xianzai588/Hanjie/simulation/cases/FE-004/README.md

# FE-004

本目录为二维热—结构代理模型交叉检查。

- 方案：baseline / compliant / 6P / S3。
- 节点来源：二维三角形 FE 网格；`bore-nodes.csv` 已送入 `position_tolerance.py`。
- 热源限制：峰值温度未达到钢/铸铁熔化温度，未模拟熔池、熔合和焊缝金属激活。
- 边界：不包含完整三维高度、温度相关塑性、相变、接触和真实材料温度曲线。
- 二维连接：翼端至壳体内壁的 1.2 mm 间隙以等效焊接桥接区表示。
- 结果性质：用于排序/趋势复核，不是实物 CMM 认证。
