xianzai588/Hanjie/DECISIONS.md

# V4.3 决策记录

更新时间：2026-10-02

1. 选题与自动 TIG + ERNiFe-CI 总体路线保留，不用未验证结果宣称已满足 Ø0.05 mm。
2. 非均匀异材公共面导热统一采用两侧串联热阻；旧 0.4R 结果仅作历史对照，当前证据指向 0.4R1。
3. 0.4R1 因空间网格门失败，保持 `solver_result_unvalidated`，不开放 THERMAL-1、正式结构耦合或熔合几何结论。
4. 3.5 mm 焊脚继续作为待验证设计目标；当前送丝 2.0 mm/s、行走 1.5 mm/s 不闭合成形体积，诊断反算值不写入 WPS。
5. 误差预算以 `project/tolerance.yaml` 为唯一权威；当前 Ø0.070 mm 最坏结果必须通过完整热—弹塑性、松夹后 CMM 与实物标定关闭。
6. 预偏置仅按逐件实测初始偏心求解，所有方法使用同一执行器约束；不可行件必须拒绝，不允许静默裁剪或回退。
7. 内腔防护必须经过装配、干涉、吹扫和非倒置退出验证；图纸表达不等于洁净度验证。
8. 定心配合以壳体内径 Ø150.00~150.02 mm、翼端外径 Ø149.94~149.98 mm 的极限尺寸直接定义，形成 0.01~0.04 mm 径向间隙；一般公差不适用于这些受控尺寸。
9. 局部截面 XSEC-M/F/VF 的焊材 P95 差未单调下降，按预登记规则停止 xfine 与新网格时间步复查；下一热实验只处理局部源密度、逐面界面通量、嵌套网格和阶梯拐角单元几何。
10. 接头尺寸继续使用 1.737/2.0/2.5/3.0/3.5 mm 条件曲线；3.5 mm 保持上界候选，不提前冻结四道。
11. 三维 J2 材料核已升级为 Mandel 一致切线与带回溯的全局 Newton，小网格基准通过；只有 Continuous 网格稀疏求解、接触、热映射和完整能量链关闭后才可通过 STRUCT-PREP。
12. Continuous 三材料预备网格不含倒置单元，但仍有 minSICN<0.1 的质量债；当前局部热场不能外推成整圈保守映射，因此不启动正式热—结构耦合。
13. THERMAL-0.6 的 NEST-M/F/VF 已严格整数嵌套；F→VF 焊材 P95 缩减比 0.406，但 P95 10.923 °C、MAE 8.066 °C 和固定点热循环仍超门，故停止 NEST-XF 与 dt/2。
14. 共同控制体源积分、源质心/二阶矩、累计界面热量及阈值翻转已通过，下一热诊断只处理边界源承载层、逐面峰值和仿射精确同材料点重构，不再归因于总能量或非嵌套比较。
15. STRUCT-0-PREP 的法向无摩擦接触、分离/撤夹、局部保守热映射和全局小模型高温无应力激活已通过；0.5 mm 局部细化及 Delaunay 重定位均未消除焊缝差单元，转向环向分段/扫掠拓扑，正式 STRUCT-0 继续冻结。
16. Plan 6 已把热源显式表示为边界面 `Q_face [W]` 并直接散射到相邻控制体 RHS；解析验证通过，且与旧 RHS 在机器精度内等价，证明旧峰值体积源密度翻倍是表示量随承载层厚度变化，不是功率单位误用。
17. 仿射精确同材料 WLS 使五个固定点 RMS 全部通过，但 F→VF NiFe P95/MAE 仍为 10.923/8.066 °C，QT 近界面峰值差 10.232 °C；不运行新 M、XF 或时间步复查，下一热路线改为成熟 FE/FVM 独立参考。
18. Continuous 采用二维共形截面环向扫掠及固定棱柱拆四面体拓扑；0.02 mm 未焊间隙在焊根共享节点闭合，最终整网格低于 minSICN 0.1 的单元为 0，几何体积误差小于 0.1%。
19. 合成温度下的完整截面周期扇区彩排已跑通稀疏全局 Newton、热致接触—分离、应力自由激活、撤夹、基准重建和孔轴拟合；STRUCT-0-PREP 升级为 `ready_pending_admitted_thermal_history`，但正式 STRUCT-0 仍由热 Gate 阻塞。
20. Plan 7 将 Elmer 40.1 s 能量跃迁定位到原生集中质量对变热容的空间混合；零传热出生能量门未通过，35–45 s 严格归因余量也略超限。成对 C 级预出生后焊缝/QT 近场仍差 68.53/108.76°C，不支持出生为主因。禁止调η或直接加密，REF-M须先通过出生与40 s审计，F/VF不运行；最多再做一次针对性诊断，仍冲突则以真实热电偶数据裁决。
21. 用户明确无实物条件，当前路线改为 Route B；第20条“实物裁决”的后续策略由本条替代。热电偶、CMM、金相和实焊均不作为当前计划依赖，不生成伪实验数据；保留物理验证边界和未来协议。
22. Plan 8完成分区焓/反力交换账、独立公共P0观测及成对预出生常物性控制。两边源积分一致，18–26 s焊缝→QT交换账约1046.46/1046.22 J，不支持巨大总量偏分配；常物性共同probe焊缝/QT近场仍差123.71/101.04°C。FE界面反力含共节点载荷/储能分摊，不能与纯梯度热流混称。诊断预算2/2已用尽，不调物理参数、不放宽门限、不运行REF-M/F/VF，剩余空间场差异作为模型形式不确定性保留。
23. 非正式STRUCT-UNCERTAINTY复用已有J2材料点、三候选3D座体和A/B基准孔轴拟合；两套QT局部热历史、3组物性、6组约束分布、2档面积基础刚度和C/M网格共432例。不是三材料整件瞬态热塑性：局部循环铺展、约束和理想壳体支承均为未验证假设。无可分辨稳健赢家，保留三候选；不得把0.00001–0.010 mm量级的敏感性当作最终焊接位置度，更不能据此认证Ø0.05。正式THERMAL-1/STRUCT-0和solver_verified升级规则不变。

19. 新增 THERMAL-REF-PLAN8 dt=0.05 s 时间步复核；Elmer 动态能量残差 0.84152 J，未改善原 dt=0.1 s 缺陷，排除时间离散为主因。热准入继续冻结，后续只处理出生焓/激活质量账的一致性。

24. R3 修复批次（2026-10-02）：评审导航、提交说明、核对清单、报名口径与冻结记录中“说明书 §9.2/§2.4”悬空引用全部改为真实章节（§0/§2.1/§7）；说明书 §0 恢复官方五评价维度→小节映射表；lint 新增章节引用门禁（§ 引用必须存在、章节标题必须渲染进 PDF），导航与说明书结构由机器对账。
25. FE 披露与载荷口径：§4.2 补胀套最大接触反力跨网格 614.2/2008.3 N（约 3.3×）披露，接触反力对网格敏感、只用于装夹容量核对、不进入位置度判定链；原“8p-fine”（3.0 mm，节点数少于主网格）更名“复核网格”（目录 8p-review、报告表头、图注、08 号附件名同步），不再使用粗/细误导命名；疲劳两组设计工况补一阶推导快照（08e load_derivation，移植 origin/main LOAD-ESTIMATE-4：Fi≈1579 N、Fg≈1885 N、M≈129.4 kN·mm），并披露假定谱倾覆矩为一阶推导的 0.19～0.58 倍——Miner 损伤仅为同谱相对排序，不是绝对寿命，载荷上移时损伤按应力范围三次方放大。
26. 封版与治理：新增 scripts/write_release_hashes.py 并生成 deliverables/COMPETITION-R3-SHA256.txt（ZIP＋27 个包内条目，verify_release_hashes.py 通配扩为 COMPETITION-R*，含回归测试）；origin/main 的 15 个分叉提交不做全量 merge——其提交门禁补强已在 R3 lint 等价实现，r1 文献基准文件整篇摘入 docs/sources/；图纸补 GB/T 324 角焊缝符号（z3.5，8×18(41)，段间净距≈41 按 Ø149.96 周长八等分）、GB/T 1182 位置度公差框（Ø0.05|A|B）与四栏标题栏（比例/材料/签审留空＝未完成制造签审）；报告 §7 与 17 号附件补 GB/T 1348-2019、GB/T 9441-2021。
