xianzai588/Hanjie/docs/P1A-0.5-complete.md

# P1A-0.5 完成报告 + Phase 1 启动状态（历史快照）

**日期**：2026-09-03  
**状态**：P1A-0.5 完成 ✅；本文记录 2026-09-03 的冻结快照。当前接口审查结论见 `simulation/structural-v4/P1A-1.1-interface-correction.md`。

---

## P1A-0.5 完成项

### 1. FAIR-A 定义修正 ✅

**修正前（错误）**：
> 固定总连接宽度 108 mm → 相同材料用量

**修正后（正确）**：
> **固定总外缘有效连接宽度 108 mm**
> 
> 回答：在相同总外缘连接尺度下，4/6/8 的拓扑分布差异如何影响结构性能。
> 
> 实际体积 V 和质量 m 将作为结果输出，不假设相等。

### 2. FAIR-C 登记 ✅

**定义**：等体积/等质量拓扑比较

**实施条件**：仅当 FAIR-A/B 排名冲突或质量差异显著时追加

**当前决策**：暂不建立（避免 7 个模型膨胀成 10+）

### 3. 统一参数化几何规则冻结 ✅

**核心文档**：`P1A-0.5-geometry-freeze.md`

**关键决策**：
- Wing width 定义：R74.98 mm 外缘处有效切向/圆弧连接宽度
- 槽根圆角：统一值（待 Phase 1 确定，优先 R2.0 mm）
- Ø40 H7：仅作为制造要求，FE 统一使用名义 Ø40.000 mm
- Continuous：传统连续环形轴承座几何基线（非简单实心圆盘）

### 4. 统一几何生成器完成 ✅

**文件**：`generate_seat_geometry.py`

**功能**：
- 生成 7 个模型的几何清单（manifest）
- 自动验证 FAIR-A/B 断言
- 输出统一格式 JSON 配置

**生成结果**：
```
[PASS] Continuous: All checks passed
[PASS] 4P-FAIR-A: All checks passed
[PASS] 6P-FAIR-A: All checks passed
[PASS] 8P-FAIR-A: All checks passed
[PASS] 4P-FAIR-B: All checks passed
[PASS] 6P-FAIR-B: All checks passed
[PASS] 8P-FAIR-B: All checks passed
```

**FAIR-A 验证**：
| 模型 | Width Each | Total Width | 断言 |
| --- | ---: | ---: | :---: |
| 4P-FAIR-A | 27.0 mm | 108.0 mm | ✅ |
| 6P-FAIR-A | 18.0 mm | 108.0 mm | ✅ |
| 8P-FAIR-A | 13.5 mm | 108.0 mm | ✅ |

**FAIR-B 验证**：
| 模型 | Width Each | Total Width | 断言 |
| --- | ---: | ---: | :---: |
| 4P-FAIR-B | 18.0 mm | 72.0 mm | ✅ |
| 6P-FAIR-B | 18.0 mm | 108.0 mm | ✅ |
| 8P-FAIR-B | 18.0 mm | 144.0 mm | ✅ |

---

## Phase 1 当前状态

### 已完成

- ✅ 7 个模型几何清单生成
- ✅ FAIR-A/B 断言验证通过
- ✅ 统一参数表冻结
- ✅ 生成规则可重复、可审查

### 待完成（Phase 1 核心任务）

**P1A Phase 1 的真正目标不是"画出来"，而是把参数化几何规则写死。**

#### 1. 确定槽根圆角统一值

**任务**：
- 检查 R2.0 mm 是否对所有拓扑（4P/6P/8P）均几何可行
- 若不可行，选择统一最大公共值（如 R1.5 mm）
- 记录最终选择理由

**约束**：
- 不与 Ø82 核心区穿透
- 不与 4 mm 槽几何冲突
- 不产生零厚度/极窄区域

**禁止**：为了降低某个方案应力而单独调整圆角

#### 2. 明确 Wing Width 几何定义

**必须回答**：
> Wing width = R74.98 mm 外缘处的哪个几何量？
> - 弦长？
> - 切向宽度？
> - 圆弧长度？
> - 恒定宽度？

**要求**：所有 FAIR-A/B 采用完全相同定义

#### 3. 建立 3D 实体几何

**使用统一生成规则**：
```
中心刚性区 Ø82
    ↓
按 N 等分中心角
    ↓
每个翼拥有参数化中心角
    ↓
从核心区向外缘延伸
    ↓
两翼之间切除径向槽
    ↓
槽根统一圆角 R_f
    ↓
外缘到 R74.98
```

**禁止**：人工独立绘制 7 份

#### 4. 自动几何检查

**必须通过**：
- Solid 有效（`is_valid = True`）
- Boolean 成功
- 无自交
- 无零/负体积
- 无重叠
- 无零厚度区域
- 坐标系一致

#### 5. 计算实际几何属性

**必须输出**：
- Planform area (mm²)
- Solid volume (mm³)
- Calculated mass (kg)
- Nominal total weld length (mm)

**用途**：后续评价比刚度 K/m

#### 6. 更新 Geometry Manifest

**将 null 字段填充为实际值**：
```json
"geometry": {
  "planform_area_mm2": 12345.67,
  "solid_volume_mm3": 123456.78,
  "calculated_mass_kg": 0.889
}
```

---

## Phase 1 验收标准（10 项）

当前完成度：4/10 (40%)

- [x] 1. 统一参数表冻结
- [x] 2. 统一生成器建立
- [x] 3. FAIR-A 断言通过
- [x] 4. FAIR-B 断言通过
- [ ] 5. 槽根圆角统一确定
- [ ] 6. Wing width 定义明确
- [ ] 7. 7 个三维实体生成
- [ ] 8. 自动几何检查通过
- [ ] 9. 实际几何属性计算
- [ ] 10. Manifest 完整更新

---

## 关键认知（重申）

### 这一步非常重要

> Phase 1 最重要的事情其实不是"画出来"，而是把**参数化几何规则写死**。

### 为什么需要统一生成器

> 评委问："4点和8点是不是人为画得不一样？"
> 
> 回答："除拓扑参数 N 和公平族定义外，几何由同一生成器产生。"
> 
> **这个证据很值钱。**

### Phase 1 的真正审查目标

> 我会先审的不是"模型漂不漂亮"，而是：
> 
> **4/6/8 的几何变化是否只有我们声称的变量在变化。**
> 
> 只要这件事守住，后面的静刚度排名才有资格称为**公平比较**。

---

## 下一步行动

### 立即任务

1. **确定槽根圆角统一值**
   - 几何可行性分析
   - 记录选择理由

2. **明确 Wing Width 定义**
   - 选择：弦长 / 切向宽度 / 圆弧长度
   - 文档化定义

3. **建立 3D 实体生成逻辑**
   - 实现统一生成规则
   - 避免人工修模

### 停止条件

**Phase 1 完成后停止，不要继续 Phase 2**

提交：
- 7 个模型/生成脚本
- geometry-manifest.csv/json（更新后）
- geometry-check-report.md
- 参数化生成规则说明
- 所有异常/妥协记录

**独立几何审查记录已迁移至 `simulation/structural-v4/geometry-audit.md`；本文仅保留历史快照。**

---

## Git 要求（已执行）

从本次开始禁止提交信息自动加入：
- ❌ Co-Authored-By: Claude
- ❌ Co-Authored-By: Codex
- ❌ Generated-by ...

---

**P1A-0.5 状态**：✅ 完成（历史快照）
**Phase 1 当前状态**：✅ P1A-1.1 接口修正和独立几何回读已通过
**下一步**：使用新 BREP 进入 Phase 2 网格与边界定义
