xianzai588/Hanjie/docs/P1A-phase0-complete.md

# P1A Phase 0 完成报告

**日期**：2026-09-03  
**任务**：Gate C-pre / P1A 三维结构静刚度公平筛选 - Phase 0 准备  
**状态**：✅ 完成

---

## 执行摘要

P1A Phase 0 准备工作已完成。设计输入已冻结，目录结构已建立，执行框架已就绪。

**核心目标重申**：
> 无预设结论地筛选进入后续三维焊接热—结构 FE 的结构候选。最终输出：Continuous + 最多两个离散候选。

**关键原则**：
- 如果六点结构被淘汰，接受结果并更新路线
- 这恰恰能证明"参数化协同优化"不是为了给既定方案找证据

---

## Phase 0 完成项（5/5）

| # | 任务 | 状态 | 交付物 |
| --- | --- | :---: | --- |
| 1 | G0 V4 unified 基线确认 | ✅ | commit 3987f11 → ed50e03 |
| 2 | 读取 V4 统一报告 | ✅ | technical-report-v4-unified.md |
| 3 | 读取几何参数 | ✅ | cad/parametric/geometry.json |
| 4 | P1A 设计输入冻结 | ✅ | P1A-design-inputs.md |
| 5 | 创建目录结构 | ✅ | simulation/structural-v4/ |

---

## 关键设计决策

### 1. 两套公平设计族（避免比较不公平）

**为什么需要两套**：
- 如果只做"4/6/8 全都每翼 18 mm"，八点实际上拥有更多材料
- 即使刚度最好也不能说是"点数优化"导致的

**FAIR-A：固定总连接宽度 108 mm**
- 回答："拓扑本身哪个好？"
- 4P: 27 mm/段，6P: 18 mm/段，8P: 13.5 mm/段

**FAIR-B：固定每段 18 mm**
- 回答："实际工程方案哪个好？"
- 4P: 72 mm 总长，6P: 108 mm，8P: 144 mm

### 2. 径向方向扫描（避免各向异性误判）

**扫描 7 个方向**：θ = 0°, 15°, 30°, 45°, 60°, 75°, 90°

**输出指标**：
- $C_{r,\max} = \max_\theta \frac{\delta_r(\theta)}{F}$（最差方向柔度）
- $A_r = \frac{C_{r,\max}}{C_{r,\min}}$（各向异性指标）

**原因**：4、6、8 点结构具有方向各向异性，只算 X/Y 很可能刚好踩在某个翼上

### 3. 双边界敏感性（避免边界假设掩盖问题）

**BC-1**：实际安装区域约束（主结果）  
**BC-2**：较刚边界（敏感性上界）

**若边界改变导致方案排序变化**：如实报告"结构优劣对安装刚度敏感"

### 4. 三级网格收敛验证（避免数值不可信）

**收敛判据**：
- 位移/柔度：Medium→Fine < 3%
- 热点应力：Medium→Fine < 10%

**若未收敛**：不得发布结构排名

### 5. 槽根圆角建模（避免数学奇异）

**禁止**：用数学尖角最大节点应力做疲劳判断  
**必须**：使用实际圆角几何，报告区域/路径应力

---

## 目录结构

```
simulation/structural-v4/
├── P1A-design-inputs.md           # ✅ 设计输入冻结
├── P1A-status.md                  # ✅ 执行状态追踪
├── README.md                      # ✅ 导航文档
├── configs/                       # ⏳ 模型配置（7 个 JSON）
├── models/                        # ⏳ 几何模型（7 个目录）
│   ├── continuous/
│   ├── 4p-fair-a/
│   ├── 4p-fair-b/
│   ├── 6p-fair-a/
│   ├── 6p-fair-b/
│   ├── 8p-fair-a/
│   └── 8p-fair-b/
├── meshes/                        # ⏳ 网格（coarse/medium/fine）
├── raw/                           # ⏳ 原始求解器输出
├── processed/                     # ⏳ 处理后结果
│   ├── results.csv
│   ├── convergence.csv
│   └── screening-summary.json
├── figures/                       # ⏳ 图表
│   ├── polar-radial-compliance.svg
│   └── pareto-stiffness-stress-mass.svg
└── stiffness-screening-v4.md      # ⏳ 筛选技术报告
```

---

## Gate C-pre 通过条件（10 项）

| # | 条件 | 状态 |
| --- | --- | :---: |
| 1 | 四种结构统一条件 3D 静力比较 | ⏳ |
| 2 | FAIR-A/B 明确分离 | ⏳ |
| 3 | 径向方向扫描完成 | ⏳ |
| 4 | 网格收敛通过 | ⏳ |
| 5 | 边界敏感性完成 | ⏳ |
| 6 | 输出机器可读结果 | ⏳ |
| 7 | 输出技术报告 | ⏳ |
| 8 | 生成极坐标图 | ⏳ |
| 9 | 生成 Pareto 图 | ⏳ |
| 10 | 无预设地选出候选 | ⏳ |

---

## 禁止项（重申）

本轮**严格禁止**：
- ❌ 预设"六点最优"结论
- ❌ 为了理想结果修改判据
- ❌ 做温度门控（那是 Gate D）
- ❌ 做预偏置补偿（那是 Gate E）
- ❌ 做三维焊接热—结构 FE（那是 Gate B/C）
- ❌ 只给漂亮云图不提供收敛表

---

## 最终输出（Phase 6 交付）

### 1. 结构筛选主表

| 方案 | 公平口径 | $C_{r,\max}$ | $A_r$ | $C_z$ | $C_\theta$ | $\sigma_{\text{slot}}/F$ | 质量 | Gate |
| --- | --- | ---: | ---: | ---: | ---: | ---: | ---: | --- |
| Continuous | baseline | … | … | … | … | … | … | ? |
| 4P | A/B | … | … | … | … | … | … | ? |
| 6P | A/B | … | … | … | … | … | … | ? |
| 8P | A/B | … | … | … | … | … | … | ? |

### 2. 网格收敛表

证明数值可信。

### 3. 径向柔度极坐标图

一张图看出 4/6/8 各向异性。

### 4. 刚度/应力/质量 Pareto 图

工程决策依据："为什么最后选 X 点"。

---

## 执行路线（Phase 1-7）

| Phase | 任务 | 预计时间 | 状态 |
| --- | --- | --- | :---: |
| Phase 1 | 几何建模（7 个模型） | 3-4 天 | ⏳ |
| Phase 2 | 网格划分（21 个网格） | 2-3 天 | ⏳ |
| Phase 3 | 边界与载荷 | 1-2 天 | ⏳ |
| Phase 4 | 求解（~378 个工况） | 2-3 天 | ⏳ |
| Phase 5 | 后处理 | 2-3 天 | ⏳ |
| Phase 6 | 分析与筛选 | 2-3 天 | ⏳ |
| Phase 7 | 独立审查 | 等待 | ⏳ |

**预计 Gate C-pre 通过**：2026-09-13

---

## Phase 7 独立审查：四个关键问题

完成 Phase 6 后，P1A 将停止并提交所有结果，等待独立审查攻击以下四个问题：

| # | 问题 | 攻击角度 |
| --- | --- | --- |
| 1 | **公平性** | FAIR-A/B 是否真的公平？有没有偷偷让某方案占便宜？ |
| 2 | **边界条件** | 边界是否合理？是否为了理想结果选择性使用边界？ |
| 3 | **网格收敛** | 收敛表是真的还是假的？变化率是否被人为压低？ |
| 4 | **结构排名** | 排名是数值结果还是人为设计出来的？ |

**只有这四项经得住攻击，才值得把筛出来的结构送入昂贵的 3D 焊接热—结构模拟。**

---

## 提交记录

```
commit ed50e03
[P1A-PREP] Phase 0 完成：三维结构静刚度公平筛选准备就绪
```

---

## 下一步

**Phase 1 几何建模**（预计 3-4 天）：
- 建立 7 个三维模型
- 统一几何参数（R74.98, Ø40 H7, t5, H200, Ø160）
- 槽根圆角建模
- 几何质量检查

**当前状态**：Phase 0 完成，进度 5/37 (14%)，准备进入 Phase 1。

---

**关键认知重申**：
> 现在不要再给项目"+1 分"。**下一次真正值得重评分的节点，就是 P1 出现第一批可信三维结构证据的时候。**

---

**P1A Phase 0 状态**：✅ 完成，设计输入冻结，目录结构就绪，等待 Phase 1 开始。
