xianzai588/Hanjie/docs/G0-v4-baseline-convergence.md

# G0 V4 基线收敛完成报告

**日期**：2026-09-03  
**任务**：从"V2+V3+V4混合状态"收敛到统一 V4 基线

---

## 执行背景

### 核心问题诊断

**当前分数分离**：
| 对象 | 当前水平 | 说明 |
| --- | ---: | --- |
| 项目思路、V4 战略、创新规划 | **84-85** | README、规划文档已 V4 |
| **当前真正提交出去的 PDF/图纸一致性** | **79-82** | 技术报告仍 V2，参数不一致 |

**最大风险**：不是技术路线不够高级，而是"**仓库里已经改了，论文还是旧的**"。

### V2/V3/V4 参数不一致清单

| 参数 | V2 旧值 | V4 正确值 | 影响 |
| --- | --- | --- | --- |
| 翼端半径 | R73.8 mm | **R74.98 mm** | 装配间隙、接头几何 |
| 装配间隙 | 1.2 mm | **0.01~0.04 mm** | 配合性质 |
| 配合表述 | "H7/h6 过渡配合" | **"H7/h6 定位间隙配合"** | 技术准确性 |
| 定位夹具 | Ø39.96 mm 定位销 | **锥形心轴 1:50** | 重复性、自动找正 |
| 误差预算 | "硬伤已修复" | **"未闭合，0.035 > 0.025 mm"** | 诚实度 |
| 轨迹补偿概念 | "轨迹反变形补偿" | **"焊前装配预偏置补偿"** | 机械逻辑正确性 |
| 标准引用 | GB/T 5185（焊缝符号） | **GB/T 324（焊缝符号）+ GB/T 5185（方法代号）** | 标准使用正确性 |

---

## G0 执行的 6 项任务

### ✅ 任务 1：建立真正的 V4 报告主稿

**文件**：`deliverables/report/technical-report-v4-unified.md`

**核心改进**：

1. **标题修正**：
   - ❌ V2："QT450-10/Q235B 主轴承座异种材料焊接数字工程技术说明书"
   - ✅ V4："面向 Ø0.05 mm 位置度的 QT450-10/Q235B 主轴承座异种焊接热—结构协同优化与数字质量控制"

2. **摘要诚实化**：
   ```markdown
   ### 当前验证状态
   | 项目 | 状态 | 证据等级 |
   | --- | --- | --- |
   | FE3D-BASE Baseline | 实施中 | Gate B 待验证 |
   | 误差预算闭合 | **未闭合** | 0.035 > 0.025 mm |
   ```

3. **误差预算缺口明确化**：
   > V4 明确边界：当前误差预算最坏情况为 **0.035 mm 径向（Ø0.070 mm 位置度）**，尚未满足 Ø0.05 mm 目标。后续热—结构优化与焊前预偏置补偿的直接目标，就是关闭这 **0.010 mm 径向预算缺口**。

4. **全文参数统一**：
   - R74.98 mm 小间隙精密定心
   - 锥形心轴 1:50
   - H7/h6 定位间隙配合（非过渡配合）

5. **未验证创新明确标记**：
   | 创新 | 状态标记 |
   | --- | --- |
   | 柔顺结构 | unresolved, hypothesis |
   | 温度门控 | untested, proposed |
   | 预偏置补偿 | untested, proposed |

6. **8 章结构**（替代原 17 节）：
   1. 命题解析与总体方案
   2. 异种材料焊接性与工艺选型
   3. 接头—夹具—尺寸链协同设计
   4. 三维热—结构协同模型
   5. 承载刚度与疲劳评估
   6. 温度门控与装配预偏置控制
   7. 自动化、检测与质量追溯
   8. 证据分级与后续路线图

---

### ✅ 任务 2：修正三个关键概念问题

#### 2.1 H7/h6 配合性质修正

**V2 错误**：
> "H7/h6 过渡配合"

**V4 正确**：
> "H7/h6 为定位间隙配合（locational clearance fit），非过渡配合。采用小间隙精密定心设计，名义径向间隙约 0.02 mm。实际装配前需测量壳体内径及圆度，通过翼端精加工/选配保证间隙落在设计范围。"

**依据**：
- H7/h6 属于定位间隙配合
- H7/k6、H7/m6 才是过渡配合

#### 2.2 预偏置补偿概念修正

**V2 错误概念**：
> "轨迹反变形补偿"——机器人把焊枪轨迹偏 0.01 mm

**机械逻辑问题**：
- 轴承座已被夹具固定，机器人偏轨迹不会直接移动轴承孔
- 真正应该做的是根据实际接头位置进行焊缝跟踪

**V4 正确概念**：
> "焊前装配预偏置—焊后变形联合补偿"

**控制链修正**：
```
视觉/CMM 测得初始偏心
        ↓
热—结构模型预测焊后收缩
        ↓
求解最佳预偏置 δ_pre
        ↓
微调心轴/定位平台        ← 作用在装配位置，不是焊枪轨迹
        ↓
重新测量确认
        ↓
机器人沿真实接头轨迹焊接
        ↓
焊后测量
```

#### 2.3 GB/T 标准引用修正

**V2 错误**：
> `FILLET WELD ... per GB/T 5185`

**问题**：
- GB/T 5185-2005 是《焊接及相关工艺方法代号》，主要用于焊接方法名称和代号
- 不是角焊缝几何或焊缝符号设计标准

**V4 正确**：
- **焊接方法代号**：GB/T 5185-2005
- **焊缝符号表示**：GB/T 324-2008《焊缝符号表示法》
- **接头/坡口**：GB/T 985.1-2008（有需要时引用）

**已修改文件**：
- `cad/parametric/generate_engineering_drawings.py`（新增 `weld_note()` 函数）

---

### ✅ 任务 3：误差预算缺口作为核心优化目标

**不再藏匿问题**，而是明确作为 V4 的核心优化约束。

**当前状态**：
```
0.005 + 0.003 + 0.008 + 0.005 + 0.012 + 0.002
= 0.035 mm 径向

目标：0.025 mm 径向
差值：0.010 mm
```

**V4 论文中的正确表达**：
> **初始最坏情况尺寸链尚不能满足 Ø0.05 mm 位置度，因此后续热—结构优化与焊前预偏置补偿的直接目标，就是关闭这 0.010 mm 径向预算缺口。**

**双口径报告计划**：
1. **最坏情况上界**（线性叠加）
2. **独立随机项 RSS/P95 统计预算**

**前提**：先区分各误差项性质：
- 可标定系统偏差
- 可补偿偏差
- 随机重复性
- 焊接随机变形
- 测量不确定度

---

### ✅ 任务 4：V2 历史归档，V4 作为新主线

**文件结构**：
```
deliverables/report/
├─ technical-report-v2.md              # ✅ 冻结历史，不再修改
├─ technical-report-v4.md              # ⏸️  V4 骨架（FE3D 占位）
├─ technical-report-v4-unified.md      # ✅ V4.1 统一版（本次交付）
└─ build_technical_report_v4.py        # 🔄 待建立
```

**V2 保留理由**：
- 降阶模型 + 二维 FE 的完整记录
- 15 组降阶筛选 + 5 组 FE 代理的对照数据
- 网格收敛未通过（29.224%）的诚实记录

**V4 主线定位**：
- 三维热—弹塑性 FE 为核心
- Gate B 验证门严格执行
- 所有未验证创新明确标记

---

### ✅ 任务 5：建立证据清单追溯

**文件**：`evidence/claims.yaml`（已存在，V4 论文已引用）

**核心主张状态**：

| 主张 ID | 主张内容 | 状态 | 置信度 | 发布状态 |
| --- | --- | --- | --- | --- |
| CLAIM-柔顺 | 六点柔顺降低位置度 | unresolved | low | hypothesis |
| CLAIM-温控 | 温度门控优于固定 S3 | untested | hypothesis | proposed |
| CLAIM-补偿 | 反变形补偿有效 | untested | hypothesis | proposed |
| CLAIM-预算 | 误差预算闭合 | not_closed | needs_optimization | optimization_target |
| CLAIM-FE3D | FE3D-BASE 可信 | in_progress | to_be_determined | in_verification |

**V4 论文发布规则**：
- `hypothesis` / `proposed` → 必须用"提出"、"设计"、"构建"
- `unresolved` / `untested` → 不能写"验证"、"证明"、"表明"
- `in_progress` → 写"实施中"、"Gate B 待验证"
- `not_closed` → 明确写"未闭合，成为优化目标"

---

### ✅ 任务 6：下一步执行清单明确

**不再做的事**（禁止项）：
- ❌ 继续写温度门控代码（在 Gate B 通过前）
- ❌ 继续加功能
- ❌ 追求更多创新点
- ❌ 修改验证协议判据（结果出来后）
- ❌ 继续总结文档和功能扩展

**立即要做的事**（优先级顺序）：

| 优先级 | 任务 | Gate | 交付物 |
| :---: | --- | --- | --- |
| **P0** | ✅ V4 基线收敛 | Gate A | 参数一致性 |
| **P1** | 🔄 连续/4/6/8 结构静刚度筛选 | Gate C-pre | 公平对比基线 |
| **P2** | 🔄 FE3D-BASE 三维热—结构 FE | Gate B | 数值可信度 |
| **P3** | ⏳ 3D FE 结构公平对比（筛选后少数方案） | Gate C | 结构选型 |
| **P4** | ⏳ 温度门控对照实验 | Gate D | 有效改善证据 |
| **P5** | ⏳ 预偏置补偿闭环验证 | Gate E | 误差预算闭合 |

---

## G0 交付物清单

| # | 交付物 | 路径 | 状态 |
| --- | --- | --- | :---: |
| 1 | V4 统一技术报告 | `deliverables/report/technical-report-v4-unified.md` | ✅ |
| 2 | 工程图生成器（标准引用修正） | `cad/parametric/generate_engineering_drawings.py` | ✅ |
| 3 | G0 基线收敛报告 | `docs/G0-v4-baseline-convergence.md` | ✅ |
| 4 | V2 历史归档 | `deliverables/report/technical-report-v2.md` | 🔒 冻结 |
| 5 | V3 误差预算 | `docs/validation/position-error-budget-v3.md` | ✅ 已有 |
| 6 | V4 关键修正说明 | `docs/v4-key-corrections.md` | ✅ 已有 |
| 7 | V4 冻结总结 | `docs/v4-freeze-summary.md` | ✅ 已有 |

---

## 关键认知转变

### Before (V2/V3 混合状态)

- "项目 85 分" = 认为提交物已经 85 分
- R73.8 mm / Ø39.96 mm 销 / 1.2 mm 间隙 = 旧参数仍在论文
- "误差预算硬伤已修复" = 回避 0.035 > 0.025 的事实
- "轨迹反变形补偿" = 机械逻辑错误
- "GB/T 5185 焊缝符号" = 标准使用错误
- 未验证创新写成"已验证成果"

### After (V4 统一基线)

- "项目规划 85 分，提交物 79-82 分" = 清晰区分
- **R74.98 mm / 锥形心轴 1:50 / 0.01~0.04 mm 间隙** = 全文统一
- "误差预算未闭合，0.010 mm 缺口成为核心优化目标" = 诚实面对
- "焊前装配预偏置补偿" = 机械逻辑正确
- "GB/T 324 焊缝符号 + GB/T 5185 方法代号" = 标准使用正确
- 所有未验证创新标为 `proposed / hypothesis / to-be-verified`

---

## 下一阶段 Gate 清单

| Gate | 必须满足 | 预计完成 |
| --- | --- | --- |
| ✅ Gate A | V2/V3/V4 参数一致性 | 2026-09-03 |
| 🔄 Gate B | FE3D-BASE 网格收敛（< 5%）+ 热场合理性 | 2026-09-07 |
| ⏳ Gate C | 4/6/8 结构公平对比 | 2026-09-11 |
| ⏳ Gate D | 自适应跳焊有效改善 | 2026-09-15 |
| ⏳ Gate E | 误差预算闭合验证 | 2026-09-18 |

---

## 最重要的一句话

> **下一阶段不是增加内容，而是让每一个创新点都出现"设计问题 → 数学/物理方法 → 对照基线 → 数值结果 → 反例/边界 → 工程决策"这一完整证据链。**

做到这一点，这个作品才真正进入高奖竞争状态。

---

**G0 状态**：V4 基线收敛完成，参数一致性达标，准备进入 Gate B 验证阶段。
