xianzai588/Hanjie/docs/00-project-definition.md

# 00 项目定义（WP0）

> 状态：v1.0 · 2026-09-02 执行版
> 比赛原始文件见 [competition/original-files/](../competition/)，本文与其逐条对照维护。

## 1. 比赛对象（固定题）

### 壳体

| 项目 | 参数 |
| --- | --- |
| 材料 | Q235B |
| 壁厚 | 5 mm |
| 外径 × 高 | Ø160 × 200 mm |

### 主轴承座

| 项目 | 参数 |
| --- | --- |
| 材料 | QT450-10 球墨铸铁 |
| 形状 | 环形盘状 |
| 轴承孔 | Ø40 mm |

## 2. 硬性要求

- 焊后轴承孔轴线位置度偏差 ≤ **Ø0.05 mm**
- 不得产生可能进入压缩机内部的焊渣、飞溅物
- 方案须覆盖五个维度：
  1. 工艺选择与优化
  2. 材料选配与连接
  3. 焊接结构设计
  4. 质量检测与评价
  5. 自动化焊接方案

## 3. 项目主线

**基于六点柔顺连接结构的 QT450-10/Q235B 主轴承座低变形自动 TIG 异种焊接及数字化质量控制方案**。

主候选：自动 TIG + 镍铁基填充材料；对比路线：CMT/低飞溅 GMAW、激光填丝。主候选仍需在设备与小试可用时完成工艺评定。

三个核心问题：

1. **焊得住** —— 异种材料焊接性：白口、脆硬组织、裂纹、焊材、热输入、预热/后热、接头可靠性
2. **焊不歪** —— P ≤ Ø0.05 mm：焊缝数量/位置/顺序、热输入、夹具、定位、热管理、反变形
3. **稳定焊** —— 视觉定位、路径生成、自动焊接、参数采集、异常检测、批量质量追溯

## 4. 工作包划分

| WP | 模块 | 最终回答 | 负责人 |
| --- | --- | --- | --- |
| WP0 | 项目定义与资料管理 | 我们到底要解决什么 | 待定 |
| WP1 | 材料与焊接性 | 为什么难焊 | 待定 |
| WP2 | 焊接工艺选型 | 到底用什么方法焊 | 待定 |
| WP3 | 接头结构与夹具 | 接头怎么设计 | 待定 |
| WP4 | 热-结构仿真 | 为什么这样设计 | 待定 |
| WP5 | 物理验证（可选） | 实际能不能焊好 | 待定 |
| WP6 | 自动化与智能监测 | 怎么稳定重复 | 待定 |
| WP7 | 检测评价与数值后处理 | 怎么证明真的好 | 待定 |
| WP8 | 作品集成与答辩 | 怎么形成完整参赛作品 | 待定 |

## 5. 证据边界

- 官方仅给出题面材料、壳体尺寸、轴承孔直径、位置度限值和洁净度要求；未给出的轴承座厚度、外廓细节、焊缝尺寸、装配间隙和基准细节统一见 [05-design-assumptions.md](05-design-assumptions.md)。
- 数值模型输出的 `P_sim` 是按内孔分层拟合轴线构造的比较指标，不是 CMM 认证结果。
- 没有设备时，实验、金相、硬度、NDT、CMM 和真实过程采集均标记为“可选/待实施”，不能用生成数据替代实测。

## 6. 待确认事项

- [ ] 固定题原文逐条核对（与 competition/original-files 对照，标注页码）
- [ ] 校内报名与作品节点最终确认（官方报名 10-20 前，作品提交 10-25 前）
- [ ] 位置度 Ø0.05 mm 的真实测量手段确认（CMM 可用性与精度）
- [ ] 洁净度判据的量化定义（内腔异物检查规程）
- [ ] QT450-10 与 Q235B 供应商质保书归档
- [ ] 自动 TIG 设备、ERNiFe-CI 丝/棒和保护气的可获得性确认
