xianzai588/Hanjie/deliverables/submission/10-复现与版本冻结记录.md

# COMPETITION-R3 复现与版本冻结记录

## 发布状态

- 版本：COMPETITION-R3；题型：固定题·焊接赛道。
- 冻结方案：8P-FAIR_B，八段两道脉冲 TIG；根道与盖面各一遍，总焊长144 mm，名义净线能量300 J/mm，净热86.40 kJ，弧燃174.5 s。
- 材料路线：QT450-10座体/Q235B壳体；Ni99预制隔离层，NiFe-55最终填充；不预热、层间≤100 ℃、400～500 ℃半热态轻击。
- 交付范围：纯数字设计作品。整件热-结构结果用于设计验证；实物资格试验仍按说明书 §7 设计放行顺序执行。
- 说明书与图集页数以构建后的 `manifest.json` 实际计数为准。

## 复现入口

在项目根目录执行：

```powershell
python deliverables/build_submission.py
```

入口会重建设计计算、Schaeffler映射、工程核算、WPS、图纸、说明书、manifest 和压缩包，并运行 `scripts/competition_submission_lint.py`。

## 权威输入

- `project/competition-design.yaml`：几何、8P焊序、控形、洁净与验证边界。
- `project/process-r3.yaml`：当前脉冲TIG名义参数。
- `studies/COMPETITION-DESIGN/results/assessment.json`：候选比较与守恒计算。
- `simulation/competition-r3/results/8p-coarse/`：整件主网格热-结构结果及历史。
- `studies/SCHAEFFLER-MAP/results/schaeffler-mapping.json`：相图当量及适用域声明。
- `deliverables/report/technical-report-v4-unified.md`：提交说明书源稿。

## 证据边界

位置度 0.001742 mm 为独立 A/B 基准拟合后的数值结果；主/复核独立网格绝对差 0.000784 mm，响应相对差45%，因此报告保留相对差并以设计限值的绝对裕量作为工程门。该结果是数值设计验证，不是实物放行；NiFe/QT界面、疲劳、洁净度和测量系统能力须通过首件试制确认。
