xianzai588/Hanjie/deliverables/submission/17-参数来源与证据等级.md

# COMPETITION-R3 参数来源与证据等级

| 参数/结论 | 当前值 | 来源等级 | 对核心结论影响 | 口径 |
| --- | ---: | :---: | :---: | :--- |
| 脉冲峰值/基值电流 | 100/50 A | B | 中 | 工艺设计窗口；试制阶段由WPS/PQR固化 |
| 电弧电压 | 12 V | B | 中 | 工艺设计窗口 |
| 焊速 | 1.65 mm/s（±2%） | B | 高 | 两道脉冲TIG冻结口径 |
| 送丝/焊丝直径 | 3.50±0.05 mm/s；Ø1.60±0.01 mm | B/C | 高 | 守恒边界输入 |
| 起焊温度/层间温度 | 20 ℃起焊（不预热）/≤100 ℃ | B/C | 高 | 位置度与铸铁冷焊窗口 |
| 锤击窗口 | 400～500 ℃；0.2～0.4 MPa | B | 高 | 仅焊道中心，避开QT/HAZ/焊趾 |
| 电弧效率/沉积效率 | 0.55；0.90～0.98 | C | 高 | 能量与熔敷守恒假设；首件截面复核 |
| 整件数值位置度 | 0.001742 mm（直径） | A | 高 | 独立A/B基准拟合；非实测放行值 |
| 网格绝对差 | 0.000784 mm | A | 高 | 与Ø0.05 mm设计限值比较的工程门 |
| 参考许用应力 | 60 MPa | C | 高 | 条件承载筛查值，不是NiFe/QT实测许用 |
| NiFe-55成分与熔敷性能 | 以供方质保书、AWS A5.15分类和PQR为准 | B | 高 | 报告仅作设计输入，不替代批次复核 |
| 母材标称成分 | Q235B按GB/T 700；QT450-10按GB/T 1348-2019 | B | 高 | 以实际批次质保书为准 |
| 金相组织检验 | GB/T 9441-2021 | B | 中 | 宏观截面/金相与硬度评定的标准框架；首件试制执行 |

等级定义：A=当前项目内可复核的独立计算或原始记录；B=公开标准/资料或工程工艺窗口；C=工程假设或设计分配。设计结果与实物工程放行严格分开。
