xianzai588/Hanjie/deliverables/process/joint-process-card.md

# 主轴承座—壳体连接 pWPS 工艺规程卡

赛道：中铁山桥杯焊接固定题。规程号HJ-W-01，修订3。适用Q235B壳体5 mm、QT450-10座体12 mm、Ø40孔、8×18 mm间断角焊缝。设计规程在A类工艺试验合格后转为生产WPS，内容按ISO 15609-1组织。

| 项目 | 规定 |
| --- | --- |
| 接头与位置 | 内周上表面角焊缝，八段等分45°；壳体轴线竖直，工件回转，焊枪保持平/横角焊位置；焊脚≥3.50，最大几何包络4.30 |
| QT预制过渡层 | 在八处18×6 mm连接面开深1.50±0.10、端部R1.5的浅槽，Ni99 TIG填满后加工至名义接头表面；最终组焊前纯镍层≥1.20 mm；组焊熔深≤0.40，剩余纯镍≥0.80；截面验证后冻结 |
| 前工序 | 镍层制作与最终Ø40孔加工分开：铸件→镍层→24 h表面裂纹检查→连接面及孔精加工→清洗干燥→组焊。隔离层不是假定“母材不再受热” |
| 表面准备 | 铸皮、油污、氧化层去除；镍层、钢侧连接面露出洁净金属；脱脂剂完全挥发，不在封闭内腔内打磨；焊前入腔物料清点 |
| 组装 | 孔40.010～40.018；座体底面z100；外缘149.94～149.98、壳体内径150.00～150.02；径向间隙0.01～0.04；胀套对独立壳体基准定心 |
| 方法/极性 | 自动脉冲GTAW（TIG），DCEN；不使用焊剂，禁止以低飞溅替代颗粒防护 |
| 焊材 | NiFe55 TIG实心棒Ø1.60±0.01；供方典型Ni55、C0.01、Si0.13、Mn0.70 wt%；按实际产品供货分类及证书订货，禁止把药皮焊条分类直接当作TIG牌号 |
| 电极/气体 | W-La20 Ø2.0，尖端角60°，平顶0.3；喷嘴Ø10，弧长2.5±0.5；99.999% Ar 10 L/min，许可8～12 |
| 脉冲 | 峰值100 A / 基值50 A；占空50%；20 Hz；平均75 A；名义12 V；须采样瞬时U(t)I(t)积分，禁止仅乘两个平均值作为在线能量 |
| 焊速/填充 | 焊速1.65 mm/s±2%；固定送丝3.50±0.05 mm/s，分辨率≤0.01；沉积效率设计0.90～0.98，由宏观截面及增重确认 |
| 成形 | 两道：根道目标焊脚2.8，盖面至名义4.0；总填充面积7.326～8.760 mm²、等效焊脚3.828～4.186；根道与盖面都需熔合，不以体积守恒替代熔合检查 |
| 线能量 | 名义毛弧能545.45 J/mm；η电弧0.55，名义净300 J/mm；净窗口250～350，η是热模型输入，不能直接由电源读数实测；全件名义净86.40 kJ |
| 焊序 | 根道1→5→3→7→2→6→4→8，盖面同序；各18 mm，段内不摆动；起停1 mm过渡，弧坑填充，不计入有效18 mm而削短焊段 |
| 温控 | 组焊不预热；起焊15～35℃；每段焊前测QT侧距焊趾10 mm及本段前道邻近测点，全部≤100℃；缺信号或超温禁起弧，等待至≤90℃再恢复 |
| 热态轻击 | 仅当表面实测400～500℃时，在熔敷焊道中部轻击；气动Ø8圆头、0.2～0.4 MPa、2000～3000次/min、搭接≥75%；不敲QT母材/熔合线/焊趾，各留0.5；压痕≤0.05，无撕裂或剥离；超窗跳过并记录，不为锤击二次加热 |
| 清理与防护 | 层间用专用刷与顶部局部抽吸清理，禁止腔内磨削；刚性盘＋分体铜环＋静态密封截留颗粒；气幕10～15、顶部抽吸22～28 L/min；水路独立检漏 |
| 装夹与卸夹 | 径向预载≤100 N；机械止挡承受热反力，额定5000 N；独立压环500 N。最后停弧≥120 s且热区<55℃，压环卸载→胀套正向回退1 mm→铜环/密封回缩0.5→朝上竖直下撤 |
| 精度检查 | 20±1℃，A为壳体下端面、B为壳体内壁两个独立测量带轴线；Ø40孔3截面各12点拟合孔轴，测得位置度直径＋同口径扩展不确定度≤0.05 |
| 尺寸精整 | 先检焊后位置度；孔径合格不精整；仅对孔径<40.020者定尺寸微珩，直径增量≤min(0.005,40.025−实测直径)，禁止用精整纠偏 |
| 异常处理 | 断丝、能量越窗、温度/气流/夹紧缺信号、漏水立即停弧；保留工装和防护，故障件隔离；返修须有独立评定，禁止自动补焊掩盖裂纹 |

名义弧燃174.5 s，耗丝610.9 mm；加夹持起停损耗按15%备料。生产节拍按焊接、锤击清理转位、冷却占用及检测资源逐项计算。
