xianzai588/Hanjie/docs/review/competition-r2-full-critique-2026-10-02.md

# COMPETITION-R2 全量锐评（2026-10-02）

## 审查范围

审查对象为当前提交包：说明书 PDF、设计图集 PDF、STEP、04～22 号证据附件、工艺卡、项目规则原件和仓库内当前正文。官方规则以 `competition/original-files/welding/第一届辽宁省大学生材料焊接与铸造工艺设计大赛实施方案.pdf` 为准。未把仓库旧版 R1/R2 研究状态当成提交结论。

## 结论先行

当前作品“能交”，但还不宜按“一等奖级完成闭环”自称。形式合规度高、工程图和工装设计是强项；技术上最危险的不是排版，而是三条证据链没有真正闭合：

1. **工艺版本冲突是硬伤。** 说明书和 06/07 号工艺卡写“不预热、层间≤100 ℃、起焊≥15 ℃”；图集第 2 页仍写“预热名义150 ℃、起弧前≥130 ℃、层间<200 ℃”。这会让评委无法判断到底评哪套 WPS。
2. **洁净防护仍残留红线方案。** 图集第 4 页仍画“连续薄裙 t0.15 mm”。它处在电弧/飞溅近区，且存在贴壁刮擦生屑风险；这与项目 AGENTS.md 明确禁止的物理方案冲突，也与正文已改用的 3 mm C11000 紫铜衬环不一致。
3. **“设计预算闭合”不等于“焊后达标”。** Ø0.05 mm 预算依赖热残余 0.008 mm、卸夹位移 0.002 mm、胀套重复性 0.003 mm 等分配值；这些不是当前实测或收敛的热—弹塑性结果。说明书应把“条件性设计判定”与“工程确认状态”分开。

因此，现状适合定位为：**完整的数字工艺设计方案，具备明确的试制验证入口；尚未完成 WPS/PQR、焊接性、位置度和洁净度的 A 类实物确认。**

## 一、基础合规检查

### 已经做得好的

- 官方固定题目五个维度均有对应章节：工艺选型、材料/界面、结构/变形、检测评价、自动化方案。
- 题面关键尺寸有覆盖：Q235B Ø160×200×5、QT450-10、Ø40 孔、焊后位置度 Ø0.05 mm、内腔洁净。
- 提交包包含说明书、图集、STEP、参数、计算、相图、边界图和工艺卡，证据可追溯性明显高于普通课程设计。
- 说明书 PDF 29 页、图集 6 页；PDF 元数据未出现学校、学生或指导教师姓名。图集视觉上有统一图号、基准 A/B、位置度框和尺寸说明。
- 官方允许固定题目提交研究报告、设计图或研究实物，未规定必须有实物；因此“纯数字设计”本身不违规。
- 说明书已经补回疲劳章节、界面预处理、应力释放槽、反变形/隔热、CMM 和洁净度检查，这些方向与题面逐项对齐。

### 必须马上修的形式/交付问题

| 严重度 | 位置 | 问题 | 为什么会被抓 |
|---|---|---|---|
| P0 | `project/report.yaml` 的 PDF 页脚 | “试制阶段完成A类实物工程确认” | 当前仓库证据明确写“实物性能未验证”。这会被理解为伪造/误报验证状态。应改成“设计计算与局部热诊断支撑｜试制阶段完成A类实物工程确认”或更准确的“设计阶段，实物工程确认待试制”。 |
| P0 | 图集第2页、`joint-detail.svg` | 150 ℃预热、起弧≥130 ℃、层间<200 ℃ | 与说明书、06号卡、07号参数“不预热、≤100 ℃”冲突；不能提交两套热制度。 |
| P0 | 图集第4页、`protected-process-assembly.svg` | 0.15 mm 连续薄裙 | 违反项目红线：电弧近区薄箔/薄裙存在烧穿和磨屑风险。必须删掉或明确它是历史禁用方案，并把图集统一改为 3 mm 紫铜衬环+隔离片+气幕。 |
| P1 | 图集页脚 | “状态 design-review（未完成制造签审）” | 可以作为数字设计状态，但应放在内部审查版；正式提交版应统一写“设计冻结/未作制造签审”，避免“图纸已可直接制造”和“未签审”两种信号同时出现。 |
| P1 | 提交包版本号 | 说明书/图集 R1，06/07/04 号为 R2 | 版本混用容易造成评委引用旧参数。建议整个包统一 COMPETITION-R2，或把 R1/R2 差异表放在导航第一页。 |
| P1 | 提交命名 | 官方要求“自编代码+小组负责人”；包内文件名是 01～22 号中文名 | 目录文件名可保留，但最终压缩包外层命名、封面自编代码和报名表必须由学校负责人按官方格式统一处理；当前仓库无法核验报名表是否一致。 |

## 二、按官方五个维度的锐评

### 1. 工艺选择与优化：有设计，缺工艺评定闭环

自动 TIG、NiFe-55、六段四道、对称跳焊、低热输入和层间温度门控的路线是有工程逻辑的；四个候选工艺的横向矩阵也覆盖了题面要求。

但当前参数仍是“设计卡”，不是合格 WPS。最关键的焊接变量没有实物证据：

- 铸铁侧实际熔深、稀释率和焊脚成形没有宏观截面；
- 75 A / 12 V / 1.5 mm/s 对 NiFe-55 Ø1.6 TIG 棒材的熔敷效率 0.85～1.00 是假设范围，不是试验标定；
- 低热输入 330 J/mm 与四道沉积之间的热循环、层间峰值和冷却时间没有实测；
- “400～500 ℃立即锤击”没有说明温度测量位置、测温误差、锤击能量校准和锤头寿命；
- 18 mm 短段 × 24 段的总节拍写得很具体，但还没有设备联调记录。

**判定：** 工艺路线可作为候选设计；不能把“焊缝不存在马氏体转变通道”“冷裂纹通道被关闭”写成已经验证的结果。应改为“设计上抑制/预期降低，需用宏观截面、硬度和裂纹 NDT 验证”。

### 2. 材料选配与连接：焊材选择成立，相图论证过度

NiFe-55 的供应商页面给出了 AWS A5.15 ENiFe-CI、EN ISO 1071 S C NiFe-2、Ni 55%、Rp0.2 300 MPa、Rm 450 MPa、A5 8%，且明确列出球铁、多道焊、钢—铸铁异种连接和机器人/自动化适用性。这一部分是可信的。

但正文的组织判定存在明显逻辑跳跃：

- Schaeffler/DeLong 类图本来是用来估算不锈钢焊缝中 Cr/Ni 当量对应的奥氏体/铁素体/马氏体比例。正文已承认 Ni_eq 46～57 超出常用图域，却又把 `Ni_eq ≥46` 直接拿去和“Fe–Ni 中 Ni≥30%”比较。
- 表 2.4-1 在 50% 稀释时实际 Ni 约 27.53%，低于正文所说的“Ni约≥30%稳定奥氏体”；这里把 Ni_eq 与实际 Ni 混用了。
- `Ms` 经验式在高镍、高碳、铸铁稀释体系中不是足够的相变证明。正文自己写了该式仅对低合金钢标定，却继续用负的 Ms 数值得出“无马氏体转变通道”。
- QT450-10 以“扣除球状石墨后的基体碳”代入当量，是可作模型假设，但不是焊缝熔合区真实化学成分；实际石墨溶解、碳扩散、Si/Mn 偏析和冷却速度仍需截面 EDS/金相/硬度确认。

**判定：** 相图附件有展示价值，但结论应收紧为“按成分混合模型，焊缝主体落在高镍奥氏体倾向区域；熔合线白口、碳化物和局部马氏体不能由该相图单独排除”。这是当前学术上最该改的一处。

### 3. 焊接结构设计：强项，但 6P 的承载/疲劳余量偏紧

六条柔顺槽、R2 槽根、六段 18 mm、内锥胀套和对称跳焊是作品最有辨识度的工程设计。图纸也把 A/B 基准、焊段识别和夹具回退写清楚了。

问题在于 6P 只保留 108 mm 总焊长，条件承载裕量 1.15、疲劳基线裕量 1.21。题面明确说主轴承座承受曲轴/转子全部重量和工作载荷，并长期承受高频振动。当前载荷是“参考包络”，不是实测载荷谱；疲劳又采用 FAT 63～80 的名义应力基线，却没有把以下因素量化进去：

- NiFe-55/球铁熔合线局部硬脆区；
- 角焊缝起止端和焊趾几何缺口；
- 未熔合/未焊透的实际等级；
- 焊接残余拉应力；
- 6 个短焊段的端部效应；
- 壳体薄壁局部屈曲/椭圆化。

**判定：** 6P 可以是低热输入首选，但应把 8P 的切换条件写成主设计的安全门，而不是附录备选。至少应明确：只要实际载荷谱、宏观熔深、疲劳试验或 CMM 任一门不通过，强制切换 8P；不能只写“条件筛查通过”。

反变形部分也偏弱：正文称有三级反变形策略，但主要仍是夹具约束、槽和顺序补偿；没有一个可执行的预偏置量/测量基准/施加方式。由于装配间隙只有 0.01～0.04 mm，应直接给出“允许预偏置范围”和超限处理，否则“反变形设计”更像概念说明。

### 4. 质量检测与评价：项目写了检测清单，但没有验收标准的工程化细节

已有 CMM、宏观截面、硬度、金相、PT/UT、内窥镜和颗粒检查的框架，覆盖面不错。缺口是“方法名有了，判定标准不够”：

- 铸铁/钢异种角焊缝的 PT/UT 适用性、探头频率、覆盖区域和验收等级未定；
- “白口带≤0.2 mm”没有说明沿多少截面、多少测线、采用何种腐蚀和图像标定；
- “显微硬度线扫无异常峰值”没有最大硬度上限、载荷、间距和判定规则；
- 疲劳试验写了 R=0.1、10^7 次、≥3 件，但没有试样几何、应力水平、失效判据、run-out 规则和统计处理；
- CMM 的不确定度 0.002 mm 是预算输入，缺少仪器 MPE、探针、温度补偿和重复测量方案；
- 洁净度只有“颗粒清点+内窥”，没有颗粒尺寸下限、计数面积/体积、可接受数量和抽样方案。

**判定：** 这一维度达到了“有方案”，还未达到“可据此放行”。建议先给出最小可执行验收表，而不是继续增加仿真图。

### 5. 自动化方案：控制逻辑有工程味，适用性尚未验证

胀套、压环、三支点、气幕、姿态互锁、温度门、回退确认和 SPC 叙述完整，属于答辩强项。

但“焊缝跟踪、自适应、在线异常监测、批量质控”大多是数字状态机/合成数据，没有真实焊机、热电偶、流量计、视觉系统或 PLC 联调记录。官方考核点要求“验证其适用性”，所以当前只能写“自动化方案设计与控制逻辑验证”，不能写“已验证自动化适用性”。

此外，紫铜衬环的“热态贴壁”是关键单点失效；名义实体干涉检查不能证明热膨胀、磨损隔离片、颗粒截留和气幕流场。必须做一个最小热态贴壁/颗粒收集试验，哪怕不是完整工件。

## 三、学术与文献核查

### 文献支持了什么

- AWS A5.15:1990(S2023) 的范围确实覆盖球墨铸铁焊接用焊条/焊丝分类，也说明材料应按化学成分分类，不能只凭商品名判定。
- Certilas 的 CEWELD NiFe 55 TIG 页面明确给出 `E NiFe-CI`、`S C NiFe-2`、Ni 55%、Rp0.2 300 MPa、Rm 450 MPa、A5 8%，并列出球铁和钢—铸铁异种接头、自动化应用。
- TWI 资料明确强调铸铁焊前清理、预热/冷却控制、镍/镍铁焊材、热态锤击和缓冷；其球铁典型预热表对铁素体球铁给出 RT～150 ℃、珠光体球铁给出 200～330 ℃。
- 2024 Scientific Reports 的球铁/304 异种焊研究仍观察到球铁/焊缝界面局部马氏体和铁碳化物，说明“焊缝主体奥氏体”不能推出“熔合线没有硬脆组织”。
- 2021 Revista de Metalurgia 的 TIG 球铁研究说明填充材料、热处理/冷却条件会改变组织和力学性能，支持做本件专属小试，而不能替代小试。
- Lincoln Electric TECHALLOY 55 资料给出更直接的反例：该 NiFe-55 类产品建议焊接时预热和层间至少 175 ℃，否则焊缝和 HAZ 可能开裂。它不是唯一工艺答案，但足以证明“不预热、≤100 ℃”必须被当作偏离供应商窗口的专项验证假设。

### 当前文献链的主要问题

1. **同一份证据被同时用于“支持路线”和“证明结果”。** 论文只能支持 NiFe/TIG/低热输入作为候选，不能证明本件熔合线硬度、裂纹、位置度或疲劳寿命。
2. **预热选择没有做真正的对立证据表。** 现在正文写“资料有分歧，所以选择不预热”，但没有按 QT450-10 基体组织、座体厚度、约束程度、热输入和裂纹风险把 0/100/150/200 ℃ 放在同一试验矩阵中。
3. **相图外推没有独立冶金证据。** 需要把“计算预测”与“金相/硬度/EDS 的可证伪判据”绑定，否则相图图很漂亮，结论仍是外推。
4. **疲劳标准引用不够具体。** 只写 IIW FAT 63～80，没有给具体焊缝细节类别、应力定义、厚度修正、应力集中处理和残余应力假设。
5. **供应商典型值被当作本件设计值。** Certilas 页面自己声明这些是典型数据，使用前需通过资格试验确认；报告应把 Rp0.2/Rm/A5 标成“供方典型值”，不能直接作为本件焊缝性能。

## 四、建议的整改顺序

### P0：提交前必须修

1. 统一热制度。决定采用“不预热、≤100 ℃”或“150 ℃、≤200 ℃”，然后同步修改说明书、06/07 号卡、图集 SVG/PDF、相图对比图、导航和所有 JSON。
2. 删除图集的 0.15 mm 薄裙。图集、STEP、工艺卡统一为“3 mm C11000 紫铜衬环 + 可更换隔离片 + 气幕 + 顶部排烟”；如果薄裙保留，只能放在“已否决方案”页并显式标红。
3. 删除“试制阶段完成A类实物工程确认”页脚，改成真实状态。
4. 修正相图结论：把“全域单相奥氏体、无马氏体通道”改成“焊缝主体高镍奥氏体倾向；熔合线局部硬脆组织需通过 V6/V7 验证”。明确区分 Ni、Ni_eq 和相图外推。
5. 在摘要和达标表中把 Ø0.05 写成“设计预算条件性闭合”，并列出热残余、卸夹位移、胀套重复性是待确认项。

### P1：最值得补的实物/验证

1. 做 3 组热制度对照：不预热/100 ℃/150～175 ℃；记录热循环、宏观截面、熔合线硬度和裂纹 PT。
2. 至少做一件代表性 6P 接头的宏观截面和显微硬度线扫；如果无法做完整件，做与实际厚度/拘束相当的平板或环段试样。
3. 做胀套重复装夹和松夹前后 CMM 比对，直接回答 0.002～0.003 mm 分配值是否真实。
4. 做紫铜衬环热态贴壁和颗粒收集对照；记录颗粒尺寸、数量、落点和清洁度判定。
5. 用 8P 做保守备选试样或至少补充疲劳/承载的几何计算，让“强制切换”有真实触发依据。

### P2：答辩必须改口径

- “Schaeffler 证明无马氏体”改为“成分混合模型预测焊缝主体为高镍奥氏体，熔合线组织由金相和硬度确认”。
- “位置度达标”改为“在热残余≤0.0102 mm、卸夹≤0.002 mm、胀套重复性满足分配的条件下，预算闭合；最终由 20±1 ℃ CMM 放行”。
- “洁净度满足”改为“源头低飞溅+铜衬环屏障+回收互锁构成设计控制链，颗粒计数和内窥检查完成后放行”。
- “自动化已验证”改为“自动化状态机和拒绝逻辑已完成数字验证，焊机/传感器/PLC 适用性待联调”。

## 参考链接

- [官方第一届辽宁省大学生材料焊接与铸造工艺设计大赛实施方案](../competition/original-files/welding/第一届辽宁省大学生材料焊接与铸造工艺设计大赛实施方案.pdf)
- [AWS A5.15:1990(S2023) 官方 PDF](https://pubs.aws.org/Download_PDFS/A5.15-90-S2023-Final-Web-PV.pdf)
- [Certilas CEWELD NiFe 55 TIG 产品页](https://certilas.com/en/product/nife-55-tig)
- [TWI Weldability of Materials—Cast Irons](https://www.twi-global.com/technical-knowledge/job-knowledge/weldability-of-materials-cast-irons-025)
- [TWI Can You Weld Cast Iron?](https://www.twi-global.com/technical-knowledge/faqs/can-you-weld-cast-iron)
- [Cárcel-Carrasco et al., Metals 2016](https://doi.org/10.3390/met6110283)
- [El-Shennawy et al., Scientific Reports 2024](https://doi.org/10.1038/s41598-024-70050-0)
- [Martínez Alcón et al., Revista de Metalurgia 2021](https://doi.org/10.3989/revmetalm.194)
