xianzai588/Hanjie/docs/process/heat-management.md

# 热管理（WP2）

> V1.0 · 热制度已冻结为**铸铁冷焊**：不预热、层间温度 ≤100 ℃、焊后半热态锤击。
> 定量依据见 [Schaeffler 相图组织映射与铸铁冷焊冶金设计](schaeffler-diagram-analysis.md) §5.2，
> 计算入口 `studies/SCHAEFFLER-MAP/run.py`，执行参数见 `project/competition-design.yaml`
> 的 `thermal_regime` 与 `peening` 段。

## 温度窗口（路线比较与选定）

| 路线 | 定位 | 预热 | 层间上限 | 冷却方式 | 本件适用性 |
| --- | --- | --- | --- | --- | --- |
| **P0 冷焊** | **选定路线** | **不预热，起焊温度 ≥15 ℃** | **100 ℃** | 保温毯缓冷至 55 ℃ 以下 | **采用**：自由径向收缩协调量 0.0630 mm，与 Ø0.05 mm 位置度相容 |
| P1 中等预热 | 对比路线 | 150 ℃ | 100 ℃ | 保温缓冷 | 数值互斥：预热使座体起焊前即高于层间门 |
| P2 较高预热 | 对比路线 | 250～350 ℃ | 自洽 | 保温缓冷 | 蓄热与收缩协调量超出位置度预算 |
| P3 热焊法 | 对比路线 | ≥400 ℃ | 自洽 | 保温缓冷 | 座体蓄热 151.15 kJ（四道净热输入的 106%），收缩协调量 0.3780 mm，不作优先选项 |

**选定理由（定量）**：

- 座体质量 0.6846 kg、比热 460 J/(kg·K)：起焊前蓄热 100 ℃ 时 25.19 kJ、150 ℃ 时 40.94 kJ、500 ℃ 时 151.15 kJ（四道名义净热输入 142.56 kJ）。
- 自由径向收缩协调量 r·α·ΔT（r = 74.98 mm、α = 10.5×10⁻⁶/K）：层间 100 ℃ 为 0.0630 mm、层间 200 ℃ 为 0.1418 mm、预热 150 ℃ 为 0.1024 mm、热焊 500 ℃ 为 0.3780 mm。
- 孔区与焊道间 31.7 K 温差即产生 0.025 mm 径向漂移，等于 Ø0.05 mm 位置度径向限值。降低整件温度水平就是降低温度梯度。
- 位置度预算不允许预热的热代价：预热 150 ℃ 预置 40.94 kJ 蓄热、抬高管座收缩协调量，并与层间 ≤ 100 ℃ 互斥；而 150 ℃ 级预热对半熔化区白口的抑制有限（显著抑制需 500～700 ℃ 热焊）。白口与 HAZ 的残余风险由低热输入限宽、镍基过渡带（NiFe-55 从外部引入镍）与锤击管理拉应力承担，并以金相门限（V6/V7）验证。

> 测温手段（测温枪/热电偶）见设备调查 §1、§3；监控点布置为距焊道边缘 10 mm 的座体表面。

## 后热与热处理

- 后热缓冷：四道完成后覆盖耐高温保温毯缓冷至 55 ℃ 以下，避免终冷阶段产生附加温度梯度。
- 焊后去应力退火（PWHT）对球铁焊缝的作用与变形风险并存，保留为对比试验项，不列入主流程。
- 与焊接顺序（S3：1→4→3→6→2→5）耦合：跳焊序列把单轮连续焊的热量分散到六个周向位置；层间可达成性按整件＋局部两尺度估算（说明书 §2.5(5)），常温车间估算值骑在门限附近，层间门保留为硬联锁，超温由状态机插入等待。

## 应力与散热路径

- **逐段锤击消应力（已列入主流程）**：每段收弧后在焊道 400～500 ℃ 窗口内以气动圆头锤轻击，搭接率 ≥75%，覆盖焊道全宽及熔合线两侧各 5 mm。冷却后锤击层稳定处于压应力状态。详见 [冷焊与半热态锤击专项工艺卡](../../deliverables/process/cold-weld-and-peening-card.md)。
- **紫铜衬环强制吸热**：C11000 衬环（壁厚 3 mm，导热率 ≥380 W/(m·K)）贴近焊缝下缘，把热量从孔周引开；外缘与壳体内壁限位贴合，接触面设可更换低摩擦隔离片，避免金属直接刮擦生屑。详见 [../../cad/fixture/](../../cad/fixture/)。
- 焊后冷却路径对残余应力的影响由 `project/competition-design.yaml` 的摩擦与释放逻辑、以及说明书 §6.3 的热—弹塑性求解方案共同处理。
