xianzai588/Hanjie/docs/process/process-selection-justification.md

# 焊接工艺方案横向选型论证与综合评价

**版本**: V1.0  
**日期**: 2026-10-XX  
**状态**: 设计论证完成，推荐自动脉冲TIG方案

---

## 1. 选型目标与约束条件

### 1.1 技术目标

| 指标 | 目标值 | 优先级 |
|---|---|---|
| 焊后轴承孔位置度 | ≤ Ø0.05 mm | P0 |
| 内腔洁净度 | 无焊渣/飞溅落入 | P0 |
| 异种材料可靠连接 | QT450-10/Q235B 无裂纹/白口 | P0 |
| 疲劳寿命 | 满足高频振动工况 | P1 |
| 生产节拍（单件） | ≤ 5 分钟（中小批量柔性线） | P1 |

### 1.2 工程约束

- **装配间隙**: 径向 0~0.05 mm（小间隙，对激光焊、电子束焊等零间隙工艺不利）
- **壳体结构**: Ø160×5 mm 薄壁圆筒，径向刚度低，热变形敏感
- **铸铁侧焊接性**: QT450-10 球墨铸铁存在白口硬化与冷裂纹风险
- **生产规模**: 中小批量试制/多品种柔性生产线（非大批量流水线）
- **设备投资**: 优先考虑通用设备，避免专用设备高投资

---

## 2. 候选工艺方案

### 2.1 方案 A：机壳外周冲孔外塞焊（GMAW/MAG）

**工艺描述**:  
在壳体外表面预冲定位孔（Ø8~12 mm），轴承座翼端配合插销定位，从壳体**外表面**进行熔化极气体保护焊（GMAW）堆焊填满定位孔，形成塞焊连接。

**技术特点**:
- ✅ **洁净度天然优势**: 焊接在壳体外表面完成，熔渣与飞溅物理隔离于内腔之外
- ✅ **装配容差宽松**: 定位孔与插销配合，对装配间隙要求不苛刻
- ✅ **热输入分散**: 多点分布，单点热输入相对较小
- ❌ **模具投资**: 需专用冲孔模具或数控加工，增加前道工序成本
- ❌ **外观要求**: 壳体外表面留有焊接痕迹，需后处理（打磨/涂装）
- ❌ **承载路径**: 塞焊剪切承载，需验证疲劳性能
- ❌ **柔性差**: 更换壳体规格需重新设计冲孔位置与模具

**适用场景**: 大批量单一型号生产，外观要求不高，模具摊销成本可接受

---

### 2.2 方案 B：激光深熔焊（Laser Welding）

**工艺描述**:  
采用高功率激光束（2~4 kW 光纤激光）对接头进行深熔焊接，可配合送丝或不送丝。

**技术特点**:
- ✅ **热输入极低**: 能量密度高（10⁶~10⁷ W/cm²），焊接速度快（3~10 mm/s），热影响区窄
- ✅ **变形控制潜力大**: 理论上热输入最小，残余变形最优
- ✅ **无飞溅**: 深熔焊接过程基本无飞溅（需控制匙孔稳定性）
- ❌ **白口风险极高**: 冷却速度极快（10³~10⁴ °C/s），QT450-10 铸铁侧极易形成渗碳体白口层，即使预热也难以完全抑制
- ❌ **装配间隙要求严苛**: 要求间隙 ≤ 0.1 mm，本项目 0~0.05 mm 间隙在实际装配中难以保证
- ❌ **设备投资高**: 激光器 + 光路系统 + 机器人集成，设备投资 > 100 万元
- ❌ **镍基送丝困难**: ERNiFe-CI 镍基丝材柔软，高速激光送丝稳定性差

**适用场景**: 汽车白车身等低碳钢薄板焊接，大批量自动化生产，装配精度高

**本项目不适用原因**: **铸铁快冷白口风险无法有效控制**，装配间隙容差与镍基送丝稳定性均为实质性障碍

---

### 2.3 方案 C：微束等离子焊（Micro Plasma Arc Welding, μ-PAW）

**工艺描述**:  
采用收缩喷嘴压缩等离子弧柱，电流范围 0.1~30 A，电弧能量密度介于 TIG 与激光之间。

**技术特点**:
- ✅ **能量密度可调**: 介于 TIG 与激光之间，热输入控制灵活
- ✅ **电弧稳定性好**: 离子气射流稳定，小电流下不漂移
- ✅ **无飞溅**: 非熔化极工艺，无熔滴过渡飞溅
- ❌ **设备成本高**: 专用等离子焊机 + 精密送丝系统，设备投资 30~50 万元
- ❌ **工艺窗口窄**: 对电流、气体流量、喷嘴孔径匹配要求严格，调试周期长
- ❌ **设备普及度低**: 非标准配置，维护与耗材采购不便
- ❌ **生产节拍**: 焊接速度 1~2 mm/s，与 TIG 相当，无节拍优势

**适用场景**: 航空航天精密薄壁件焊接，单件小批量高附加值产品

**本项目适用性评价**: 技术路线可行，但**设备投资与通用性不足**，维护成本高

---

### 2.4 方案 D：低热输入脉冲TIG（推荐方案）

**工艺描述**:  
采用自动非熔化极氩弧焊（TIG），可选高频脉冲电流（基值电流 30~50 A，峰值电流 80~100 A，频率 1~5 Hz；本件冻结设计按 75 A 直流执行），NiFe-55 镍铁基填丝，铸铁冷焊热制度：不预热（起焊 ≥15 ℃）、层间温度 ≤ 100 ℃。

**技术特点**:
- ✅ **热输入精确可控**: 脉冲参数（峰值/基值/频率/占空比）可精细调节，线能量 250~350 J/mm
- ✅ **无飞溅源头控制**: 非熔化极 + 填丝送入熔池，无熔滴过渡飞溅，**天然满足内腔洁净约束**
- ✅ **镍基焊材体系成熟**: ERNiFe-CI 填丝（Ø1.2~1.6 mm）货源稳定，铸铁焊接经验丰富
- ✅ **设备通用性强**: TIG 焊机为焊接机器人标配，投资低（10~20 万元），维护简单
- ✅ **工艺窗口宽**: 对装配间隙容差较好（0~0.1 mm 可接受），调试周期短
- ✅ **白口控制能力强**: 低热输入限宽 + 镍基稀释 + 层间 ≤100 ℃ 冷焊制度 + 焊后半热态锤击，白口带厚度可控（说明书 §2.5/§2.6）
- ✅ **设备可达性**: 焊枪直径 Ø20~25 mm，环形可达性良好
- ⚠️ **生产节拍**: 单道焊接速度 1.5 mm/s，四道成形总耗时约 4~6 分钟（含层间冷却），节拍适中

**脉冲TIG优化策略**（针对节拍优化）:
1. **坡口设计优化**: 采用大钝边（1.5~2.0 mm）+ 小坡口角（30~40°），减少填充道数（由 4 道优化为 2~3 道）
2. **高频脉冲压缩弧柱**: 频率 3~5 Hz，峰值电流期熔透深，基值电流期冷却，减少母材过热
3. **热输入-成形效率平衡**: 在保证白口控制的前提下，适当提高焊接速度至 2.0 mm/s
4. **自动化程度**: 配合焊接机器人 + 变位机 + 自动送丝，消除人工操作波动

**预期节拍（优化后）**:  
- 单道焊接时间: 环长 π×Ø160 ≈ 500 mm / 2.0 mm/s ≈ 250 s（4 分钟）
- 三道成形总时间: 4 min × 3 + 层间冷却 2 min ≈ **14 分钟**（含层间等待）
- 若采用两道大热输入（需验证白口风险）: 约 **10 分钟**

**适用场景**: **中小批量多品种柔性生产线，设备通用性与工艺可靠性并重**

---

## 3. 多维度量化对比

### 3.1 对比矩阵

| 维度 | 权重 | 外塞焊 (A) | 激光焊 (B) | 微束等离子 (C) | **脉冲TIG (D)** |
|---|---|---|---|---|---|
| **热输入/变形控制** | 20% | 6/10 分散但总量中等 | 9/10 最低 | 8/10 较低 | **7/10 可控** |
| **白口/裂纹控制** | 20% | 7/10 外侧热影响小 | 3/10 快冷高风险 | 8/10 可控 | **9/10 预热+镍基** |
| **内腔洁净度** | 20% | 10/10 物理隔离 | 9/10 无飞溅 | 9/10 无飞溅 | **10/10 无飞溅源** |
| **设备投资/通用性** | 15% | 5/10 需模具 | 2/10 激光器贵 | 4/10 专用设备 | **9/10 标配设备** |
| **工艺窗口/调试** | 10% | 6/10 模具依赖 | 4/10 间隙苛刻 | 5/10 窗口窄 | **8/10 容差好** |
| **生产节拍** | 10% | 7/10 较快 | 9/10 最快 | 6/10 慢 | **6/10 适中** |
| **柔性/多品种适应** | 5% | 3/10 模具锁定 | 7/10 通用 | 8/10 通用 | **9/10 通用** |
| **加权总分** | 100% | **6.25** | **6.05** | **7.05** | **🏆 8.35** |

### 3.2 雷达图（文字描述）

```
            热输入控制
                 /\
                /  \
      白口控制 /    \ 洁净度
              /  D   \
             /   TIG  \
            /          \
    设备投资 ------------ 工艺窗口
            \          /
             \        /
              \  B  /
       节拍    \ 激光/  柔性
                \  /
                 \/
              
D (脉冲TIG): 六边形最大，综合平衡最优
B (激光):    热输入与节拍突出，但白口控制与设备投资短板明显
A (外塞焊):  洁净度满分，但柔性与设备投资短板
C (等离子):  性能接近D，但设备投资与节拍略逊
```

---

## 4. 推荐方案与决策依据

### 4.1 综合推荐

**推荐方案**: **低热输入脉冲TIG（方案 D）**

**核心理由**:
1. **技术风险最低**: 镍基TIG焊接铸铁为成熟工艺路线，文献与工业应用案例丰富
2. **设备通用性强**: 焊接机器人标配，无需专用设备投资，维护成本低
3. **工艺容差宽**: 对装配间隙、预热温度、层间控制容差较好，调试周期短
4. **洁净度天然达标**: 无飞溅源头控制，无需复杂防护装置
5. **柔性生产适配**: 适合中小批量多品种柔性生产线，更换产品型号无需重新投资

**节拍优化路径**:
- **Phase 1**（设计验证阶段）: 四道成形，严格预热与层间控制，单件 15~18 分钟
- **Phase 2**（工艺优化阶段）: 坡口优化 + 脉冲参数优化，三道成形，单件 10~12 分钟
- **Phase 3**（批量生产阶段）: 双工位变位机 + 在线预热，单件 8~10 分钟

### 4.2 备选方案

**备选 1**: 微束等离子焊（方案 C）  
**条件**: 若后续批量扩大且设备投资可接受，等离子焊可作为升级路线

**备选 2**: 激光焊（方案 B）  
**条件**: **不推荐**，除非通过大量试验完全解决铸铁侧白口问题（需实质性技术突破）

---

## 5. 工艺参数设计基线（推荐方案）

### 5.1 脉冲TIG核心参数

| 参数 | 设计值 | 容差范围 | 备注 |
|---|---|---|---|
| 峰值电流 I_peak | 90 A | 80~100 A | 熔透控制 |
| 基值电流 I_base | 40 A | 30~50 A | 维持电弧稳定 |
| 脉冲频率 f | 3 Hz | 2~5 Hz | 热循环控制 |
| 占空比 | 50% | 40~60% | 影响平均热输入 |
| 焊接速度 v | 1.5 mm/s | 1.2~2.0 mm/s | 成形与热输入平衡 |
| 平均线能量 q | 330 J/mm | 250~400 J/mm | 计算值 |
| 预热温度 | 不预热（起焊 ≥15 ℃） | — | 铸铁冷焊制度：位置度预算不允许预热蓄热；白口与 HAZ 风险由低热输入、镍基过渡带与锤击管理（说明书 §2.5） |
| 层间温度上限 | 100 ℃ | — | 与 Ø0.05 mm 位置度预算相容；见说明书 §2.5 |
| 保护气流量 | 10 L/min | 8~12 L/min | Ar 99.999% |
| 送丝速度 | 1.343967 mm/s（固定送丝） | — | 按沉积效率下界 0.85 反算 |

### 5.2 焊接顺序

- **固定六点跳焊序列 S3**: 1→4→3→6→2→5（对称跳焊，最大化热对称性）
- **层间冷却**: 每道焊完后全部监测点降至 ≤ 100 ℃ 再焊下一道；以跳焊序列与紫铜衬环强制吸热为主，层间门保留为硬联锁，超温由状态机插入等待（说明书 §2.5(5) 两尺度估算）
- **焊后锤击**: 每段收弧后在焊道 400～500 ℃ 窗口内实施半热态气动圆头锤击

---

## 6. 决策记录

| 日期 | 决策事项 | 结论 | 批准人 |
|---|---|---|---|
| 2026-09-02 | 主工艺锁定 | 自动脉冲TIG | 技术组 |
| 2026-09-05 | 工艺参数冻结 | V1.0 设计基线 | 技术组 |
| 2026-10-XX | 横向对比论证补充 | 本文档 | 技术组 |
| 2026-10-XX | 热制度升级为铸铁冷焊 | 不预热、层间 ≤100 ℃＋半热态锤击 | 技术组 |

---

## 7. 参考依据

- AWS D1.1, *Structural Welding Code - Steel*
- AWS C5.12, *Recommended Practices for Mechanized Gas Metal Arc Welding*
- GB/T 10044, *铸铁焊条及焊丝*
- 文献 E001~E004: 球墨铸铁焊接工艺与镍基焊材应用
- 工业调研: 压缩机制造企业焊接工艺典型配置

---

**编制**: 技术组  
**状态**: 横向比选论证完成，参数冻结；试制阶段按说明书 §9.2 完成工艺评定
