xianzai588/Hanjie/docs/review/competition-r1-gap-analysis.md

# COMPETITION-R1 竞赛适配性诊断与整改方案

> 日期：2026-09-20　｜　距作品提交截止（10-25）约 5 周，距报名截止（10-20）约 4 周
> 依据：`competition/original-files/welding/...实施方案.pdf`（已提取原文逐条核对）、`deliverables/submission/`、`project/stage-status.yaml`、`docs/EXECUTIVE_SUMMARY.md`

---

## 0. 一句话结论

**不是"中看不中用"。是"中看"已经做到省一水平，"中用"的证据链只差最后一环没接上——而官方考核要点四问，四问都在问这一环。**

最尖锐的说法：

> 这份作品是为「不被打倒」写的，不是为「打动评委」写的。它是一份**审计报告**，不是一份**参赛作品**。

全部 9 月 6 日以后的工作（THERMAL-0.4R1 → 0.4R2 → XSEC → NEST → Neumann → Elmer REF → Plan7 → Plan8 → 432 例敏感性）在 `stage-status.yaml` 里的验收结论，几乎每一条都是 `not_passed` / `no_resolved_robust_winner` / `unvalidated`。**花了 60% 的力气，产出了一批"排除了一些可能性"的记录。**

对评委而言，"我们证明了这条路走不通"是减分项，不是加分项。

---

## 1. 合规性逐条对照

### 1.1 形式合规 —— ✅ 全部满足

| 官方条款（原文） | 项目 | 判定 |
| --- | --- | --- |
| "最终提交参赛作品可以包括项目研究报告、项目设计图或研究实物" | 22 页说明书 + 6 页设计图集 + 名义装配 STEP | ✅ 三选一中的两项 |
| "固定题目项目说明书格式及篇幅不受限制" | 14 页，自定版式 | ✅ |
| "参赛小组参赛学生 2-4 人、指导老师 1-2 名" | 由校方与报名表承担 | ✅ 不属交付物 |
| "10 月 20 日前报名；10 月 25 日（含）提交" | 已登记 | ✅ |
| 英文匿名为铸造赛道条款 | 已正确识别、未套用 | ✅ 判断正确 |

**形式层面没有硬伤。** 这一点先排除掉——你担心的"没有符合要求"，主要不在形式上。

### 1.2 内容合规 —— ⚠️ 三处实质缺口、一处硬指标未闭合

官方题面给出**五个维度**与**四条考核要点**。逐条比对：

| 官方维度原文列举项 | 项目现状 | 判定 |
| --- | --- | --- |
| ① 焊接与连接方法选型、热输入与热管理、预热与后热、连接顺序 | TIG + ENiFe-CI + 四道 + 6P 跳焊 + 150 ℃ 预热 | ✅ 覆盖充分 |
| ② 焊丝/焊条选型 | NiFe 55 / ERNiFe-CI，有供方页面 + 标准分类 | ⚠️ 只有文献与供方页面 |
| ② **异种材料界面设计与过渡层** | v4 说明书**无对应章节** | ❌ **缺失** |
| ② **待焊表面预处理** | 全文仅"清理"二字 | ❌ **严重不足** |
| ② 焊接材料的强度与韧性匹配 | 引用了 400～579 MPa，但明确声明"不作为许用值" | ⚠️ 有数据不敢用 |
| ③ 接头形式设计、焊缝布局优化 | 6P-FAIR_B、六段 18 mm、R2 槽根 | ✅ 最强项 |
| ③ **反变形设计** | 只有"逐件装配预偏置"（补偿的是装配姿态，不是焊后变形） | ❌ **实质缺失** |
| ③ **散热或隔热结构** | V3 的 4 mm 柔顺槽在 R1 已从配置中消失 | ❌ **缺失** |
| ④ NDT 方法选择 | 仅"适用表面 NDT"一句，未选 PT/UT 与标准 | ⚠️ 过薄 |
| ④ 焊接变形精密测量、同轴度检测 | A/B 基准、CMM、不确定度判定规则 | ✅ 覆盖好 |
| ④ 焊缝金相组织评价 | 出现在放行门清单，无方法细节 | ⚠️ 过薄 |
| ④ **力学性能与疲劳试验方案** | **v4 说明书全文无疲劳章节** | ❌ **缺失（且是回退）** |
| ④ 焊渣与洁净度检查方法 | 薄裙 + 朝上回收 + 内窥 + 颗粒清点 | ✅ 覆盖好 |
| ⑤ 装备选型、定位夹紧工装 | 胀套 + 独立压环 + 三支点 | ✅ 覆盖好 |
| ⑤ 焊接路径规划 | 有，但仅参数级 | ⚠️ 偏薄 |
| ⑤ 焊缝跟踪与自适应控制 | 状态机 + 温度门控 | ⚠️ 全为合成原型 |
| ⑤ 在线监测、批量质控、人机协作 | 视觉/异常检测为合成分支；人机协作未提 | ⚠️ 已被 `frozen_work` 冻结 |

### 1.3 最硬的一条：疲劳章节被删掉了（这是回退，不只是缺失）

`deliverables/report/technical-report-v2.md` §5 完整写过「焊缝疲劳与寿命评估」，包含 IIW 名义应力法 FAT 63–80 基线、疲劳热点与设计对策、三级验证试验计划。

**v4 说明书把这一整节删了。** 而官方题面原文：

> "焊缝在压缩机长期高频振动工况下承受交变载荷，**疲劳寿命要求高**。"

并且维度④原文明确要求「力学性能与疲劳试验方案」。

**这是目前最容易补、也最不该丢的一分。** v2 的稿子还在仓库里，捡回来更新成"6P 四道"口径即可，成本不到一天。

### 1.4 硬指标闭合状态

| 指标 | 官方要求 | 项目当前 | 判定 |
| --- | --- | --- | --- |
| 位置度 | ≤ Ø0.05 mm | 新预算 0.0456 mm（**其中 0.008 热残余 + 0.002 卸夹为假设**）；旧预算 Ø0.070 mm 明确超限 | ❌ **无达标证据** |
| 洁净度 | 不得产生可能落入内部的焊渣飞溅 | 设计闭环完整，无实测 | ⚠️ 设计成立、未验证 |
| 焊得住 | 异种材料可靠连接 | 文献 + 条件承载筛查 | ❌ 无任何试样 |

---

## 2. "中看不中用"的五个病灶（诊断）

### 病灶 1｜叙事自杀：作品在替评委否定自己

摘要第一段就写"本作品形成一套可直接进入工艺评审的数字设计方案"；第二段"仍须另行验证"；第三段"正式热—结构证据、最终位置度和洁净度仍按独立检测流程放行"。

§7.1 三项放行总表：**焊得住 / 位置度 / 洁净度，状态栏三行全是「待验证」。**

学术上这是诚信。竞赛上，评委翻到这一页会形成一个印象：**"这个队自己知道什么都没验证。"** 一旦这个印象形成，后面所有精妙的设计都变成"纸上功夫"的注脚。

> 诚实不必删，但**位置必须换**。正文讲"我们做了什么、结论是什么、为什么可信"；把所有"未验证"集中到最后一节《局限与验证路线》+ 证据等级附表（这张表你已经有了，就是 17 号文件）。

### 病灶 2｜研究跑偏：把火力全打在评委不看的靶子上

从 `DECISIONS.md` 第 13～22 条和 `stage-status.yaml` 看，9 月 6 日至今的主线是**自研热求解器的网格收敛与跨求解器对齐**：

- 0.4R1 空间网格未收敛 → 0.4R2-A 降到 16.682 ℃ 仍未过 10 ℃ 门
- XSEC 三级非单调 → NEST 严格嵌套仍有 10.923 ℃ → 边界 Neumann → Elmer 对照 → Plan7 出生焓账 → Plan8 交换账
- 最后结论：*"剩余空间场差异作为模型形式不确定性保留"*

**这一段在竞赛里的期望收益接近于零，期望损失却很大**——因为评委只会读到"你们的热模型没做出来"，而不会读到"你们严谨地排除了六种数值成因"。

自研 FVM 收敛性不是这道题要考的东西。题目要考的是：**这个接头该怎么焊、怎么保证不歪、怎么保证不脏。**

### 病灶 3｜闭环断在最后 0.010 mm

你已经做对的：
- 填丝守恒闭环：Ø1.2 单道 → Ø1.6 四道，1.737 mm 焊脚矛盾解决了 ✅
- 公差预算闭环：0.0218 径向 → Ø0.0436 + 0.002 不确定度 = 0.0456 < 0.05 ✅
- 工装几何闭环：裸锥穿透 → 内置锥驱动胀套，实体检查零干涉 ✅
- 拒绝逻辑闭环：缺信号/超温/未回退全部拒绝 ✅

**唯一没接上的一环**：预算表里最大的一项 `热残余 0.008 mm` 是设计目标；第二大的 `卸夹 0.002 mm` 也是。这两项加起来 0.010 mm，占整个 Ø0.05 预算的 2/3。

项目自己也写明了：

> "若热残余回到旧预算 0.012，则含不确定度后超限。"

也就是说——**Ø0.05 能不能达标，完全取决于一个没测过的数。** 评委问到这一层，现有的答案是"不知道"。

### 病灶 4｜核心创新与题面诉求正面冲突（最危险的一条）

这是我认为评委最可能致命一击的地方：

| | 焊缝总长 | 名义净热输入 | 条件所需许用 | 裕量 |
| --- | ---: | ---: | ---: | ---: |
| Continuous | 471.11 mm | 621.87 kJ | 11.96 MPa | 5.0× |
| **6P-FAIR_B（推荐）** | **108.00 mm** | 142.56 kJ | **52.17 MPa** | **1.15×** |
| 8P-FAIR_B | 144.00 mm | 190.08 kJ | 42.44 MPa | 1.41× |

推荐方案把焊缝长度压缩到整圈的 **23%**，代价是承载裕量从 5.0× 掉到 **1.15×**。

而官方题面把这个件的服役条件写得很重：

> "承载曲轴、转子等运动部件的**全部重量与工作载荷**""**长期高频振动**工况下承受**交变载荷**，疲劳寿命要求高"

评委必然会问：**"你为了控制变形，把焊缝砍掉 77%、安全裕量砍到 1.15，靠一个自己承认'不是真实载荷'的 60 MPa 包络来兜底，凭什么说这个座子不会在压缩机里振裂？"**

§3 里那句"模型不含焊趾缺口、未熔合、热残余、接触分担或**疲劳**"，等于自己把这个问题摆到了桌面上而没有回答。

**这条不解决，方案越"轻巧"，越像炫技。**

### 病灶 5｜把"设计"当成了"验证"，拿分点写成了减分点

§7 的《数字证据》表 7 行，其中：

- 热模型 → "空间准入未过，限制保留"
- 结构敏感性 → "432 例，**没有稳健优胜方案**"

这两行放在报告正文里，读者得到的信号是"研究失败"。而它们真实的价值（"我们证明了在当前不确定度下 6P/8P 不可分辨，因此选择依据应转向可制造性与热量，而不是继续挑数字"）**没有被写出来**。

**有结论的失败是成果；没有结论的失败只是失败。**

---

## 3. 客观评价：最强与最弱

### 真正的强项（不要改，要放大）

1. **几何是真的。** 6P-FAIR_B 是真实 BREP，不是示意图；装配 STEP 可查；工装干涉是实体布尔检查。本科生竞赛里能做到这一步的不多。
2. **图纸专业度极高。** 标题栏、基准 A/B/C、位置度框、公差限值、免责声明、图号 HJ-R1-001 …… 见 `cad/generated/engineering-drawings/bearing-seat.png`。这是"中看"的实体，而且是真的专业。
3. **误差预算链条完整，且保留了失败对照。** 旧 Ø0.070 超限的记录没有删——这在答辩时是加分项（说明你知道自己错在哪、怎么改的）。
4. **有拒绝条件。** 缺信号/超温/未回退/不确定度超限全部拒绝。工程味很足，比"什么都通过"的 demo 强得多。
5. **证据分级 A/B/C 体系。** 17 号文件那张表，答辩时是真加分项。
6. **全链路可复现。** `run.py` 一行跑通，构建脚本拒绝过期结果。评审专家想验证，随时能验。

### 真正的弱项

| 弱项 | 严重度 | 可补性 |
| --- | --- | --- |
| 零物理证据（无焊机、无金相、无硬度、无 CMM） | ★★★★★ | 中（取决于能否借到实验室） |
| Ø0.05 无任何达标证据 | ★★★★★ | 中 |
| 疲劳章节缺失（v2 有、v4 删了） | ★★★★ | **高（一天）** |
| 6P 承载裕量 1.15 与"高频振动"诉求冲突 | ★★★★ | 中 |
| 维度②界面/预处理、维度③反变形/隔热 缺失 | ★★★ | **高（1-2 天）** |
| 热模型挣扎史占据正文 | ★★★ | **高（半天）** |
| 自动化全为合成分支、已被冻结 | ★★ | 低 |

---

## 4. 整改方案

### 4.0 不依赖任何设备、必须做的（1 周内，收益最高）

| # | 动作 | 具体做法 | 产出 |
| --- | --- | --- | --- |
| A1 | **报告叙事重组** | 摘要第一段改为结论先行：推荐方案 + 关键数字 + 一条证据 + 一句"验证路径"。把散落各处的"未验证/不宣称"收拢到文末《局限与验证路线》。 | 说明书 v5 |
| A2 | **补回疲劳章节** | 从 `technical-report-v2.md` §5 捡回，更新为 6P 四道口径：IIW 名义应力 FAT 63–80；**正面回应 108 mm 焊缝的疲劳裕量**；三级验证试验计划（接头级 R=0.1 / 部件级振动台 / 整机级）。 | 新增 §5，约 1.5 页 |
| A3 | **补维度②缺口** | 新增"坡口与表面预处理"小节：待焊面机械清理/去油/去石墨层、镍基过渡层或预堆边、层间温度控制、后热与缓冷制度。哪怕按文献写，也要成节。 | 新增 0.5 页 |
| A4 | **补维度③缺口** | 反变形：给出**具体的反变形量与实施方式**（如装配预偏置 0.02 mm 反向 + 焊接顺序补偿），而不是只有公差分配；隔热：恢复"轴承座本体径向散热/隔热槽"设计并给出尺寸与依据。 | 新增 0.5 页 |
| A5 | **压缩热模型叙述** | §7 里热模型那两行删掉或改为一句结论："局部热模型用于确定热输入窗口与风险边界，空间准入未通过，故不将其作为位置度证据。"删掉全过程。 | 净减 1 页 |
| A6 | **把"失败"改写成"结论"** | 432 例的表述改为："在现有不确定度下 6P/8P 不可分辨，故选择依据转向热量、可制造性与对称性；这条结论本身即为设计依据。" | 改写 1 段 |
| A7 | **给 Ø0.05 一个答案** | 现在的问题是"没有答案"。改成句式：**"在 X 条件下预计可达 Ø0.0yy；敏感项为热残余，需通过 Y 验证；已有 Z 证据支持。"** 哪怕结论是"条件性可达"，也比"未证明"强一百倍。 | 改写摘要 + §6 |

### 4.1 路线 A：能借到焊机 + 硬度计（强烈建议，收益最大）

**三个小试，全部可在一次实验课时间内完成。**

| 小试 | 做法 | 直接回答的官方要求 | 预计耗时 |
| --- | --- | --- | --- |
| **T1 焊接性验证** | QT450-10 板 + Q235B 板，ENiFe-CI 棒，DCEN 75 A / 12 V / 1.5 mm·s⁻¹，预热 150 ℃，打一条 100 mm 角焊缝。 | 维度②「材料选配与连接」、考核要点"验证了其适用性" | 半天：焊 + 拍照 |
| **T2 组织与硬度** | T1 试样切割 → 磨抛 → 腐蚀 → 宏观截面照片（测熔深、熔合线、白口层厚度）→ 显微硬度线扫（母材/HAZ/熔合线/焊缝）。 | 维度④「焊缝金相组织评价」、②「强度与韧性匹配」 | 1 天（含制样） |
| **T3 洁净度对照** | 用开口容器模拟内腔，对比"无防护 / 有连续屏障"两种情况下焊接后的飞溅落物——**收集、称重、计数、拍照**。 | 维度④「焊渣与洁净度检查方法」、题面硬约束 | 半天 |

**三张小表的威力，大于你现在那 432 例敏感性 + 8 个热模型算例的总和。** 因为它们是"验证"，而后者不是。

**顺带解决病灶 4**：T1/T2 如果做出来，就能给出"108 mm 焊缝、FAT 基线、实测硬度与熔合线"，把裕量 1.15 的问题从"没回答"变成"有数据支撑的保守设计"。

### 4.2 路线 B：只能借到部分设备

优先级：**T1 > T3 > T2**。
- 只有焊机 → 做 T1 + T3（外观照 + 飞溅收集），已能把维度②和洁净度从"文献"提到"实测"。
- 只有金相/硬度没有焊机 → 难以独立完成，转路线 C。

### 4.3 路线 C：完全拿不到设备（务实的兜底）

| # | 动作 | 说明 |
| --- | --- | --- |
| C1 | **文献对标表** | 找 ≥5 篇同体系（球墨铸铁/低碳钢 + NiFe 焊材）的公开研究或 WPS，做参数对标表："本方案参数落在已发表成功窗口内"。**这是"适用性验证"的最低成本形态。** |
| C2 | **做一个真实动作模型** | 3D 打印 / 亚克力做 胀套 + 薄裙接料盘 的可动模型，拍一段"插入 → 胀紧 → 焊后回退 → 贴壁下撤"的视频。官方原文明确允许提交**研究实物**。成本：几十元 + 一天。 |
| C3 | **拒绝逻辑演示录屏** | 把已有的状态机 demo 录成 60 秒：模拟"防护未在位 → 拒绝起弧""超温 → 停弧""未回退 → 禁止下撤"。**"会说'不'的系统"在答辩里非常讨好。** |
| C4 | **数字化演示件** | 用 `03-名义装配包络.step` 做一段可交互三维剖切（HTML/视频），让评委能自己转着看 6P 布局、胀套接触带、薄裙路径。 |

路线 C 的产出性质是"实物模型 + 演示"，不是"实验数据"。**要在报告里把两者严格区分**——这正是你证据分级体系的长处。

### 4.4 4 周行动表

| 周次 | 日期 | 主线 | 交付 |
| --- | --- | --- | --- |
| W1 | 09-20 ~ 09-26 | ①找指导教师落实实验室（焊机/硬度/切割）②A1~A7 报告整改 | 说明书 v5 定稿（无新数据版） |
| W2 | 09-27 ~ 10-03 | 路线 A 的 T1 + T3（或路线 C 的 C1 + C2） | 焊接试样照片、飞溅对照数据/模型视频 |
| W3 | 10-04 ~ 10-10 | T2 制样与硬度线扫；重做图纸/说明书插图 | 金相照片、硬度曲线图、更新后的设计图集 |
| W4 | 10-11 ~ 10-17 | 数据入报告 → 重跑 `build_submission.py` → 答辩 PPT + 60 秒演示视频 → **内部攻击式预答辩**（用 `docs/review/competition-r1-attack-review.md` 那张表，但**加上病灶 4 的三个新问题**） | 封版 RC3、PPT、视频 |
| W5 | 10-18 ~ 10-25 | 10-20 前完成报名；终检、命名、盖章汇总表、提交 | 提交完成 |

---

## 5. 答辩必答（在现有 18 问之外新增）

现有 `docs/review/competition-r1-attack-review.md` 的 18 问质量很高，但**缺了最致命的三个**：

| 新增攻击问题 | 现在的答案 | 必须补成 |
| --- | --- | --- |
| **108 mm 焊缝只占整圈 23%，承载裕量 1.15，凭什么保证压缩机长期高频振动下不裂？** | "条件筛查通过" | 疲劳校核 + 实测/文献数据 + 明确的安全系数论证 |
| **焊后位置度到底达没达到 Ø0.05？** | "尚未证明" | "在 X 条件下预计可达 Ø0.0yy，敏感项是热残余，验证路径是 Y" |
| **你们做了那么多热仿真，结论是什么？** | "空间网格未收敛" | "确定了热输入窗口，并把位置度证据交给独立测量——这是我们主动的证据边界划分" |

---

## 6. 底线判断

| 场景 | 预计结果 |
| --- | --- |
| 现状直接提交 | 形式完整、内容惊艳、但"验证"一栏空白。**很可能三等，运气好二等。** 评委的评语大概是"设计详实，缺少验证"。 |
| 只做 4.0（不依赖设备） | 叙事与合规补齐。**稳二等。** 因为疲劳、界面、反变形的缺口是最容易被挑的。 |
| 做 4.0 + 路线 A（哪怕只有 T1+T3） | 从"纯数字"跨到"有实测"。**冲一等有实质把握。** |
| 做 4.0 + 路线 C | 有实物模型和演示视频，**二等偏上**，且答辩观赏性大幅提升。 |

**核心判断：这个项目最缺的不是钱、不是时间、不是算力，是"一次真实的焊接"。**

哪怕只有一条 100 mm 的焊道、一张宏观截面照片、一条硬度曲线——作品的性质就从"数字推演"变成了"有实验支撑的设计"。官方考核要点四条里的"验证"二字，这才算落了地。

---

## 附：本次诊断新增/引用的关键证据位置

- 官方原文：`competition/original-files/welding/第一届辽宁省大学生材料焊接与铸造工艺设计大赛实施方案.pdf`（PDF 第 2–4 页为固定题与五维度，第 5 页为考核要点）
- 疲劳章节可捡回的源稿：`deliverables/report/technical-report-v2.md` §5
- 承载与热量对比：`studies/COMPETITION-DESIGN/results/robust-selection.json`
- 现有答辩准备：`docs/review/competition-r1-attack-review.md`
- 阶段总账：`project/stage-status.yaml`
- 设备现状：`docs/03-equipment-inventory.md`（全部"待确认"）

---

## 整改执行结果（2026-09-20，RC3）

本诊断 §4.0 的七项「不依赖设备、必须做」的动作已全部落地，并额外修复一处既有缺陷。

| 诊断项 | 落地位置 | 状态 |
| --- | --- | --- |
| A1 叙事重组（结论先行 + 边界收拢） | 摘要重写并新增「条件性达标判断」表；全部未闭合项收拢到 §9.2（L1～L10） | ✅ |
| A2 补回疲劳与力学性能 | 新增 §6.2，含 FAT 63～80 基线、52.17 MPa 名义应力、裕量 1.21、三级试验计划 | ✅ |
| A3 补维度②缺口 | 新增 §2.1（界面策略、稀释率控制、表面预处理、层间与后热、强韧匹配）；工艺卡补七行 | ✅ |
| A4 补维度③缺口 | 新增 §3.2（径向柔顺释放槽的应力释放与热隔离双功能、反变形三级策略及间隙约束反算） | ✅ |
| A5 压缩热模型叙述 | §7 热模型登记为热输入窗口依据并声明不作为位置度证据，删除收敛挣扎过程 | ✅ |
| A6 把"失败"改写成"结论" | §7 与 §6.2：432 例不可分辨 → 结构选择转向热量、可制造性与失效退出路径 | ✅ |
| A7 给 Ø0.05 一个条件性答案 | 摘要「条件性达标判断」+ §6 预算反算热残余上限 0.0102 mm | ✅ |
| 额外：修复边界图缺中文字形 | `studies/ROBUST-BOUNDARY/run.py` 新增 `configure_cjk_font()` 与 `svg.fonttype=path` | ✅ |
| 额外：补维度④的变形精密测量 | 新增 §6.1 | ✅ |
| 额外：正面回应 6P 承载代价 | 新增 §3.1 与「强制切换」表 | ✅ |

**仍待外部条件（不在本次可修复范围）：** §4.1／§4.2／§4.3 三条实物路线（焊接性小试、洁净度对照、疲劳试件、3D 打印动作模型）。这三条决定的是"能否从二等冲到一等"，不是"能否交得出作品"。

**验证结果：** `python -m pytest -q` → 217 passed；`python deliverables/build_submission.py` → 提交门禁 PASS（19 个文件、说明书 22 页、图集 6 页、推荐候选 6P-FAIR_B/4pass）；构建告警由 60 余条降为 0。
