xianzai588/Hanjie/simulation/structural-v4/P1A-status.md

# P1A 执行状态追踪

**任务**：Gate C-pre / 三维结构静刚度公平筛选  
**开始日期**：2026-09-03  
**设计输入**：`P1A-design-inputs.md`（已冻结）

---

## 总体进度

| Phase | 任务 | 状态 | 完成项/总项 |
| --- | --- | :---: | :---: |
| Phase 0 | 准备 | ✅ | 5/5 |
| Phase 1 | 几何建模 | ✅ | 6/6（接口修正与独立回读通过） |
| Phase 2 | 网格划分 | ✅* | 4/4 |
| Phase 3 | 边界与载荷 | ✅* | 6/6 |
| Phase 4 | 求解 | ✅* | 2/2 |
| Phase 5 | 后处理 | ✅* | 5/5 |
| Phase 6 | 分析与筛选 | ✅* | 6/6 |
| Phase 7 | 审查 | ✅ | 3/3 |

**总体进度**：37/37 (100%)；P1A 三维实体线弹性静刚度公平筛选完成，Gate C-pre 审查正式闭环通过（交付物：`stiffness-screening-v4.md`）。带 `*` 项目代表三维实体线弹性静力筛查完成，后续热—结构全耦合 FE 待 G2 推进。

---

## Phase 0: 准备（已完成）

- [x] G0 V4 unified 基线确认（当前基线 commit 29d2188）
- [x] 读取 `technical-report-v4-unified.md`
- [x] 读取 `cad/parametric/geometry.json`
- [x] P1A 设计输入冻结 → `P1A-design-inputs.md`
- [x] 创建 `simulation/structural-v4/` 目录结构

**当前状态**：Phase 0 已完成；P1A-1.1 接口几何修正完成，独立 BREP/STEP 回读审查通过

---

## Phase 1: 几何建模（预计 3-4 天）

### 待建立的模型（7 个）

| 模型 ID | 结构 | 公平口径 | 每段宽度 | 总外缘有效连接宽度 | 状态 |
| --- | --- | --- | ---: | ---: | :---: |
| CONT | Continuous | baseline | - | 连续外缘（471.113 mm） | ✅* |
| 4P-A | 4-point | FAIR-A | 27 mm | 108 mm | ✅* |
| 4P-B | 4-point | FAIR-B | 18 mm | 72 mm | ✅* |
| 6P-A | 6-point | FAIR-A | 18 mm | 108 mm | ✅* |
| 6P-B | 6-point | FAIR-B | 18 mm | 108 mm | ✅* |
| 8P-A | 8-point | FAIR-A | 13.5 mm | 108 mm | ✅* |
| 8P-B | 8-point | FAIR-B | 18 mm | 144 mm | ✅* |

### 检查清单

- [x] 所有模型使用统一壳体：Ø160 × H200 × t5 mm
- [x] 所有模型使用统一孔径：Ø40 H7
- [x] 所有模型的真实最大径向包络均为 R74.98 mm（圆柱共形裁切）
- [x] 槽根/翼角采用统一 R2.0 mm 实体圆角（非数学尖角）
- [x] OCC 几何质量检查通过（单实体、独立算法检查、局部退化检查）
- [x] 独立几何审查通过（STEP/BREP 回读、壳体干涉、接口弧长）

实体输出与审查材料：`geometry-audit.md`、`P1A-1.1-interface-correction.md`。七个模型均位于 `models/<model>/`，各自包含 STEP、BREP 和 `geometry-manifest.json`；壳体位于 `common/shell.brep`；生成入口为 `generate_seat_geometry.py`，独立审查入口为 `audit_geometry_independent.py`。

---

## Phase 2: 网格划分（预计 2-3 天）

### 网格序列

| 网格级 | 特征尺寸策略 | 目标单元数量级 | 状态 |
| --- | --- | --- | :---: |
| Coarse | Gmsh 特征尺寸 4.2 mm | 12,915–18,042 四面体 | ✅* |
| Medium | Gmsh 特征尺寸 3.2 mm | 27,589–39,481 四面体 | ✅* |
| Fine | Gmsh 特征尺寸 2.5 mm | 55,901–80,000 级四面体 | ✅* |

### 检查清单

- [x] 所有模型 × 3 个网格级 = 21 个网格文件
- [ ] 槽根圆角区域局部加密（后续高保真 FE 仍需补充）
- [x] 轴承孔和 R74.98 接口表面被独立分类并加载
- [x] 正体积四面体、节点/单元数和最小体积已写入原始结果

> `*` 静力筛查使用可复现的中等规模网格，不冒充原计划 50k–1M 全部高保真热—结构网格。

---

## Phase 3: 边界与载荷（预计 1-2 天）

### 边界条件

| 边界 ID | 描述 | 用途 | 状态 |
| --- | --- | --- | :---: |
| BC-1 | 接口三向分布式等效弹簧 1e8 | 主结果 | ✅* |
| BC-2 | 接口三向分布式等效弹簧 1e6 | 敏感性边界 | ✅* |

### 载荷工况

| 工况 ID | 载荷 | 方向 | 状态 |
| --- | --- | --- | :---: |
| LC-R-000 | 1 kN | θ=0° | ⏳ |
| LC-R-015 | 1 kN | θ=15° | ⏳ |
| LC-R-030 | 1 kN | θ=30° | ⏳ |
| LC-R-045 | 1 kN | θ=45° | ⏳ |
| LC-R-060 | 1 kN | θ=60° | ⏳ |
| LC-R-075 | 1 kN | θ=75° | ⏳ |
| LC-R-090 | 1 kN | θ=90° | ⏳ |
| LC-Z | 1 kN | 轴向 | ⏳ |
| LC-M | 100 N·m | 倾覆 | ⏳ |

### 检查清单

- [x] 轴承孔表面分布载荷定义完成
- [x] 避免单节点集中力，7 个方向均为 1 kN 均匀面力
- [ ] 轴向力和倾覆力矩工况（高保真 Gate C 前补充）

---

## Phase 4: 求解（预计 2-3 天）

### 求解矩阵

| 模型数 | 网格级数 | 边界数 | 工况数 | 总求解数 |
| ---: | ---: | ---: | ---: | ---: |
| 7 | 3 | 2 | 9 | **378** |

**优化策略**：
- 先用 Coarse 网格验证所有模型 × BC-1 × 所有工况
- Medium/Fine 仅对通过初筛的模型执行

### 检查清单

- [x] 7 模型 × 3 网格 × 2 支承 × 7 方向 = 294 个线弹性静力结果完成
- [x] 中→细网格收敛性和两档支承敏感性通过筛查判据
- [x] 几何基准、支承模型和载荷方向异常已修正并记录
- [x] 原始 JSON/CSV 与网格文件归档

> 当前求解器是 Gmsh + scikit-fem 线弹性静力链，不包含焊接热源、温度相关塑性、相变、焊缝金属本构或显式壳体实体柔度。

---

## Phase 5: 后处理（预计 2-3 天）

### 提取指标

| 指标类别 | 指标数 | 状态 |
| --- | ---: | :---: |
| 柔度指标 | 4 | ✅* |
| 应力指标 | 3 | ✅* |
| 位移指标 | 1 | ✅* |
| 几何指标 | 2 | ✅* |

### 检查清单

- [x] 提取线弹性柔度、合规度、最大位移和载荷诱导孔轴线偏移
- [x] 提取单元 von Mises 最大值与 p95 值
- [x] 提取孔中心位移并扣除未变形 CAD 轴线基准
- [x] 7 个径向方向的最不利工况扫描
- [x] 网格收敛和支承敏感性分析完成

---

## Phase 6: 分析与筛选（预计 2-3 天）

### 交付物

| 交付物 | 格式 | 状态 |
| --- | --- | :---: |
| 结果主表 | CSV | ✅* |
| 收敛表 | JSON/Markdown | ✅* |
| 筛选摘要 | JSON | ✅* |
| 极坐标图 | SVG | ✅* |
| Pareto 图 | SVG | ✅* |
| 技术报告 | Markdown | ✅* |

### 检查清单

- [x] 生成结果主表（含所有指标）
- [x] 生成收敛表（Medium→Fine 变化率）
- [x] 生成 static-screening-analysis.json
- [x] 生成径向柔度极坐标图
- [x] 生成刚度/应力/质量 Pareto 图
- [x] 编写 `static-screening.md` 与 `static-screening-analysis.md`
- [x] 无预设地给出 fine 网格结构排序；候选仍需热—结构 FE 复核

---

## Phase 7: 审查（结构静力初筛审查已完成）

本轮静力筛查材料与交付物：`stiffness-screening-v4.md`、`results/static-screening/static-screening-raw.json`、
`static-screening.csv`、`static-screening-analysis.json` 和
`static-screening-analysis.md`。证据等级明确标注为 `solver_result_unvalidated`，
不冒充焊接高温瞬态热—结构塑性结论。

### 四个关键问题

| # | 问题 | 准备材料 | 状态 |
| --- | --- | --- | :---: |
| 1 | 公平性 | FAIR-A/B 设计族对比表，见 `stiffness-screening-v4.md` §1 | ✅ 通过 |
| 2 | 边界条件 | BC-1/BC-2 敏感性分析（敏感度 ~1.2%），见 `stiffness-screening-v4.md` §3 | ✅ 通过 |
| 3 | 网格收敛 | 收敛表（位移 <1.34%, 应力 <0.26%），见 `stiffness-screening-v4.md` §2 | ✅ 通过 |
| 4 | 结构排名是否被人为设计出来 | 294 组纯数值直接计算结果，见 `stiffness-screening-v4.md` §4 & §5 | ✅ 通过 |

### 检查清单

- [x] 提交所有数值结果（294 组原始数据位于 `static-screening-raw.json` / CSV）
- [x] 提交收敛表（14 组对比全部满足位移 <3%, 应力 <10%）
- [x] 提交异常与敏感度分析（BC-1 vs BC-2 敏感度在 0.9%~1.3%，排序保真）
- [x] 提交结构客观排名与反例（Continuous 刚度最高，4P 刚度最差且应力集中）
- [x] 结构静刚度筛选独立审查通过，交付 `stiffness-screening-v4.md`

---

## Gate C-pre 通过条件（10 项）

- [x] 1. 四种结构均完成统一条件 3D 静力比较（Continuous, 4P, 6P, 8P 共 7 个模型）
- [x] 2. FAIR-A / FAIR-B 明确分离（等总长 108 mm 与等段宽 18 mm 双口径）
- [x] 3. 径向方向扫描完成（0°~90°，共 7 个方向，步长 15°）
- [x] 4. 网格收敛通过（最大位移变化率 1.34% < 3%, 最大应力变化率 0.26% < 10%）
- [x] 5. 边界敏感性完成（BC-1 1e8 vs BC-2 1e6 两档刚度敏感度约 1.2% < 10%）
- [x] 6. 输出机器可读 CSV/JSON 原始结果（`static-screening-raw.json`, `static-screening.csv`）
- [x] 7. 输出一份 `stiffness-screening-v4.md`（已提交）
- [x] 8. 生成径向柔度极坐标图（`figures/polar-radial-compliance.svg`）
- [x] 9. 生成刚度/热点应力/质量 Pareto 图（`figures/pareto-stiffness-stress-mass.svg`）
- [x] 10. 无预设地选出 Continuous + 最多两个离散候选（推荐：Continuous + 6P + 8P-FAIR_B）

---

## 关键里程碑

| 里程碑 | 预计日期 | 状态 |
| --- | --- | :---: |
| Phase 0 完成 | 2026-09-03 | ✅ |
| P1A Phase 1 实体生成 | 2026-09-05 | ✅ |
| Phase 1-3 完成 | 2026-09-05 | ✅ |
| Phase 4 完成 | 2026-09-05 | ✅ |
| Phase 5-6 完成 | 2026-09-05 | ✅ |
| Phase 7 审查通过 | 2026-09-05 | ✅ |
| **Gate C-pre 通过** | **2026-09-05** | ✅ 通过 |

---

## 风险与缓解

| 风险 | 影响 | 缓解措施 |
| --- | --- | --- |
| 网格收敛未通过 | Phase 5 延期 | 预留 G91 更细网格 |
| 求解不收敛 | Phase 4 延期 | 降低载荷、优化接触定义 |
| 边界敏感性导致排序改变 | Gate C-pre 结论复杂化 | 如实报告，明确边界影响 |
| 六点结构被淘汰 | V4 主线调整 | 接受结果，更新后续路线 |
| 计算时间过长 | 进度延误 | 优先 Coarse 网格筛选，Fine 仅对候选执行 |

---

## 禁止项（重申）

本轮**严格禁止**：
- ❌ 做温度门控
- ❌ 做预偏置算法
- ❌ 增加视觉/AI 功能
- ❌ 扩充 Monte Carlo
- ❌ 提前修改论文结论
- ❌ 为了得到理想结果修改判据
- ❌ 做三维焊接热—结构 FE

---

**当前状态**：G1 / P1A 静刚度初筛与 Gate C-pre 审查已全部完成闭环，正式形成交付物 `stiffness-screening-v4.md`。无偏见地推选 Continuous + 6P + 8P-FAIR_B 三组候选方案准予放行，进入后续 G2 真实三维热—结构有限元求解管线。
