xianzai588/Hanjie/simulation/structural-v4/geometry-audit.md

# P1A Phase 1：实体几何审查材料

**状态**：P1A-1.1 接口几何修正完成；独立几何审查通过；允许进入 Phase 2 网格准备

**审查证据**：`geometry-independent-audit.json`

**独立复核命令**：

```powershell
python simulation/structural-v4/audit_geometry_independent.py
```

## 本轮修正的几何语义

- `R_seat,max = 74.98 mm` 是座体所有实体点的真实最大径向包络，不是平面翼端的 x 坐标。
- 离散翼由平面圆角母体与 `R=74.98 mm` 圆柱求交，最终外缘为圆柱共形接口。
- FAIR 宽度统一定义为 `R74.98` 圆柱焊接接口弧长；FAIR-A 固定总目标 108 mm，FAIR-B 固定每段目标 18 mm。
- `cad_measured_total_weld_length_mm` 和 `cad_measured_weld_interface_area_mm2` 均由导出实体的 OCC 面重新测量，不再把目标宽度复制为“实际焊缝”。
- 离散座体槽根最小径向韧带按 `R39-R20=19 mm` 计算；连续座体孔壁为 21 mm。
- `common/shell.brep` 是独立的 Q235B `Ø160 × H200 × t5 mm` 壳体审查实体。

## 七个实体与独立回读结果

| 模型 | CAD 实测焊接接口（mm） | 接口面积（mm²） | 壳体最小间隙（mm） | 最大穿透（mm） | 座体最小韧带（mm） | 结论 |
| --- | ---: | ---: | ---: | ---: | ---: | :---: |
| Continuous | 471.113 | 5653.359 | 0.020 | 0 | 21 | PASS |
| 4P-FAIR-A | 108.000 | 1295.760 | 0.020 | 0 | 19 | PASS |
| 4P-FAIR-B | 72.000 | 863.840 | 0.020 | 0 | 19 | PASS |
| 6P-FAIR-A | 108.000 | 1295.760 | 0.020 | 0 | 19 | PASS |
| 6P-FAIR-B | 108.000 | 1295.760 | 0.020 | 0 | 19 | PASS |
| 8P-FAIR-A | 108.000 | 1295.760 | 0.020 | 0 | 19 | PASS |
| 8P-FAIR-B | 144.000 | 1727.680 | 0.020 | 0 | 19 | PASS |

接口面积按 `弧长 × 座体厚度 12 mm` 从 OCC 圆柱面读取。审查脚本同时对每个模型重新读取 STEP 与 BREP，并检查两者体积一致。

## 独立审查项目

| 项目 | 独立判据 | 结果 |
| --- | --- | :---: |
| BREP 有效性 | `BRepCheck_Analyzer` 回读有效 | PASS |
| 单一实体 | 回读后 `solid_count = 1` | PASS |
| 自干涉/算法检查 | 独立 `BRepAlgoAPI_Check` | PASS |
| STEP/BREP 一致性 | 体积相对差 `<1e-8` | PASS |
| FAIR 目标一致性 | OCC 接口弧长与目标差 `≤1e-5 mm` | PASS |
| 壳体实体干涉 | `seat ∩ shell` 体积为 0 | PASS |
| 内腔穿透 | `seat \ shell_inner_void` 体积为 0 | PASS |
| 配合间隙 | `seat-shell` 最小距离约 0.020 mm | PASS |
| 局部退化 | 最小面面积、最小边长均为正 | PASS |
| 槽根韧带 | 独立重算最小值为 19 mm（离散） | PASS |

## 6P-A / 6P-B 几何 oracle

两者都满足每段接口弧长 18 mm、总接口弧长 108 mm；独立回读体积均为 `95079.427 mm³`，质量均为 `0.684572 kg`。这保留了公平规则的生成 oracle：两种写法对 6P 拓扑应产生同一实体，而不是把它们人为当成两个不同设计。

## 结论与边界

P1A-1.1 的五个退回项已闭合：真实径向包络、圆柱共形接口、CAD 实测焊接接口、独立几何质量检查、真实最小韧带/壳体干涉。当前可以进入 Phase 2 的网格和边界定义准备。

本审查不证明焊缝冶金质量、网格收敛、夹具刚度、热—结构响应或最终结构排名。由于座体实体已改变，任何依赖旧几何的结构结果都必须标记为历史结果，Phase 2 需要使用本轮新 BREP 重新计算。
