xianzai588/Hanjie/simulation/structural-v4/P1A-0.5-geometry-freeze.md

# P1A-0.5 几何定义冻结

**日期**：2026-09-03  
**状态**：冻结；接口实现已由 P1A-1.1 完成闭环

---

## 关键修正

### 1. FAIR-A 定义修正

**修正前（错误）**：
> 固定总连接宽度 108 mm → 相同材料用量

**问题**：
- 即使外缘总宽度 $\sum w_i = 108$ mm 保持一致
- 4P/6P/8P 的翼根宽度、翼侧边形状、槽总面积、实体体积、柔顺路径、焊接界面总长度仍可能不同
- **"固定总宽度"只能叫几何连接尺度公平，不能叫材料用量公平**

**修正后（正确）**：
> **FAIR-A：固定总外缘有效连接宽度 108 mm**
> 
> 回答：在相同总外缘连接尺度下，4/6/8 的拓扑分布差异如何影响结构性能。
> 
> **注**：实际体积 V 和质量 m 将作为结果输出，不假设它们相等。

### 2. FAIR-C 登记（暂不建立）

**定义**：
> **FAIR-C：等体积/等质量拓扑比较**
> 
> 调整 4P/6P/8P 使 $V_{4P} \approx V_{6P} \approx V_{8P}$
> 
> 回答：相同材料投入下，哪个拓扑效率更高？

**实施条件**：
- 仅当 FAIR-A/B 排名冲突时
- 或结构质量差异显著时（如 $m_{8P} > 1.5 m_{4P}$）
- 追加 FAIR-C 作为区分实验

**当前决策**：暂不建立，避免 7 个模型膨胀成 10+ 个

---

## 统一参数化几何规则

### 核心原则

**禁止**：手工独立绘制 7 个模型  
**必须**：所有模型由同一套代码和参数规则生成

**目标**：
> 评委问："4点和8点是不是人为画得不一样？"
> 
> 回答："除拓扑参数 N 和公平族定义外，几何由同一生成器产生。"

### 统一参数表

| 参数 | 值 | 来源 |
| --- | --- | --- |
| `shell_outer_diameter` | 160 mm | 题面固定 |
| `shell_height` | 200 mm | 题面固定 |
| `shell_thickness` | 5 mm | 题面固定 |
| `bearing_bore_diameter` | Ø40.000 mm | 名义尺寸（FE用） |
| `seat_thickness` | 12 mm | V4 设计 |
| `seat_outer_radius` | 74.98 mm | V4 设计 |
| `seat_core_diameter` | 82 mm | V4 设计 |
| `slot_width` | 4 mm | V4 设计 |
| `slot_root_radius` | **2.0 mm** | 统一公共值（所有离散拓扑） |

**关键说明**：
- **Ø40 H7** 仅作为制造设计要求
- P1A 有限元几何统一使用名义 **Ø40.000 mm**
- 不做公差极值模型（+0.025 / +0.000）

---

## Wing Width 几何定义

### 必须明确的问题

**Wing width / effective connection width 是哪个几何量？**

选项：
- 外圆处弦长
- 外圆处切向宽度
- 圆弧长度
- 整个翼恒定宽度

**必须选一个，所有 FAIR-A/B 采用完全相同定义。**

### 推荐定义

**定义**：
> Wing width = R74.98 mm 圆柱焊接接口上的弧长

**禁止**：
- 4P 用弦长
- 6P 用切向宽度
- 8P 用圆弧长度

**原因**：定义不一致会导致 FAIR-A/B 断言失效

---

## 槽根圆角冻结

### 统一要求

**所有 4P/6P/8P 使用完全相同槽根圆角半径**

### 确定流程

1. 先检查 **R2.0 mm** 是否对所有拓扑均几何可行
2. 若不可行，选择所有拓扑均可实现的统一最大公共值（如 R1.5 mm）
3. **不得为了降低某个方案应力而单独调整圆角**
4. 记录最终选择理由

### 几何约束

圆角必须满足：
- 不与 Ø82 核心区穿透
- 不与 4 mm 槽几何冲突
- 不产生零厚度/极窄区域

### 后续敏感性

**原则**：4/6/8 完全一致

**将来可单独做**：
$$
R_f = 1.0,\ 2.0,\ 3.0 \text{ mm}
$$
的局部敏感性研究

---

## Continuous 基线定义

### 正确定义

**Continuous ≠ 一整块 Ø149.96 × 12 mm 实心圆盘**

**Continuous = 传统连续环形轴承座几何基线**

### 必须记录

- $V_{\text{Continuous}}$（体积）
- $m_{\text{Continuous}}$（质量）

### 评价方式

**不应该说**：
> "柔顺方案刚度不如 Continuous，因此差。"

**应该分析**：
$$
\frac{K}{m} \quad \text{（比刚度）}
$$

以及焊接变形收益。

**原因**：
- Continuous 本来就是刚度上界候选
- 不应期待离散结构在纯静刚度上把它打败
- 真正研究的是：$\text{焊接变形} \leftrightarrow \text{服役刚度}$ 的权衡

---

## 几何生成器架构

### 推荐结构

```python
def generate_seat(N, family, parameters):
    """
    统一参数化座体生成器
    
    Parameters:
    -----------
    N : int
        连接点数量（4/6/8）或 0（Continuous）
    family : str
        公平族（'FAIR_A' / 'FAIR_B' / 'Continuous'）
    parameters : dict
        统一几何参数
    
    Returns:
    --------
    solid : CAD solid
    manifest : dict
        几何清单
    """
    pass
```

### 生成逻辑

```
中心刚性区 Ø82
    ↓
按 N 等分中心角
    ↓
每个翼拥有参数化中心角
    ↓
从核心区向外缘延伸
    ↓
两翼之间切除径向槽
    ↓
槽根统一圆角 R_f
    ↓
与 R74.98 圆柱求交，形成共形外缘接口
```

---

## Geometry Manifest 输出

### 每个模型自动输出

```json
{
  "model_id": "6P-FAIR-A",
  "family": "FAIR_A",
  "layout": "6P",
  "N": 6,
  "shell": {
    "outer_diameter_mm": 160,
    "height_mm": 200,
    "thickness_mm": 5
  },
  "seat": {
    "bore_nominal_diameter_mm": 40.000,
    "thickness_mm": 12,
    "outer_radius_mm": 74.98,
    "core_diameter_mm": 82,
    "slot_width_mm": 4,
    "slot_root_radius_mm": 2.0,
    "fair_target_width_each_mm": 18.0,
    "fair_target_total_width_mm": 108.0
  },
  "geometry": {
    "planform_area_mm2": null,
    "solid_volume_mm3": null,
    "calculated_mass_kg": null
  },
  "manufacturing": {
    "slot_count": 6,
    "weld_segment_count": 6,
    "nominal_total_weld_length_mm": null
  },
  "generation": {
    "generator_version": "1.0",
    "timestamp": "2026-09-03T19:00:00Z",
    "rule": "unified_parametric"
  }
}
```

### 用途

后续 Pareto 图可直接使用：
$$
C_r,\quad \sigma,\quad m,\quad N_{\text{weld}}
$$

---

## 自动几何检查

### 必须检查项

| 检查项 | 判据 |
| --- | --- |
| Solid 有效 | `is_valid = True` |
| Boolean 成功 | 无异常 |
| 无自交 | 拓扑检查 |
| 无零/负体积 | $V > 0$ |
| 无重叠 | 实体唯一 |
| 无零厚度区域 | 最小厚度 > 阈值 |
| 坐标系一致 | 原点/Z轴对齐 |

### FAIR-A 断言

```python
assert abs(sum(effective_widths) - 108.0) < 1e-6, \
    "FAIR-A total width must be 108 mm"
```

### FAIR-B 断言

```python
for w in effective_widths:
    assert abs(w - 18.0) < 1e-6, \
        "FAIR-B each width must be 18 mm"
```

**禁止仅靠人工查看图判断。**

---

## Phase 1 验收标准

### 必须满足（10 项）

- [x] 1. 7 个三维实体全部生成
- [x] 2. 所有几何自动检查通过
- [x] 3. FAIR-A 断言通过（总外缘有效连接宽度 = 108 mm）
- [x] 4. FAIR-B 断言通过（每段外缘有效连接宽度 = 18 mm）
- [x] 5. 参数 manifest 完整
- [x] 6. 质量/体积已计算
- [x] 7. 槽根圆角统一为 R2.0 mm
- [x] 8. 生成规则可重复
- [x] 9. 无人为独立修模
- [x] 10. Wing width 定义一致

此外，P1A-1.1 已补充并通过：导出 BREP/STEP 独立回读、座体—壳体零穿透、CAD 实测焊接接口弧长、真实槽根最小韧带和 6P-A/B 同构 oracle。Phase 2 可以使用新实体开始，但必须重新生成网格和结构结果。

**只有上述条件全部满足，才进入 Phase 2 网格。**

上述 10 项是生成器与实体交付验收，已全部满足；独立几何审查已作为 P1A-1.1 的单独暂停门完成并通过。

### 若几何冲突

**停止并报告**，不得私下修改该方案以使其通过。

---

## 质量和材料体积

### 不假设相等

**FAIR-A 不假设材料用量相同**

直接输出各结构真实：
- $V$ (mm³)
- $m$ (kg)

### 后续评价指标

将增加：
- 比刚度：$K / m$
- 刚度质量比：$C_r \cdot m$

---

## Git 提交要求

### 从本次开始禁止

```text
❌ Co-Authored-By: Claude Opus 4.8 <noreply@anthropic.com>
❌ Co-Authored-By: Codex
❌ Generated-by: ...
```

### 不需要

- 不需要改写过去 Git 历史
- 不需要 force-push
- 从下一次提交开始执行

---

**P1A-0.5 状态**：几何定义与七个实体生成完成；P1A-1.1 独立几何审查已通过，允许进入 Phase 2 网格/结构筛选。
