xianzai588/Hanjie/simulation/structural-v4/P1A-1.1-interface-correction.md

# P1A-1.1 接口几何修正完成记录

**日期**：2026-09-05

**状态**：完成；独立回读审查 PASS

## 修正内容

1. 将 `R74.98 mm` 从平面端点坐标改为真实圆柱径向包络，并在 OCC 中执行实体与圆柱的交集裁切。
2. 以圆柱接口弧长为公平宽度定义，通过统一反求过程得到圆角翼母体宽度，避免弦长、平面宽度和焊缝长度混用。
3. 从最终实体外圆柱面按 `OCC 面积 / 12 mm 厚度` 提取实际接口弧长、面积、段数和角度记录。
4. 将壳体实体独立导出到 `common/shell.brep`，对座体—壳体公共体积、内腔外穿体积和最小距离进行审查。
5. 将 `BRepCheck_Analyzer`、`BRepAlgoAPI_Check`、单实体计数、最小面/边尺度、局部韧带和壳体干涉拆成独立字段。
6. 补充 6P-A/B 同构 oracle，防止同一公平规则被误判为两个不同几何。

## 允许发布的几何主张

- 七个导出实体均可由同一参数化入口重建。
- 所有座体点的最大径向包络为 `R74.98 mm`；与壳体内壁 `R75.00 mm` 的名义间隙为 `0.020 mm`。
- FAIR-A 的 CAD 实测接口总弧长为 `108.000 mm`；FAIR-B 的每段 CAD 实测接口弧长为 `18.000 mm`。
- 座体—壳体公共体积和座体穿出壳体内腔的体积均为 0。
- 离散座体真实槽根方向最小径向韧带为 `19.000 mm`。

这些主张仅限几何接口和导出回读层面，不延伸为焊接质量或结构性能结论。
