xianzai588/Hanjie/docs/research/references.md

# 文献与标准清单

> 新增文献按格式追加；重点结论摘录到对应研究文档并标注编号。

| 编号 | 类型 | 标题/标准号 | 来源 | 关键结论 | 关联 |
| --- | --- | --- | --- | --- | --- |
| R001 | 标准 | GB/T 1348 球墨铸铁件 | | QT450-10 成分/性能依据 | WP1 |
| R002 | 标准 | GB/T 700 碳素结构钢 | | Q235B 成分/性能依据 | WP1 |
| R003 | 标准 | GB/T 10044 铸铁焊条及焊丝 | | 铸铁焊材选型依据 | WP2 |
| | 文献 | 球铁/钢异种材料焊接 | | | WP1 |
| | 文献 | 铸铁焊接白口控制 | | | WP1 |
| | 文献 | 薄壁圆筒焊接变形控制 | | | WP3/WP4 |
| R004 | 文献 | An Analysis of the Weldability of Ductile Cast Iron Using Inconel 625 for the Root Weld and Electrodes Coated in 97.6% Nickel for the Filler Welds | Cárcel-Carrasco et al., *Metals* 2016, 6, 283. [DOI](https://doi.org/10.3390/met6110283) | TIG 根部/镍基填充、预热与冷却会影响球铁界面组织；仍有硬脆区风险 | WP1/WP2 |
| R005 | 文献 | Effect of welding parameters on microstructure and mechanical properties of dissimilar AISI 304/ductile cast iron fusion welded joints | El-Shennawy et al., *Scientific Reports* 2024, 14, 19827. [DOI](https://doi.org/10.1038/s41598-024-70050-0) | ENiFe-CI 等填充与焊接条件影响界面组织；对象不是 Q235B/QT450-10 | WP1/WP2 |
| R006 | 文献 | Mechanical and microstructural analysis in the welding of ductile cast iron by TIG procedure, with different filler materials and air cooling | Martínez Alcón et al., *Revista de Metalurgia* 2021, 57(2). [DOI](https://doi.org/10.3989/revmetalm.194) | TIG、填充材料与热处理/冷却改变组织和力学性能；用于定义小试变量 | WP1/WP2 |
