xianzai588/Hanjie/docs/p0.5-cleaning-report.md

# P0.5 清洗完成报告

**日期**：2026-09-03 晚间  
**基于**：P0.5 细节审查反馈

---

## 修正的 5 个问题 ✅

### 1. Git 提交数量统计错误 ✅

**问题**：
- 最终总结说"8个commit"，实际列了9个
- 中间文档说"7个commit"，实际列了8个
- `eb7d144` 本身就是第9个提交

**修正**：统一为 **9个（含最终总结提交）**

**已修改文件**：
- 本次清洗报告中明确统计

---

### 2. CLAIM-001/002 的 verified 写高了 ✅

**问题**：只有文献支持，不能写 `publication_status: verified`

**修正**：
```yaml
status: literature_supported
confidence: high
publication_status: supported
allowed_wording: "文献与相近材料体系研究支持该工艺路线具有可行性"
notes: "仅文献支持，需本项目实物验证"
```

**允许写**："文献与相近材料体系研究支持该工艺路线具有可行性"  
**不能写**："已验证本项目 QT450-10/Q235B 接头可可靠焊接"

**已修改文件**：`evidence/claims.yaml`

---

### 3. 官方条件不该叫 design_assumption ✅

**问题**：`CLAIM-010/011` 来源是 `OFFICIAL-SPEC`，却写 `status: design_assumption`

**修正**：
```yaml
status: official_requirement
confidence: certain
publication_status: official
```

**已修改文件**：`evidence/claims.yaml`

---

### 4. CLAIM-017 偷偷提前了一步 ✅

**问题**：允许措辞"候选结构之一，经参数化优化得到"，但 Pareto 本身还是 `planned`，不能说"经优化得到"

**修正**：
```yaml
allowed_wording: "六点低拘束结构作为候选方案之一，待三维热—结构公平比较及参数化优化进一步裁决"
notes: "不能说'经参数化优化得到'，因为 Pareto 本身还是 planned"
```

**已修改文件**：`evidence/claims.yaml`

---

### 5. CLAIM-060 的"这不是硬伤"应该删掉 ✅

**问题**：0.035 > 0.025 仍然是预算缺口，"这不是硬伤"不够严谨

**修正**：
```yaml
allowed_wording: "误差预算口径已修正（装配链/自动化链分离），但当前仍存在 0.010 mm 径向预算缺口，是 V4 尚待解决的设计约束"
notes: "口径错误已修正，但预算缺口仍存在。四个创新点的顶层约束。"
```

**已修改文件**：`evidence/claims.yaml`

---

## publication_status 定义更新 ✅

新增分类：
- `official`: 官方要求
- `literature_supported`: 文献支持的可行性（无本项目实测）

更新定义：
- `verified`: 已验证，可直接作为结论（**需本项目实测数据**）
- `supported`: 有文献支持，可引用（**文献证据**）

---

## 关于 Co-Authored-By

**问题**：`eb7d144` 等提交包含 `Co-Authored-By: Claude Opus 4.8 <noreply@anthropic.com>`

**建议**：
- ✅ 不建议 force-push 改历史（协作风险）
- ✅ 立即固定开发指令：提交时不得添加任何 AI 工具署名

---

## Git 提交记录（今日完整统计）

```
eb7d144 [V4-FINAL] 今日工作最终总结
dc7dd61 [V4-P0] 添加关键修正说明文档
c8e3f2c [V4-P0] 关键修正：H7/h6表述+误差预算未闭合+证据清单
0260139 [V4-DOC] 今日工作总结
c871e16 [V4-DOC] 添加执行摘要
6689dde [V4-DOC] 对深度评审意见的完整回应
39edc0d [V4-MAINLINE] 重构项目核心叙事
d4b270b [V3-DOC] 添加进度报告与刚度分析框架
3754ded [V3-FIX-P0] 修复接头几何、夹具定位与误差预算三大硬伤
```

**今日 Git 提交总数：9 个（含最终总结提交）** ✅

---

## 评分不上调 ✅

**认同评审判断**：

| 维度 | 评分 | 说明 |
| --- | ---: | --- |
| 项目组织与研究成熟度 | **约 85** | 研究纪律、架构质量提升 |
| **当前实际提交竞争力** | **约 81-83** | 未产生新的物理/数值核心证据 |

**下一次值得重新评分的节点**：
> FE3D-BASE 通过网格收敛 + 热场合理性 + 边界检查之后

**不是**：
- ❌ `technical-report-v4.md` 建好
- ❌ 继续加功能
- ❌ 跑出"结果"但不可信

---

## 下一步执行顺序（确认）

### 阶段 1：technical-report-v4.md 骨架（本周）⏳

**不是写"最终稿"，而是"活的竞争稿"**

每个核心结果章节明确分三种状态：
```
[已有结果]  - ROM 初筛、2D FE、冲突
[当前边界]  - 六点只能作为候选、2D FE 未收敛
[V4待验证]  - 3D Base/4P/6P/8P、Pareto
```

**新论文结构（8 章）**：
1. 问题分析与设计目标
2. 异种材料焊接性与工艺选择
3. 参数化接头与夹具设计
4. 热—结构协同模型
5. 结构与工艺优化结果
6. 自适应跳焊与补偿
7. 自动化与质量闭环
8. 可靠性与证据边界

**关键原则**：
- ✅ 以后**替换证据，不用重新改逻辑**
- ✅ 今天就可以开始写
- ✅ 每章标明"已有/边界/待验证"

---

### 阶段 2：3D FE Baseline（9月5-10日）⏳

**只完成一个模型**：
- Continuous（连续座体）
- Rigid fixture（刚性夹具）
- S3 顺序
- Baseline 工艺参数

**必须交付**：
- ✅ 真正 3D 壳体 + 轴承座
- ✅ 温度相关材料参数
- ✅ 移动热源（Goldak/高斯）
- ✅ 热-弹塑性顺序耦合
- ✅ 完全冷却后松夹
- ✅ 拟合 Ø40 孔轴线 → 位置度
- ✅ **网格收敛性验证（变化 < 5%）**

**数值可信度 Gate**：
- ✅ 热场合理性（峰值温度、HAZ 尺度）
- ✅ 边界条件清晰
- ✅ 材料参数有依据

**Gate B**：模型自己先站得住

**关键原则**：
> **不要为了赶 9 月 10 日，就让 3D FE"跑出结果"而没有跑可信度。**
> 
> 如果 9 月 10 日得到的是一个不收敛、边界不清楚、材料参数随便填的 3D 模型，它不比现在二维模型高级。

---

### 阶段 3：公平结构比较（9月10-14日）⏳

统一边界，只改变结构变量：
- Continuous（Baseline）
- 4-point
- 6-point
- 8-point

**Gate C**：六点到底是不是值得继续

**关键**：如果六点输，换方案，不要保六点。

---

### 阶段 4：自适应跳焊（9月14-18日）⏳

对比方案：
- S1 顺序
- S2 对称
- S3 固定跳焊
- Thermal Gate（温度阈值门控）
- Dynamic（预测式动态顺序）

**Gate D**：必须比固定 baseline 有可解释改善

---

### 阶段 5：Pareto 优化（9月18-22日）⏳

设计变量：N, L_w, W_s, K_f, q  
目标：min(P, σ_hotspot, Q, t_cycle)

**这时才能说**："经参数化优化得到"

---

### 阶段 6：反变形补偿（9月22-26日）⏳

用已经可信的模型测试：
- 不补偿
- 静态补偿
- 根据初始装配偏差自适应补偿

---

### 阶段 7：最终论文（9月底）⏳

- 视觉和文字压缩
- 图表优化
- 摘要重写
- 从"V4 规划稿"变成"V4 结果稿"

---

## P0.5 清洗完成 ✅

**修正内容**：
- ✅ Git 提交数量统计：9 个
- ✅ CLAIM-001/002：literature_supported
- ✅ CLAIM-010/011：official_requirement
- ✅ CLAIM-017：不能说"经优化得到"
- ✅ CLAIM-060：删除"这不是硬伤"

**下一步**：
- ⏳ 提交 P0.5 清洗
- ⏳ 建立 technical-report-v4.md 骨架
- ⏳ 进入 3D FE Baseline 阶段

**核心原则（重申）**：
- ✅ 冻结 V4 主张
- ✅ 只有得到结果后，才允许更新论文中的创新结论
- ✅ 不要为了赶进度而牺牲可信度
- ✅ 如果六点输，换方案，不要保六点

---

**状态**：P0.5 清洗完成，准备进入 technical-report-v4.md 骨架建立阶段。
