xianzai588/Hanjie/deliverables/report/adversarial-review-v2.md

# Technical Report V2 - 恶意评委式技术审查

## 审查结论

本轮没有发现需要推翻主线的 P0 技术硬伤。报告最重要的防守点已经具备：基准不自引用、FE 不冒充高保真焊接仿真、蒙特卡洛不冒充独立证据、视觉返回率不冒充工程通过、参赛提交与制造放行分层。

## 逐条攻击记录

| 评委攻击 | 证据边界是否回答 | 风险 | 审查意见 |
| --- | --- | --- | --- |
| 为什么选 TIG？ | 是 | P1 | 说明了热输入、路径、分段和过程记录可控；同时承认设备与小试仍待评定。 |
| ERNiFe-CI 对本题有直接证据吗？ | 是 | P1 | 明确写成镍铁基候选，直接有效性由真实接头金相、硬度、裂纹/NDT 裁决；没有把相近对象文献当成本题验证。 |
| 为什么 6 点，不是 4 点/8 点？ | 是 | P1 | 解释为热输入、焊段数量和模型内裕度折中，不宣称唯一数学最优；后续答辩应展示 4/8 点对照输入。 |
| 为什么降阶和 FE 相反？ | 是 | P0 已关闭 | 明确归因于结构连接、夹具边界和材料表达不同，并把冲突保留为验证优先级，而非删除不利结果。 |
| FE 最高只有 462-562 °C，有什么意义？ | 是 | P0 已关闭 | 明确它没有熔池、熔合、焊缝激活、温度相关塑性、相变、三维接触等，只承担独立二维结构反例检查。 |
| 0.025 mm 预算为什么这样分？ | 是 | P0 已关闭 | 给出 6 项线性最坏情况分配，并明确它是设计分配，不是测量不确定度，也不是三维 GD&T 轴线误差的严格等价分解。 |
| 透视条件误差约 10 mm，怎么还能叫自动化？ | 是 | P0 已关闭 | 检测返回率和工程通过被分开；perspective 的 P95 超门限，系统应拒绝结果或转人工复核。 |
| 异常检测 100% 是不是自己出题自己答？ | 是 | P0 已关闭 | 明确是当前注入模式上的规则回归，不代表真实现场泛化；真实焊机数据需重新标定阈值、误报率和延迟。 |
| 没有实物，凭什么参赛？ | 基本是 | P1 | PDF 明确按数字工程设计方案提交，并把实物验证缺口列出；最终提交包应保留官方命题附件的准确文件名/编号。 |
| 洁净度怎么证明？ | 是 | P0 已关闭 | 明确数字图、仿真和无异常事件不能替代焊后内窥/目视与追溯放行记录。 |
| 最终到底推荐刚性还是柔顺？ | 已修正 | P1 | 当前证据只能支持 S3 作为继续验证的候选，同时保留刚性基准；PDF V2 已把“最终推荐”改成“当前候选路线”，避免过度定案。 |

## 只修关键缺陷后的答辩口径

一句话总答：

> 当前数字证据把自动 TIG + 镍基填充、六点短焊段和 S3 排为继续验证候选；降阶模型支持柔顺结构，但独立二维代理 FE 给出反例，所以最终结构不在没有三维/物理证据时提前定案。

## 不应在最终稿中新增的主张

- 不把 `P_FE` 写成真实焊后位置度或 CMM 结果。
- 不把 1000 次蒙特卡洛写成真实失效概率或第三种独立验证。
- 不把视觉检测返回率写成定位精度或工程通过率。
- 不把数字误差预算写成已测得的不确定度。
- 不把候选 WPS、候选填充牌号或数字图纸写成制造放行文件。
