xianzai588/Hanjie/deliverables/report/blind-review-v2.md

# Technical Report V2 - 脱离仓库上下文的三分钟盲审

## 审查边界

审查者只获得 `technical-report-v2.pdf`，不打开 GitHub、仓库源代码、结果 JSON 或工程图目录。目标不是复核每一个计算，而是判断首次阅读者能否在 3 分钟内回答：题目是什么、方案是什么、真正做了什么、哪些没有做。

## 结论

**盲审结论：通过，具备参赛 PDF 的基本自洽性；“最终推荐”歧义已收紧为“当前候选路线”。**

PDF 首屏给出目标、材料组合、位置度限值和证据链；第 1 章给出阅读路径；第 6-8 章明确了降阶模型、二维代理 FE、蒙特卡洛和视觉工程门的证据边界；第 14-15 章直接回答关键质疑并区分参赛提交与制造放行。因此读者不需要访问仓库才能理解作品主线。

## 三分钟阅读轨迹

| 时间 | 读者应当得到的答案 | PDF 位置 | 判定 |
| --- | --- | --- | --- |
| 0-30 s | 这是 QT450-10 / Q235B 异种材料焊接；目标是焊后 Ø40 孔轴线位置度不超过 Ø0.05 mm，同时保证内腔洁净。 | 封面、表 1 | PASS |
| 30-90 s | 当前路线是自动 TIG + 镍基填充、六点短焊段、S3 和可释放夹具，但仍属于候选路线。 | 封面、表 5、表 16 | PASS，措辞需继续避免唯一最优暗示 |
| 90-150 s | 项目实际完成了降阶筛选、二维热-结构代理交叉检查、共同输入扰动、视觉 P95 工程门和追溯/验证接口。 | 图 2-5、表 7-15 | PASS |
| 150-180 s | 降阶与 FE 排序相反；FE 未达到熔点，因此不是完整焊接预测；困难视觉有明确 FAIL；没有实物放行证据。 | 第 6-8、14-15 章 | PASS |

## 独立读者复述测试

- **题目是什么：** 两种材料连接，同时约束焊后位置度和内腔洁净度。
- **主张是什么：** 提出一条可继续验证的自动化 TIG 候选路线，并用数字模型组织证据。
- **真正做了什么：** 生成参数化结构/夹具、降阶结果、二维代理 FE 反例、蒙特卡洛传播、视觉工程门和追溯接口。
- **没有做什么：** 没有熔池级焊接 FE、WPS/PQR、真实焊接、焊后 CMM、金相/硬度/NDT 或实物洁净度放行。

## 盲审发现并已完成的唯一成稿级修订

封面和结尾如果使用“最终推荐”，容易被快速阅读者理解为“已完成最终选型”。PDF V2 已统一改为：

> 当前候选路线：自动 TIG + 镍基填充、六点短焊段和 S3；连续座体/刚性夹具继续作为 FE 反例基准，最终结构需由更高等级证据裁决。

该修订不改变任何数值结果，只消除决策状态歧义。
