xianzai588/Hanjie/simulation/structural-v4/results/joint-load-basis/joint-design-basis.md

# 条件性接头承载筛查

> 题面没有真实整机载荷或载荷谱；以下为参考包络影响系数，不是服役安全认证。

| 布局 | 有效焊长 (mm) | 焊脚 (mm) | 参考包络角点所需许用 (MPa) | 单道净热输入 (kJ) | 四道净热输入 (kJ) |
| --- | ---: | ---: | ---: | ---: | ---: |
| Continuous | 471.113 | 1.737 | 24.105 | 155.467 | 621.869 |
| Continuous | 471.113 | 2.000 | 20.931 | 155.467 | 621.869 |
| Continuous | 471.113 | 2.500 | 16.745 | 155.467 | 621.869 |
| Continuous | 471.113 | 3.000 | 13.954 | 155.467 | 621.869 |
| Continuous | 471.113 | 3.500 | 11.960 | 155.467 | 621.869 |
| 6P-FAIR_B | 108.000 | 1.737 | 105.149 | 35.640 | 142.560 |
| 6P-FAIR_B | 108.000 | 2.000 | 91.303 | 35.640 | 142.560 |
| 6P-FAIR_B | 108.000 | 2.500 | 73.042 | 35.640 | 142.560 |
| 6P-FAIR_B | 108.000 | 3.000 | 60.869 | 35.640 | 142.560 |
| 6P-FAIR_B | 108.000 | 3.500 | 52.173 | 35.640 | 142.560 |
| 8P-FAIR_B | 144.000 | 1.737 | 78.862 | 47.520 | 190.080 |
| 8P-FAIR_B | 144.000 | 2.000 | 68.477 | 47.520 | 190.080 |
| 8P-FAIR_B | 144.000 | 2.500 | 54.782 | 47.520 | 190.080 |
| 8P-FAIR_B | 144.000 | 3.000 | 45.652 | 47.520 | 190.080 |
| 8P-FAIR_B | 144.000 | 3.500 | 39.130 | 47.520 | 190.080 |

## 结论

参考包络下3.5 mm可降低条件应力并增加裕量，但题面载荷、真实焊缝许用和疲劳谱缺失，不能证明它是唯一必要尺寸。
容量与焊脚近似成正比；在同一焊长下，其力/力矩容量约为3.5 mm情景的49.6%。
保留为待真实载荷与成形验证的上界候选，不升级为推荐工艺。

既有 1000 N 径向静力筛查仅作为座体孔轴位移影响系数引用；它没有显式焊缝，不能给 3.5 mm 焊脚背书。
疲劳只登记焊趾、焊根、离散焊段端部和翼根圆角为风险位置；没有载荷谱时不计算或宣称寿命。

## 6P 焊脚—分量敏感曲线

| 焊脚 (mm) | 径向 (MPa) | 轴向 (MPa) | 合力 (MPa) | 倾覆 (MPa) | 包络角点 (MPa) |
| ---: | ---: | ---: | ---: | ---: | ---: |
| 1.737 | 65.300 | 65.300 | 92.348 | 50.281 | 105.149 |
| 2.000 | 56.701 | 56.701 | 80.188 | 43.660 | 91.303 |
| 2.500 | 45.361 | 45.361 | 64.150 | 34.928 | 73.042 |
| 3.000 | 37.801 | 37.801 | 53.458 | 29.107 | 60.869 |
| 3.500 | 32.401 | 32.401 | 45.821 | 24.949 | 52.173 |
