xianzai588/Hanjie/deliverables/registration-description.md

# 报名表"作品详细描述"填写口径（已核实）

> 对应附件 1《"中铁山桥杯"焊接工艺设计赛道报名表》。
> 2026-09-02 从报名表 .doc 原文提取核实。

## 报名表原文

```text
作品详细描述（200字以内）
固定命题，请填无
```

## 结论

本队为**固定命题**，该栏**填"无"**即可，无需填写 200 字描述。

## 备用：方案简介（如校内预选或老师另索材料时使用）

以下简介仅用于校内交流：

针对QT450-10主轴承座与Q235B壳体，提出八段两道脉冲TIG、NiFe-55镍铁基填充、圆柱胀套独立夹紧和紫铜衬环内腔防护方案，并采用铸铁冷焊热制度（不预热、层间≤100 ℃）与焊后半热态锤击控制熔合区冷裂纹。当量计算（适用域声明见说明书§2.1）表明焊缝全稀释域显示高镍奥氏体倾向；因点位超出Schaeffler常用域，熔合线组织由金相/硬度/NDT确认。通过真实CAD、沉积守恒、条件承载与疲劳基线比较、工装包络、公差分配和失败互锁，覆盖工艺、材料、结构、评价、自动化五维度。交付16页论文（正文8页＋文末横版设计图集8页）与可复算数据；试制阶段按说明书§7设计放行顺序完成A类实物工程确认（当前技术包不宣称已完成）。

## 报名表其余字段提示

- 作品类型：勾选 **固定命题**。
- 参赛作品名称：建议与报告封面标题一致——"面向精密定位与内腔洁净的异种材料焊接工艺设计"（或按校方命名规则）。
- 团队主要成员：不超过 4 人；获奖证书按此栏颁发，填写前与队友核对。
- 报名表无"自编代码"字段（自编代码为铸造赛道要求）。
