xianzai588/Hanjie/deliverables/submission-checklist.md

# 参赛提交核对清单（COMPETITION-R3）

技术文件页数以包内 manifest.json 的实际计数为准（当前构建为16页论文：正文8页＋文末横版设计图集8页），另含名义装配STEP、计算记录、工艺提案、冷焊与锤击专项工艺卡、Schaeffler相图映射、候选选择、确定性鲁棒边界、参数来源与证据等级总图、守恒修订与放行闭环图、复现与版本冻结记录。旧图纸与旧研究结果不混入当前技术包。

- 构建：python deliverables/build_submission.py；基于实际运行结果检查输入并重新导出当前图纸/报告与候选选择。包内整件热结构主网格结果与能量历史为当前冻结诊断附件，不由该入口重算。
- 已覆盖工艺、材料、结构、质量评价、自动化五维度；主设计为8P两道、NiFe-55填充、铸铁冷焊热制度（不预热、层间≤100 ℃）、焊后半热态锤击。
- 组织设计由 Schaeffler 当量计算进行高镍奥氏体倾向筛查；因点位超出常用图域，熔合线组织、硬度和裂纹状态必须由 V6/V7 实物确认（包内 19～21 号）。
- 位置度预算口径（R3）：预算目标上限 0.0456 mm（04号 precision：设计口径 0.0436＋测量扩展 0.002，design_budget_closes=true）；R3 保守合成估计 31.34 μm（线性、直径口径，FE 热残余取两网格较差值），构成与出处见说明书 §4.3 统一表。R1 时期“合计 0.0456、余 0.0044、热残余上限 0.0102”旧口径自 R3 起停用。试制阶段按说明书 §7 设计放行顺序完成 CMM 实测、金相与显微硬度、锤击层残余应力、衬环热接触与颗粒清点等工程确认。
- 热模型诊断在当前版本冻结，用于确定热输入窗口与风险边界；位置度证据由独立测量闭环判定。
- 焊接固定命题允许设计作品、篇幅不限；不套用铸造匿名与版式条款。
- 同校2～4名学生、1～2名教师。10月20日前报名；10月25日（含当日）提交作品和盖章汇总表，由校负责人核对最新通知。
- 固定命题报名表"作品详细描述"按原附件填"无"；真实学校、成员与指导教师由参赛方填写。
- 校方压缩包命名按官方"焊接工艺设计赛-参赛院校"。本地技术包按校方要求完成盖章、推荐与正式提交。
- 技术说明书与图纸已按当前生成入口核对；提交前由队伍确认报名信息、引用原件和附件清单。

原始依据：competition/original-files/welding/第一届辽宁省大学生材料焊接与铸造工艺设计大赛实施方案.pdf。
