xianzai588/Hanjie/docs/plan-2-physics-v5.3.md

# 计划二执行记录：焊接热模型物理完整性与工艺可行域

> 当前工作推进至本文末尾 **Plan 2C / THERMAL-0.4R**。下文0.3质量失配与243组预检保留为历史记录，不代表0.4仍使用旧焊缝带。

2026-09-06。**G-PHYSICS = REVIEW；THERMAL-1 和正式 STRUCT-0 均不放行。** 本轮完成25组实际计算，发现代理焊缝质量/几何不闭合。停止对该代理进行校准，先核实真实接头、填丝和宏观熔合。没有证明真实 TIG 路线不可行。

路线变更为 `G-THERMAL → G-PHYSICS → EXP-THERMAL → THERMAL-1`。无实验时只允许带明确不确定性的情景研究；不能宣称 calibrated、validated、最优或保证 Ø0.05。

## 已执行与保留的边界

| 交付物 | 本轮结果 | 尚未完成 |
| --- | --- | --- |
| THERMAL0.2 封存 | 原始结果及 manifest 全部核验未变；numerically verified, physically uncalibrated | 不升级物理证据 |
| THERMAL-0.3-PHYS | 三种材料独立固/液相线、潜热焓更新；温度相关 k/cp；两种激活模式 | ERNiFe-CI 高温数据仍为假设，未完成真实填丝几何 |
| G-PHYSICS | 独立机器审计，保留具体阻断项 | 质量闭合、高温数据、物理熔合与实验 |
| PROCESS-FEASIBILITY | 9个工艺/预热组合×2模式，另7组敏感性/复核 | 未穷尽连续工艺域，不构成全域不可行证明 |
| METALLURGY | 两侧母材 t8/5 有效数=0；风险改为 unresolved | 不能评价真实熔焊 HAZ 安全性 |
| EXP-THERMAL v2 | 执行协议、原始记录字段、质量账本、独立试件分流和目标函数规则 | 设备、试件、原始测量与实验执行 |
| STRUCT-0-PREP | 独立基准/孔轴拟合、体积加权P95、释放状态及SERVICE合力/力矩模块通过测试 | 统一网格、弹塑性、心轴接触、实物基准协议与正式耦合 |

## 计算结果

| 情景 | 全场峰温 °C | QT母材峰温 °C | Q235B母材峰温 °C |
| --- | ---: | ---: | ---: |
| 封存 THERMAL0.2 | 896.99 | 434.88 | 525.87 |
| 0.3 名义工况、预存在焊缝 | 797.15 | 426.29 | 507.56 |
| 0.3 名义工况、逐段激活 | 786.96 | 356.55 | 413.92 |

工艺采样的全场峰温上限为 **923.89°C**；单独改变 NiFe k/cp 的四组敏感性范围为 **683.78–1023.14°C**。全部25组计算中，QT/Q235B母材峰温上限分别为 **483.94/574.42°C**，母材有效 t8/5 均为0，没有两侧熔合。

名义工况关闭潜热后的峰温与开启潜热完全相同，因为未进入相变区。独立加热测试实际跨过固/液相线，以分段 cp 梯形积分加潜热复算能量，验证了潜热没有被漏掉。所有已算峰温也低于各材料假设固相线区间的下限；这仅说明这些情景下相变未激活，不能当作联合不确定性上界。

预存在/激活两模式 dt减半的峰温变化分别为 **0.01465% / 0.04022%**。旧网格收敛证据只封存为0.2的证据，不能自动覆盖新增空腔、出生边界和新物性。没有进行无意义的0.2网格加密。

## 物理阻断：填丝质量与热源沉积

由仓库名义焊丝 Ø1.2 mm、送丝2 mm/s、行走1.5 mm/s计算，100%沉积率对应每单位焊长的填丝体积为 **1.508 mm²**。名义3.5 mm等脚角焊缝截面积为 **6.125 mm²**；当前网格中的全高度焊缝带约 **132.462 mm²**，分别是上述填丝量和名义角焊缝面积的 **87.84倍 / 21.63倍**。

角焊缝截面包含母材熔化贡献，不能把6.125/1.508直接解释成送丝倍率。但整个132.462 mm²区域预先赋予焊丝物性、或将其作为新增焊丝激活，都无法代表登记的实际填丝量。当前双模型因此保留为**同一失配焊缝带的敏感性实验**。

逐段激活时，空单元不导热、不蓄热；按焊枪位置激活后以20°C出生焓入账，新增空腔面有对流/辐射损失。热源在完整计算域内按原0.2权重归一化，落在空域的部分单列为未吸收能量，禁止向剩余单元集中。

名义工况输入19800 J中，激活模式吸收约14653.63 J，空域未吸收约5146.37 J（约26.0%）。所以797.15→786.96°C不能证明“预存在焊缝抑制峰温10°C”：质量、散热路径和有效沉积热量同时变化。完整计算域捕获PASS与活动材料吸收FAIL分开登记，不能用能量守恒掩盖源沉积模型不适用。

账本为 `E_absorbed + E_birth = ΔU + E_convection + E_radiation + residual`，另有 `E_nominal = E_absorbed + E_void`。出生焓非零与跨相变的独立测试均通过。所有结果保持 `solver_result_unvalidated`。

## 参数与采样证据

输入覆盖层见 [thermal-physics-v5.3.yaml](../project/thermal-physics-v5.3.yaml)，没有修改0.2冻结材料文件。Q235相变中心值使用文献中的1748/1793 K和264000 J/kg，换算为1474.85/1519.85°C；这不是本批Q235B实测。见[Q235连铸研究表2](https://www.mdpi.com/1996-1944/16/9/3361)。

QT及NiFe的相变区间、NiFe高温曲线均明确标为工程敏感性假设；不伪装成“精确标准值”或“文献置信区间”。[ERNiFe-CI供应商资料](https://nickelalloys.es/fundicion/fund-nife-cl-ernife-cl/)没有给出本模型需要的高温k/cp和潜热，G-PHYSICS对此保持未通过。

工艺采样固定η=0.55及原热源尺寸。先从冻结I/U/v离散组合中按 `ηUI/v ∈ [240,420] J/mm`过滤，再预登记功率、速度、线能量边界及名义点，加入130/180°C预热。实际采样线能量覆盖 **241.3125–412.5 J/mm**；未覆盖精确240/420端点或全部连续组合。没有根据计算峰温选点、提高η或缩小热源以追求熔化。

[Goldak轮廓校准研究](https://doi.org/10.1016/j.addma.2024.104379)研究对象是LPBF；本项目只采用联合几何约束的思路，不迁移其激光参数到TIG。

## EXP 与 STRUCT 准备

[EXP-THERMAL v2](../experiments/protocols/EXP-THERMAL-v2.yaml)优先获取实测I/U/v、两侧宏观熔深/熔宽及送丝增重。CAL-01/CAL-02用于校准及重复，VAL-01完整留作独立验证。误差标准化方法、目标函数权重和参数边界在首次优化前冻结。

旧协议Q235测点n=+10 mm超出5 mm壳壁及当前模型域，已在v2废止；候选远点改为沿z方向10 mm、n=4 mm，实物安装性仍需检查，不能再称法向10 mm测点。

[STRUCT-0-PREP清单](../project/struct-0-prep.yaml)逐项登记真实状态。显式壳体和Continuous座体已有独立CAD；统一焊缝网格和弹塑性求解尚未实现。新评价模块使用独立A/B测点，再拟合实际孔轴，计入整个测量跨度上的偏移和倾斜；这仍是最小二乘测量情景，正式CMM基准协议待确认。旧静力排名和未加权P95没有改写成新结果。

本轮开始工作区干净，贴文所说的5个未提交结构改动在本地不存在。未凭描述补造这些改动，也没有正式耦合热场。

## 复现

Python 3.12环境；新增依赖Numba已写入项目依赖，运行输入快照保存在结果目录。

```powershell
python simulation/thermal-v5/run_physics03.py
python simulation/thermal-v5/audit_physics03.py
python simulation/metallurgy-v5/run_metallurgy0.py
python -m pytest tests/test_physics03.py tests/test_structural_prep.py tests/test_plan1_artifacts.py tests/test_evidence_graph.py -q
```

本轮 **26项测试通过**。新结果集中于 [G-PHYSICS](../simulation/thermal-v5/results/physics03/G-PHYSICS.json)、[PROCESS-FEASIBILITY](../simulation/thermal-v5/results/physics03/PROCESS-FEASIBILITY.json)及[冶金风险修正结果](../simulation/metallurgy-v5/results/physics03/metallurgy0-summary.json)。manifest登记运行产物，旧THERMAL0.2产物未覆盖。

下一项物理工作是核实接头截面、填丝量和实际焊接记录，并据此建立质量闭合的填丝几何及源沉积模型。该信息补齐前继续扫η或正式计算残余位置度没有合理证据基础。

## 后续审计意见落实：密度与 THERMAL-1 准入

最新贴文仍基于0.2状态，其中相变焓、NiFe高温情景、激活对照和实验协议已由上面的0.3工作覆盖；不能回退到单一1350°C阈值，也不能省去G-PHYSICS。结构候选保留Continuous、6P、8P-FAIR_B，后续正式结构求解仍先从Continuous开始。

新增 [准入输入](../project/thermal1-admission.yaml) 和 [预检结果](../simulation/thermal-v5/results/thermal1-preflight.json)，仅补充密度证据边界和正式Goldak矩阵，不重跑旧25组热场。

**密度处理。** 增加三种材料的固态膨胀情景 `J(T)=exp(3∫α_tangent dT)`、`rho(T)=rho_ref/J(T)`，检查 `rho(T)J(T)=rho_ref`。原材料表没有明确α是瞬时还是平均系数，所以这种解释本身仍是design_assumption；NiFe仅有常温α，常值延伸也明确标为假设。α倍率0.8–1.2只作工程敏感性，不是测量置信区间。

当前0.3求解器继续使用固定参考质量，不直接把rho(T)塞进固定体积的能量更新。否则会人为改变总质量。[COMSOL参考构形热物性说明](https://doc.comsol.com/6.3/doc/com.comsol.help.metproc/metproc_ug_theory.4.11.html)同样强调密度参考温度与质量守恒。空间密度变化必须同时处理体积变化或质量输运；本轮没有宣称实现移动网格或液相输运。

Q235/QT的情景范围受已有α表和保守固相线下限共同限制，NiFe受固相线下限限制。缺失温区返回null/missing_evidence，尤其三种材料1500°C密度均未补造。**完整20–1500°C实测rho(T)、液相密度和高温物性证据仍未取得。**

**Goldak矩阵。** η=[0.45,0.55,0.65]，a_f=[4.8,6,7.2] mm，a_r=[8,10,12] mm，b/c=[2,2.5,3] mm，共243组全因子解析预检。η和b/c范围继承旧数值审计；a_f/a_r±20%为新登记的工程敏感性假设。I/U/v、预热及前后权重固定，线能量为270/330/390 J/mm，没有追温度调参。

72组满足当前网格解析度、计算域捕获、边界余量和能量约束；171组因热源过小、当前网格不足以解析而拒绝。**243组均未执行热场求解**，且仍被焊缝质量、活动材料热源沉积、高温物性证据及合理熔合四项阻断。解析通过不等于准入或校准成功；后续真实几何改变后须重新预检，而非直接继承这72组。

```powershell
python simulation/thermal-v5/preflight_thermal1.py
python -m pytest tests/test_thermal1_preflight.py -q
```

新增5项关键测试通过，覆盖闭式密度/体积守恒、分段α积分、缺失温区拒绝、热源缩窄/效率强推拒绝及物理Gate缺项不放行。0.2、0.3冻结输入和已有计算结果均未覆盖。

后续修复：预检原先漏检预热窗口、可接受负密度，且四个物理检查为真时会忽略Gate的REVIEW状态。现已修正，并校验alpha表、速度、网格、路径、前后权重及必要数值检查；23项预检回归测试通过。重生成的243组预检仍有72组满足数值条件，阻断列表明确包含Gate状态和激活网格未收敛，已有热场未重算或覆盖。

## Plan 2B：THERMAL-0.4-MASS-CLOSED 实际物理纠偏

本次直接重构几何与热源，只运行75 A、12 V、1.5 mm/s、η=0.55、预热150°C这一工况。0.2/0.3输入和计算产物保持原样，没有扩跑243组矩阵。

### 母材保留，只有填丝出生

新局部坐标以壳体内壁为n=0、座体上表面为z=0。QT母材为n≤−0.02 mm、−12≤z≤0；Q235B壳体为0≤n≤5 mm。保留0.02 mm空隙，未计间隙气体导热/相互辐射；填丝与两侧接触后形成固体导热路径。

填丝位于母材之外的角部，采用面积精确的4层阶梯三角截面，面积由 `πd²/4 × v_wire/v_travel × eta_deposit` 给出。名义沉积效率1.0仍是design_assumption，0.85–1.0区间已登记；几何测试覆盖0.85情景，不声称已做该情景热场敏感性。

- 填丝截面积：**1.507964 mm²**；等效三角焊脚：**1.736643 mm**。
- 40 s送丝形成体积：**90.477868 mm³**；质量：**0.741919 g**。
- 每步最大填丝体积相对误差：**9.33×10⁻¹⁵**；母材质量变化：**0**。

沿s单元内连续增加占据长度，新增质量精确对应积分送丝量。母材不变为NiFe、不被删除或重新出生。3.5 mm焊脚仍是待满足的设计要求，不把1.737 mm填丝几何冒充设计已经实现；母材熔化体积另行统计。

### 表面热流直接作用于首个可见材料面

改用45°入射的前后双高斯**表面热流模型**，沿s的a_front=6 mm、a_rear=10 mm及投影横向宽度b=2.5 mm保持原值，前后权重保持0.6/1.4；体积Goldak的深度参数c不再用于表面模型。这是明确的新源模型假设，不是将旧26%空域功率集中补回，也不是实验校准。

在无限s/u投影平面解析归一化，再按射线选取首个已有母材或已出生填丝表面。填丝遮挡母材后只由首面接收；尚未出生区域仍由实际存在的母材表面接收。独立射线—矩形相交oracle复核表面权重；人为删除一侧接收面时，总接收功率随之减少，不会自动归一化恢复495 W。

[GTAW热流模型对比研究](https://journals.sagepub.com/doi/10.1243/09544054JEM1886)比较过表面高斯与体积Goldak模型；这里仅据此说明表面模型具有方法依据，不转用其材料/工艺标定。45°方向、阶梯自由表面和源尺度仍需真实接头/宏观截面约束。

实际源输入/表面接收均为 **19.800 kJ**，最小活动材料接收比例约 **100%**，超过运行前冻结的95%工程门槛；没有活动域重归一化。该值证明本源模型的功率没有落空，不证明真实电弧热流已经校准。

### 单一名义工况的实际结果

使用36260个参考单元、0.1 s隐式时间步，焊接40 s并继续冷却20 s。沿用0.3材料焓表和未验证高温物性情景；使用参考质量守恒，未模拟熔池流动、蒸发或成分混合。

| 材料 | 峰温 °C | 假设固相线 °C | 曾超过固相线体积 mm³ | 有效t8/5单元数 |
| --- | ---: | ---: | ---: | ---: |
| QT450-10母材 | 1087.262 | 1100 | 0 | 313 |
| Q235B母材 | 1018.340 | 1474.85 | 0 | 159 |
| ERNiFe-CI填丝 | 1517.269 | 1380 | 25.2584 | 420 |

NiFe曾超过液相线的体积约9.0478 mm³，说明出现**局部熔化**，不代表全部填丝已经充分熔化或接头实现两侧熔合。两侧母材现在确实超过800°C，所以0.4的非零t8/5与0.2/0.3中的母材零计数不矛盾；这些新热循环尚未用于评分真实冶金风险。

全局能量残差约 **−4.20×10⁻⁶ J（2.12×10⁻⁸%）**。隐式焓更新包含出生焓、导热和边界损失；本例20°C出生焓为零，独立热/冷质量混合测试验证了新增冷质量不会凭空获得热焓，相变跨越测试也通过。

**G-PHYSICS-R1：质量闭合、母材始终存在、源沉积、能量闭合及相变实现通过本轮检查；新模型网格/时间步及熔合几何收敛尚未验证，高温物性仍未获实验支持，两侧母材熔合未闭合。** 不把数值闭合升级为工艺合格，不修改η追求母材熔化。

新物理核心8项测试通过，加上沿用相变模块6项回归，共14项。测试覆盖逐时刻送丝体积、真实母材身份/间隙、独立射线积分、未出生材料无导热、删接收面不归一化、冷丝出生焓与潜热。

```powershell
python simulation/thermal-v5/run_mass_closed04.py
python -m pytest tests/test_mass_closed04.py tests/test_physics03.py -q
```

输入：[thermal-mass-closed-v5.4.yaml](../project/thermal-mass-closed-v5.4.yaml)。代码：[几何与表面源](../simulation/thermal-v5/mass_closed_geometry.py)、[隐式热求解器](../simulation/thermal-v5/run_mass_closed04.py)。结果：[summary](../simulation/thermal-v5/results/mass-closed04/summary.json)、[G-PHYSICS-R1](../simulation/thermal-v5/results/mass-closed04/G-PHYSICS-R1.json)、[质量/能量时间账本](../simulation/thermal-v5/results/mass-closed04/history.json)。

下一阶段针对**这个新模型**补材料证据、冻结情景并验证收敛，重点考察两侧熔合几何。THERMAL-1和正式STRUCT-0继续冻结；旧243组预检仍属于0.3，不直接迁移为0.4准入结果。

## Plan 2C / THERMAL-0.4R：物理可信度诊断

预登记配置为 `project/thermal-credibility-v5.4r.yaml`，运行入口为 `simulation/thermal-v5/run_credibility04r.py`。原0.4求解器、输入及结果保持封存；0.4R在独立模块实例中复用其焓求解，增加源接口和观测账本。每一步记录Q235、QT、NiFe直接源输入和净导热，二者不混同。正净导热表示从其余材料吸热；各材料净导热之和应为零。

名义账本：Q235直接4.184 kJ（21.13%）、QT 4.603 kJ（23.25%）、NiFe 11.012 kJ（55.62%）。随后NiFe向母材净导热10.626 kJ，分别进入Q235 4.928 kJ、QT 5.698 kJ。因此没有出现“NiFe独占80–90%直接输入”的证据，也不能把直接源占比当作材料最终储能占比。

### 热源与物性情景

固定η=0.55、I=75 A、U=12 V、v=1.5 mm/s、送丝2 mm/s、预热150°C。比较45°表面源、90%表面+10%浅层源、30°表面源。浅层部分沿射线在实际材料路径中以0.5 mm衰减长度指数吸收，间隙不吸收，剩余透射独立记账；它不是已标定的熔池对流模型。10%、0.5 mm、30°均为事先声明的设计情景，不能因为某情景更易熔化就选为真实模型。

[GTAW表面/体积热源比较研究](https://journals.sagepub.com/doi/10.1243/09544054JEM1886)支持开展热源结构比较；研究对象是AA1050，不能迁移其材料或工艺参数。本轮再次检查[NiFe焊丝生产商页面](https://nickelalloys.es/fundicion/fund-nife-cl-ernife-cl/)，仍只有成分、用途及机械性能，未获得高温k/cp或相变数据。Q235和球铁既有MDPI来源本轮直接访问返回429，保留原证据等级，没有声称完成新的逐值核验。

物性lower/nominal/upper采用0.3已登记的各参数工程区间；lower/upper是同时取参数端点的联合情景，**不是温度上下界、统计置信区间或实测曲线**。Q235相变常数为文献类比，其余高温曲线、QT/NiFe相变参数仍属设计假设。参考密度不随温度随意修改；alpha未进入固定参考域热方程，也没有据此虚构液态密度证据。完整字段分级、范围及结果见本轮assessment.json。

### 数值验证和判读规则

三档网格同时细化s方向、近远场及填丝阶梯，保持填丝积分体积；固定dt=0.1 s。另在中网格比较dt=0.1/0.05/0.025 s。它们是冻结名义代理物性及45°表面源后的**条件数值验证**，不能代替材料证据或实测标定。

除峰温外，对照母材/填丝越固相线与液相线体积、最大截面热暴露面积、母材热暴露宽度/深度、t8/5有效体积和体积加权均值、400°C以上暴露体积与能量残差。宽度/深度是逐截面单元外缘包络，不是实测金相熔合线；400°C以上暴露也不冒充组织HAZ边界。相邻变化门槛为5%；峰温还须不超过10°C，宽深还须不超过0.1 mm。两级熔化量均为零只说明状态一致，不能判定熔合几何收敛；出现阈值翻转则明确失败。t8/5均值基于各网格实际有效区域，需结合有效体积共同判断。

### 焊脚与后续工艺边界

3.5 mm位于 `project/baseline.yaml` 的设计geometry字段，不在其official字段中；`docs/plan-1-execution-v5.2.md`也将其列为设计假设。当前未找到独立承载/疲劳证明，不自行改变冻结设计。母材熔化区域并不等于外部新增截面积；没有母材迁移与自由表面模型，不能将母材熔化量直接加到1.508 mm²填丝截面上补足6.125 mm²。若保持理想等脚三角外形且完全由焊丝增加体积，3.5 mm对应的送丝量约为当前4.06倍；这只是体积核算，不是推荐工艺。

联合工艺扫描须先解决本轮暴露的收敛及材料证据问题，之后才围绕I/U/v/送丝/预热预登记9–15点；不恢复旧243组，不人为提高η追峰温。没有实测宏观截面、过程参数、耗丝/沉积质量与热电偶记录时，THERMAL-1和正式STRUCT-0继续不放行。

### 本轮实跑结果与判定

共10组，均完成40 s热源移动及20 s冷却。各组质量、有效源输入与全局能量检查通过，最大能量相对残差为1.73×10⁻⁷%。名义复算的各材料峰温与封存0.4一致。

| 工况 | Q235峰温°C | QT峰温°C | NiFe峰温°C | QT越固相线mm³ | NiFe越固相线mm³ |
| --- | ---: | ---: | ---: | ---: | ---: |
| baseline | 1018.34 | 1087.26 | 1517.27 | 0.000 | 25.258 |
| shallow45 | 1019.36 | 1087.56 | 1500.29 | 0.000 | 18.473 |
| surface30 | 1044.16 | 1087.91 | 1439.30 | 0.000 | 18.096 |
| properties-lower | 1186.24 | 1287.59 | 1943.33 | 95.192 | 81.889 |
| properties-upper | 876.73 | 929.37 | 1265.60 | 0.000 | 0.000 |
| coarse | 972.57 | 1051.07 | 1478.76 | 0.000 | 35.521 |
| medium | 1019.73 | 1088.15 | 1518.62 | 0.000 | 26.012 |
| fine | 1057.52 | 1124.21 | 1532.35 | 9.957 | 17.006 |
| dt-0.05 | 1021.81 | 1090.82 | 1520.97 | 0.000 | 26.578 |
| dt-0.025 | 1022.80 | 1092.02 | 1522.16 | 0.000 | 26.578 |

**时间步两次细化比较均通过预登记指标；空间网格两次细化比较均未通过。** 中→细网格，NiFe越固相线暴露体积变化34.62%，QT从零翻转到9.957 mm³，单元外缘热暴露深度为0.4 mm。后者只有一层细网格深度，不能作为已收敛熔深。Q235在全部10组中越固相线体积均为零；有限情景不能证明真实工艺不可行。

因此本轮完成的是可信度诊断，不是THERMAL-1认证。首要问题已定位为空间离散/阶梯表面表示与高温物性敏感性；不继续调整Gate或挑选能熔化的热源。联合工艺扫描未启动。

验证：新增7项独立测试通过，原0.4及焓实现14项回归通过，证据图8项测试通过，共29项。全结果审计核对逐步源/净导热、运行来源、材料分配与名义复现。初轮测试将有限厚度穿透误写为100%吸收，已按解析透射模型修正测试预期，未修改功率归一化。

运行期间发现继承的方向/网格状态元数据仍使用旧标签，已按实际计算角度纠正。实际执行驱动保存在结果根目录executed-runner.py及runtime-provenance.json；场数据和能量账本没有因元数据修正重算或改写。后续入口已同步修正标签。

复现命令（指定新的输出目录，入口拒绝覆盖已有证据）：

```powershell
python simulation/thermal-v5/run_credibility04r.py --output-dir output/credibility04r-repeat
python simulation/thermal-v5/audit_credibility04r.py --output-dir output/credibility04r-repeat
python -m pytest tests/test_credibility04r.py tests/test_mass_closed04.py tests/test_physics03.py tests/test_evidence_graph.py -q
```
