xianzai588/Hanjie/docs/01-roadmap.md

# 01 当前执行路线

2026-09-05 起以 [V4.2 比赛路线与修复计划](V4.2-competition-roadmap.md) 为唯一当前路线。旧版“P0–P5 已完成”仅说明部分数字脚本曾运行，不表示工程验证通过。

优先顺序：证据纠偏 → FAIR-A/B 真实几何与静刚度 → 真正 Continuous 热—结构求解及验证 → 条件落实后的物理校准 → 同模型焊序/预偏置对照 → 预算与报告冻结。

设备全部待确认；数字主线继续推进，实测证据积极争取。报名 10 月 20 日前，作品 10 月 25 日（含当日）提交，均由学校负责人办理。固定命题须覆盖工艺、材料、结构、质量评价、自动化五个维度，不强制提供实物。
