xianzai588/Hanjie/docs/v4-freeze-summary.md

# V4 技术路线冻结 - 工作总结

**日期**：2026-09-03  
**版本**：V4.0-FROZEN  
**状态**：设计输入冻结完成，FE3D-BASE 实施准备就绪

---

## 📌 核心决策

### 技术路线收敛原则

**停止功能扩展和文档总结，先建立 Baseline 数值可信度。**

V4 执行严格的技术纪律：
- ✅ **只实施** FE3D-BASE（连续环形座体 + 刚性夹具 + S3）
- ❌ **禁止** 4/6/8 点结构优化、Pareto、自适应跳焊、反变形补偿
- ⏸️ **暂停** 所有结构参数扫描和优化工作
- 🔒 **冻结** 设计输入、验证协议、判据

**理由**：Baseline 未通过 Gate B 前，任何结构优化结论都不可信。

---

## ✅ V4 交付物（已完成）

### 1. 设计输入冻结

**文件**：`simulation/fe3d/design-inputs-frozen-v4.md`

**内容**：
- 几何参数（壳体、轴承座、焊缝）
- 材料参数（温度相关：E, α, σ_y, k, c_p）
- 工艺参数（I=75A, U=12V, v=1.5mm/s, q=330J/mm）
- 边界条件（夹具约束、热边界、释放时机）
- 分析流程（热分析 → 结构分析 → 后处理）
- 网格策略（G51/G61/G71/G81）
- 输出指标（位置度 P、应力、温度、HAZ）

**状态**：✅ 已冻结，FE3D-BASE 及后续建模统一使用此输入

### 2. 验证协议（结果出来前编写）

**文件**：`simulation/fe3d/FE3D-BASE-verification-protocol.md`

**内容**：
- Gate B.1：网格收敛判据（P < 5%, T_peak < 10%, σ < 15%）
- Gate B.2：热场合理性判据（1300-1600°C, HAZ 3-10mm）
- Gate B.3：边界条件验证清单
- Gate B.4：材料参数验证清单
- 孔轴线位置度提取算法（最小二乘拟合）
- 异常检测与通过/不通过判定流程

**关键原则**：结果出来前编写判据，避免确认偏误

**状态**：✅ 已编写完成，严格按照协议验证

### 3. 技术报告 V4 骨架

**文件**：`deliverables/report/technical-report-v4.md`

**结构**：
- §0: V4 技术路线声明（实施范围、禁止项、Gate B）
- §1-3: 题面约束、材料边界、工艺路线
- §4-5: FE3D-BASE 几何与分析流程
- §6: 网格策略与收敛验证
- §7: Gate B 验证结果（PLACEHOLDER，待填充）
- §8-9: 疲劳评估、内腔防护
- §10-11: 证据分级、后续路线图
- §12: 附录（文件清单、术语表）

**状态**：✅ 骨架完成，§7 待 FE3D-BASE 结果填充

### 4. 实施状态追踪

**文件**：`simulation/fe3d/FE3D-BASE-status.md`

**内容**：40 项检查清单
- Phase 0: 准备（4/4 已完成）
- Phase 1: 几何建模（0/5）
- Phase 2: 网格划分（0/8）
- Phase 3: 材料定义（0/5）
- Phase 4: 边界条件与载荷（0/10）
- Phase 5: 求解设置（0/4）
- Phase 6: 求解运行（0/4）
- Phase 7: 后处理（0/8）
- Phase 8: Gate B 验证（0/12）
- Phase 9: 文档更新（0/4）

**当前进度**：4/40 (10%)

**状态**：✅ 检查清单建立，Phase 1 待开始

### 5. 目录结构与 README

**文件**：`simulation/fe3d/README.md`

**内容**：
- V4 技术路线说明
- 禁止项清单
- 文件结构
- Gate B 验证门详解
- 设计输入摘要
- 实施流程与路线图
- 验证协议原则
- 问题诊断流程

**状态**：✅ 导航文档完成

---

## 🚫 禁止项（重申）

Gate B 通过前，严格禁止：

1. ❌ 4-point 结构建模
2. ❌ 6-point 结构建模
3. ❌ 8-point 结构建模
4. ❌ 柔顺夹具对比
5. ❌ Pareto 多目标优化
6. ❌ 自适应跳焊策略
7. ❌ 反变形补偿设计
8. ❌ 任何结构参数扫描
9. ❌ 修改验证协议判据（结果出来后）
10. ❌ 继续总结文档和功能扩展

---

## 📊 Gate B 验证门（必须全部通过）

### Gate B.1: 网格收敛

**判据**：相邻网格级主要指标变化率

| 指标 | 阈值 | 说明 |
| --- | ---: | --- |
| 位置度 P | < 5% | 两级都必须 < 5% |
| 峰值温度 T_peak | < 10% | 两级都必须 < 10% |
| 最大应力 σ_eq_max | < 15% | 两级都必须 < 15% |

**网格序列**：G51 → G61 → G71 → G81

### Gate B.2: 热场合理性

**检查项**：
- 峰值温度 1300-1600°C（TIG 熔池范围）
- HAZ 宽度 3-10 mm（> 723°C 区域）
- 热源移动速度 = 1.5 mm/s
- 层间温度 ≤ 200°C

### Gate B.3: 边界条件

**检查项**：
- 夹具约束清单完整
- 释放时机明确（50±5°C）
- 热边界条件正确

### Gate B.4: 材料参数

**检查项**：
- 温度相关性合理（单调性）
- 来源标注清晰
- 不确定性评估

**只有 Gate B.1/B.2/B.3/B.4 全部通过，才允许开展 4/6/8 结构对比（V5）。**

---

## 📈 技术债务清理

### V2 → V3 问题修复（已完成）

- ✅ 接头几何修正（翼端半径、间隙）
- ✅ 基准定义修正（独立基准系统）
- ✅ 误差预算闭合（0.025 mm 径向预算）
- ✅ H7/h6 表述修正（Ø40 H7 孔）
- ✅ 证据清单细节清洗

### V3 → V4 核心转变

**V3 问题**：
- 降阶模型 + 二维 FE 代理，网格收敛未通过（29.224%）
- 柔顺结构优势证据不足
- 结构对比未统一边界条件

**V4 策略**：
- 停止降阶模型和二维 FE
- **只实施** FE3D-BASE（连续环形座体）
- 建立数值可信度基线（Gate B）
- 禁止未经验证的结构扩展

---

## 🔄 后续路线图

### V4 当前阶段（2-4 周）

**目标**：建立 FE3D-BASE 数值可信度

**任务**：
1. Phase 1-2: 几何建模 + 网格划分
2. Phase 3-5: 材料定义 + 边界条件 + 求解设置
3. Phase 6: 求解运行（G61/G71/G81）
4. Phase 7: 后处理（位置度、热场、应力场）
5. Phase 8: Gate B 验证
6. Phase 9: 文档更新

**交付物**：
- FE3D-BASE 验证报告
- Gate B 通过判定
- `technical-report-v4.md` §7 填充

### V5 阶段（Gate B 通过后）

**目标**：公平结构对比

**条件**：Gate B.1/B.2/B.3/B.4 全部通过

**任务**：
- 4-point 结构建模
- 6-point 结构建模
- 8-point 结构建模
- 统一网格、边界、参数
- 结构选型结论

### V6+ 阶段（V5 完成后）

**目标**：协同优化

**任务**：
- 柔顺夹具对比
- Pareto 多目标优化
- 自适应跳焊
- 反变形补偿

---

## 📝 V4 与 V2/V3 对比

| 项目 | V2 | V3 | V4 |
| --- | --- | --- | --- |
| **分析方法** | 降阶模型 + 二维 FE 代理 | 同 V2 | **三维 FE（仅 Baseline）** |
| **网格收敛** | 未通过（29.224%） | 同 V2 | **严格验证（< 5%）** |
| **结构对比** | 6 点柔顺 vs 刚性 | 同 V2 | **禁止（Gate B 通过前）** |
| **边界条件** | 混合（顺序/夹具不统一） | 同 V2 | **冻结（刚性/S3）** |
| **验证协议** | 无 | 无 | **有（结果前编写）** |
| **禁止项** | 无 | 无 | **严格执行** |
| **技术纪律** | 功能扩展优先 | 修正 P0 | **可信度优先** |

**核心转变**：从"快速探索多方案"转向"严格验证 Baseline"。

---

## 🎯 V4 成功标准

### 最小成功（必须）

- [ ] FE3D-BASE 建模完成
- [ ] Gate B.1 网格收敛通过
- [ ] Gate B.2 热场合理性通过
- [ ] Gate B.3 边界条件通过
- [ ] Gate B.4 材料参数通过
- [ ] 验证报告编写完成

### 完整成功（期望）

- [ ] 位置度预测值明确（P_FE3D_BASE）
- [ ] 热场云图、应力场云图完整
- [ ] 温度历程曲线完整
- [ ] 孔轴线偏移矢量可视化
- [ ] 不确定性敏感度分析
- [ ] 为 V5 结构对比建立可信基线

---

## ⚠️ 风险与缓解

### 风险 1：网格收敛未达标

**影响**：Gate B.1 不通过，无法进入 V5

**缓解**：
- 预留 G91 加密网格
- 优化网格过渡策略
- 检查单元类型选择

### 风险 2：峰值温度超范围

**影响**：Gate B.2 不通过，热源模型不合理

**缓解**：
- 调整 Goldak 热源参数（a_f, a_r, b, c）
- 与文献 HAZ 尺度交叉验证
- 必要时引入热源标定试验

### 风险 3：求解不收敛

**影响**：无法获得结果

**缓解**：
- 调整时间步长、增量步
- 优化非线性求解设置
- 检查接触定义、材料本构

### 风险 4：计算时间过长

**影响**：进度延误

**缓解**：
- 优化网格过渡
- 并行计算（多核）
- 简化远场网格

---

## 📂 文件清单

### 已交付文件

| 文件 | 路径 | 大小 | 状态 |
| --- | --- | ---: | --- |
| 设计输入冻结 | `simulation/fe3d/design-inputs-frozen-v4.md` | ~6 KB | ✅ 已冻结 |
| 验证协议 | `simulation/fe3d/FE3D-BASE-verification-protocol.md` | ~9 KB | ✅ 已编写 |
| 状态追踪 | `simulation/fe3d/FE3D-BASE-status.md` | ~6 KB | ✅ 检查清单 |
| README | `simulation/fe3d/README.md` | ~8 KB | ✅ 导航文档 |
| 技术报告 V4 | `deliverables/report/technical-report-v4.md` | ~17 KB | ✅ 骨架完成 |
| 工作总结 | `docs/v4-freeze-summary.md` | 本文件 | ✅ 总结完成 |

### 待建立文件（Phase 1+）

- `simulation/fe3d/models/FE3D-BASE/geometry/` 几何文件
- `simulation/fe3d/models/FE3D-BASE/mesh/` 网格文件
- `simulation/fe3d/models/FE3D-BASE/materials/` 材料定义
- `simulation/fe3d/models/FE3D-BASE/bc/` 边界条件
- `simulation/fe3d/models/FE3D-BASE/analysis/` 求解设置
- `simulation/fe3d/models/FE3D-BASE/results/` 结果文件
- `simulation/fe3d/FE3D-BASE-verification-report.md` 验证报告

---

## 🔖 关键提交信息

**提交标题**：`[V4-FREEZE] 技术路线冻结：停止功能扩展，只实施 FE3D-BASE`

**提交说明**：

V4 技术路线收敛，执行严格技术纪律：

**已完成**：
- ✅ 设计输入冻结（几何、材料、工艺、边界）
- ✅ 验证协议编写（结果前，避免确认偏误）
- ✅ 技术报告 V4 骨架
- ✅ 实施状态追踪（40 项检查清单）
- ✅ FE3D-BASE 目录结构

**唯一实施任务**：FE3D-BASE（连续环形座体 + 刚性夹具 + S3）

**Gate B 验证门**（必须全部通过）：
- B.1 网格收敛（P < 5%, T < 10%, σ < 15%）
- B.2 热场合理性（1300-1600°C, HAZ 3-10mm）
- B.3 边界条件验证
- B.4 材料参数验证

**严格禁止**（Gate B 通过前）：
- 🚫 4/6/8 点结构优化
- 🚫 Pareto、自适应跳焊、反变形补偿
- 🚫 任何结构参数扫描
- 🚫 修改验证协议判据

**理由**：Baseline 数值可信度未建立前，任何结构优化结论都不可信。

**下一步**：开始 Phase 1 几何建模。

---

**V4 冻结状态**：设计输入已锁定，FE3D-BASE 实施准备就绪，技术纪律严格执行。
