xianzai588/Hanjie/docs/daily-summary-final-2026-09-03.md

# 今日工作最终总结（2026-09-03）

**工作时长**：约 4 小时  
**Git 提交**：7 个 commit  
**状态**：P0 关键修正完成

---

## 核心认识修正 ⚠️

### 评分校准

**修正前的误解**：
- ❌ "今日完成后项目评分 85 分"
- ❌ "现在直接提交就有 85 分竞争力"

**修正后的正确理解**：
- ✅ **85 分是项目开发状态评分**
- ✅ **当前真正 PDF 提交态：81-83 分**
- ✅ README = V4，但技术报告 = V2（最大不一致）

**关键认识**：
> 比赛是盲审无答辩，评委只看最终 PDF。必须把"V4 规划"变成"V4 可提交证据"。

---

## 今日完成的工作

### 一、V3 P0 硬伤修复 ✅

1. **R73.8/1.2mm 接头几何矛盾**
   - R73.8 → R74.98 mm
   - 小间隙精密定心设计
   - 删除所有 "2D FE equivalent" 标注

2. **Ø39.96 定位销与误差预算矛盾**
   - 定位销 → 锥形心轴 1:50
   - 定位重复性 0.008 mm（设计假设）

3. **误差预算混淆装配链与自动化链**
   - 拆分为两条独立链路
   - 生成 V3 误差预算文档

**Git 提交**：`3754ded [V3-FIX-P0]`

---

### 二、V4 主线重构 ✅

1. **主标题修改**
   - 从"基于六点柔顺结构"
   - 改为"面向 Ø0.05 mm 位置度的热—结构协同优化"

2. **四个创新点凝聚**
   - 参数化低拘束接头+协同优化
   - 温度门控自适应跳焊（主创新）
   - 焊前反变形补偿
   - 一件一码数字质量闭环

3. **核心一句话确立**

**Git 提交**：
- `d4b270b [V3-DOC]`
- `39edc0d [V4-MAINLINE]`
- `6689dde [V4-DOC]`
- `c871e16 [V4-DOC]`
- `0260139 [V4-DOC]`

---

### 三、P0 关键修正 ✅

1. **H7/h6 表述纠正**
   - 从"过渡配合" → "定位间隙配合"
   - 明确为小间隙精密定心设计

2. **误差预算状态修正**
   - 从"已修复" → "未闭合但方向正确"
   - 当前 0.035 mm > 0.025 mm 目标
   - 增加 V4 目标分配（设计指标）
   - 误差预算成为四个创新点的顶层约束

3. **证据清单系统建立**
   - `evidence/claims.yaml`（17 个主张）
   - 明确每个主张的证据来源、置信度和发布状态
   - 六点柔顺 = `unresolved`（ROM 支持，FE2D 反例）
   - 温度门控/反变形/Pareto = `proposed`
   - 二维 FE = `preliminary_model`（网格未收敛）
   - 误差预算 = `not_closed`（优化目标）
   - 所有实物验证 = `pending`

**Git 提交**：
- `c8e3f2c [V4-P0]`
- `dc7dd61 [V4-P0]`

---

## Git 提交记录（今日全部）

```
dc7dd61 [V4-P0] 添加关键修正说明文档
c8e3f2c [V4-P0] 关键修正：H7/h6表述+误差预算未闭合+证据清单
0260139 [V4-DOC] 今日工作总结
c871e16 [V4-DOC] 添加执行摘要
6689dde [V4-DOC] 对深度评审意见的完整回应
39edc0d [V4-MAINLINE] 重构项目核心叙事
d4b270b [V3-DOC] 添加进度报告与刚度分析框架
3754ded [V3-FIX-P0] 修复接头几何、夹具定位与误差预算三大硬伤
```

**已推送到**：`github.com:xianzai588/Hanjie.git`

---

## 文件变更统计

| 类型 | 文件数 | 说明 |
| --- | ---: | --- |
| 核心配置 | 2 | geometry.json, design-assumptions.md |
| 证据系统 | 1 | evidence/claims.yaml（新建） |
| CAD 生成器 | 2 | 生成器脚本 |
| 工程图 | 7 | 全部 SVG 重新生成 |
| 仿真脚本 | 1 | error_budget_v3.py |
| 文档 | 10 | V3/V4 计划、进度、修正、摘要 |
| **合计** | **23** | |

---

## 评分真实状态

| 状态 | 评分 | 说明 |
| --- | ---: | --- |
| 项目架构/规划成熟度 | **85** | README、计划已 V4 |
| **当前真正 PDF 提交态** | **81-83** | 技术报告仍 V2 |
| 修正一致性后 | 84-85 | ⏳ 下一步 |
| 完成可信 3D FE | 86-88 | ⏳ 9月5-10日 |
| 温度门控对照 | 87-89 | ⏳ 9月14-18日 |
| V4 全部完成 | 88-90 | 🎯 目标 |
| V4 + 实物证据 | 90-92 | 🎯 最佳 |

---

## 下一步最关键的工作

### 不是 ❌
- ❌ 继续写温度门控代码
- ❌ 继续加功能
- ❌ 追求更多创新点

### 而是 ✅

**1. 建立 technical-report-v4.md（本周）⏳**

把"V4 规划"变成"V4 可提交证据"

必须同步：
- R74.98 小间隙精密定心
- 锥形心轴 1:50
- V3 误差预算（未闭合但方向正确）
- V4 主叙事和四个创新点
- 所有"尚未实现的创新"标为 `proposed / to-be-verified`

新论文结构（8 章）：
1. 问题分析与设计目标
2. 异种材料焊接性与工艺选择
3. 参数化接头与夹具设计
4. 热—结构协同模型
5. 结构与工艺优化结果
6. 自适应跳焊与补偿
7. 自动化与质量闭环
8. 可靠性与证据边界

**2. 建立 3D FE Baseline（9月5-10日）⏳**

只完成一个模型：
- Continuous + rigid fixture + baseline process
- 真正 3D 壳体 + 轴承座
- 移动热源（Goldak/高斯）
- 热-弹塑性顺序耦合
- **网格收敛性验证（变化 < 5%）**

**Gate B**：模型自己先站得住

**3. 公平结构比较（9月10-14日）⏳**

统一边界，只改变结构变量：
- Continuous / 4-point / 6-point / 8-point

**Gate C**：六点到底是不是值得继续

**关键**：如果六点输，换方案，不要保六点。

---

## 执行时间表（修正后）

| 日期 | 里程碑 | Gate |
| --- | --- | --- |
| 09-03~05 | 提交基线清洗 | Gate A：参数一致性 |
| 09-05~10 | 3D FE Baseline | Gate B：模型可信 |
| 09-10~14 | 公平结构比较 | Gate C：六点验证 |
| 09-14~18 | 自适应跳焊 | Gate D：有效改善 |
| 09-18~22 | 多目标优化 | Pareto 前沿 |
| 09-22~26 | 反变形补偿 | 闭环验证 |
| 09-底 | V4 技术报告第一完整稿 | - |

---

## 最终提交前的 5 个"高奖门"

| Gate | 必须满足 |
| --- | --- |
| G1 题目响应 | 五个比赛维度都明确回答 |
| G2 主创新 | 至少 2 个创新有定量 baseline 对照 |
| G3 数值可信 | 核心 FE 收敛、BC、材料、热源清晰 |
| G4 证据完整 | 每个强结论都有 evidence ID |
| G5 盲审表现 | 3 分钟能看懂"问题—创新—结果—可信度" |

**五个都过，再谈 88-90。**

---

## 核心原则（重新确立）

1. ✅ 冻结 V4 主张
2. ✅ 先修提交物一致性
3. ✅ 再建立可信 3D baseline
4. ✅ 模型通过检查后，统一边界比较
5. ✅ **只有得到结果后，才允许更新论文中的创新结论**

**不要让论文提前写"已经验证的成果"，而实际上还是"计划中的创新"。**

---

## 关键文档索引

| 文档 | 路径 | 作用 |
| --- | --- | --- |
| **关键修正说明** | `docs/v4-key-corrections.md` | P0 修正详细说明 |
| **修正执行清单** | `docs/v4-correction-checklist.md` | 修正任务清单 |
| 执行摘要 | `docs/EXECUTIVE_SUMMARY.md` | 快速查阅 |
| V4 主线重构 | `docs/v4-mainline-refactor.md` | V4 详细计划 |
| 评审回应 | `docs/response-to-deep-review.md` | 完整回应 |
| **证据清单** | `evidence/claims.yaml` | 17 个主张状态 |
| V3 误差预算 | `docs/validation/position-error-budget-v3.md` | 双链预算 |

---

## 今日核心成就

### 1. 完成了 V3 P0 硬伤修复 ✅
- 消除了 3 个最易被评委抓到的硬伤

### 2. 完成了 V4 主线重构 ✅
- 从"六点柔顺已成立"转向"面向 Ø0.05 mm 的参数化协同优化"
- 四个创新点凝聚

### 3. 完成了 P0 关键修正 ✅
- H7/h6 表述纠正
- 误差预算状态修正
- 证据清单系统建立

### 4. 建立了清晰的执行路径 ✅
- Gate A/B/C/D 明确
- 时间节点清晰
- 文档追溯完整

---

## 最重要的认识

### 修正前
> "今天完成后项目 85 分，可以冲高奖了"

### 修正后
> "85 分是项目架构成熟度，当前真正 PDF 提交态 81-83 分。下一步不是继续加功能，而是先把 README 的 V4 叙事同步到技术报告，再建立可信的 3D FE baseline，只有得到结果后才允许更新论文中的创新结论。"

---

## 感谢

非常感谢二次深度评审的专业指导！

每一条建议都直击要害：
- ✅ 评分校准（85 分是开发成熟度，不是提交竞争力）
- ✅ H7/h6 表述纠正（定位间隙配合，非过渡配合）
- ✅ 误差预算状态修正（未闭合但方向正确）
- ✅ 证据清单系统（防止把计划当成果）
- ✅ 执行顺序修正（先修一致性，再建模型，再写结论）

**今日工作严格按照修正后的理解执行，取得实质性进展。**

---

**当前状态**：P0 关键修正完成，准备进入 technical-report-v4.md 建立阶段。  
**下一步**：建立 V4 技术报告，全面同步 V4 参数和主叙事。
