xianzai588/Hanjie/docs/v4-key-corrections.md

# V4 关键修正说明

**日期**：2026-09-03 下午  
**基于**：二次深度评审反馈

---

## 评分重新校准 ⚠️

### 修正前的误解
- ❌ "今日完成后项目评分 85 分"
- ❌ "现在直接提交就有 85 分竞争力"

### 修正后的正确理解
| 状态 | 评分 | 说明 |
| --- | ---: | --- |
| 项目架构/规划成熟度 | **85** | README、计划文档已 V4 |
| **当前真正 PDF 提交态** | **81-83** | ⚠️ 技术报告仍 V2 |

**核心认识**：
- **85 分是项目开发状态评分，不是当前 PDF 提交竞争力**
- 比赛是盲审无答辩，评委只看最终 PDF
- README = V4，但技术报告 = V2（最大不一致）

---

## P0 关键修正（已完成）

### 1. H7/h6 表述纠正 ✅

**错误表述**：
> "H7/h6 过渡配合"

**正确表述**：
> "H7/h6 为定位间隙配合（locational clearance fit），非过渡配合。采用小间隙精密定心设计，名义径向间隙约 0.02 mm。"

**修正依据**：
- H7/h6 属于定位间隙配合
- H7/k6、H7/m6 才是过渡配合
- 当前设计本质是小间隙精密定心

**已修改文件**：
- `docs/05-design-assumptions.md`
- `evidence/claims.yaml`

---

### 2. 误差预算"未闭合"事实修正 ✅

**错误表述**：
> "误差预算硬伤已修复"

**正确表述**：
> "误差预算口径已修正（装配链/自动化链分离），但当前最坏情况预算尚未闭合（0.035 > 0.025），成为 V4 重点优化约束。"

**当前状态**：
- V3 装配链合计：**0.035 mm**
- 目标：**0.025 mm**
- 差值：**0.010 mm**
- 状态：**未闭合**

**V4 目标分配**（设计指标，待验证）：

| 项目 | V4 目标 (mm) | 依据 |
| --- | ---: | --- |
| A/B 基准建立 | ≤0.004 | 精密装夹基准 |
| 定位夹具 | ≤0.004 | 锥形心轴自动找正 |
| 初始装配 | ≤0.003 | 小间隙精密定心 |
| 焊接变形 | ≤0.011 | 柔顺结构+自适应跳焊 |
| 松夹回弹 | ≤0.003 | 可释放夹具 |
| **合计** | **≤0.025** | 闭合目标 |

**关键认识**：
- 这不是硬伤，是优化方向
- 误差预算反而成为四个创新点的顶层约束
- 必须回答"为什么能做到这些目标"

**已修改文件**：
- `docs/validation/position-error-budget-v3.md`
- `evidence/claims.yaml` (CLAIM-060/061)

---

### 3. 证据清单系统建立 ✅

**目的**：
- 防止把"计划中的创新"误写成"已经验证的成果"
- 明确每个主张的证据来源、置信度和发布状态

**已建立文件**：
- `evidence/claims.yaml`（17 个核心主张）

**关键主张状态**：

| 主张 | 状态 | 置信度 | 发布状态 |
| --- | --- | --- | --- |
| 六点柔顺降低位置度 | unresolved | low | hypothesis |
| 温度门控优于固定S3 | untested | hypothesis | proposed |
| 反变形补偿有效 | untested | hypothesis | proposed |
| Pareto前沿 | planned | to_be_determined | proposed |
| 二维FE | qualified | low | preliminary_model |
| 误差预算闭合 | not_closed | needs_optimization | optimization_target |

**发布规则**：
- `hypothesis` / `proposed` 必须用"提出"、"设计"、"构建"
- `unresolved` / `untested` 不能写"验证"、"证明"、"表明"
- `digital_prototype` 必须注明"数字样本"
- `preliminary_model` 必须注明局限性
- `pending` 必须写"待验证"或完全不提

---

## 下一步最关键的工作

**不是**：
- ❌ 继续写温度门控代码
- ❌ 继续加功能
- ❌ 追求更多创新点

**而是**：

### 1. 建立 technical-report-v4.md（本周）⏳

**目的**：把"V4 规划"变成"V4 可提交证据"

**结构**：
```
deliverables/report/
├─ technical-report-v2.md       # 冻结历史
├─ technical-report-v4.md       # 新主稿
├─ build_technical_report_v4.py # 新生成器
└─ figures-v4/                  # 新图集
```

**必须同步**：
- R74.98 小间隙精密定心（非 R73.8）
- 锥形心轴 1:50（非 Ø39.96 销）
- V3 误差预算（未闭合但方向正确）
- V4 主叙事和四个创新点
- 所有"尚未实现的创新"标为 `proposed / to-be-verified`

**新论文结构**（8 章）：
1. 问题分析与设计目标
2. 异种材料焊接性与工艺选择
3. 参数化接头与夹具设计
4. 热—结构协同模型
5. 结构与工艺优化结果
6. 自适应跳焊与补偿
7. 自动化与质量闭环
8. 可靠性与证据边界

---

### 2. 建立 3D FE Baseline（9月5-10日）⏳

**只完成一个模型**：
- Continuous（连续座体）
- Rigid fixture（刚性夹具）
- S3 顺序
- Baseline 工艺参数

**必须交付**：
- 真正 3D 壳体 + 轴承座
- 温度相关材料参数
- 移动热源（Goldak/高斯）
- 热-弹塑性顺序耦合
- 完全冷却后松夹
- 拟合 Ø40 孔轴线 → 位置度
- **网格收敛性验证（变化 < 5%）**

**Gate B**：模型自己先站得住

---

### 3. 公平结构比较（9月10-14日）⏳

统一边界，只改变结构变量：
- Continuous（Baseline）
- 4-point
- 6-point
- 8-point

**Gate C**：六点到底是不是值得继续

**关键**：如果六点输，换方案，不要保六点。

---

## 执行时间表（修正后）

| 日期 | 里程碑 | Gate |
| --- | --- | --- |
| 09-03~05 | 提交基线清洗 | Gate A：参数一致性 |
| 09-05~10 | 3D FE Baseline | Gate B：模型可信 |
| 09-10~14 | 公平结构比较 | Gate C：六点验证 |
| 09-14~18 | 自适应跳焊 | Gate D：有效改善 |
| 09-18~22 | 多目标优化 | Pareto 前沿 |
| 09-22~26 | 反变形补偿 | 闭环验证 |
| 09-底 | V4 技术报告第一完整稿 | - |

---

## 最终提交前的 5 个"高奖门"

| Gate | 必须满足 |
| --- | --- |
| G1 题目响应 | 五个比赛维度都明确回答 |
| G2 主创新 | 至少 2 个创新有定量 baseline 对照 |
| G3 数值可信 | 核心 FE 收敛、BC、材料、热源清晰 |
| G4 证据完整 | 每个强结论都有 evidence ID |
| G5 盲审表现 | 3 分钟能看懂"问题—创新—结果—可信度" |

**五个都过，再谈 88-90。**

---

## 核心原则（重新确立）

1. ✅ 冻结 V4 主张
2. ✅ 先修提交物一致性
3. ✅ 再建立可信 3D baseline
4. ✅ 模型通过检查后，统一边界比较
5. ✅ **只有得到结果后，才允许更新论文中的创新结论**

**不要让论文提前写"已经验证的成果"，而实际上还是"计划中的创新"。**

---

## Git 提交记录（今日下午）

```
c8e3f2c [V4-P0] 关键修正：H7/h6表述+误差预算未闭合+证据清单
```

---

**状态**：P0 关键修正完成，准备进入 technical-report-v4.md 建立阶段。
