xianzai588/Hanjie/docs/EXECUTIVE_SUMMARY.md

# V4 升级执行摘要

**日期**：2026-09-03  
**当前状态**：V4 主线重构完成，评分从 78 → 85 分  
**目标**：V4 全部完成达到 88-90 分高奖竞争力

---

## 今天完成的工作 ✅

### 1. V3 P0 三项硬伤修复 ✅
- R73.8 → 74.98 mm（H7/h6 配合）
- Ø39.96 销 → 锥形心轴（定位重复性 0.008 mm）
- 误差预算拆分（装配链 / 自动化链）

### 2. V4 主线重构 ✅
- 主标题从"基于六点柔顺结构"改为"面向 Ø0.05 mm 位置度的热—结构协同优化"
- 六点柔顺降为"候选方案之一"
- 四个创新点重构：参数化优化、温度门控跳焊、反变形补偿、数字质量闭环

### 3. Git 提交记录 ✅
```
3754ded [V3-FIX-P0] 修复接头几何、夹具定位与误差预算三大硬伤
d4b270b [V3-DOC] 添加进度报告与刚度分析框架
39edc0d [V4-MAINLINE] 重构项目核心叙事
6689dde [V4-DOC] 对深度评审意见的完整回应
```

---

## 核心叙事（已确立）

> 以 Ø0.05 mm 位置度为直接设计目标，通过**参数化低拘束接头、热—结构鲁棒优化、焊前位姿补偿、焊中温度门控自适应跳焊和全过程质量追溯**，构建 QT450-10/Q235B 异种焊接的**三闭环数字工艺体系**。

---

## 四个创新点（已确立）

### 创新 1：参数化低拘束接头与热—结构协同优化 ⭐⭐⭐
- 多目标优化 → Pareto 前沿
- 六点处于"折中区域"，不说"最优"

### 创新 2：基于热状态反馈的自适应对称跳焊策略 ⭐⭐⭐
- 不是固定 S3，而是动态选择
- `next_segment = f(T₁..T₆, ΔT, P_predicted)`

### 创新 3：焊前位姿—焊后变形联合预测的轨迹/反变形补偿 ⭐⭐
- 视觉 + 预测 + 轨迹闭环
- `x_cmd = x_nominal - predict_shrinkage`

### 创新 4：基于过程数据和证据分级的一件一码数字质量闭环 ⭐
- I/U/v/T + anomaly + traceability
- 证据分级清晰

---

## 下一步行动（优先级）

### P0 级（本周必须）
1. ⏳ **3D FE 模型** — 最大技术短板
2. ⏳ **4/6/8/连续结构公平比较** — 支撑主创新
3. ⏳ **网格收敛性验证** — 可信度基础

### P1 级（2 周内）
4. ⏳ **温度门控自适应跳焊** — 主创新
5. ⏳ **焊前反变形补偿** — 闭环创新
6. ⏳ **参数化多目标优化** — Pareto 前沿

### P2 级（争取）
7. ⏳ **最小物理证据链** — 3 小试 + 1 硬度 + 1 温度
8. ⏳ **Evidence Manifest** — claims.yaml

---

## 关键文档索引

| 文档 | 作用 |
| --- | --- |
| `README.md` | 项目主页，已更新主线 |
| `docs/v3-fix-plan.md` | V3 总计划 |
| `docs/v3-progress-report.md` | V3 进度报告 |
| `docs/v4-mainline-refactor.md` | V4 主线重构详细计划 |
| `docs/response-to-deep-review.md` | 对评审意见的完整回应 |
| `docs/validation/position-error-budget-v3.md` | V3 误差预算（装配链/自动化链） |
| `simulation/results/stiffness-comparison-framework.md` | 刚度对比框架 |

---

## 评分进展

| 阶段 | 分数 | 状态 |
| --- | ---: | --- |
| V2 起点 | 78 | ✅ |
| V3 P0 修复 | 83 | ✅ |
| **V4 主线重构** | **85** | **✅ 当前** |
| V4 + 3D FE | 86-87 | ⏳ |
| V4 + 温度门控 | 87-88 | ⏳ |
| V4 全部完成 | 88-90 | 🎯 目标 |
| V4 + 实物 | 90-92 | 🎯 最佳 |

---

## 时间节点

| 日期 | 里程碑 | 状态 |
| --- | --- | --- |
| 09-03 | V3 P0 + V4 主线 | ✅ |
| 09-10 | 3D FE + 公平比较 | ⏳ |
| 09-17 | 温度门控跳焊 | ⏳ |
| 09-24 | 反变形 + Pareto | ⏳ |
| 10-01 | 实物小试（如果可能） | ⏳ |
| 10-08 | 证据清单 + 内部评审 | ⏳ |
| 10-20 | 学校报名截止 | 🎯 |
| 10-25 | 作品提交截止 | 🎯 |

---

## 核心原则

1. ✅ 不推翻重做，在当前基础上升级
2. ✅ 做强证据，凝聚创新
3. ✅ 保持技术诚信和证据分级
4. ✅ 从"数字内容多" → "机理驱动、可验证"
5. ✅ 不追求"看起来厉害"，追求"站得住"

---

## 关键引用

> "六点柔顺现在没资格承担整个项目成败。" — 评审核心判断

> "一个收敛的三维热—弹塑性模型，比现在继续增加 50 个二维算例更值钱。" — 评审关键建议

> "3 个小试 + 1 条硬度 + 1 条温度，对比赛可信度的提升，可能比增加十个 AI 功能都大。" — 评审优先级指导

---

**状态**：V4 主线重构完成，正在向 88-90 分高奖竞争力推进。
