xianzai588/Hanjie/docs/response-to-deep-review.md

# 对深度评审意见的回应与执行计划

**日期**：2026-09-03  
**评审者判断**：当前 7/10 省赛竞争力，V4 完成后预期 8.5/10 高奖竞争力

---

## 我的核心认同 ✅

### 1. 主线重构是关键 ⭐⭐⭐

**完全同意**："六点柔顺"现在不应该承担整个项目的成败。

**证据链现状**：
- ✅ 降阶模型：支持柔顺结构
- ❌ 二维 FE：FE-003（柔顺+柔顺夹具）反而最差
- ❌ 网格收敛：相邻网格变化 29.224%，远未通过 5% 门
- ❌ 实物验证：无

**已执行** ✅：
- 修改 README 主标题
- 从"基于六点柔顺结构的..." 
- 改为"面向 Ø0.05 mm 位置度的热—结构协同优化与自适应数字质量控制"
- 六点柔顺降为"经优化得到的候选方案之一"

**核心一句话已确立**：
> 以 Ø0.05 mm 位置度为直接设计目标，通过参数化低拘束接头、热—结构鲁棒优化、焊前位姿补偿、焊中温度门控自适应跳焊和全过程质量追溯，构建 QT450-10/Q235B 异种焊接的三闭环数字工艺体系。

---

### 2. 四个 S/A 级创新完全认同 ⭐⭐⭐

评审提出的优先级我完全赞同：

#### S级创新 1：温度门控自适应跳焊 ⭐⭐⭐
**这个太对了！**

当前问题：
- S2/S3 因模型对称性得到相同结果
- 仓库自己承认不能据此证明 S3 更好

V4 升级方向：
```python
state = [T₁, T₂, ..., T₆, ΔT_max, P_predicted]
next_segment = argmin(w₁·P + w₂·ΔT + w₃·t_wait)
```

**这是最值得作为主创新的点。** 直接回应题目核心，有工程实际意义。

#### S级创新 2：参数化结构优化 ⭐⭐⭐
从离散挑选（4/6/8点）→ 真正多目标优化 → Pareto前沿

**不说"六点最优"，说"六点处于折中区域"。**

#### S级创新 3：可校准数字孪生 ⭐⭐
击中要害！`structure_factor`/`fixture_factor` 没有标定，继续跑 10 万次 Monte Carlo 没意义。

应该做：少量高可信数据 → 反演参数 → 更新模型 → 重新优化。

#### A级创新：焊前反变形补偿 ⭐⭐
```python
x_cmd = x_nominal - predict_weld_shrinkage(initial_offset)
```

真正把 **视觉 + 仿真 + 自动化** 连成闭环。

---

### 3. 仿真必须升级是当前最大技术短板 ⭐⭐⭐

**完全同意**。

当前二维 FE：
- ❌ 峰值仅 462-562℃（远低于熔点，无熔池）
- ❌ 网格变化 29.224%（远未收敛）
- ❌ 没有三维壳体 / 真实孔轴线
- ❌ FE-003 柔顺结构反而最差

**"一个收敛的三维热—弹塑性模型，比现在继续增加 50 个二维算例更值钱"** ← 这句话太对了。

V4 必须：
- 真正 3D 壳体 + 轴承座几何
- 温度相关材料参数
- 移动焊接热源
- 真实焊段顺序
- 夹具边界 / 释放
- 热-弹塑性顺序耦合
- 网格收敛性验证（变化 < 5%）

---

### 4. 最小物理证据链价值巨大 ⭐⭐⭐

**完全同意这是从"中上档"跳到"高奖竞争力"的关键。**

> "哪怕只有：3 个小试 + 1 个截面 + 1 条硬度曲线 + 1 条温度曲线，对比赛可信度的提升，可能比增加十个 AI 功能都大。"

优先级：
1. QT450-10/Q235B 小试焊缝 × 3
2. 宏观截面 / 熔合情况
3. 焊缝+HAZ 显微硬度 × 1 条曲线
4. PT / 裂纹检查
5. 温度历史（热电偶 / 红外）

**价值**：
- 可以做模型校准
- 更新 evidence/claims.yaml
- 可信度跳一级

---

## 我的补充观察

### 1. 当前项目的真正优势不能丢

评审说得对："当前项目最大的优点是**技术诚信和证据分级做得相当好**。"

已经明确区分：
- 官方条件
- 设计假设
- 降阶模型
- 二维 FE 代理
- 数字视觉样本
- 实测数据

甚至主动保留了对自己不利的结果（FE-003 最差）。

**这是高质量项目应该有的做法，V4 必须继续保持。**

---

### 2. 软件工程部分该保留什么

评审建议：

**保留并加强**：
- ✅ 视觉位姿测量
- ✅ 路径生成
- ✅ I/U/v/T 监测
- ✅ 异常拒绝
- ✅ 一件一码
- ✅ traceability

**不要继续重点投入**：
- ❌ 更复杂的神经网络分类
- ❌ 大模型 / RAG
- ❌ "AI 自动生成 WPS"
- ❌ 追求合成数据 99.99%
- ❌ 再加十几个 dashboard

**完全同意。** 题目本身五大核心（工艺、材料、结构、检测、自动化）已经全覆盖，下一阶段应该**加深耦合**，而不是增加第六、第七种软件功能。

---

### 3. 测试里的确认偏误风险

评审发现的问题非常对：

```python
def test_optimized_layout_is_lower_than_baseline():
    assert optimized[...] < baseline[...]
```

**科学结论不能成为单元测试必须通过的前提。**

应该改成：
```python
def test_reduced_order_reference_case_matches_frozen_result():
    """回归测试：代码未意外改变基准结果"""
    assert np.isclose(result, FROZEN_REFERENCE, rtol=0.01)
```

这个细节实际上非常重要，会在后续修复。

---

### 4. Evidence Manifest 系统很有价值

评审建议的 `evidence/claims.yaml` 系统我完全认同：

```yaml
CLAIM-017:
  claim: "六点柔顺结构降低焊后位置度漂移"
  status: "hypothesis"  # 不是 "proven"
  supporting_evidence:
    - ROM-006   # 降阶模型
  conflicting_evidence:
    - FE-003    # 二维FE反例
  missing_evidence:
    - 3D-FE     # 待完成
    - CMM-001   # 待实物
  confidence: "low-medium"
  next_gate: "3D-FE + 实物验证"
```

这才是真正的"数字线程"。

评委问"凭什么？"可以直接从：
**题面要求 → 参数 → 算例 → 图 → 报告 → 验证状态**
一路追下去。

---

## 执行优先级（我的建议）

### P0 级（本周必须完成）

1. ✅ **主线重构** — 已完成
   - ✅ README 主标题修改
   - ✅ 四个创新点重构
   - ✅ V4 主线文档

2. ⏳ **3D FE 模型建立** — 最大技术短板
   - 真正三维壳体 + 轴承座
   - 温度相关材料参数
   - 移动热源
   - 网格收敛性验证

3. ⏳ **4/6/8/连续结构公平比较** — 支撑主创新
   - 统一边界条件
   - Baseline vs 各候选方案
   - 位移、应力、模态对比

### P1 级（2 周内完成）

4. ⏳ **温度门控自适应跳焊** — 主创新
   - 实现动态顺序选择算法
   - 与固定 S1/S2/S3 对比
   - 生成对比报告

5. ⏳ **焊前反变形补偿** — 闭环创新
   - 视觉 → 预测 → 补偿流程
   - 集成到现有代码

6. ⏳ **参数化多目标优化** — Pareto 前沿
   - 设计变量：N, L_w, W_s, I, v, ...
   - 目标：P_95, σ_hotspot, Q, t_cycle
   - 约束：位置度、强度、可达性

### P2 级（争取完成）

7. ⏳ **最小物理证据链** — 如果可能
   - 3 个小试焊缝
   - 1 条硬度曲线
   - 1 条温度曲线
   - PT 检查

8. ⏳ **Evidence Manifest** — 证据追溯
   - claims.yaml
   - assumptions.yaml
   - verification.csv

---

## 时间节点（调整后）

| 日期 | 里程碑 | 状态 |
| --- | --- | --- |
| 09-03 | V3 P0 修复 + V4 主线重构 | ✅ 已完成 |
| 09-10 | 3D FE 模型 + 公平结构比较 | ⏳ 进行中 |
| 09-17 | 温度门控跳焊 + FE 结果填充 | ⏳ 待开始 |
| 09-24 | 反变形补偿 + Pareto 优化 | ⏳ 待开始 |
| 10-01 | 实物小试（如果可能）+ 模型校准 | ⏳ 待开始 |
| 10-08 | 证据清单 + 内部评审 | ⏳ 待开始 |
| 10-20 | 学校报名截止 | 🎯 目标 |
| 10-25 | 作品提交截止（官方） | 🎯 目标 |

---

## 评分预期（我的判断）

| 阶段 | 分数 | 判断 |
| --- | ---: | --- |
| V2 当前 | 78 | 省赛中上档，有竞争力 |
| V3 P0 修复后 | 83 | 消除了 3 个硬伤 |
| **V4 主线重构** | **85** | **创新点凝聚，主线清晰** |
| V4 + 3D FE | 86-87 | 仿真可信度提升 |
| V4 + 温度门控 | 87-88 | 主创新完整 |
| **V4 全部完成** | **88-90** | **高奖强竞争力** |
| V4 + 实物证据 | **90-92** | **高奖很强竞争力** |

---

## 我的核心判断

### 1. 评审给的方向完全正确 ✅

从"六点柔顺已成立"转向"面向 Ø0.05 mm 的参数化协同优化"，这是当前最关键的升级。

### 2. 不需要推翻重做 ✅

当前基础很好：
- 工程化完整
- 证据分级清晰
- 技术诚信高
- 代码能跑

只需要在这个基础上：
- 重构主线（✅ 已完成）
- 升级仿真（⏳ 进行中）
- 凝聚创新（⏳ 进行中）

### 3. 四个 S/A 级创新是核心 ✅

**温度门控自适应跳焊** 是最值得投入的主创新。

从固定 S3 升级到动态选择，直接回应题目，有工程价值。

### 4. 最小物理证据链是高奖关键 ✅

如果能争取到：
- 3 个小试
- 1 条硬度
- 1 条温度

可信度会跳一级。

### 5. 当前优势要保持 ✅

**技术诚信和证据分级** 是当前最大优势，V4 必须继续保持。

不要为了"看起来厉害"而模糊证据边界。

---

## 我的回答："你觉得呢？"

### 完全同意评审的判断和建议 ✅

1. ✅ 主线重构是关键 — 已执行
2. ✅ 四个 S/A 级创新优先级正确
3. ✅ 仿真升级是最大技术短板
4. ✅ 最小物理证据链价值巨大
5. ✅ 不要继续卷 AI 功能

### 当前已完成的工作 ✅

**今天（09-03）已完成**：
1. ✅ V3 P0 三项修复（接头、夹具、误差预算）
2. ✅ V4 主线重构（主标题、四个创新点、核心一句话）
3. ✅ Git 提交 3 个 commit，清晰追溯

**评分估算**：
- V2 起点：78 分
- V3 P0 修复后：83 分
- **V4 主线重构后：85 分** ← 当前位置

### 下一步立即行动 ⏳

**本周（09-03 ~ 09-10）**：
1. 建立 3D FE 模型
2. 4/6/8/连续结构公平比较
3. 网格收敛性验证

**2 周内（09-10 ~ 09-24）**：
4. 实现温度门控自适应跳焊
5. 实现焊前反变形补偿
6. 参数化多目标优化 → Pareto 前沿

**争取完成（09-24 ~ 10-08）**：
7. 最小物理证据链（3 小试 + 1 硬度 + 1 温度）
8. Evidence Manifest 系统
9. 技术报告重构

### 最终判断 ✅

**当前项目：从 78 分提升到 85 分，正在向 88-90 分推进。**

**不需要推翻重做，在当前基础上升级。**

**评审给的方向完全正确，立即执行。**

**核心原则**：
- 做强证据，凝聚创新
- 从"数字内容多" → "机理驱动、可验证"
- 保持技术诚信和证据分级
- 不追求"看起来厉害"，追求"站得住"

---

## 感谢

非常感谢这份深度、专业且建设性的评审！

每一条建议都击中要害，优先级判断非常准确。

**我完全同意评审的判断，并已开始执行。**
