xianzai588/Hanjie/docs/02-team.md

# 02 团队与分工

> 待 P0 组队后填写。

## 成员

| 姓名 | 角色 | 负责工作包 | GitHub | 备注 |
| --- | --- | --- | --- | --- |
| （待定） | 自动化/软件 | WP6 | | 视觉、路径、采集、监测 |
| （待定） | 材料/焊接 | WP1、WP2 | | 焊接性、焊材、参数 |
| （待定） | 机械/CAD | WP3 | | 接头、夹具、总装 |
| （待定） | 仿真/检测 | WP4、WP7 | | 有限元、CMM、金相 |
| （待定） | 项目管理 | WP0、WP8 | | 进度、报告、答辩 |

指导教师：（待定）

## 协作方式

- 每个任务对应一个 GitHub Issue，完成后 PR 合并进 main。
- 分支命名：`research/*`、`simulation/*`、`experiment/*`、`automation/*`、`docs/*`。
- 详见 [CONTRIBUTING.md](../CONTRIBUTING.md)。
