xianzai588/Hanjie/deliverables/submission/提交说明.txt

COMPETITION-R3 技术包（焊接固定题）
论文（说明书＋设计图集）共16页：第1～8页为说明书正文，第9～16页为横版设计图 HJ-001～008。STEP为名义装配包络。
本包为纯数字设计作品：几何来自真实BREP，全部数字结果由经典公式计算、局部热模型诊断与公差预算给出，正文显式区分计算结果与设计目标；说明书§7列出设计放行顺序与试制工程确认要求。
工艺体系：八段两道脉冲TIG、Ni99预制隔离层＋NiFe55填充、铸铁冷焊（不预热、层间≤100 ℃）、热态轻击；整件热结构结果与能量历史在08号文件，冶金适用域声明见19～21号。
复现需完整项目及Python依赖，在项目根目录运行 python deliverables/build_submission.py。
校方另附真实报名表、推荐与盖章汇总表；固定命题作品详细描述按附件填‘无’。
截止时间与命名按官方原件及后续通知执行。
