xianzai588/Hanjie/deliverables/process/cold-weld-and-peening-card.md

# 冷焊与热态轻击专项卡

执行HJ-W-01。组焊不预热，层间≤100℃；纯镍隔离层制作在最终孔精加工之前。不得以r·α·ΔT推算孔轴偏移；全件位置度读取冷却卸夹后的有限元拟合结果。

停弧后用校准红外测温（首件与接触热电偶对比发射率）确认焊道400～500℃，只敲熔敷金属中部，避开焊趾、熔合线和QT侧HAZ。Ø8圆头锤，气压0.2～0.4 MPa，2000～3000次/min；重叠≥75%，压痕≤0.05 mm，无撕裂/剥离。未处于温度窗口则跳过、记录，不强行再热。

锤击作用是局部塑性延展、缓解收缩拉应力。设计计算不计锤击带来的强度、疲劳或位置度收益，也不宣称全熔合线转为压应力。首件按焊道中部/两侧HAZ分区测残余应力与金相，保持截面证据。

单段：温度和安全信号有效→18 mm焊接约10.91 s→收弧→测温轻击/记录跳过→局部抽吸刷净→转位。两道×八段共16段次。下道或下段测点超温必须等待；这段等待计入实际节拍。
