xianzai588/Hanjie/docs/review/competition-r2-independent-self-audit-2026-10-02.md

# COMPETITION-R2 独立自审：比赛要求、计算与工艺可执行性

审核日期：2026-10-02。对象为当前提交包，说明书29页、图集6页、ZIP内25个文件。

**审核结论：上一轮“完整修复”的判断不成立。当前完成了部分版本、图注和表述修正；位置度、冶金、防裂、疲劳和自动化执行的关键证据仍有缺口，并存在确定的算术与参数矛盾。当前稿不宜作为已经完成技术验证的定稿提交。**

本次重新阅读官方题面，逐页浏览35页PDF，并核对正文源文件、工艺卡、配置、原始结果和关键计算程序。没有以旧审稿意见、摘要措辞、软件测试数量或“design_verified”字段作为达标依据。独立重算未调用项目的工艺核算函数；气幕互锁另提取原判定函数检查。审核未修改参赛正文、图纸、配置和提交包。

优先级：P0直接影响核心设计结论；P1影响可制造性、检测与论证可信度；P2为基础一致性和表达问题。这是修复优先级，不是官方分数或取消资格判定。

## 一、先查基础与比赛要求

### 1. 官方要求的适用范围

原件：[大赛实施方案](E:/AI/bisai/Hanjie/competition/original-files/welding/第一届辽宁省大学生材料焊接与铸造工艺设计大赛实施方案.pdf)。

- 第3页给定Q235B、壳体Ø160×200×5、QT450-10、Ø40轴承孔、焊后孔轴位置度≤Ø0.05，以及不得有可能落入内腔的焊渣或飞溅物。当前材料和基本尺寸对题，五个官方维度均有章节覆盖。
- 第5页允许项目研究报告、设计图或实物，固定题说明书格式及篇幅不受限制。无实物路线有依据；文件没有明确承诺“无实物绝不扣分”，也没有公布数值评分权重。
- 第6页的匿名、自编代码、规定封面与PDF命名条款位于“铸造工艺设计赛道”。不能直接把它们说成焊接固定题的官方格式硬门槛。本仓库AGENTS另行要求匿名和真实代码，仍应执行。
- 第7页公布省一、二、三等奖；本项目“特等奖”目标不能作为官方奖项设置引用。
- 第7～8页要求学校推荐，10月20日前报名、10月25日含当日提交。技术ZIP不能替代真实报名、推荐和盖章汇总材料；后续通知还需由校方核对。

### 2. 基础缺陷清单

| 编号 | 优先级 | 位置与确定问题 | 应完成的修正 |
| --- | --- | --- | --- |
| B1 | P2 | 说明书封面、页脚和图纸仍用COMPETITION-R2。它是项目版本号，不能当作与报名一致的真实自编代码。 | 保留版本管理用途；最终封面按实际参赛信息替换。不能编造代码，也不把铸造模板误套到焊接固定题。 |
| B2 | P2 | 说明书第4页工艺比选的四个加权总分全部算错。按表中权重与分数，依次应为6.80、6.15、7.10、8.40，现写6.25、6.05、7.05、8.35。 | 纠正算术，给每个分值来源或评分锚点。排序未改变，但该表尚不能证明TIG在工程上综合最优。 |
| B3 | P1 | 第6、12页8P条件所需许用应力写42.44 MPa；第13页、正文公式与原始比较结果写39.13 MPa。 | 明确焊脚、效率、载荷等输入，一组输入只保留一个值。 |
| B4 | P1 | 06号工艺卡同时规定焊前孔加工到最终Ø40H7（40.000～40.025），又保留单边0.010～0.015珩磨量。若从上限执行最大精整，孔径可到40.055。 | 明确焊前、焊后、最终孔径链与精整触发条件；焊后位置度应在精整前独立证明，尺寸精整不能承担孔轴纠偏。 |
| B5 | P1 | 图集是有用的设计示意，但尚未形成完整制造图：若干尺寸只在旁注中，缺少完整零件尺寸链、关键形位框、铜环分体接缝/隔离垫/气路详图。06号卡偏方案汇总，缺逐道截面、焊接位置、起停程序和一致的可执行参数范围。 | 补成可据以加工装配和施焊的工程图与pWPS。设计阶段可以没有已评定PQR，但应清楚区分pWPS与评定后的生产WPS。ISO 15609-1规定电弧焊WPS的内容要求，不能由一张接头示意图代替完整规程。[标准说明](https://www.iso.org/standard/75556.html) |
| B6 | P2 | 00导航仍指向不存在的“08-R1单段热诊断.json”；实际名为“08-冻结单段热诊断（历史附件）.json”。第21页称07号含温度相关材料参数表，但07没有该表，04输入快照也未包含materials.yaml。 | 修正导航，交付真实材料表及来源，确保评委能复算核心模型。无需增加哈希工作。 |

PDF总体可读，未发现大面积字符丢失或表格裁切；但没有独立目录，第3、20页等留白较大，图示在正文中偏小。先解决技术闭环，再整理目录和版面。当前两份PDF元数据未显示参赛学校、学生或导师身份。

## 二、审查理论、数值与文献依据

### T1｜P0：Ø0.05没有得到整件焊后残余变形的计算证明

第1、2、18页承认0.008 mm是热残余分配目标；第21页又写“由本节给出的求解方案与输入清单升级为数值计算结果”，并断言三条控形路径“共同把热残余限制在0.0102 mm门限以内”。该节实际给出的是Sysweld/Simufact/Abaqus求解计划，没有四道、整件、夹具接触及卸夹后的结果。

[precision_budget程序](E:/AI/bisai/Hanjie/src/hanjie/domain/competition_design.py:58)只相加分配值，却在第70行附近直接返回`thermal_residual_design_verified: True`；04、05附件和manifest因此出现“验证完成”字段。程序没有读取热残余计算值。0.0456 mm预算与0.0044 mm余量的加法成立，实际残余变形尚未由此证明。其他工装分项也包含设计分配，不能全部当作已证实的能力。

[历史热诊断输入](E:/AI/bisai/Hanjie/simulation/thermal-ref/results/competition-r2/r1-singlepass/run-inputs.json)的初始温度是150℃；结果最低温度141.16℃，历时60秒，四道整件适用性为false，热—结构允许标志为false。它不能证明当前20℃起焊、层间≤100℃的四道工艺窗口。432例固有应变响应的原始assessment也明确不是三材料整件瞬态热塑性求解。

**修复完成条件：**在当前几何、四道时序、材料温度相关参数和工装约束下，完成热—弹塑性计算及冷却卸夹；按同一A/B基准拟合孔轴，给出残余位置度、孔径/圆度、槽根/焊趾应力云图及基本网格独立性。真实数值决定6P或8P，不能通过改验证标志或降低措辞替代。

### T2｜P0：把自由径向热膨胀换算成孔轴偏心，物理量错位

[正文第205～207行](E:/AI/bisai/Hanjie/deliverables/report/technical-report-v4-unified.md:205)以`r·α·ΔT`得到31.7 K对应0.025 mm，进而称它达到整个位置度指标。该公式计算径向长度变化，不直接计算孔轴相对基准的偏移。

独立反例：轴对称环件发生0.025 mm均匀径向膨胀，孔半径变化而孔心仍在原轴线上；数值采样拟合中心偏移约8×10⁻¹⁶ mm。周向对称但径向不均匀的温度场也不必产生横向轴心漂移。纯弹性热胀冷却后还可恢复，不能把瞬态伸缩直接当作残余量。

因此，40.94 kJ预热蓄热和0.0630 mm自由协调量的算术可以保留；“降低整件温度就是降低梯度”“位置度预算不允许预热”“31.7 K直接耗尽位置度”均没有成立的推导。TWI说明预热可减缓冷却、抑制硬化并分散收缩应力；其球铁温区随基体组织变化，铁素体球铁可含室温起焊，珠光体球铁建议更高温度。不能据此断言本件必须预热，也不能忽视预热收益。[TWI铸铁焊接资料](https://www.twi-global.com/technical-knowledge/job-knowledge/weldability-of-materials-cast-irons-025)

**修复完成条件：**分别定义孔径、圆度、孔轴偏移/倾斜与残余位移；用周向非均匀热场、塑性和卸夹过程比较热制度。保留不预热主案时，必须给出相应冶金与控形证据。

### T3｜P0：相图表述收紧了，图形与判据仍非真实Schaeffler分区

第7～8页图2把Ni_eq=12和16画成水平相界；[分类函数](E:/AI/bisai/Hanjie/studies/SCHAEFFLER-MAP/run.py:107)接收Cr_eq却完全不使用它，绘图仅按Ni_eq涂三条水平带。这是自设的一维分类，不能标成标准相图分区或标准边界余量。

制造商原始技术手册第3-7页图2.3给出依赖Cr、Ni两个当量的Schaeffler分区，具有斜向边界和多相区；图的坐标显示范围也不同于本文。[Kobelco原始图与说明](https://www.kobelco-welding.jp/images/education-center/pdf/Specific_4Ed.pdf)

当前正文已承认Ni_eq 46～57超出常用图域，这一修正有必要；但第8页表格与19号JSON仍报告“边界余量30.2”，图中仍有“A+M边界Ni_eq=16”。README仍声称“稳居单相奥氏体区、余量≥30、淬硬与冷却速度无关”。这些内容互相抵触。

Q235B被写成“马氏体区、自回火软化”，不能据一个焊缝组织当量点判定母材供货组织。QT450-10的C=3.65%、Si=2.60%及11 vol%石墨是当前假定，未给出GB/T 1348具体条款或批次依据；Ms经验式也未说明对实际Ni约27.5～49.5%成分的适用范围。

**修复完成条件：**采用可追溯的原相图，标清图域和图外点；去掉自设相界与虚假余量。保留14例成分混合计算，另用适用于Ni–Fe–C体系的相平衡/凝固依据论证焊缝主体，并单独分析铸铁半熔化区、HAZ、碳化物和多道再热。后续道次即使不再熔化母材，也仍会传热；第10页“熔合线不再二次受热”需纠正。

### T4｜P0：锤击松弛拉应力的方向合理，“必然拉转压、消除裂纹”未得到证明

第11、27页与06/22号卡由假设塑性应变0.3%～0.8%乘室温E=190 GPa，得到570～1520 MPa，再以屈服封顶宣称整个熔合线稳定压应力且应变不确定性不影响结论。这不是完整残余应力求解。表面压痕不能直接确定塑性应变张量、影响深度、熔合线内部应力及后续三道再热后的状态。

TWI支持铸铁短焊道趁热锤击缓解收缩；它没有在该资料中给出本件400～500℃、低于300℃禁锤、气压/压痕组合和熔合线两侧各5 mm均可敲击的精确验证。引用[13]的钢/铝焊后疲劳改善方法不能自动成为NiFe/球铁热态锤击工艺的量化证据。IIW相关新研究也明确区分材料、接头、载荷与质量控制要求。[2025年IIW HFMI更新研究](https://link.springer.com/article/10.1007/s40194-024-01882-7)

“无焊剂+高纯氩即消除氢源”“剩下唯一因素是拉应力”也过度绝对：清洁、干燥和表面状态仍影响氢及缺陷。锤击范围进入球铁HAZ、表面压痕对焊趾的影响以及锤头进入内腔的可达性，均未闭合。

**修复完成条件：**保留热态轻击主案，给出与材料和接头匹配的依据、作用深度及多道再热后的应力评价；建立锤击器实际工具包络和温度测量方法。不能再由Eε一项算术推出全熔合线压应力。

### T5｜P0：疲劳“裕量1.21”不成立，8P的1.61同样受影响

第19页用静态载荷角点的等效应力52.17 MPa直接计算63/52.17=1.21。疲劳评定需要循环应力范围、应力分量、受力方向及对应焊趾/焊根细节；没有实际或明确假定的载荷历程，不能把静态结果直接当作Δσ。FAT63或80也不能仅按“纵向/横向角焊缝量级”选定。

TWI的疲劳设计研究明确以应力范围表达S–N类别，并按接头几何、载荷方向和失效部位选择类别。[TWI疲劳设计依据](https://www.twi-global.com/technical-knowledge/published-papers/fatigue-design-rules-for-welded-structures-january-2000) 当前IIW推荐第三版为Hobbacher与Baumgartner，2024年；稿中只链接IIW首页，未落实版次、条款和细节。[出版方记录](https://link.springer.com/book/10.1007/978-3-031-57667-6)

仅作概念反例：若52.17是一个单轴完全反向应力幅，范围应为104.34 MPa，63/104.34≈0.604；若它是R=0.1循环的最大单轴应力，范围为46.953 MPa。这两者都不是本件真实疲劳预测，只说明现有输入不足以确定裕量。当前静态等效应力还不能直接按这个单轴例子转换。

第20页“R=0.1、10⁷循环、≥3件”没设多个应力级、失效数据和统计方法，不能同时承诺得到S–N曲线斜率。[TWI疲劳数据分析指南](https://www.twi-global.com/pdfs/best-practice-guides/best-practice-guide-on-statistical-analysis-of-fatigue-data.pdf)

**修复完成条件：**定义载荷谱/设计循环数与Δσ、Δτ；给出适用细节和NiFe/球铁接头的证据，校核焊趾、焊根、段端及槽根。试验计划区分耐久验证与S–N拟合。重算后再制定8P切换，不能沿用现有1.21/1.61作安全储备。

### T6｜P0：固定送丝的数学闭合过窄，与选定装备不相容

在稿中四道、焊速1.5 mm/s、棒径1.6 mm、效率0.85～1.00、焊脚3.5～3.8 mm全部成立的前提下，独立按体积守恒重算：

`u_min = (3.5²/2)×1.5 / (4×0.85×π×1.6²/4) = 1.34396695 mm/s`

`u_max = (3.8²/2)×1.5 / (4×1.00×π×1.6²/4) = 1.34660003 mm/s`

允许窗口仅宽0.00263308 mm/s，约0.196%。第22页设备却写“送丝分辨率0.1 mm/s级”。若实际设1.3，效率0.85时等效焊脚3.442 mm，不足3.5；若设1.4，效率1.0时焊脚3.875 mm，超出3.8包络。1.343967的六位小数没有装备精度、棒径误差与焊速稳定性支撑。

**修复完成条件：**把供丝/焊速/棒径误差纳入窗口，调整最大成形包络、截面设计或供丝方案，给出能实际执行的公差。名义守恒成立不等于鲁棒工艺成立。

此外，“四道是守恒所必需”的论证不成立：相同简化模型下，两道配两倍送丝即可给出相同沉积面积。它是否能熔合、是否要改变电流须另论证；当前不能据此直接推荐两道，但必须把两道/脉冲路线纳入公平比较。

### T7｜P1：双工位9分钟是算术错误，18分钟工艺未完成优化

第11、22、26页给出弧燃288 s、锤击清理480 s、装夹300 s。串行合计1068 s=17.8 min；焊接与锤击清理仍在同一焊接工位，至少768 s=12.8 min，尚未计冷却、移枪、转位与检测。

装卸工位并行不能把焊接工位负荷从12.8 min自动变成9 min。采用两套焊接单元或跨件流水并行需要实际资源和时序图，稿中未给出。第11页“在线预热替代等待”还与当前“不预热”工艺直接冲突。

AGENTS已经明确要求直面慢速四道TIG的节拍代价。小批量定位可以解释设备投资，却不能证明该路线优于两道、脉冲或外塞焊。

**修复完成条件：**按资源约束画工序时间表，给出单件周期和产线节拍各自下界，计入温度等待。用可比成形/熔合质量、总热量和设备投入比较候选，取消无依据的9 min和10～12 min承诺。

### T8｜P0：8P不能作为“变形无代价”的无条件兜底

[正文第280行](E:/AI/bisai/Hanjie/deliverables/report/technical-report-v4-unified.md:280)从单段参数相同、代理敏感性不可分辨，推到8P沿用0.008 mm目标且变形无代价。但8P总热量由142.56增到190.08 kJ，增加33.3%，连接约束、热累积和卸夹响应均改变。

原432例结果的“不可分辨”表示该模型和误差范围不能支持排序，不表示两者工程等效。整体平均终温低于100℃也不能替代局部层间温度。

**修复完成条件：**6P与8P分别核算残余位置度、疲劳、工装和节拍；切换必须同时满足承载、控形、洁净与执行条件。不能仅放宽连接长度而自动宣布所有门槛通过。

## 三、审查工装、洁净和质量闭环

### T9｜P1：胀套只有理想力平衡，缺少足以支撑3 μm定心的刚度证据

第15页与图HJ-R2-006已给出锥角、接触带、槽、壁厚和回退方式，是有效设计进展。但17.63～39.01 N驱动力与0.221 MPa平均带压来自理想锥平衡，未包含开缝胀套弹性扩张消耗、孔端点接触、偏载、温升与卸夹恢复。限制驱动力不等于已达到规定直径和定心重复性。

**修复完成条件：**给出胀套力—位移、孔壁接触压力/变形和冷却卸夹计算；验证100 N限力与3 μm目标能同时成立，并明确机械限位和制造公差。图纸补完整轴向尺寸、槽端结构和装配尺寸链。

### T10｜P1：铜环/气幕比薄箔合理，但“洁净保证”仍缺工程量

第16～17页与图HJ-R2-004给出3 mm紫铜环、接料盘、底口退出，名义空间关系有依据。当前CAD的环外径Ø150，壳体最小内径也是Ø150；外缘再加低摩擦隔离垫时，没有垫厚、压缩量及热膨胀后的配合预算。整圈实心环和盘的几何检查不包含分体缝、隔离垫和真实气路。

底部环形进气槽没有画出与焊缝下缘连通的流道/喷孔尺寸。10～15 L/min若摊到Ø150全截面，平均速度约0.0094～0.0141 m/s；实际环形喷口速度应按喷口面积计算。这个量不能单独证明任意颗粒均不会下落。铜的高导热率也不直接给出热接触吸热量或循环散热能力。

TIG减少飞溅和焊渣来源，但锤击、层间机械清理、工具接触与铜环磨损仍是颗粒来源。第26页“TIG从源头消除颗粒”过度绝对。只写清点、内窥和颗粒计数，尚缺采样区域、盲区、提取方法、粒径/数量判据和检测下限。

**修复完成条件：**补热态配合、分体密封、气路与抽吸量平衡；明确收集与退出全过程的颗粒路径，给出可检查的洁净验收方案。需要用计算/设计证据支持屏障与气幕作用，不能只靠有流量信号。

### T11｜P1：检测名称列全了，适用范围和判废程序尚未落实

第24页写“表面与近表面裂纹用PT”。PT检测的是向表面开口的缺陷，不能覆盖封闭的近表面裂纹。[TWI渗透检测边界](https://www.twi-global.com/technical-knowledge/faqs/faq-what-are-the-advantages-and-disadvantages-of-penetrant-examination-in-non-destructive-examination-nde)

UT常规标准对象与本件差异显著：ISO 17640主要针对厚度≥8 mm、低衰减、铁素体全熔透接头；本件壳体5 mm、小角焊缝、球铁与NiFe界面。标准允许以专门规范定义D级特殊应用，故不能断言本件禁止UT；也不能仅引用标准名字就认为常规技术已适用。[ISO 17640范围与D级说明](https://www.iso.org/standard/75737.html)

图纸没有明确UT有效扫查面、探头频率/晶片/角度、同材料对比试块、覆盖区域、近场盲区和缺陷阈值。白口带≤0.2 mm、HV≤350是设计目标，需要给出依据及能分辨该窄带的硬度试验载荷、压痕间距和金相取样方案。不能用PT/UT排除“组织”的概念。

**修复完成条件：**按缺陷和组织分工，制定适用于真实接头的检测流程与明确判据；将生产可执行检测与破坏性工艺验证分开。PT清洗/去渗透液也应进入内腔洁净流程。

### T12｜P1：气幕缺信号仍可起弧，违反正文规定的硬联锁

[起弧函数第82行](E:/AI/bisai/Hanjie/src/hanjie/domain/competition_design.py:82)：`curtain_ok = curtain_flow_l_min is None or 10 <= curtain_flow_l_min <= 15`。其余输入有效时，气幕流量缺失返回True；显式流量0才拒绝。独立执行该判定得到：缺信号True、0 L/min为False、12 L/min为True。

正文第22页宣称气幕必须在10～15 L/min且缺信号不能通过。当前控制逻辑与保护要求相反，200例合成异常检测和测试全绿未覆盖这项工程失效。

**修复完成条件：**气幕测量缺失、非有限值、断线、低流量和越界均闭锁；连同锤击温度、回退与最高温度信号说明输入来源、失效状态和实际PLC动作。只需验证有实际意义的失效情景，无需扩张测试数量。

## 四、文献与证据等级的复审结果

参考[11]和[12]已通过Crossref原始元数据核实题名、作者、年份、卷和文章号，未发现这两篇被凭空编造：[2016年Metals论文](https://doi.org/10.3390/met6110283)、[2024年Scientific Reports论文](https://doi.org/10.1038/s41598-024-70050-0)。但其材料/焊材和工艺不等同本件，不能直接搬用为NiFe55/Q235B接头达标证据。本轮未取得可读全文，因此没有从它们推断具体工艺效果。

当前NiFe55产品页确有Ni55、C0.01、Si0.13、Mn0.70，以及Rp0.2 300 MPa、Rm450 MPa、A5 8%和Ø1.6实心棒；这些作为选材输入有公开依据。产品数据是典型熔敷金属性能，不能直接当作稀释后接头/HAZ性能。[Certilas供方资料](https://certilas.com/en/product/nife-55-tig)

正文“NiFe55供应商建议至少175℃”没有在所选Certilas页面定位到。若引用的是另一供方、另一产品，必须明确产品与工艺差异，不能合并成同一焊材的通用要求。Kobelco150～350℃表注明为低温预热SMAW，不能无说明直接套到TIG。

17号参数表把“0.008 mm目标/0.0102 mm上限”整体列为A类，混淆了可复核的预算反算与未验证的热残余能力；400～500℃、≥75%锤击参数列B类但没有精确出处。参考[7]应补实际版次与细节，[9]应补可追溯原图和完整书目信息，[10]不能将多项标准混成一个无版次条目。

需要建立逐项对应：文献支持哪一条机理，标准适用于什么对象，哪些数值是设计假设，哪些是已运行模型结果。无需把说明书改成期刊论文，也不能靠反复“待确认”维持未经证明的强结论。

## 五、哪些修正可以保留

1. 真实BREP、6P/8P/整圈几何、焊段长度与名义工装退出设计，是可继续使用的基础。
2. 四道名义沉积守恒、330 J/mm净热输入、142.56 kJ总热量和288 s弧燃时间，在列明输入下算术成立；需补工艺误差和装备匹配。
3. 0.0436/0.0456 mm预算与0.0102 mm热残余允许门限的反算成立；它们是分配与要求，不是焊后仿真结果。
4. 不再把历史单段诊断冒充整件四道结果、承认高Ni当量图外、将薄箔改为3 mm铜环，是正确方向；全文与附件没有完成一致落实。
5. 独立A/B基准、冷态CMM判定并计入不确定度，有工程意义；测量能力和夹具重复性仍需给出证据。

外部备份`E:/AI/bisai/Hanjie-backup-20261002-123827.zip`已确认存在，约1.10 GB。新渲染和独立算术记录存于项目外`E:/AI/bisai/Hanjie-audit-20261002/`，没有向参赛包加入审核材料。

## 六、按比赛价值排序的修复闭环

1. **先完成位置度主证据。** 修正径向膨胀与轴偏移语义；得到当前整件四道、冷却、卸夹后的真实结果与云图；同时核查槽、胀套的承载/控形折中。达到基本工程精度后固化，不无限调参。
2. **重做冶金和防裂证据。** 使用真实相图及适用的Ni–Fe–C依据，独立处理熔合线；保留有依据的热态轻击工艺，撤去Eε推出全界面压应力的跳跃。
3. **闭合可执行工艺。** 扩宽沉积/装备窗口，比较两道与脉冲/外塞焊，重算资源节拍；6P/8P切换要同时核查控形、承载、疲劳和洁净。
4. **补齐工程交付。** 制造图、pWPS、气路/热态配合、适用NDT、疲劳与洁净验收；修复缺信号气幕联锁。
5. **最后统一正文和附件。** 只让真实结果进入“验证完成”字段；纠正评分、42.44/39.13、孔径链、文件名和证据等级，按实际报名信息完成封面。

**最终判断：五个维度均有内容，但核心结论不能批准为“经理论与数值验证满足指标”的完成稿。下一轮需要补真实计算和可执行设计；仅继续润色、加免责声明或增加测试，都不能完成上述闭环。**
