xianzai588/Hanjie/docs/process/01-process-selection.md

# 工艺选型（WP2）

> 状态：V1 数字工程候选已收敛，主路线为**低热输入自动 TIG + NiFe-55 镍铁基填充 + 铸铁冷焊热制度**；CMT 与激光填丝作为对比路线保留。三方案的量化横向比选见 [process-selection-justification.md](process-selection-justification.md)，试制阶段按说明书 §9.2 的 V1～V10 完成工艺评定。
> 评分矩阵先保留在本文，作为比选过程的原始记录。

## 候选方案

| 方案 | 说明 |
| --- | --- |
| A | 激光 / 激光填丝焊 |
| B | CMT / 低飞溅脉冲 GMAW |
| C | 自动 TIG |

## 候选技术要点（V0.1 · 风险假设，待证伪）

> 下表是**假设清单**，不是结论。评价必须按证据链推进：
> **候选 → 风险假设 → 证据（文献 + 设备调查）→ 小试 → 评分**；禁止先给路线贴标签再找资料证明标签。
> 状态标注：技术预研版，须经材料老师审核。

| | A 激光/填丝 | B CMT/脉冲 MIG | C 自动 TIG |
| --- | --- | --- | --- |
| 假设优势 | 热输入最低、速度最快、变形最小潜力 | 低飞溅 + 低热输入，镍基焊丝可机械化送丝 | 技术最成熟，镍基铸铁焊材体系完整（焊条/填充棒路线），设备门槛低 |
| 风险假设（待证伪） | 冷却极快 → 球铁侧白口层风险；装配间隙要求高；镍基送丝难 | 镍基焊丝货源与送丝稳定性；设备依赖 | 热输入相对偏大，需小参数/多点分段压缩；节拍慢 |
| 飞溅/洁净度（假设） | 好 | 好（低飞溅是卖点） | 好（基本无飞溅） |
| 设备依赖（详见 [../03-equipment-inventory.md](../03-equipment-inventory.md)） | 激光器 + 送丝 + 机器人 | CMT/冷弧电源 + 机器人或变位机 | TIG 电源 + 变位机 |
| 决定性未知 | 球铁快冷白口（文献 + 小试） | ERNiFe-CI 丝材可购性与送丝 | 热输入-变形平衡（仿真 + 小试） |

## 评分矩阵（权重制）

> 「学校设备可实现性」一项在 09-01 设备调查（Gate 1）完成前**不得打分**；其余项在文献证据 + 第一轮小试完成前只允许填定性判断。

| 指标 | 权重 | A 激光/填丝 | B CMT | C 自动TIG |
| --- | ---: | --- | --- | --- |
| 接头可靠性 | 25 | | | |
| 热输入/变形控制 | 20 | | | |
| 裂纹/白口控制 | 15 | | | |
| 飞溅/洁净度 | 15 | | | |
| 自动化程度 | 10 | | | |
| 学校设备可实现性 | 10 | | | |
| 成本/节拍 | 5 | | | |
| **合计** | **100** | | | |

## 决策记录

| 日期 | 事项 | 结论 | 依据 |
| --- | --- | --- | --- |
| 2026-09-02 | 无设备条件执行收敛 | 自动 TIG + 镍基作为主候选；CMT/激光作对比 | E001–E004、数字仿真与设备边界 |
| 2026-08-30 | 建立候选与评分框架 | 三方案保留 | — |
| 2026-08-30 | 候选技术要点 V0.1 建立 | 不评分、不锁定；可实现性评分依赖设备调查 | Issue #4 / #2 |
| 2026-08-30 | V0.1 技术纠错 | 候选要点改为风险假设结构（证据链推进，防确认偏误）；删除绝对化表述；焊材牌号按方法分开管理 | 评审意见 |

## 里程碑

- 09-05：三方案 V0.1 对比完成
- 09-18：**Process Freeze V1**（锁定主工艺）
