xianzai588/Hanjie/simulation/fe3d/V4-EXEC-SUMMARY.md

# V4 执行摘要

**日期**：2026-09-05
**状态**：设计输入冻结；`fe3d.py` 为 surrogate prototype，真实 FE3D-BASE 尚未实施

---

## ⚡ 核心决策（一句话）

**完成 G0 证据纠偏；先建立真实 Baseline 数值可信度，Gate B.1 对当前代理不适用。**

---

## 📋 后续真实求解任务

**FE3D-BASE**：连续环形座体 + 刚性夹具 + S3 焊接顺序；当前仅有标签网格和预设响应演示

---

## 🚫 禁止项（真实 Gate B 通过前）

- ❌ 4/6/8 点结构优化
- ❌ 柔顺夹具对比
- ❌ Pareto/自适应跳焊/反变形补偿
- ❌ 任何结构参数扫描
- ❌ 修改验证协议判据（结果后）

---

## ⏳ Gate B 验证门（当前未执行）

| Gate | 判据 | 阈值 |
| --- | --- | ---: |
| **B.1 网格收敛** | 位置度 P | < 5% |
|  | 峰值温度 T_peak | < 10% |
|  | 最大应力 σ_eq_max | < 15% |
| **B.2 热场合理性** | 峰值温度 | 1300-1600°C |
|  | HAZ 宽度 | 3-10 mm |
| **B.3 边界条件** | 夹具约束清单 | 完整 |
|  | 释放时机 | 50±5°C |
| **B.4 材料参数** | 温度相关性 | 单调合理 |
|  | 来源标注 | 清晰 |

当前代理输出不能使上述任一门通过；能量平衡未计算，保持空值。

---

## 📁 关键文件

| 文件 | 用途 |
| --- | --- |
| `simulation/fe3d/README.md` | 导航入口 |
| `simulation/fe3d/design-inputs-frozen-v4.md` | 设计输入（冻结） |
| `simulation/fe3d/FE3D-BASE-verification-protocol.md` | 验证协议 |
| `simulation/fe3d/FE3D-BASE-status.md` | 40 项检查清单 |
| `deliverables/report/technical-report-v4-unified.md` | 当前 V4.2 技术报告源 |
| `docs/v4-freeze-summary.md` | 完整工作总结 |

---

## 🔄 当前进度

**G0**：✅ 纠偏完成
**G1/G2**：⏳ 真实几何与求解待实施

**状态**：代理演示可复现；工程验证未完成

**下一步**：开始 G1 真实 FAIR-A/B 几何与 manifest

---

## 📈 后续路线

- **G1/G2**（当前后续）：真实几何与 Continuous 热—结构求解
- **G4**（Gate B 条件满足后）：至多两个候选进入统一热 FE
- **G5/G6**：焊序与预偏置的同模型对照

---

## 🎯 成功标准

**G0 成功**：代理不能晋升为 FE 证据，合成不冒充实测，默认报告源固定为 V4.2

**未来完整成功**：真实位置度、热场、应力场和证据等级完整，再决定是否扩展结构

---

**理由**：Baseline 数值可信度未建立前，任何结构优化结论都不可信。

**原则**：结果出来前编写判据，避免确认偏误。

**纪律**：严格执行证据边界，禁止把代理/合成结果写成工程验证。
