xianzai588/Hanjie/docs/process/welding-sequence.md

# 焊接顺序（WP3）

> 版本：V1.0 · 2026-09-02。核心研究量：N_weld → Q_total → deformation。当前先由降阶仿真筛选，真实实验获得后再复核。

## 候选顺序（以 6 点为例）

| 编号 | 名称 | 顺序 | 说明 |
| --- | --- | --- | --- |
| S1 | 顺序焊 | 1 → 2 → 3 → 4 → 5 → 6 | 基准方案 |
| S2 | 对称焊 | 1 → 4，2 → 5，3 → 6 | 对置抵消变形 |
| S3 | 跳焊 | 1 → 4 → 2 → 5 → 3 → 6 | 分散热输入 |

## 评价

- [ ] 三种顺序在 4/6/8 点布局下的仿真变形对比
- [ ] 实验证实（若获得样件和 CMM；当前为可选）
- [ ] 与生产节拍的权衡
