xianzai588/Hanjie/docs/research/evidence-matrix.md

# 文献证据矩阵

> 版本：V1.0 · 2026-09-02
>
> 用于把“机理证据”“相近对象证据”和“本题直接证据”分开。没有直接针对 QT450-10/Q235B 本结构的来源时，结论只能写成机理依据或工程假设。

| ID | 结论/命题 | 证据来源 | 适用层级 | 当前表述边界 | 状态 |
| --- | --- | --- | --- | --- | --- |
| E001 | 球墨铸铁熔焊时，快速冷却可导致白口、马氏体或碳化物等硬脆区域 | Cárcel-Carrasco et al., *Metals* 2016, 6, 283, DOI: [10.3390/met6110283](https://doi.org/10.3390/met6110283) | 机理/相近对象 | 可用于说明球铁侧冶金风险；不能给出本 QT450-10 工件的实际硬度 | 已有文献 |
| E002 | TIG 根部焊与镍基填充在球铁焊接中具有研究基础，但热处理、冷却速度和焊材会改变组织与硬度 | Cárcel-Carrasco et al. 2016 | 机理/工艺路线 | 支持“自动 TIG + 镍基”作为候选，不等于本题工艺已验证 | 已有文献 |
| E003 | Fe-Ni 类填充可降低部分碳化物形成倾向，但球铁侧熔合界面仍可能出现马氏体/碳化物 | El-Shennawy et al., *Scientific Reports* 2024, 14, 19827, DOI: [10.1038/s41598-024-70050-0](https://doi.org/10.1038/s41598-024-70050-0) | 机理/相近对象 | 研究对象为 AISI 304/球铁，不是 Q235B/QT450-10；只能作为材料机理旁证 | 已有文献 |
| E004 | 不同填充材料、TIG 工艺与焊前/焊后热处理会影响球铁焊接接头的组织和力学性能 | Martínez Alcón et al., *Revista de Metalurgia* 2021, 57(2), DOI: [10.3989/revmetalm.194](https://doi.org/10.3989/revmetalm.194) | 机理/相近对象 | 可用于定义小试变量；不能替代本题焊接性试验 | 已有文献 |
| E005 | QT450-10 的成分、组织和力学性能必须以实际铸件质保书/检验报告为准 | GB/T 1348《球墨铸铁件》 | 标准约束 | 仓库暂未取得本项目铸件质保书；典型成分仅作为模型假设 | 待材料文件 |
| E006 | Q235B 化学成分和力学性能应按 GB/T 700 及材料证明文件确认 | GB/T 700《碳素结构钢》 | 标准约束 | 本项目薄壁壳体的变形结论仍需几何与边界条件验证 | 待材料文件 |
| E007 | 6 点短段、对称/跳焊有利于降低整体热输入不均匀性 | 本项目降阶模型：`simulation/results/summary-r1.md`、`summary.csv`；`simulation/fe/results/fe-summary.csv` 与 `fe-convergence.csv` | 本题数值证据 | 降阶模型只支持相对筛选；二维 FE 已完成 FE-001..005 匹配对照，但 41/51/61/81 网格最细相邻变化 29.224%，不是三维 FE 或实物测量 | 二维 FE 代理已运行，网格未通过 5% 参考门，待三维/物理复核 |
| E008 | 采用无焊渣工艺、内腔防护罩和内窥终检可形成洁净度风险控制链 | 工艺设计 + 比赛固定题约束 | 设计证据 | 只能降低风险，不能声称“零飞溅已实测” | 设计中 |
| E009 | 输入不确定性、视觉退化和异常规则可通过数字基准进行可追溯压力测试 | `simulation/results/monte-carlo/`、`automation/vision/results/difficult-summary.*`、`automation/anomaly-detection/results/benchmark/`；本轮结果提交 `923e2de` | 本题数字验证 | 全部为仿真/渲染数据；不能外推为实际失效率、相机精度或焊机检测性能 | 数字基准已运行，待实测数据替换 |

## 证据使用规则

1. `已有文献`：可以支撑机理与候选路线，但不允许外推为本件的实测性能。
2. `本题数值证据`：必须同时给出输入、脚本版本、结果文件和模型限制。
3. `待材料文件`：在取得质保书前，不把典型成分写成 QT450-10/Q235B 实际成分。
4. `设计证据`：用于说明如何满足比赛要求，不能替代检测报告。
