xianzai588/Hanjie/competition/original-files/casting/附件1 大赛题目.pdf

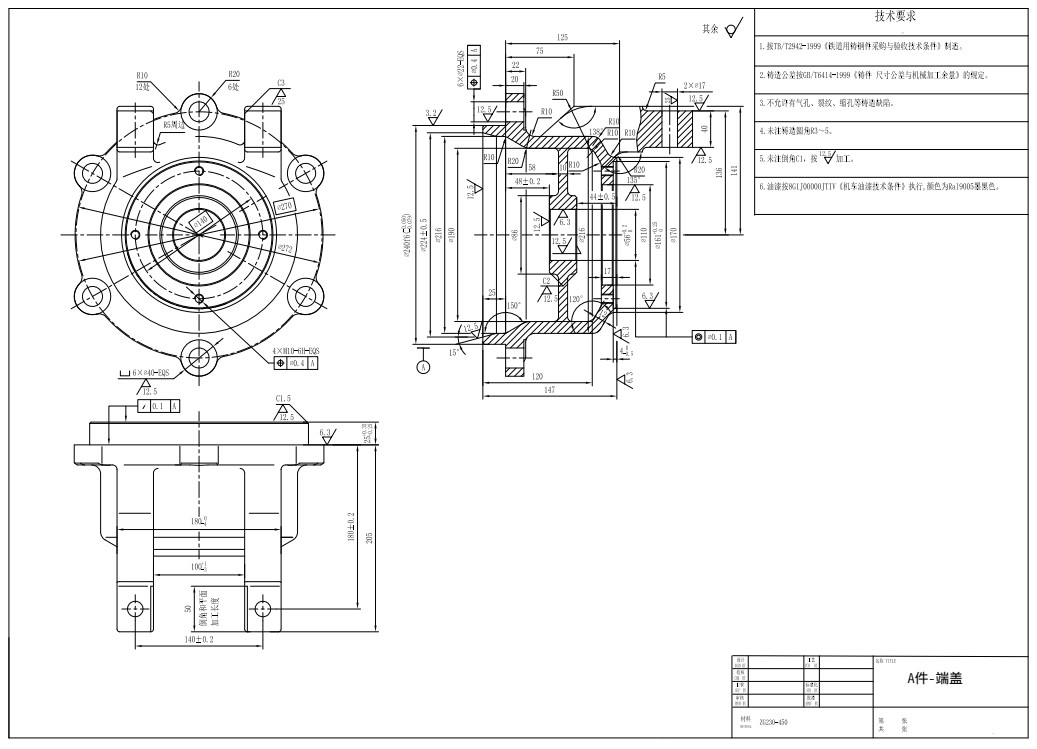
[picture p22: page 1]

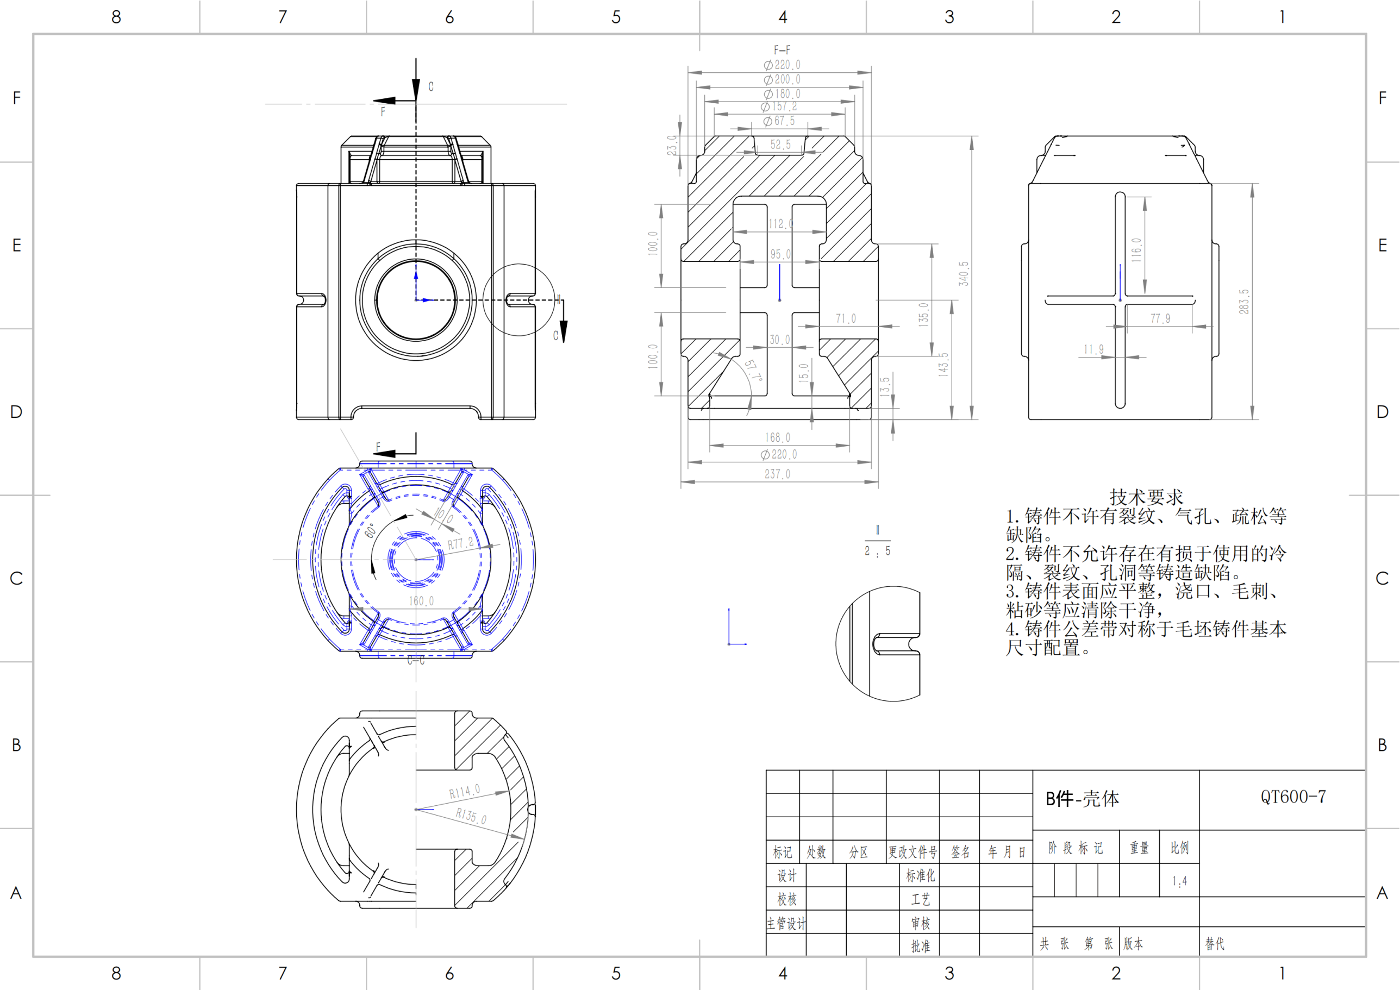
[picture p23: page 2]

B件-

E

E

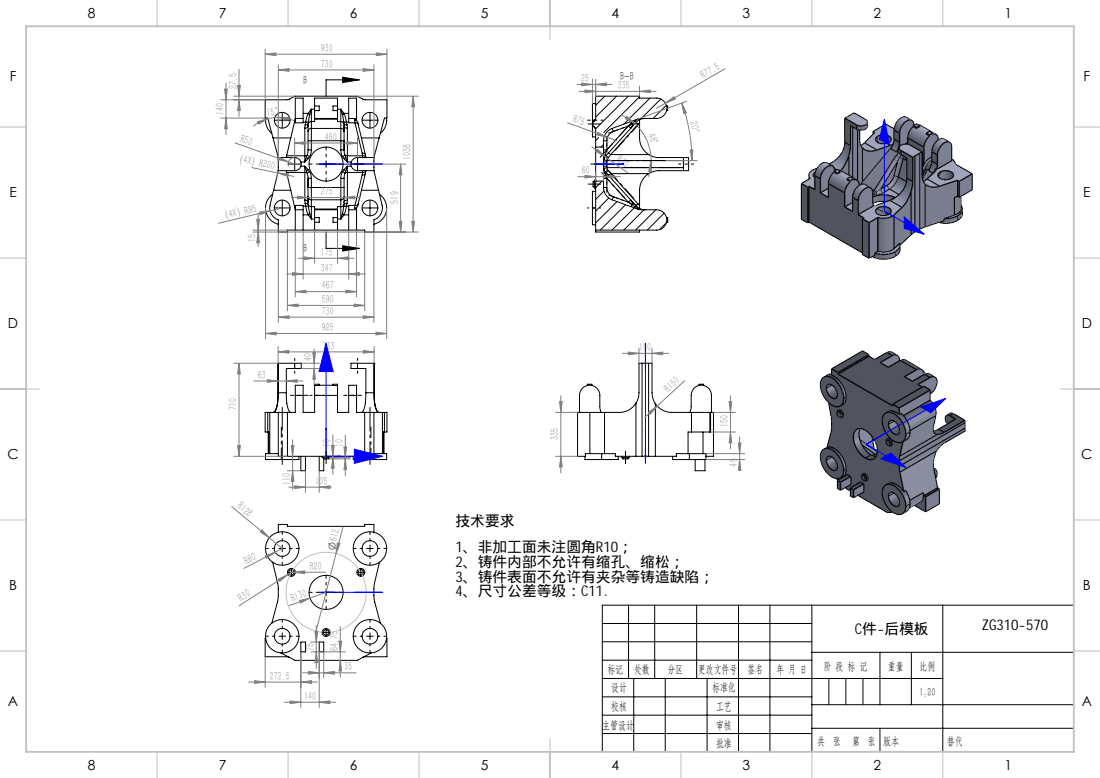
[picture p24: page 3]

347
467

2、铸件内部不允许有缩孔、缩松； 3、铸件表面不允许有夹杂等铸造缺陷； 4、尺寸公差等级：C11.

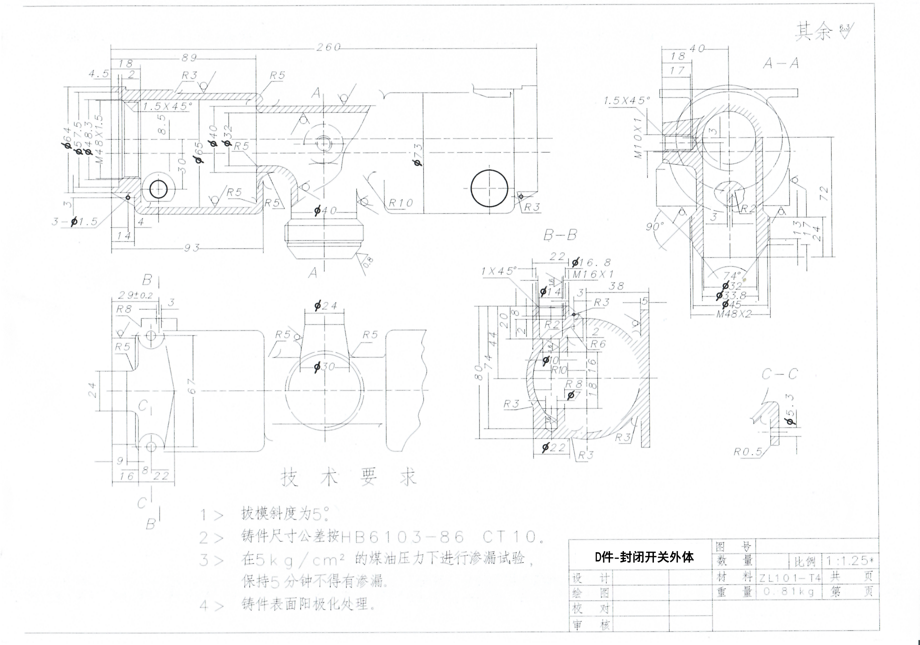
[picture p25: page 4]

### D件-封闭开关外体

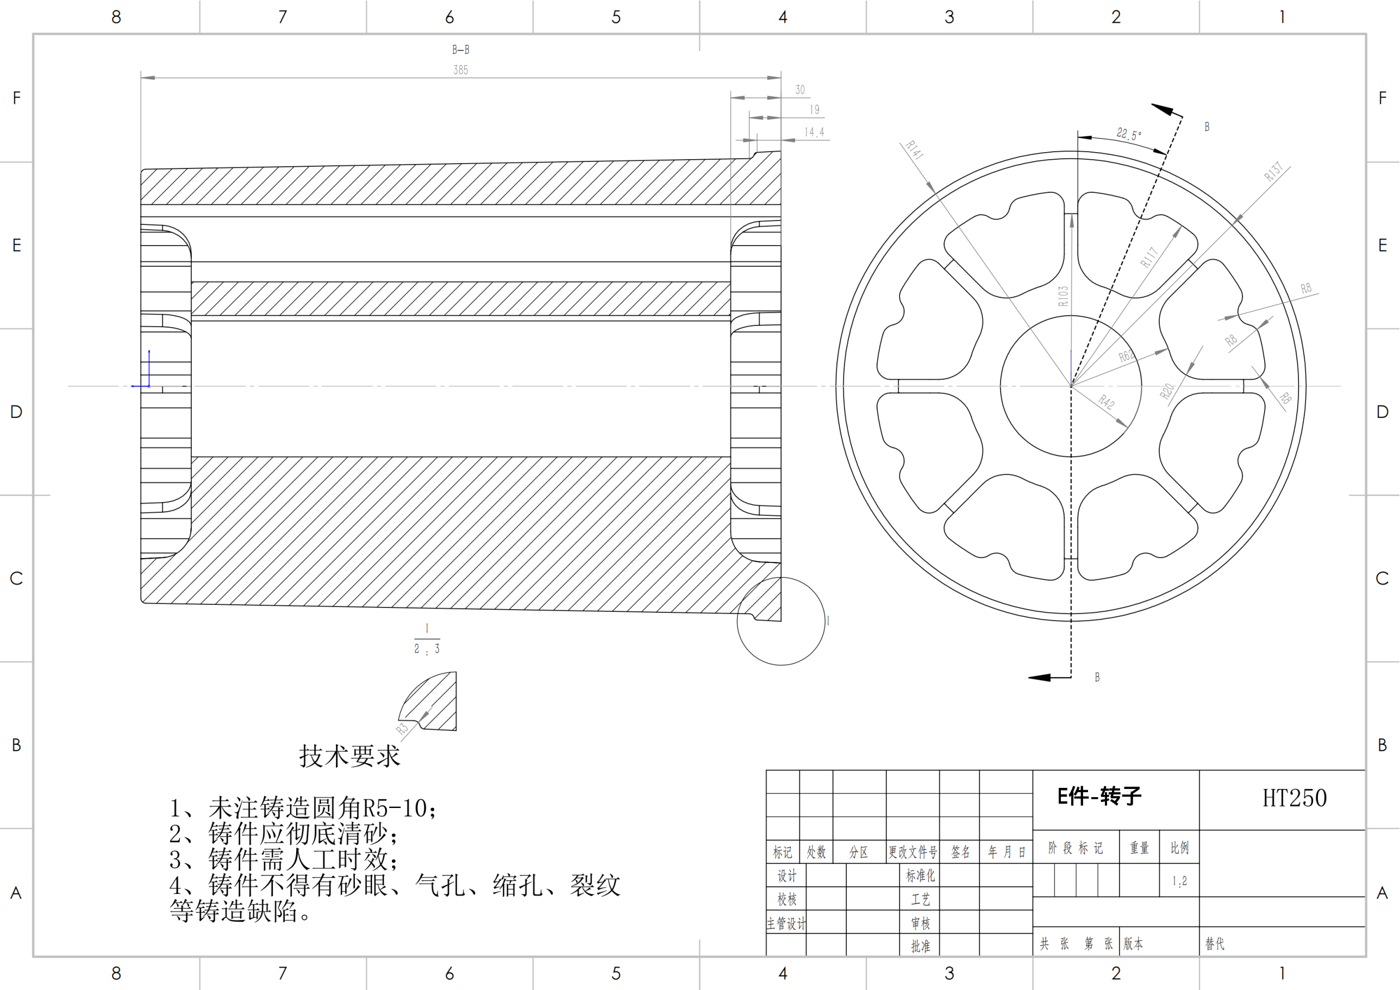
[picture p26: page 5]

## E件-转子
