xianzai588/Hanjie/deliverables/report/technical-report-v2.md

> 历史版本，禁止进入当前提交链。当前报告源：technical-report-v4-unified.md。

# QT450-10/Q235B 主轴承座异种材料焊接数字工程技术说明书 V2

**版本**：V2 · 2026-09-02
**赛道**：“中铁山桥杯”焊接工艺设计赛道 · 固定命题：某型压缩机主轴承座与壳体连接
**状态**：数字工程参赛版（证据分级）；不是制造发布版、合格 WPS/PQR 或实物检测报告。

## 摘要

本项目面向 Q235B 薄壁圆柱壳体与 QT450-10 球墨铸铁主轴承座的异种材料连接，目标是控制焊后 Ø40 轴承孔轴线位置度不超过 Ø0.05 mm，并避免焊渣和飞溅进入壳体内部。当前条件下采用"自动 TIG + 镍基填充"作为候选工艺，建立六点短焊段、S3 跳焊、柔顺夹具和视觉/过程监测的数字主线。

本版完成了 15 组降阶方案筛选、5 组开源二维热—结构代理匹配对照、41/51/61/81 网格检查、1000 次全析因降阶蒙特卡洛、带运行时质量拒绝门的常规与困难视觉基准、100 正常+100 注入异常检测及鲁棒性曲线，以及 7 张 SVG 工程表达图。降阶模型中柔顺 6P-S3 的 `P_sim=0.008787 mm`，低于刚性 6P-S1 的 `0.049701 mm`；在统一 S3、刚性夹具后，柔顺结构配对更优比例为 84.3%，明显低于混合顺序/夹具口径的 100%。二维代理 FE 中柔顺 FE-003 的 `P_FE=0.002599523 mm` 高于连续座体 FE-002 的 `0.001412091 mm`，而 FE-005（柔顺/刚性/S3）为 `0.001403186 mm`。网格相邻变化仍达 29.224%，未通过 5% 参考门。这些结果共同约束结论：柔顺结构仍是候选，不得表述为已被 FE 证明的唯一最优方案。

## 1. 题面约束与验收目标

官方固定条件为：壳体 Q235B，外径 Ø160 mm、高 200 mm、壁厚 5 mm；主轴承座 QT450-10，中心轴承孔 Ø40 mm；焊后位置度限值 Ø0.05 mm；内部不得出现可能落入压缩机内部的焊渣或飞溅。官方未给出的轴承座厚度、翼宽、焊缝尺寸、基准细节和夹具尺寸均列为设计假设。

本报告的数字指标都使用"模型内判定"措辞。只有焊后完全冷却、解除夹具、建立基准并完成合适精度的 CMM 或经校准专用检具测量，才能给出实测位置度。

### 1.1 命题响应对照

| 命题要求 | 本方案对策 | 对应章节 |
| --- | --- | --- |
| QT450-10 / Q235B 异种材料可靠连接 | 镍铁基焊材 + 低热输入自动 TIG + 预热/层间控制 | §3、§12 |
| 焊后位置度 ≤ Ø0.05 mm | 六点短焊段 + S3 跳焊 + 柔顺夹具 + 0.025 mm 径向误差预算 | §4–§9 |
| 焊缝承受高频振动交变载荷（疲劳寿命） | 镍基韧性焊缝 + 焊段端部修整 + IIW 疲劳设计基线与试验计划 | §5 |
| 内腔不得有焊渣 / 飞溅 | TIG 无飞溅工艺特性 + 内腔防护罩 + 焊后内窥终检与追溯放行 | §10、§11 |
| 自动化稳定批量生产 | 视觉定位 P95 门控 + 路径规划 + 在线异常监测 | §8、§9、§10 |

## 2. 材料与焊接性边界

QT450-10 球墨铸铁侧存在石墨组织、熔合区硬脆组织和裂纹风险；Q235B 侧为薄壁钢壳体，局部热输入可能引起壳体椭圆化和装配基准漂移。镍铁基填充、低热输入 TIG、分段对称焊和热管理作为候选路线，依据与边界见 [`docs/research/evidence-matrix.md`](../../docs/research/evidence-matrix.md)。文献只用于机理和相近对象旁证，不能代替本批 QT450-10 质保书、焊材批次、焊接性试验、金相和硬度数据。

模型材料参数为：Q235B 弹性模量 210 GPa、线膨胀系数 12.0×10⁻⁶/K、导热率 45 W/(m·K)；QT450-10 分别为 170 GPa、10.5×10⁻⁶/K、35 W/(m·K)。这些数值属于设计输入，不代表实际批次材料参数。

## 3. 工艺路线与热管理

### 3.1 候选工艺对比矩阵

围绕命题三条硬指标（异种材料连接质量、Ø0.05 位置度、内腔洁净）与工程可行性，对四条候选路线作降阶对比打分（◎优 ○良 △中 ×差）：

| 评估维度 | 自动 TIG（主候选） | CMT-MAG（对比路线） | 激光填丝（对比路线） | 熔化极钎焊（排除） |
| --- | --- | --- | --- | --- |
| 白口 / 裂纹控制 | ◎ 热输入精确可调，熔合比低 | ○ 低热输入，熔合比中等 | ○ 热输入可控，但快冷硬倾向 | × 界面金属间化合物脆性 |
| 变形与位置度 | ◎ 线能量小、分段跳焊灵活 | ○ 较优，熔滴过渡稳定 | ○ 变形小，但对装配间隙敏感 | ○ 热输入最低 |
| 飞溅 / 焊渣风险 | ◎ 无熔滴过渡飞溅，天然满足洁净约束 | ○ CMT 近无飞溅 | △ 高能密度气化飞溅需防护 | ○ 飞溅小但钎剂残留需清理 |
| 环形可达性 / 工装 | ◎ 枪体小，内孔环缝可达性好 | ○ 枪体较大，需定制工装 | △ 光学头尺寸与反射防护要求高 | ○ 可达性尚可 |
| 接头强度 / 疲劳潜力 | ◎ 镍基焊缝韧性高、止裂强 | ◎ 熔敷率与韧性兼顾 | ○ 焊缝窄、硬化带需评估 | × 接头强度受钎料限制 |
| 自动化成熟度 / 成本 | ◎ 焊接机器人标配，成本低 | ◎ 设备成熟，成本中 | △ 设备昂贵，参数窗口窄 | ○ 成本低但工序多 |

选型结论：自动 TIG 在热输入控制、飞溅/洁净度、环形可达性和疲劳潜力四项同时占优，确定为主候选；CMT-MAG 与激光填丝保留为对比路线，待设备可得性与小试结果裁决；熔化极钎焊因界面脆性与强度上限排除。

### 3.2 主候选参数窗口

候选设定为 75 A、12 V、1.5 mm/s、热效率 0.55、预热 150 °C、层间上限 200 °C、Ar 99.99%。线热输入按

\[
q_l=\eta UI/v
\]

计算，得到基准线热输入 330 J/mm。实际参数必须在设备、焊材和小试条件具备后通过工艺评定确认；当前 `docs/process/wps-v1-design-card.md` 是设计卡，不是合格 WPS。

数字顺序包括 S1 顺序焊、S2 对称焊和 S3 跳焊。S2/S3 在降阶模型中因对称性得到相同指标，因此不能仅凭该代理模型宣称 S3 比 S2 更优；S3 作为路径生成和 FE-003 的代表顺序。

## 4. 接头、基准与夹具设计

参数化数字样机采用中心刚性区 Ø82 mm、六个 18 mm 短焊段、翼端半径 R73.8 mm、翼宽 18 mm、径向槽宽 4 mm、名义座厚 12 mm。R73.8 mm 与壳体内半径 75 mm 的 1.2 mm 间隙属于装配假设，二维 FE 以等效焊接桥接区连接，实际桥接形状需要 CAD/工艺复核。

装配后的独立基准系定义为：A—壳体安装基准平面；B—由 Q235B 壳体建立的理论中心轴；C—独立周向定位特征。受控特征为 Ø40 轴承孔轴线，工程图和测量计划统一采用 `POSITION Ø0.05 | A | B`；C 只用于装配周向姿态，不进入该圆孔轴线的位置度框，从而避免以受控孔轴线自引用为基准。数字坐标原点为 A 与 B 的交点，`position_tolerance.py`、降阶模型和 FE 后处理均按此名义轴定义。夹具采用中心 Ø39.96 mm 定位销、Ø190 mm 底板和 6 个径向支撑；1200 N/mm 仅为等效柔顺刚度假设。

图纸包见 [`cad/generated/engineering-drawings/`](../../cad/generated/engineering-drawings/)（7 张 SVG）及其 [`pdf/`](../../cad/generated/engineering-drawings/pdf/) 图集（单图 7 页 + `HJ-DRW-drawing-set.pdf` 合集，A4 矢量导出）。当前状态为 `design-review`，尚未完成三维关联、公差叠加、干涉检查和制造签审。

## 5. 焊缝疲劳与寿命评估

命题明确焊缝在压缩机长期高频振动工况下承受交变载荷，疲劳寿命与位置度同为设计主线。本节按 IIW 推荐的名义应力法建立焊缝疲劳设计基线，并给出实物阶段的验证试验计划。

### 5.1 疲劳热点与设计对策

| 疲劳热点 | 成因 | 设计对策 |
| --- | --- | --- |
| 焊段起止端（弧坑/焊趾） | 六段环缝端部刚度突变，应力集中系数高 | 延迟收弧填满弧坑；端部打磨圆滑过渡，必要时 TIG 重熔修整焊趾 |
| 焊缝根部未焊透区 | 局部熔透不足形成内部缺口 | 坡口与钨极对中控制；小试金相确认熔透 |
| 熔合区硬脆组织 | 白口/马氏体在交变载荷下萌生裂纹 | 镍基填充（韧性好、止裂能力强）+ 预热缓冷改善组织 |
| 整体不平衡激励 | 焊缝非对称布置引入附加振动 | 六点周向对称布置 + S3 跳焊均衡残余应力 |

设计基线：环向角焊缝按 IIW 名义应力法取 FAT 63–80 等级（2×10⁶ 循环参考强度）作保守评估；压缩机工况应力谱需以实测载荷谱标定后计算安全裕度。镍基焊缝的良好延性与低残余应力设计是本方案的疲劳裕度来源。

### 5.2 验证试验计划

实物阶段按三级验证：① 接头级——轴向载荷疲劳试样（应力比 R=0.1，10⁷ 循环，≥3 件）验证 FAT 基线；② 部件级——焊后壳体组件振动台耐久试验，跟踪位置度漂移；③ 整机级——装机耐久试验后内窥复检焊缝与内腔。试验数据以独立 source_type 回填证据链，用于校准本节设计基线。

边界：本节为疲劳设计基线与验证门，实测载荷谱与接头疲劳数据回填前，不作为寿命达标证明。

## 6. 降阶模型与位置度后处理

降阶模型把每个焊段等效成热收缩向量，根据布局、顺序、结构因子和夹具刚度计算孔中心平移与轴线倾斜，再按

\[
P_{sim}=2\max_z\sqrt{x(z)^2+y(z)^2}
\]

形成与位置度直径限值同量纲的比较指标。15 个算例、输入配置和结果见 [`simulation/results/summary-r1.md`](../../simulation/results/summary-r1.md) 与 [`simulation/cases/SIM-001/`](../../simulation/cases/SIM-001/)。

关键基准：6P-S1 刚性基准 `P_sim=0.049701 mm`；6P-S3 柔顺方案 `P_sim=0.008787 mm`；8P 柔顺对照约 `0.008201 mm`。这些数字是降阶模型输出，不能写成实物达标或 CMM 结果。

## 7. 二维 FE 热—结构代理交叉检查

`simulation/fe/run_fe_cases.py` 使用 scikit-fem 三角形网格、瞬态热传导、外边界对流、等效残余本征应变、平面应力弹性和径向弹簧夹具。每个案例导出 FE 内孔节点，调用 `position_tolerance.fit_axis` 在 A/B 装配基准系中完成三层圆拟合与轴线评价。这里的 `P_FE` 是二维热—弹性代理模型的几何响应指标，不是焊后绝对位置度预测。

| Case | 结构/夹具/顺序 | 网格节点 | 网格单元 | 峰值温度 (°C) | P_FE (mm) | 模型内判定 |
| --- | --- | ---: | ---: | ---: | ---: | --- |
| FE-001 | baseline / rigid / 6P-S1 | 2800 | 5312 | 462.413 | 0.001449982 | pass |
| FE-002 | baseline / rigid / 6P-S3 | 2800 | 5312 | 458.511 | 0.001412091 | pass |
| FE-003 | flex / compliant / 6P-S3 | 1678 | 2632 | 561.755 | 0.002599523 | pass |
| FE-004 | baseline / compliant / 6P-S3 | 2800 | 5312 | 458.511 | 0.002051051 | pass |
| FE-005 | flex / rigid / 6P-S3 | 1678 | 2632 | 561.755 | 0.001403186 | pass |

FE-001 与 FE-002 的顺序差异较小；FE-003 的柔顺结构指标高于刚性连续座体。该结果不是失败，而是对降阶模型结构因子的反例约束：V2 同时保留柔顺候选和连续座体刚性基准，下一轮优先补三维高度、真实接触、焊缝金属本构和夹具刚度标定。

### 模型物理边界

五组案例峰值温度约为 458–562 °C，远未达到钢/铸铁熔化温度，因此当前 FE 没有模拟熔池形成、熔合过程或焊缝金属激活。结构部分实际采用平面应力、最大温度驱动的等效残余本征应变和等效径向弹簧夹具；也未包含温度相关塑性、相变、三维壳体高度、真实焊缝几何/本构、接触和真实夹具预紧。41/51/61/81 网格检查的最细相邻变化为 29.224%，未达到 5% 参考门，因此 FE 仍是离散化未收敛的二维代理反例检查，不是“FE 证明焊后位置度为 0.0026 mm”，也不是“已达到 0.05 mm”的完整焊接 FE 验证。

## 8. 参数不确定性与鲁棒性

对 4/6/8 点、baseline/flex、rigid/compliant、S1/S2/S3 共 36 个因子组合执行 1000 次共同输入扰动，随机种子为 20260902。扰动覆盖热效率、电流、电压、焊速 ±10%；两种材料导热率 ±10%；线膨胀系数、弹性模量 ±5%；夹具刚度 ±20%；初始偏心 [-0.03,0.03] mm。结果见 [`simulation/results/monte-carlo/monte-carlo.md`](../../simulation/results/monte-carlo/monte-carlo.md)。

| 设计 | P5 (mm) | P50 (mm) | P95 (mm) | worst (mm) | 超限比例 |
| --- | ---: | ---: | ---: | ---: | ---: |
| baseline rigid 6P-S3 | 0.015012 | 0.035529 | 0.065942 | 0.072866 | 23.7% |
| flex rigid 6P-S3 | 0.010685 | 0.033053 | 0.062009 | 0.068371 | 20.7% |

该统计是降阶模型风险传播，不是实际失效概率。统一 6P-S3、刚性夹具条件后，柔顺结构配对更优比例为 84.3%，而混合 S1/S3、刚性/柔顺夹具的旧口径为 100%，后者不再作为因果结论。`structure_factor` 和 `fixture_factor` 未由 FE/实测标定，因此蒙特卡洛只支持“在当前降阶模型及其预设系数下的相对变化”，不用于验证结构优劣，也不能推翻二维 FE 反例。

## 9. 视觉定位数字基准

视觉程序识别壳体中心、座中心和姿态标记。除误差统计外，运行时增加轮廓圆度、椭圆轴比和标记面积质量门；质量门拒绝的结果不能进入路径规划。常规 1000 张数字样本的检测返回率为 100%，径向 MAE 为 0.001811 mm、角度 MAE 为 0.001843°，在数字视觉门限内判定 PASS。困难集各条件 100 张，标签随像面变换同步更新；本版以误差预算和质量接受率作为主指标：

| 条件 | 原始返回率 | 质量接受率 | 拒绝数 | 径向 P95 (mm) | 角度 P95 (°) | 工程判定 |
| --- | ---: | ---: | ---: | ---: | ---: | --- |
| clean | 100% | 100% | 0 | 0.003422 | 0.004248 | PASS |
| noise | 100% | 0% | 100 | 0.079638 | 0.128781 | FAIL |
| blur | 100% | 100% | 0 | 0.002769 | 0.002119 | PASS |
| illumination | 100% | 0% | 100 | 0.356118 | 0.005194 | FAIL |
| perspective | 100% | 0% | 100 | 10.690229 | 1.833196 | FAIL |
| occlusion | 100% | 0% | 100 | 3.205838 | 2.961169 | FAIL |
| missing_edges | 100% | 0% | 100 | 0.264525 | 0.063685 | FAIL |
| low_contrast | 100% | 100% | 0 | 0.002923 | 0.003808 | PASS |
| distortion | 100% | 100% | 0 | 0.003572 | 0.004456 | PASS |
| large_offset (±5 mm) | 100% | 100% | 0 | 0.003830 | 0.004387 | PASS |

这里的“原始返回率”只表示算法给出了坐标；“质量接受率”才表示通过运行时可观测质量门，但仍不表示满足工业精度门限。比赛位置度限值 Ø0.05 mm 对应径向预算 0.025 mm；本版分配视觉 0.010 mm、相机标定 0.004 mm、TCP 0.003 mm、机器人重复定位 0.003 mm、夹具 0.003 mm、热变形 0.002 mm，采用线性最坏情况合计 0.025 mm。完整分配见 [`docs/validation/position-error-budget.md`](../../docs/validation/position-error-budget.md)。数字门限采用径向 P95 ≤0.010 mm；以 73.8 mm 姿态作用半径换算，角度 P95 ≤0.0078°，MAE 仅作描述性统计，不代表真实设备精度认证。透视、遮挡、光照梯度、噪声和缺失边缘现在会被质量门拒绝，仍需真实镜头标定、畸变校正和现场阈值定标。

## 10. 异常检测与追溯

规则检测器按电流、电压、焊速和温度窗口识别连续越界事件，并加入在线偏置估计、10% 窗口滞回、5 点中值滤波和 50 ms 最小持续时间。基准包含 100 个正常试验和 100 个异常注入试验，注入类型包括电流下降、电压尖峰、速度偏差、温度超限和电弧中断。电弧中断可同时产生电流/电压事件，因此总真实事件数为 243。

名义基准仍为 TP=243、FP=0、FN=0、precision=100%、recall=100%、F1=100%、正常试验级 FPR=0%、平均/中位检测延迟均为 0 s。压力曲线显示：10–30 ms 脉冲按设计被去抖，50 ms 及以上可检出；噪声倍数 2.0 时试验级误报率为 0%，3.0 时为 10%；±4 A 静态偏置在在线校正后误报率为 0%。该结果仍只适用于仿真信号，阈值、误报率和延迟必须用真实焊机数据重新标定。详细记录见 [`automation/anomaly-detection/results/benchmark/summary.md`](../../automation/anomaly-detection/results/benchmark/summary.md)。

## 11. 洁净度与安全控制链

候选路线采用无焊渣工艺、内腔防护、焊前清洁、分段短焊、焊后目视和内窥检查。洁净度是硬约束，不能用数字图或"无异常事件"替代真实内腔检查。实际执行时应建立一件一码、焊材批次、操作者、参数曲线、内窥照片和最终放行记录之间的关联。

## 12. 风险与失效模式

主要风险为球铁侧脆硬组织/裂纹、薄壁壳体椭圆化、夹具过拘束、焊缝不可达、内部飞溅、视觉误检和材料牌号偏差。FMEA 见 [`docs/design/fmea.md`](../../docs/design/fmea.md)。控制策略分别为低热输入与候选镍基填充、短段/跳焊/热管理、可释放夹具、路径仿真、内腔防护与内窥终检、困难样本压力测试，以及质保书和焊材批次锁定。

## 13. 可复现性与文件索引

```text
simulation/configs/default.yaml
simulation/scripts/run_reduced_order.py
simulation/scripts/run_monte_carlo.py
simulation/fe/run_fe_cases.py
simulation/scripts/position_tolerance.py
automation/vision/run_benchmark.py
automation/anomaly-detection/run_benchmark.py
cad/parametric/generate_engineering_drawings.py
cad/parametric/export_drawing_pdfs.py
```

关键输出包括：

- 降阶：`simulation/results/summary.csv`、`summary-r1.md`、`monte-carlo/`；
- FE：`simulation/fe/results/fe-summary.*`、`simulation/fe/results/fe-convergence.csv`、`simulation/cases/FE-001..005/`；
- 视觉：`automation/vision/results/summary.json`、`difficult-summary.*`；
- 异常：`automation/anomaly-detection/results/benchmark/`；
- 工程图：`cad/generated/engineering-drawings/`（7 张 SVG）及 `pdf/` 图集（单图 7 页 + `HJ-DRW-drawing-set.pdf` 合集）。

回归测试：`python -m pytest -q`，当前 15 项测试通过。

## 14. 物理验证计划

获得样件和设备后，先对 QT450-10/Q235B 母材与焊材做来料确认，再做小试样和代表性接头试验。实物流程为：焊前基准测量 → 按候选 WPS 焊接并记录电流/电压/焊速/层间温度 → 完全冷却并解除夹具 → 焊后 CMM 或经校准替代测量 → 内孔分层拟合轴线 → 外观、内窥、NDT、金相和硬度评价。数字样本与实物数据使用不同 `source_type`，不得互相覆盖。

## 15. 结果讨论

降阶模型和二维 FE 给出了不同结构排序，说明结果对结构表达、连接刚度和边界条件敏感。降阶模型适合快速筛选布局与输入边界；二维 FE 适合发现几何材料分区造成的反例；二者都不能解决三维壳体高度、接触、焊缝金属塑性和真实夹具预紧问题。因而 V2 的技术贡献是形成可复算的证据链和明确的下一步验证门，而不是提前宣称实物性能。

## 16. 交付包与版本控制

提交前应将本 Markdown 转换为学校要求的 PDF，并同时归档 `cad/` 源文件、工程表达 SVG、`simulation/` 脚本与结果、`automation/` 源码与统计、工艺卡、检测规程、FMEA 和所有输入参数。图表下方统一标注数据来源与模型边界，禁止把仿真、渲染或示例记录混入实物证据栏。

## 17. 结论与放行条件

数字证据支持自动 TIG + 镍基填充、六点短段和 S3 作为值得继续验证的候选路线；降阶模型支持柔顺结构作为低位置度候选，二维 FE 则要求保留连续座体刚性基准。当前不能给出"实物已满足 Ø0.05 mm"的结论。

**参赛提交状态**：本文件可作为数字工程设计方案提交；提交时应明确各数值结果的证据等级、二维 FE 的代理模型边界、困难视觉样本的工程 FAIL 条件，以及尚未完成的物理验证，不把缺失的实物数据包装成已验证性能。

**制造放行状态**：未经实际 QT450-10/Q235B 质保书确认、焊材和设备可得性确认、WPS/PQR 或等效工艺评定、三维 CAD 与公差/干涉检查、真实焊接记录、焊后 CMM 或经校准替代测量、金相/硬度/NDT、内腔洁净度证据以及真实相机/焊机数据标定，不得用于实际制造放行。上述要求是制造质量门，不是本参赛数字方案的提交前置条件。

## 附录 A. WPS V1 工艺卡（设计态）

以下为数字样机的工艺设定卡（同步自 [`docs/process/wps-v1-design-card.md`](../../docs/process/wps-v1-design-card.md)），定位是"值得验证的工艺候选"的设计基线，不是经评定的 WPS/PQR。

| 项目 | V1 设计值 | 状态 |
| --- | --- | --- |
| 母材 | QT450-10 / Q235B，Q235B 壳体 t=5 mm | 题面条件 |
| 方法 | 自动 TIG，短段、对称跳焊 | 主候选 |
| 填充材料 | ERNiFe-CI，规格待采购确认 | 候选 |
| 电流/电压 | 75 A / 12 V | 数值设定 |
| 焊速 | 1.5 mm/s | 数值设定 |
| 线热输入 | 330 J/mm（η=0.55） | 降阶模型输入 |
| 预热 | 150 °C | 候选设定，需工艺评定 |
| 层间上限 | 200 °C | 候选控制值 |
| 保护气 | Ar 99.99%，10 L/min | 设备确认项 |
| 焊缝布局 | 6 个柔顺连接单元，单段 18 mm | 设计假设 |
| 顺序 | S3：1→4→3→6→2→5 | 数字样机当前方案 |
| 冷却 | 保温缓冷；不得对球铁熔合区强制急冷 | 设计原则 |
| 内腔防护 | 可拆卸环形防护/接料罩 + 焊后内窥检查 | 洁净度设计证据 |

放行前必须补齐：QT450-10/Q235B 质保书、焊材批次和烘干/储存记录；设备能力、装配间隙和 TCP 标定；小试中的成形、裂纹、金相、硬度与 NDT 结果；真实焊后 CMM 位置度和测量不确定度。
