xianzai588/Hanjie/cad/generated/engineering-drawings/gas-water-detail.png

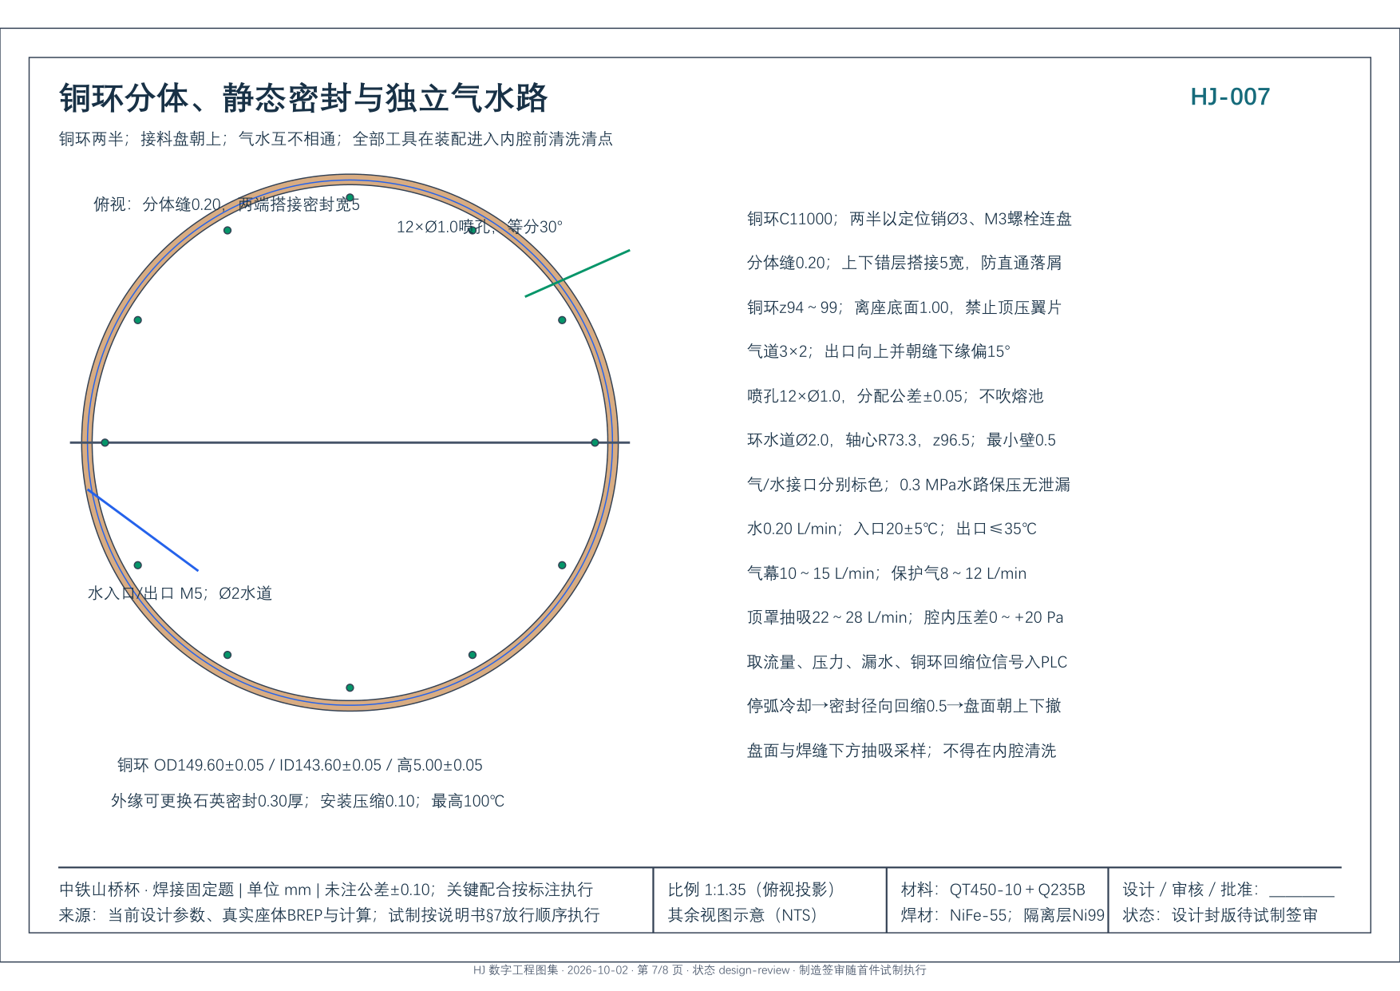
cad/generated/engineering-drawings/gas-water-detail.png
