xianzai588/Hanjie/cad/generated/engineering-drawings/sleeve-detail.png

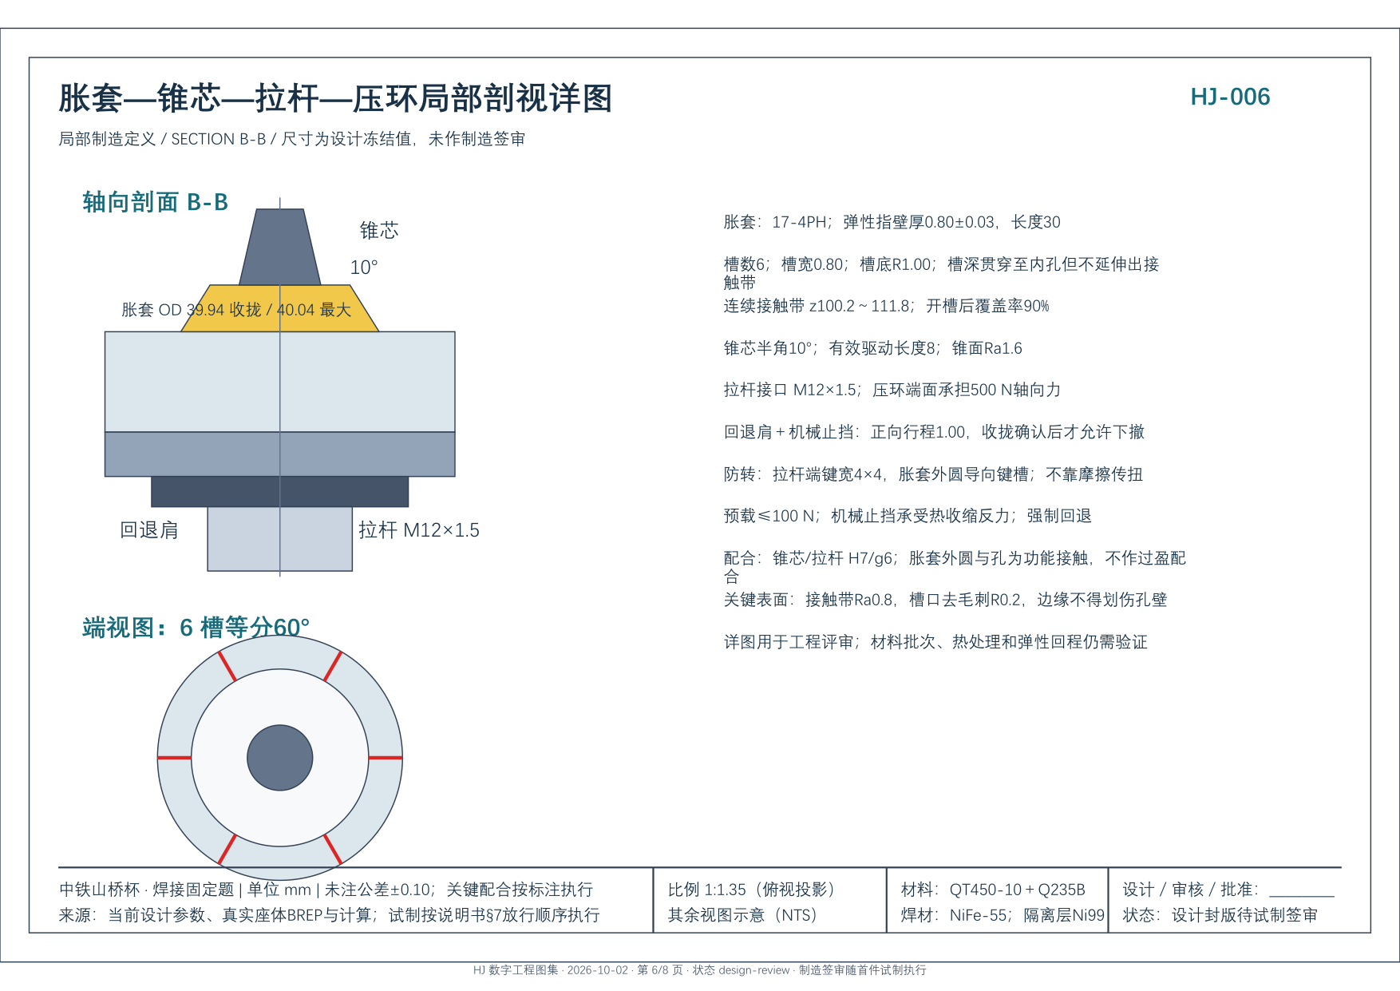
cad/generated/engineering-drawings/sleeve-detail.png
