xianzai588/Hanjie/simulation/cases/SIM-008/result.csv

case_id | structure | fixture | layout_points | sequence | line_heat_input_j_mm | total_heat_input_j | effective_peak_temperature_c | haz_width_proxy_mm | material_stiffness_factor | hole_center_shift_mm | axis_tilt_deg | shell_ellipticity_proxy_mm | position_metric_p_sim_mm | limit_mm | pass_in_model | sequence_indices | datum_reference | reduction_vs_baseline_s1_pct
BASELINE-RIGID-8P-S2 | baseline | rigid | 8 | S2 | 330.0 | 47520.0 | 550.628437 | 3.996498 | 1.0 | 0.006234 | 0.015477 | 0.004242 | 0.015708 | 0.05 | True | 1-5-2-6-3-7-4-8 | A=壳体安装基准平面；B=Q235B 壳体理论中心轴；C=独立周向定位特征；受控特征=Ø40 孔轴线；位置度=Ø0.05 | A | B | 75.001
