xianzai588/Hanjie/cad/generated/engineering-drawings/fixture-assembly.png

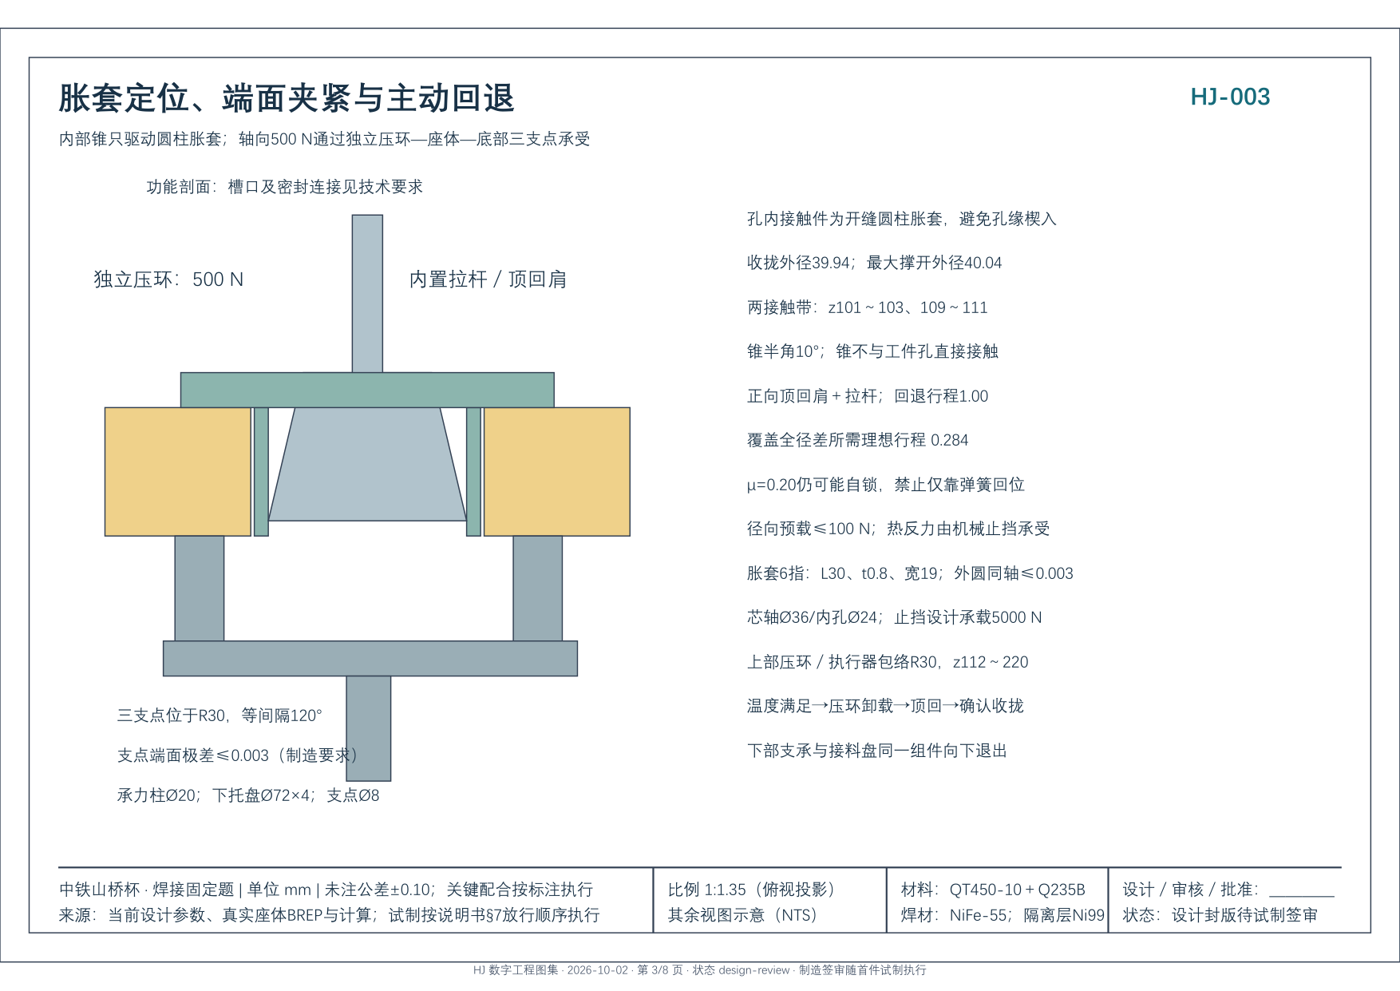
cad/generated/engineering-drawings/fixture-assembly.png
