xianzai588/Hanjie/cad/generated/engineering-drawings/protected-process-assembly.png

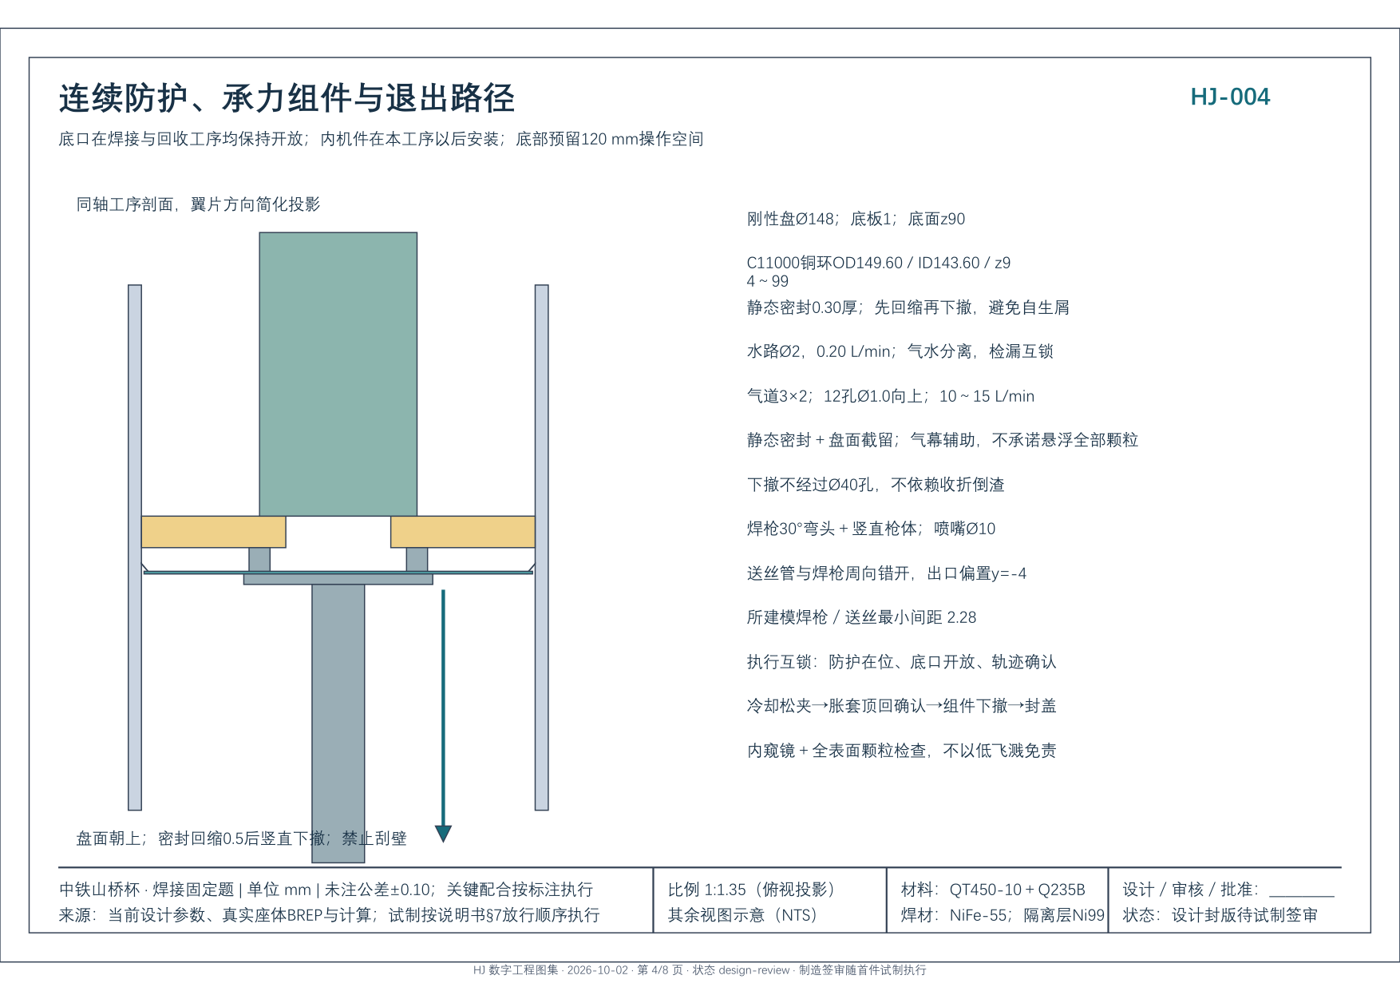
cad/generated/engineering-drawings/protected-process-assembly.png
