xianzai588/Hanjie/automation/vision/results/difficult/blur/errors.csv

filename | dx_error_mm | dy_error_mm | theta_error_deg | quality_accepted | quality_confidence | quality_failed_checks
sample_0000.png | -0.0021769205729166665 | 0.0011189778645832593 | -0.0028914904965890997 | True | 0.9985245970932757
sample_0001.png | -0.002909362316131592 | -0.0019887487093607215 | 0.001525970280971567 | True | 0.9984689462462949
sample_0002.png | -7.120768229162966e-05 | -7.120768229174068e-05 | 0.0 | True | 0.9984874965286218
sample_0003.png | 0.0011088152726491107 | 7.11679458618164e-05 | 0.0 | True | 0.9984874965286218
sample_0004.png | 0.0019175410270690918 | 0.0019785364468892785 | -0.002792723683613829 | True | 0.9985431473756026
sample_0005.png | -0.0007934967676799243 | -0.000152587890625 | 0.0 | True | 0.9984874965286218
sample_0006.png | -0.0003509521484375 | -0.00010683139165246214 | -0.0003509041266727131 | True | 0.9984689462462949
sample_0007.png | -0.0006358027458190918 | 0.00034586588541662966 | -0.0010486020006350572 | True | 0.9985245970932757
sample_0008.png | 0.0005442301432291666 | -0.0017700393994649621 | 0.0 | True | 0.9984874965286218
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
