xianzai588/Hanjie/automation/vision/results/difficult/clean/errors.csv

filename | dx_error_mm | dy_error_mm | theta_error_deg | quality_accepted | quality_confidence | quality_failed_checks
sample_0000.png | -0.00012211004892992428 | -0.0017344256242116107 | 0.0026371389820925017 | True | 0.9984941374026078
sample_0001.png | 0.0012511809666950757 | -0.00189208984375 | 0.0029359572614494622 | True | 0.9985001516666913
sample_0002.png | 0.001490265130996704 | 0.0017852385838825757 | -0.002751123137857192 | True | 0.9985121801948582
sample_0003.png | 0.0004780888557434082 | -0.00019837419191998107 | 0.001173789660596114 | True | 0.9985061659307748
sample_0004.png | -0.00040183464686072146 | -0.0008493661880493164 | 0.000630652485047678 | True | 0.9985121801948582
sample_0005.png | 0.0023193359375 | 0.0012308756510416667 | -0.0016707655015322231 | True | 0.9985362372511922
sample_0006.png | -0.0031738678614299243 | 0.00012209018071496214 | -0.001270843859270343 | True | 0.9968583980713821
sample_0007.png | 0.0013682047526041297 | -0.0012919108072916667 | 0.002349098578336317 | True | 0.9985242087230253
sample_0008.png | 0.0005646149317424243 | 0.002461731433868408 | -0.004236530952136164 | True | 0.9985181944589417
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
