xianzai588/Hanjie/automation/vision/results/difficult/distortion/errors.csv

filename | dx_error_mm | dy_error_mm | theta_error_deg | quality_accepted | quality_confidence | quality_failed_checks
sample_0000.png | 0.0013427337010700757 | -0.0005696515242258893 | 0.0007779305403081693 | True | 0.998560294307526
sample_0001.png | 0.002304087082544981 | 0.0010274251302083703 | -0.0006033171166102136 | True | 0.9985542800434426
sample_0002.png | 0.0009256998697916666 | -0.0001881519953410571 | -0.00014382555631442528 | True | 0.9985482657793591
sample_0003.png | -0.0005747477213541666 | -0.0015920003255208333 | 0.0027720698288353773 | True | 0.9985542800434426
sample_0004.png | 0.002655049165089962 | -0.0018920699755350379 | 0.0036624603999417804 | True | 0.9985482657793591
sample_0005.png | -0.0002288818359375 | -0.001271575689315796 | 0.001307470390673915 | True | 0.9985362372511922
sample_0006.png | 0.0016225079695383893 | 0.0008290211359660571 | -0.001536123601784567 | True | 0.9985482657793591
sample_0007.png | 0.0005696713924407959 | 0.0005645652612050189 | 0.00041363187374283635 | True | 0.9985302229871087
sample_0008.png | 0.001983622709910038 | 0.0001780390739440918 | -0.0006161011850576159 | True | 0.9985482657793591
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
