xianzai588/Hanjie/automation/vision/results/difficult/illumination/errors.csv

filename | dx_error_mm | dy_error_mm | theta_error_deg | quality_accepted | quality_confidence | quality_failed_checks
sample_0000.png | -0.2982329924901326 | 0.004496276378631592 | 0.0014101094345888576 | False | 0.045131558060118794 | shell_circularity
sample_0001.png | -0.2842102448145549 | 0.0010782678922017785 | 1.37067650278766e-05 | False | 0.04586266310201864 | shell_circularity
sample_0002.png | -0.35231526692708337 | 0.007965087890625 | 0.0001348154898224152 | False | 0.044936499535690476 | shell_circularity
sample_0003.png | -0.25777180989583337 | 0.0007171630859375 | 0.0013559234983926416 | False | 0.04547033359026955 | shell_circularity
sample_0004.png | -0.35743208726247155 | -0.0060628453890482215 | -0.0034369456187075542 | False | 0.04555108999734203 | shell_circularity
sample_0005.png | -0.2983704010645549 | 0.003402690092722538 | 0.0029497394749649075 | False | 0.045503480464646175 | shell_circularity
sample_0006.png | -0.24445088704427076 | -0.006113688151041741 | 0.0027814856609226224 | False | 0.04646570977827448 | shell_circularity
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
