xianzai588/Hanjie/simulation/structural-v4/results/struct0-prep/constitutive-3d-small-mesh.md

# STRUCT-0-PREP 三维组件验证

> 三维 J2 与六四面体仿射小网格算法基准；不是 Continuous 整件求解结果。

| 小网格算例 | 最大等效应力 (MPa) | 最大应力分量 (MPa) | 合力范数 (N) | 合矩范数 (N·mm) |
| --- | ---: | ---: | ---: | ---: |
| free_thermal_expansion | 0.000000 | 0.000000 | 0.000e+00 | 0.000e+00 |
| fully_constrained_heating | 0.000000 | 989.181818 | 0.000e+00 | 0.000e+00 |
| deviatoric_loading | 235.000000 | 315.757576 | 1.421e-14 | 0.000e+00 |
| support_release_to_plastic_shape | 0.000000 | 0.000000 | 0.000e+00 | 0.000e+00 |

全部登记检查：通过

已覆盖纯剪、静水、组合、卸载、坐标旋转一致性、跨温区插值、自由/约束热膨胀和支承释放。任意边界全局 Newton、一致切线、焊材、接触及焊道激活仍未实现。
