xianzai588/Hanjie/simulation/thermal-v5/results/credibility04r1/spatial-convergence-diagnosis.md

# THERMAL-0.4R1 空间收敛诊断

> surface45, nominal properties, dt=0.1 s; process and source parameters unchanged。本文件是已有结果的共同控制体后处理，不是新物理校准。

| 材料 | 体积加权 MAE (°C) | 体积加权 P95 (°C) | 最大差 (°C) | 固相线翻转体积 (mm³) | P95 门 |
| --- | ---: | ---: | ---: | ---: | --- |
| q235b | 1.641 | 6.694 | 70.489 | 0.000 | 通过 |
| qt450_10 | 0.720 | 3.364 | 72.446 | 15.258 | 通过 |
| ernife_ci | 45.880 | 74.554 | 80.452 | 10.462 | 未通过 |

## 结论

中、细网格有效焊材体积分别为 90.477868/90.477868 mm³，体积守恒；焊材单元数从 560 变为 1620。
Q235B 与 QT450-10 的大部分体积温度场已接近，但局部极值仍超限；QT450-10 出现固相线判定翻转。ERNiFe-CI 热区的 P95 差异仍超限，因此失败不只是阈值统计问题，而是局部焊道/热源离散尚未收敛。

状态：`spatial_convergence_pass=false`。继续冻结 THERMAL-1；下一步应固定本情景，优先细化焊道与热源边界表示并复核共同物理位置，而不是调整热效率或门槛。
