xianzai588/Hanjie/simulation/thermal-v5/results/g-thermal-audit/G-THERMAL-audit.md

# G-THERMAL 审计

> 证据等级：`solver_result_unvalidated`。审计通过只表示数值链检查通过，不表示热源已由实验校准。

## Gate 判定

- 源能量归一化：**PASS**；最大功率体积分误差 `6.890e-16`，连续焊段累计能量误差 `0.0000%`。
- 全局热能平衡：**PASS**；最大残差 `0.0041%`。
- 热源域捕获：**PASS**；归一化前最小捕获率 `99.997772%`。
- 时间步审计：**PASS**；dt/2→dt/4 峰值变化 `0.001%`。
- 网格审计：**PASS**；medium/fine 均取 dt=0.003 s，峰值变化 `0.56%`。
- 参数边界审计：**REVIEW**；效率和热源尺寸变化对峰值有明显影响。
- G-THERMAL 总状态：**review_required**。

## 运行矩阵

| 工况 | 网格 | dt (s) | 峰值温度 (°C) | 功率误差 | 能量误差 |
| --- | --- | ---: | ---: | ---: | ---: |
| baseline | 72×52×30 | 0.0100 | 896.99 | 5.74e-16 | 0.0000% |
| mesh-coarse | 49×26×15 | 0.0030 | 959.20 | 6.89e-16 | 0.0000% |
| mesh-medium | 72×52×30 | 0.0030 | 896.62 | 6.89e-16 | 0.0000% |
| mesh-fine | 107×62×36 | 0.0030 | 901.62 | 5.74e-16 | 0.0000% |
| dt-half | 72×52×30 | 0.0050 | 896.65 | 6.89e-16 | 0.0000% |
| dt-quarter | 72×52×30 | 0.0025 | 896.66 | 5.74e-16 | 0.0000% |
| convection-low | 72×52×30 | 0.0100 | 898.21 | 5.74e-16 | 0.0000% |
| convection-high | 72×52×30 | 0.0100 | 894.58 | 5.74e-16 | 0.0000% |
| efficiency-low | 72×52×30 | 0.0100 | 760.54 | 5.61e-16 | 0.0000% |
| efficiency-high | 72×52×30 | 0.0100 | 1033.51 | 5.83e-16 | 0.0000% |
| source-narrow | 72×52×30 | 0.0100 | 998.84 | 5.74e-16 | 0.0000% |
| source-wide | 72×52×30 | 0.0100 | 816.90 | 5.74e-16 | 0.0000% |

## 结论与下一步

源能量归一化、归一化前域捕获和全局热能账本已独立审计。固定局部窗口只描述焊源邻域，网格/参数敏感性和实验校准仍需复核，当前不能进入 THERMAL-1，也不能把峰值写成已校准焊接热场。
