xianzai588/Hanjie/simulation/structural-v4/results/static-screening/static-screening-analysis.md

# P1A 静力筛查分析

> 证据等级：`solver_result_unvalidated`。本报告只评价三维线弹性静力筛查的数值稳定性，不把它升级为热—结构焊接 FE 结论。

## 判据

- medium→fine 轴线偏移直径相对变化 ≤ 3%。
- medium→fine p95 von Mises 相对变化 ≤ 10%。
- fine 网格 BC-1/BC-2 敏感性 ≤ 10%。

## 网格收敛

| 模型 | BC | 位移变化 | p95 应力变化 | 结论 |
| --- | --- | ---: | ---: | --- |
| 4P-FAIR_A | BC-1 | 0.37% | 0.07% | PASS |
| 4P-FAIR_A | BC-2 | 0.10% | 0.16% | PASS |
| 4P-FAIR_B | BC-1 | 0.44% | 0.05% | PASS |
| 4P-FAIR_B | BC-2 | 0.07% | 0.10% | PASS |
| 6P-FAIR_A | BC-1 | 0.38% | 0.26% | PASS |
| 6P-FAIR_A | BC-2 | 0.14% | 0.25% | PASS |
| 6P-FAIR_B | BC-1 | 0.38% | 0.26% | PASS |
| 6P-FAIR_B | BC-2 | 0.14% | 0.25% | PASS |
| 8P-FAIR_A | BC-1 | 0.77% | 0.04% | PASS |
| 8P-FAIR_A | BC-2 | 0.37% | 0.01% | PASS |
| 8P-FAIR_B | BC-1 | 0.12% | 0.23% | PASS |
| 8P-FAIR_B | BC-2 | 0.62% | 0.10% | PASS |
| Continuous | BC-1 | 0.67% | 0.14% | PASS |
| Continuous | BC-2 | 1.34% | 0.19% | PASS |

## 支承敏感性

| 模型 | 位移变化 | p95 应力变化 | 结论 |
| --- | ---: | ---: | --- |
| 4P-FAIR_A | 1.25% | 0.01% | PASS |
| 4P-FAIR_B | 1.21% | 0.00% | PASS |
| 6P-FAIR_A | 1.28% | 0.05% | PASS |
| 6P-FAIR_B | 1.28% | 0.05% | PASS |
| 8P-FAIR_A | 1.26% | 0.07% | PASS |
| 8P-FAIR_B | 1.25% | 0.03% | PASS |
| Continuous | 0.92% | 0.07% | PASS |

## fine 网格候选排序

| 排名 | 模型 | 质量 kg | 平均轴线偏移直径 mm | 平均 p95 应力 MPa |
| ---: | --- | ---: | ---: | ---: |
| 1 | Continuous | 1.417426 | 0.000304 | 0.632 |
| 2 | 8P-FAIR_B | 0.796860 | 0.000570 | 0.972 |
| 3 | 8P-FAIR_A | 0.704814 | 0.000696 | 1.226 |
| 4 | 6P-FAIR_A | 0.684572 | 0.000750 | 1.281 |
| 5 | 6P-FAIR_B | 0.684572 | 0.000750 | 1.281 |
| 6 | 4P-FAIR_A | 0.667989 | 0.000898 | 1.409 |
| 7 | 4P-FAIR_B | 0.572283 | 0.001247 | 1.919 |

静力筛查数值稳定性：**PASS**。
6P-FAIR_A / 6P-FAIR_B 等价性：**PASS**（由相同离散几何得到相同数值）。
完整热—结构 Gate：**未通过/未执行**；需要温度场、焊缝材料和显式壳体柔度模型后再审。

> 仅为修复后实体的三维线弹性静力筛查，不含焊接热源、温度相关塑性、相变、焊缝金属本构和显式壳体实体柔度。
