xianzai588/Hanjie/simulation/structural-v4/results/static-screening/static-screening.md

# P1A 三维线弹性静刚度筛选

> 结果直接来自修复后 STEP 的 Gmsh 四面体网格和 scikit-fem 线弹性求解；证据等级为 `solver_result_unvalidated`。
> 该结果不包含焊接热源、温度相关塑性、相变、焊缝金属本构或壳体实体柔度，不能写成完整热—结构 FE 结论。

## 统一边界与载荷

- Ø40 孔内表面施加合力 1 kN 的均匀径向分布载荷，扫描 0°–90°、每 15° 一点。
- R74.98 圆柱焊接接口施加三向分布式等效弹簧；BC-1 = 1e8 N/mm，BC-2 = 1e6 N/mm。
- 整圈分布式支承本身消除刚体模态，不使用随网格变化的点锚固。
- 材料统一采用 QT450-10 室温线弹性参数 E=169 GPa、ν=0.27。

## 各模型最不利方向结果

| 模型 | 网格 | BC | 最不利角度 | 最大载荷诱导轴线偏移直径 (mm) | 最大 von Mises (MPa) | 质量 (kg) |
| --- | --- | --- | ---: | ---: | ---: | ---: |
| Continuous | coarse | BC-1 | 90 | 0.000306 | 1.005 | 1.417426 |
| Continuous | coarse | BC-2 | 90 | 0.000313 | 1.005 | 1.417426 |
| Continuous | medium | BC-1 | 90 | 0.000305 | 1.177 | 1.417426 |
| Continuous | medium | BC-2 | 75 | 0.000310 | 1.130 | 1.417426 |
| Continuous | fine | BC-1 | 90 | 0.000303 | 1.263 | 1.417426 |
| Continuous | fine | BC-2 | 90 | 0.000306 | 1.263 | 1.417426 |
| 4P-FAIR_A | coarse | BC-1 | 90 | 0.000885 | 3.443 | 0.667989 |
| 4P-FAIR_A | coarse | BC-2 | 90 | 0.000908 | 3.460 | 0.667989 |
| 4P-FAIR_A | medium | BC-1 | 90 | 0.000889 | 3.294 | 0.667989 |
| 4P-FAIR_A | medium | BC-2 | 90 | 0.000905 | 3.307 | 0.667989 |
| 4P-FAIR_A | fine | BC-1 | 75 | 0.000892 | 3.664 | 0.667989 |
| 4P-FAIR_A | fine | BC-2 | 75 | 0.000904 | 3.677 | 0.667989 |
| 4P-FAIR_B | coarse | BC-1 | 90 | 0.001218 | 3.403 | 0.572283 |
| 4P-FAIR_B | coarse | BC-2 | 90 | 0.001246 | 3.672 | 0.572283 |
| 4P-FAIR_B | medium | BC-1 | 90 | 0.001234 | 3.392 | 0.572283 |
| 4P-FAIR_B | medium | BC-2 | 90 | 0.001255 | 3.360 | 0.572283 |
| 4P-FAIR_B | fine | BC-1 | 75 | 0.001239 | 4.015 | 0.572283 |
| 4P-FAIR_B | fine | BC-2 | 75 | 0.001254 | 3.969 | 0.572283 |
| 6P-FAIR_A | coarse | BC-1 | 0 | 0.000740 | 2.821 | 0.684572 |
| 6P-FAIR_A | coarse | BC-2 | 0 | 0.000758 | 2.933 | 0.684572 |
| 6P-FAIR_A | medium | BC-1 | 0 | 0.000742 | 2.685 | 0.684572 |
| 6P-FAIR_A | medium | BC-2 | 0 | 0.000756 | 2.619 | 0.684572 |
| 6P-FAIR_A | fine | BC-1 | 75 | 0.000745 | 2.813 | 0.684572 |
| 6P-FAIR_A | fine | BC-2 | 75 | 0.000755 | 2.764 | 0.684572 |
| 6P-FAIR_B | coarse | BC-1 | 0 | 0.000740 | 2.821 | 0.684572 |
| 6P-FAIR_B | coarse | BC-2 | 0 | 0.000758 | 2.933 | 0.684572 |
| 6P-FAIR_B | medium | BC-1 | 0 | 0.000742 | 2.685 | 0.684572 |
| 6P-FAIR_B | medium | BC-2 | 0 | 0.000756 | 2.619 | 0.684572 |
| 6P-FAIR_B | fine | BC-1 | 75 | 0.000745 | 2.813 | 0.684572 |
| 6P-FAIR_B | fine | BC-2 | 75 | 0.000755 | 2.764 | 0.684572 |
| 8P-FAIR_A | coarse | BC-1 | 90 | 0.000686 | 2.433 | 0.704814 |
| 8P-FAIR_A | coarse | BC-2 | 90 | 0.000705 | 2.514 | 0.704814 |
| 8P-FAIR_A | medium | BC-1 | 45 | 0.000687 | 2.548 | 0.704814 |
| 8P-FAIR_A | medium | BC-2 | 45 | 0.000698 | 2.472 | 0.704814 |
| 8P-FAIR_A | fine | BC-1 | 90 | 0.000692 | 2.475 | 0.704814 |
| 8P-FAIR_A | fine | BC-2 | 90 | 0.000701 | 2.368 | 0.704814 |
| 8P-FAIR_B | coarse | BC-1 | 60 | 0.000565 | 2.146 | 0.796860 |
| 8P-FAIR_B | coarse | BC-2 | 60 | 0.000578 | 2.252 | 0.796860 |
| 8P-FAIR_B | medium | BC-1 | 90 | 0.000567 | 2.046 | 0.796860 |
| 8P-FAIR_B | medium | BC-2 | 90 | 0.000577 | 2.034 | 0.796860 |
| 8P-FAIR_B | fine | BC-1 | 90 | 0.000567 | 1.952 | 0.796860 |
| 8P-FAIR_B | fine | BC-2 | 90 | 0.000574 | 1.895 | 0.796860 |

## 解释边界

最不利方向按载荷诱导的孔轴线偏移直径选择，已扣除未变形 CAD 轴线基准；连续结构和离散结构的质量只用于比刚度辅助比较，不用于替代热—结构焊接结论。网格相邻变化和边界敏感性必须在新 BREP 上同时报告，不能沿用旧二维代理结果。
