xianzai588/Hanjie/automation/anomaly-detection/results/benchmark/summary.md

# 异常检测基准结果

> 100 个正常试验 + 100 个异常注入试验；全部信号为 simulated，不是焊机采集。

| 指标 | 数值 |
| --- | ---: |
| TP | 243 |
| FP | 0 |
| FN | 0 |
| precision | 100.000% |
| recall | 100.000% |
| F1 | 100.000% |
| FPR（正常试验有误报） | 0.000% |
| FPR（每正常试验误报事件数） | 0.000000 |
| 平均检测延迟 (s) | 0.0 |
| 中位检测延迟 (s) | 0.0 |

匹配规则：同一信号、时间区间重叠或相差不超过 0.2 s 计为命中；FP/FN 为事件级统计，FPR 同时给出正常试验级和事件率口径。

## 鲁棒性曲线

短于最小持续时间的脉冲按设计会被去抖；曲线用于决定采样率、阈值和后续硬件触发策略。

| 电流异常持续时间 (s) | 检出率 |
| ---: | ---: |
| 0.010 | 0.000% |
| 0.020 | 0.000% |
| 0.030 | 0.000% |
| 0.050 | 100.000% |
| 0.080 | 100.000% |
| 0.120 | 100.000% |
| 0.200 | 100.000% |

| 正常噪声倍数 | 试验级误报率 | 每试验误报事件数 |
| ---: | ---: | ---: |
| 1.0 | 0.000% | 0.000 |
| 1.5 | 0.000% | 0.000 |
| 2.0 | 0.000% | 0.000 |
| 2.5 | 0.000% | 0.000 |
| 3.0 | 10.000% | 0.100 |

| 电流静态偏置 (A) | 试验级误报率 |
| ---: | ---: |
| 0.0 | 0.000% |
| 1.0 | 0.000% |
| 2.0 | 0.000% |
| 3.0 | 0.000% |
| 4.0 | 0.000% |
