xianzai588/Hanjie/automation/anomaly-detection/results/benchmark/trial-metrics.csv

trial_id | class | injected | tp | fp | fn | truth_count | predicted_count | mean_delay_s
N-001 | normal | False | 0 | 0 | 0 | 0 | 0
N-002 | normal | False | 0 | 0 | 0 | 0 | 0
N-003 | normal | False | 0 | 0 | 0 | 0 | 0
N-004 | normal | False | 0 | 0 | 0 | 0 | 0
N-005 | normal | False | 0 | 0 | 0 | 0 | 0
N-006 | normal | False | 0 | 0 | 0 | 0 | 0
N-007 | normal | False | 0 | 0 | 0 | 0 | 0
N-008 | normal | False | 0 | 0 | 0 | 0 | 0
N-009 | normal | False | 0 | 0 | 0 | 0 | 0
N-010 | normal | False | 0 | 0 | 0 | 0 | 0
N-011 | normal | False | 0 | 0 | 0 | 0 | 0
N-012 | normal | False | 0 | 0 | 0 | 0 | 0
N-013 | normal | False | 0 | 0 | 0 | 0 | 0
N-014 | normal | False | 0 | 0 | 0 | 0 | 0
N-015 | normal | False | 0 | 0 | 0 | 0 | 0
N-016 | normal | False | 0 | 0 | 0 | 0 | 0
N-017 | normal | False | 0 | 0 | 0 | 0 | 0
N-018 | normal | False | 0 | 0 | 0 | 0 | 0
N-019 | normal | False | 0 | 0 | 0 | 0 | 0
N-020 | normal | False | 0 | 0 | 0 | 0 | 0
N-021 | normal | False | 0 | 0 | 0 | 0 | 0
N-022 | normal | False | 0 | 0 | 0 | 0 | 0
N-023 | normal | False | 0 | 0 | 0 | 0 | 0
N-024 | normal | False | 0 | 0 | 0 | 0 | 0
N-025 | normal | False | 0 | 0 | 0 | 0 | 0
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
