xianzai588/Hanjie/automation/vision/results/difficult/blur/error-distribution.png

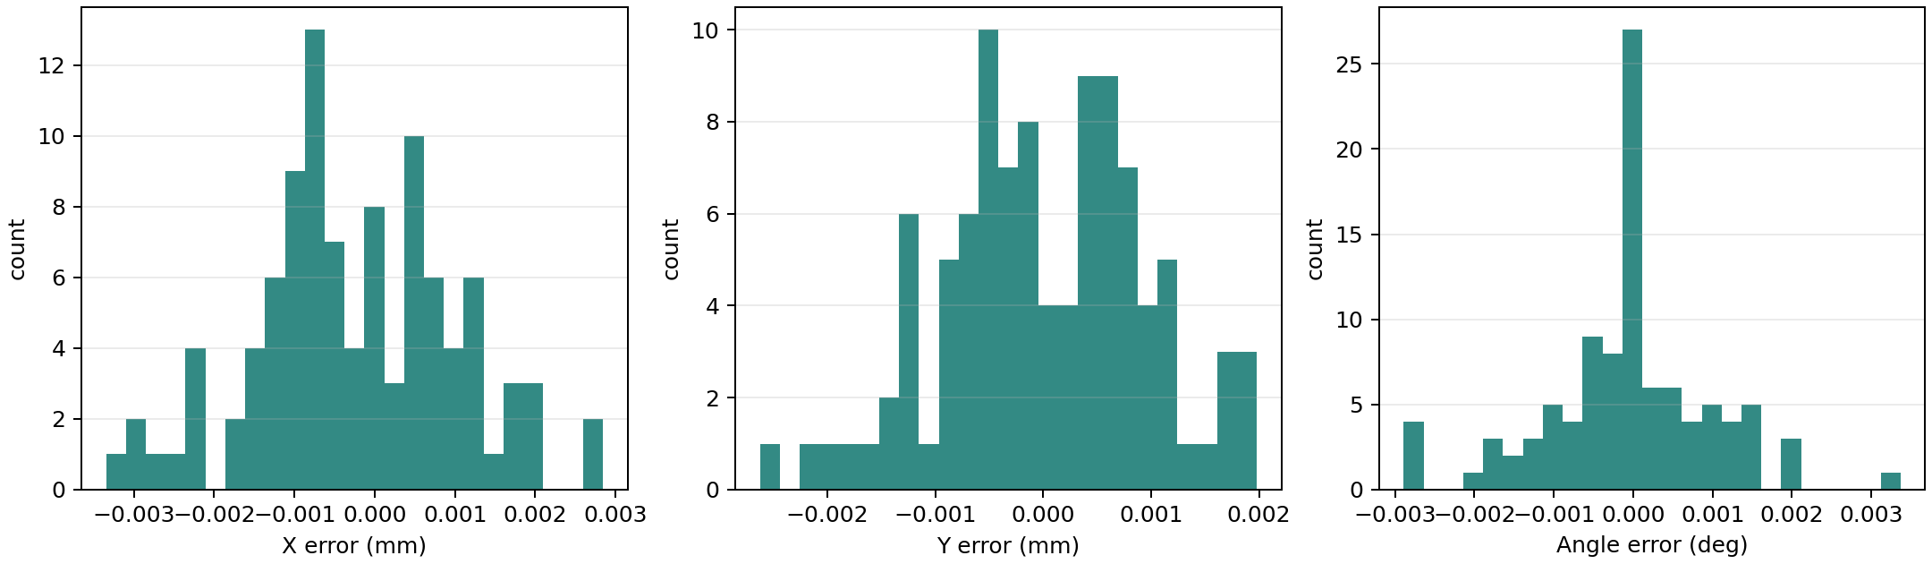
automation/vision/results/difficult/blur/error-distribution.png
