xianzai588/Hanjie/automation/vision/results/difficult/clean/error-distribution.png

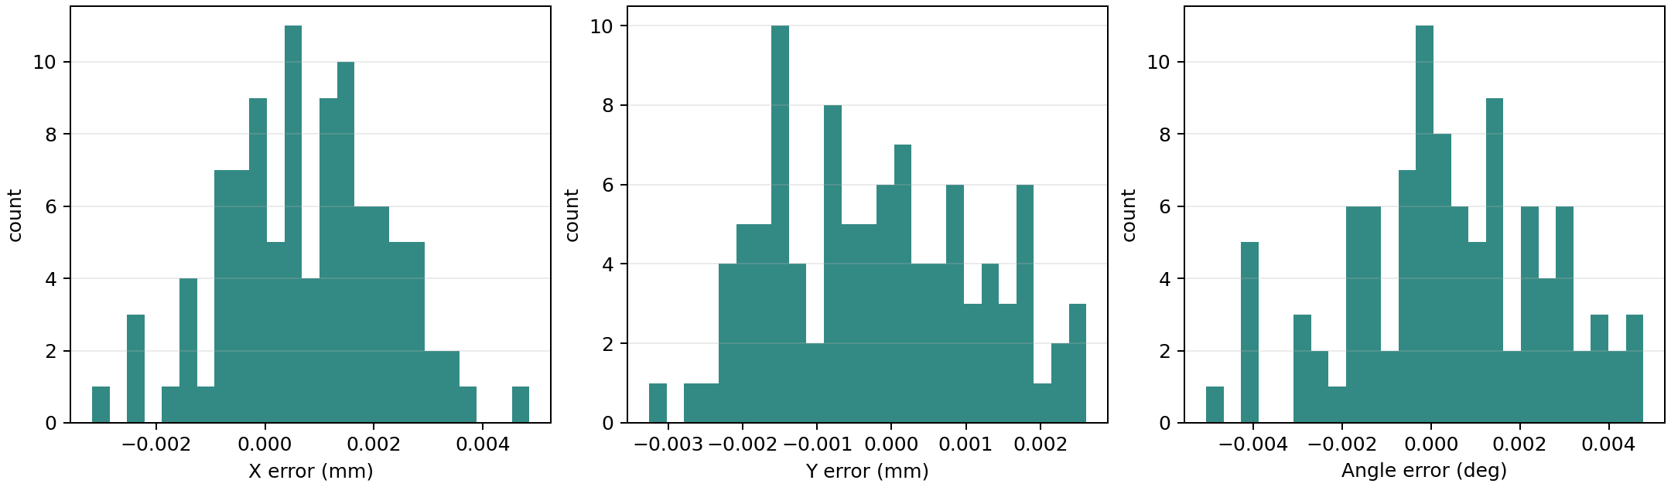
automation/vision/results/difficult/clean/error-distribution.png
