xianzai588/Hanjie/automation/vision/results/difficult/distortion/error-distribution.png

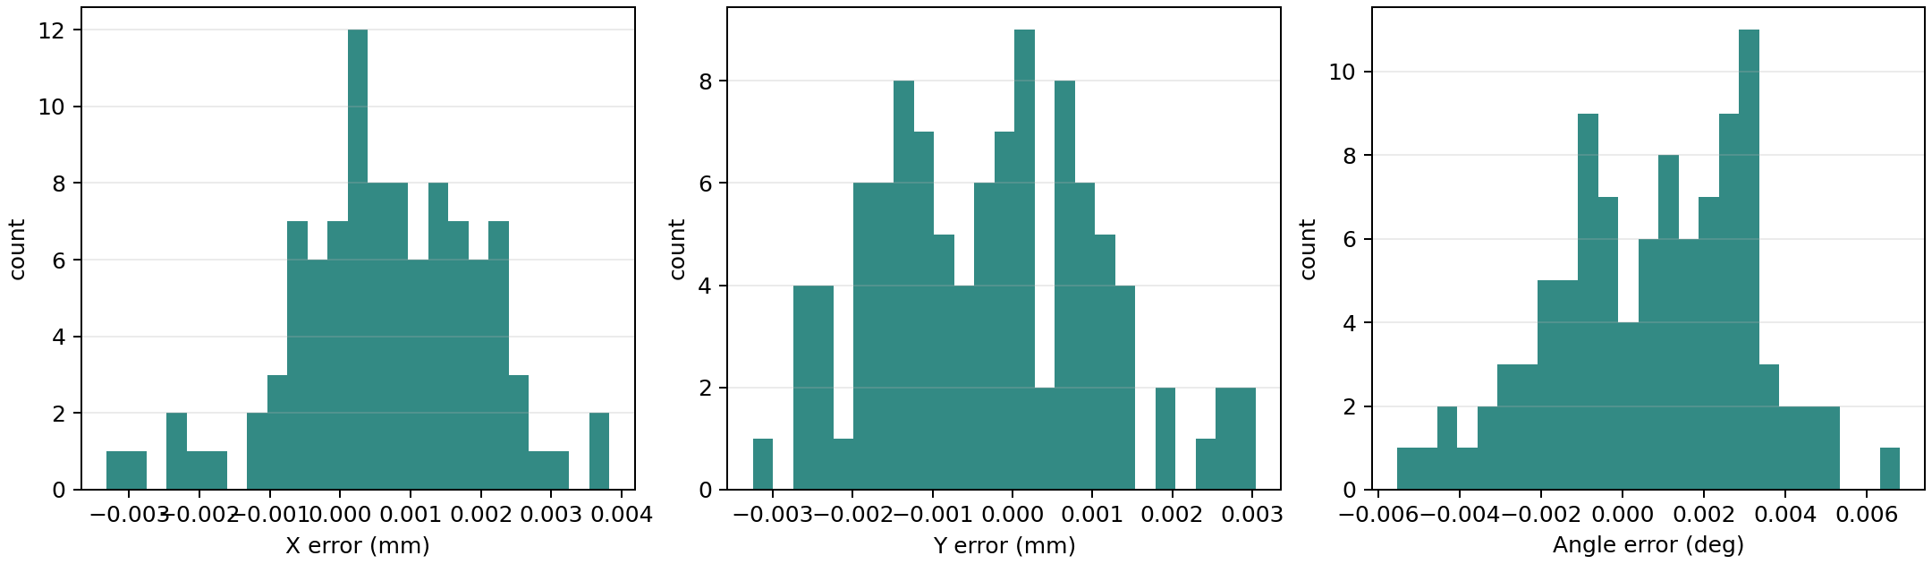
automation/vision/results/difficult/distortion/error-distribution.png
