xianzai588/Hanjie/automation/vision/results/difficult/illumination/error-distribution.png

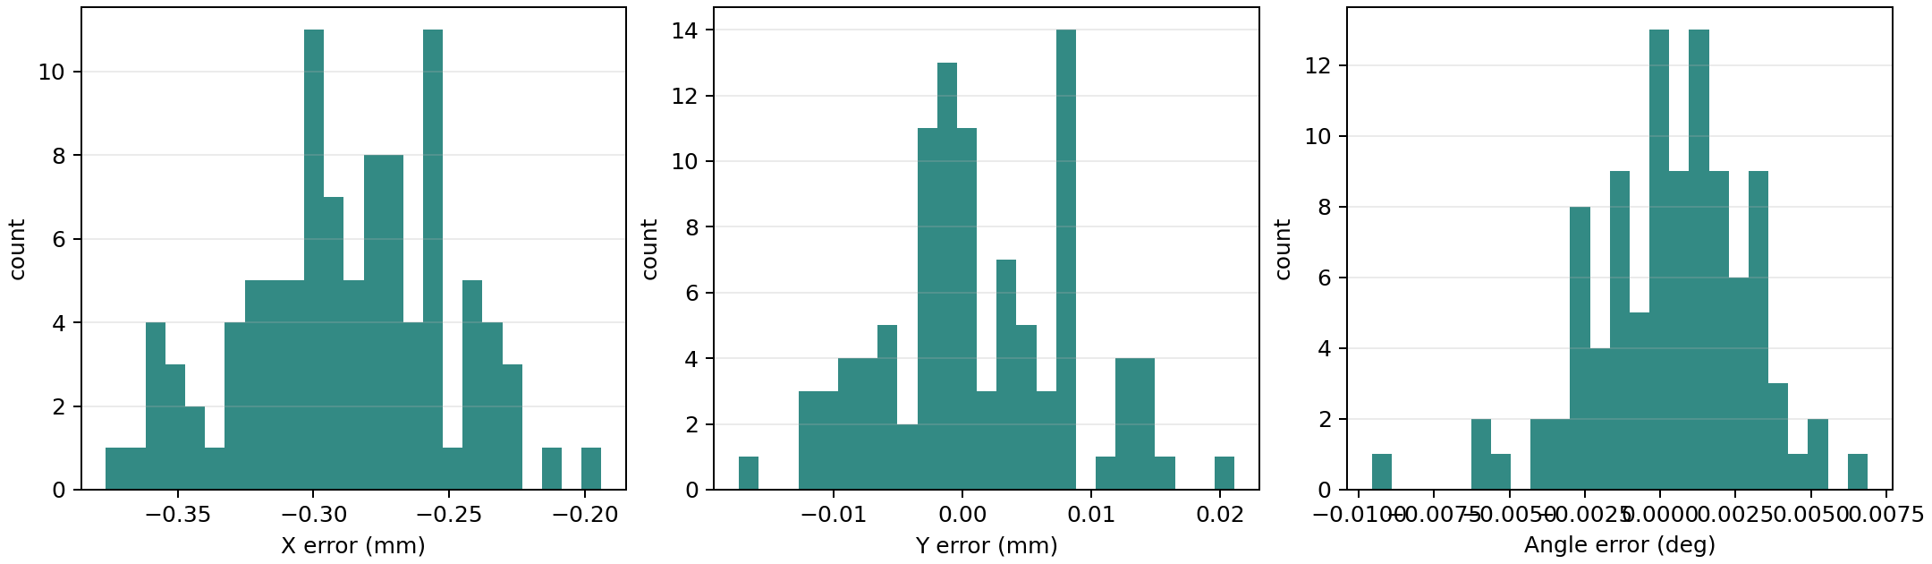
automation/vision/results/difficult/illumination/error-distribution.png
