xianzai588/Hanjie/automation/vision/results/difficult/missing_edges/error-distribution.png

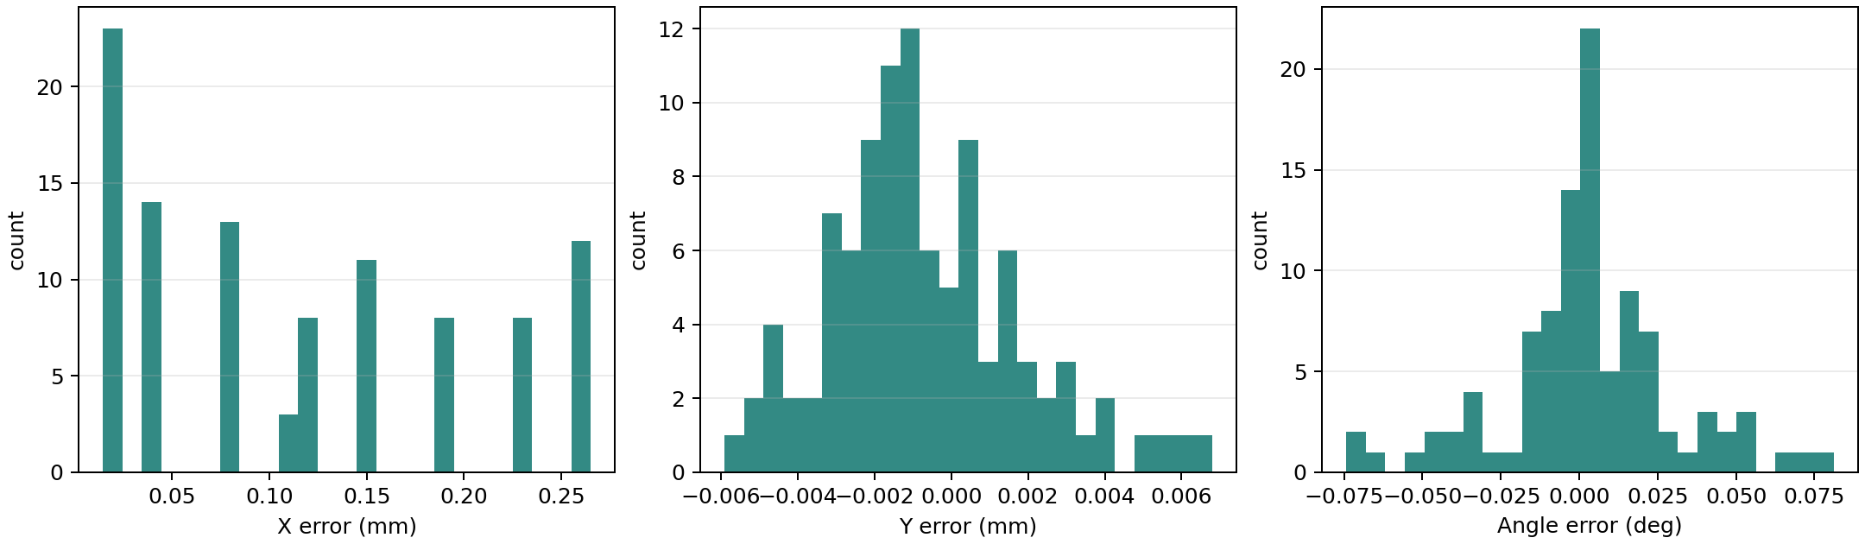
automation/vision/results/difficult/missing_edges/error-distribution.png
