xianzai588/Hanjie/automation/vision/results/difficult/occlusion/error-distribution.png

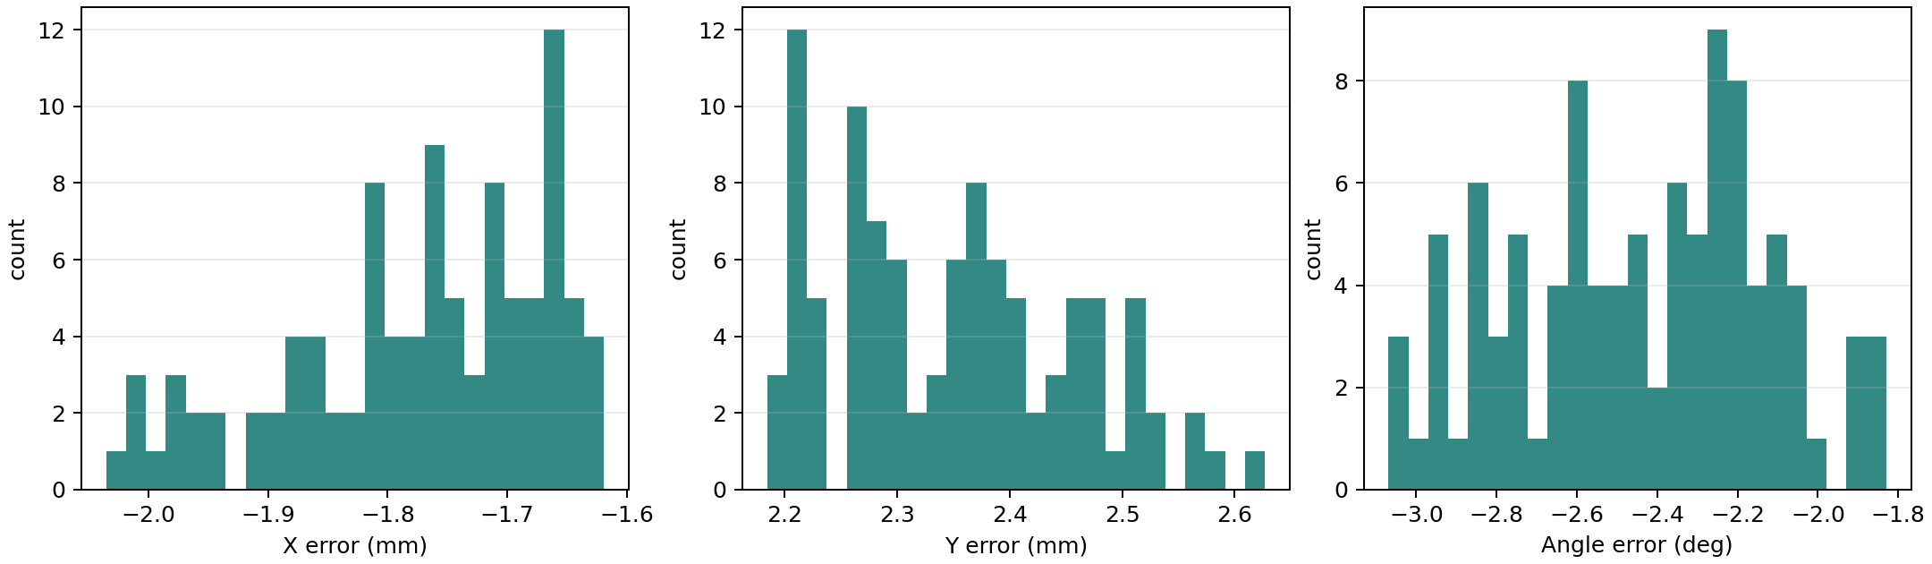
automation/vision/results/difficult/occlusion/error-distribution.png
