xianzai588/Hanjie/simulation/results/monte-carlo/monte-carlo.png

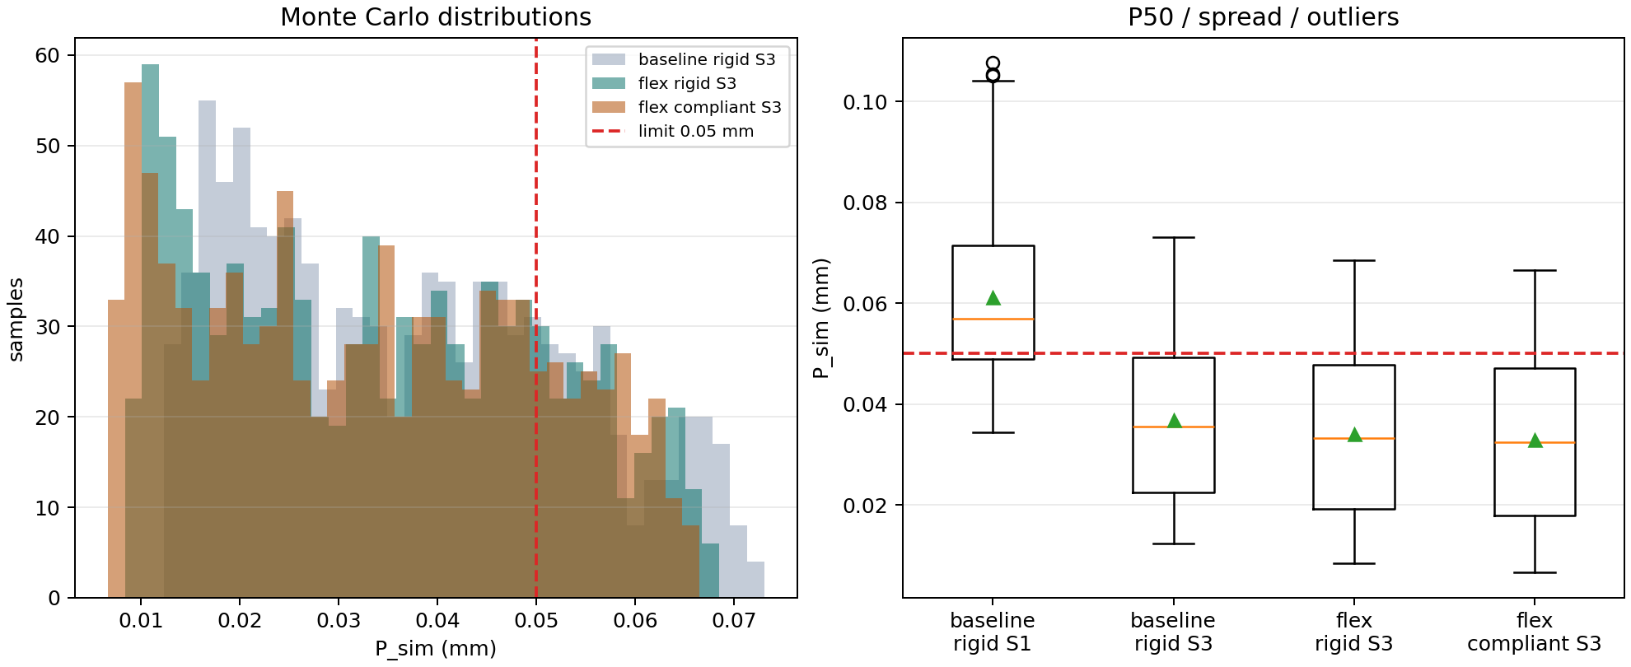
simulation/results/monte-carlo/monte-carlo.png
