xianzai588/Hanjie/simulation/structural-v4/results/struct-uncertainty/sensitivity-ranking.png

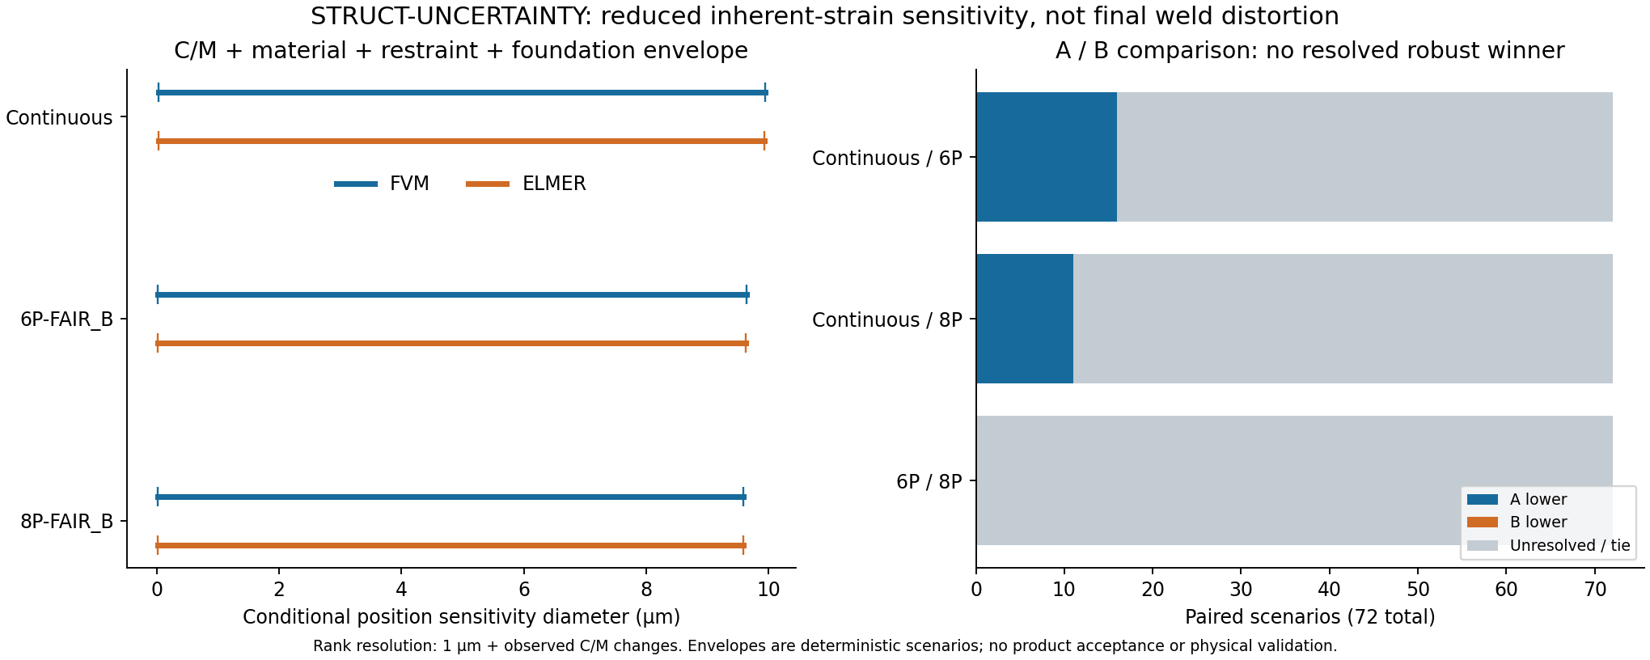
simulation/structural-v4/results/struct-uncertainty/sensitivity-ranking.png
