xianzai588/Hanjie/simulation/thermal-ref/results/plan7/mechanism-diagnostics.png

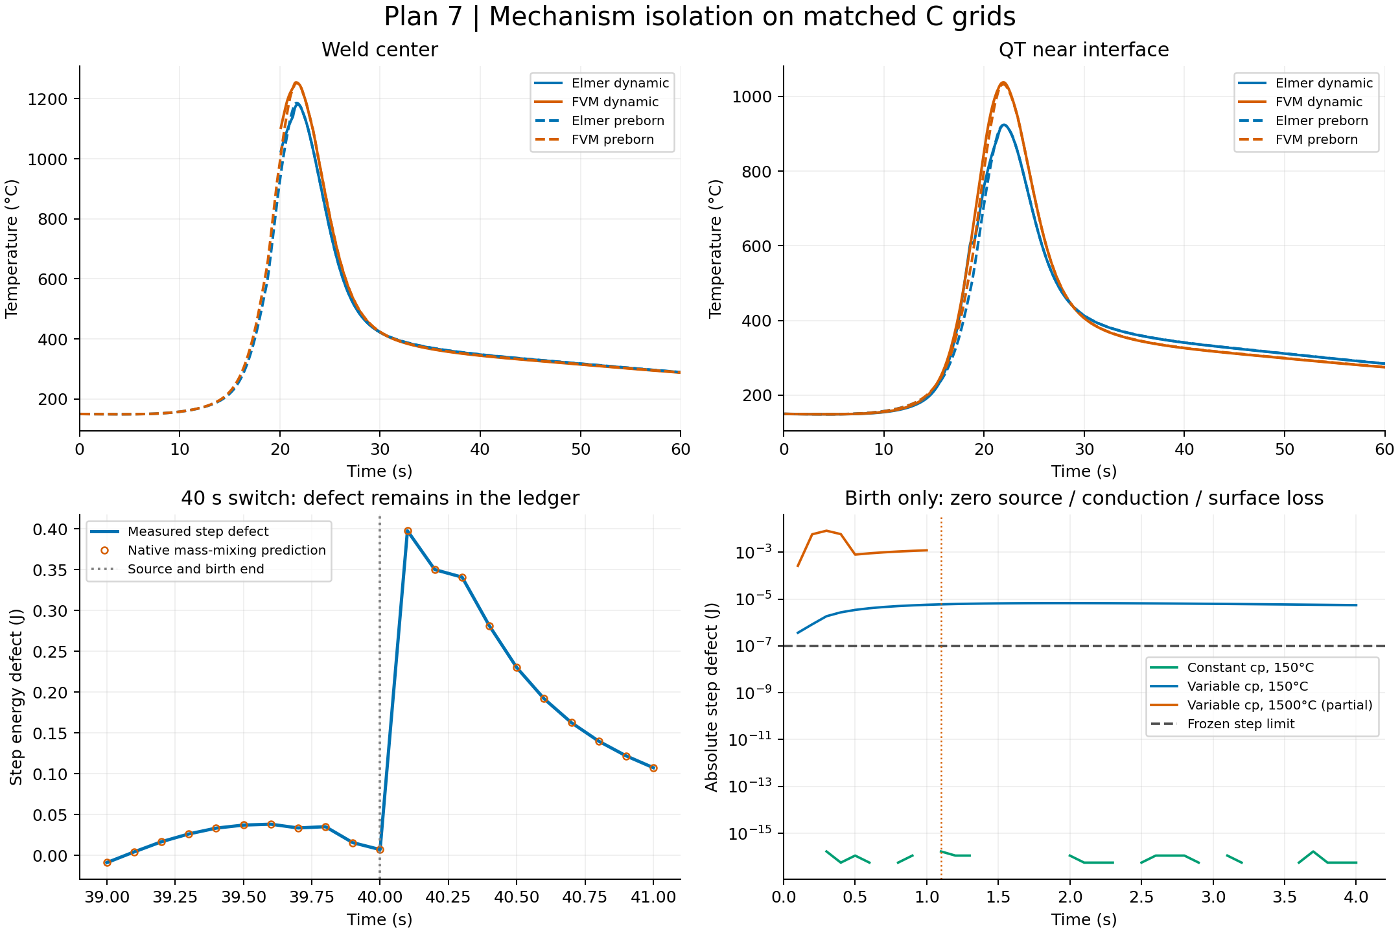
simulation/thermal-ref/results/plan7/mechanism-diagnostics.png
