xianzai588/Hanjie/simulation/thermal-ref/results/plan8/partition-diagnostics.png

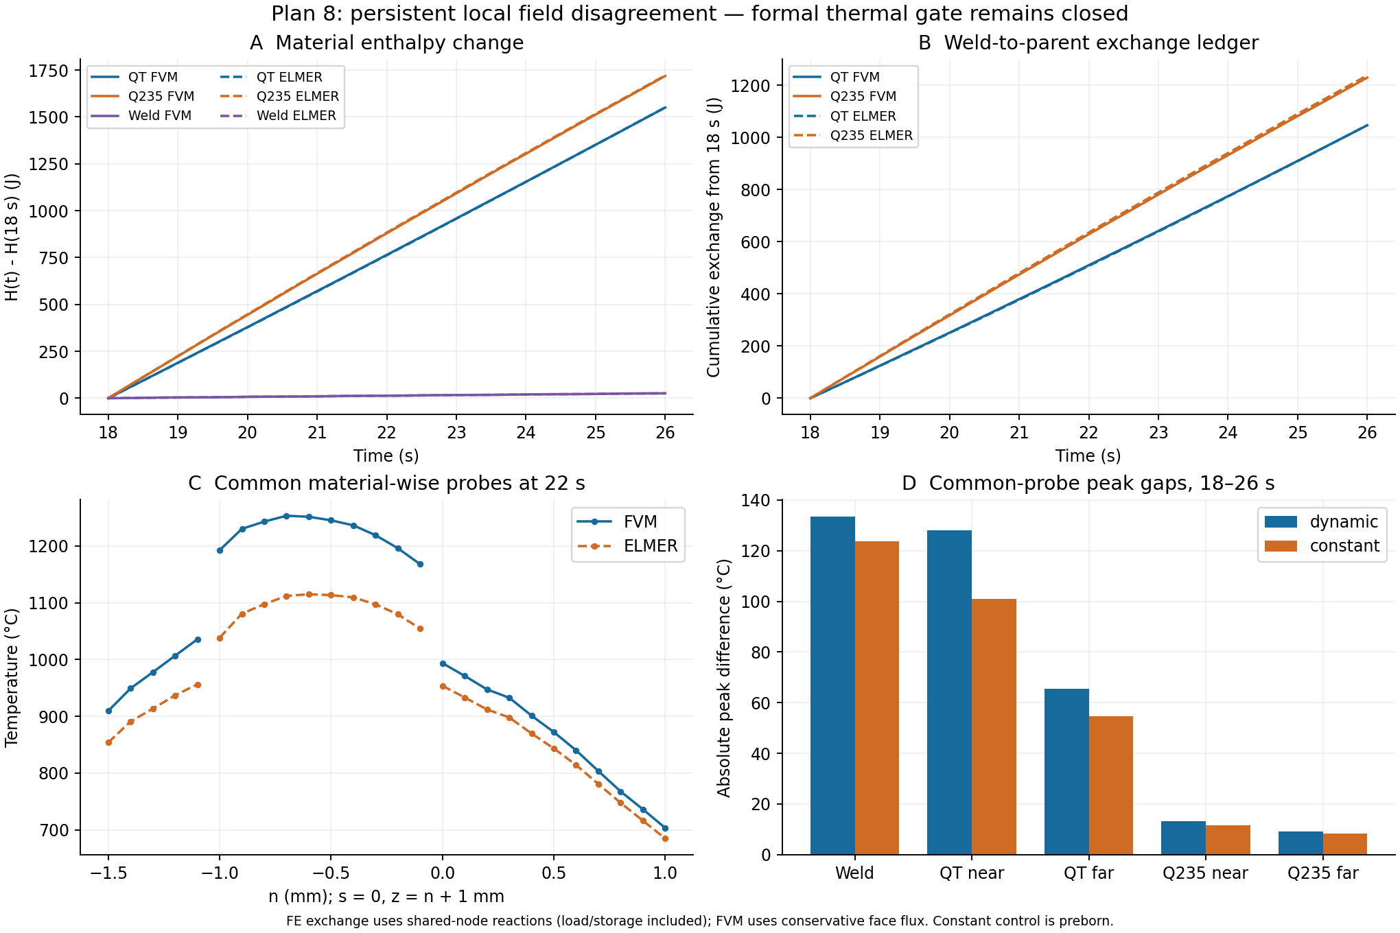
simulation/thermal-ref/results/plan8/partition-diagnostics.png
