xianzai588/Hanjie/simulation/thermal-ref/results/REF-C/comparison.png

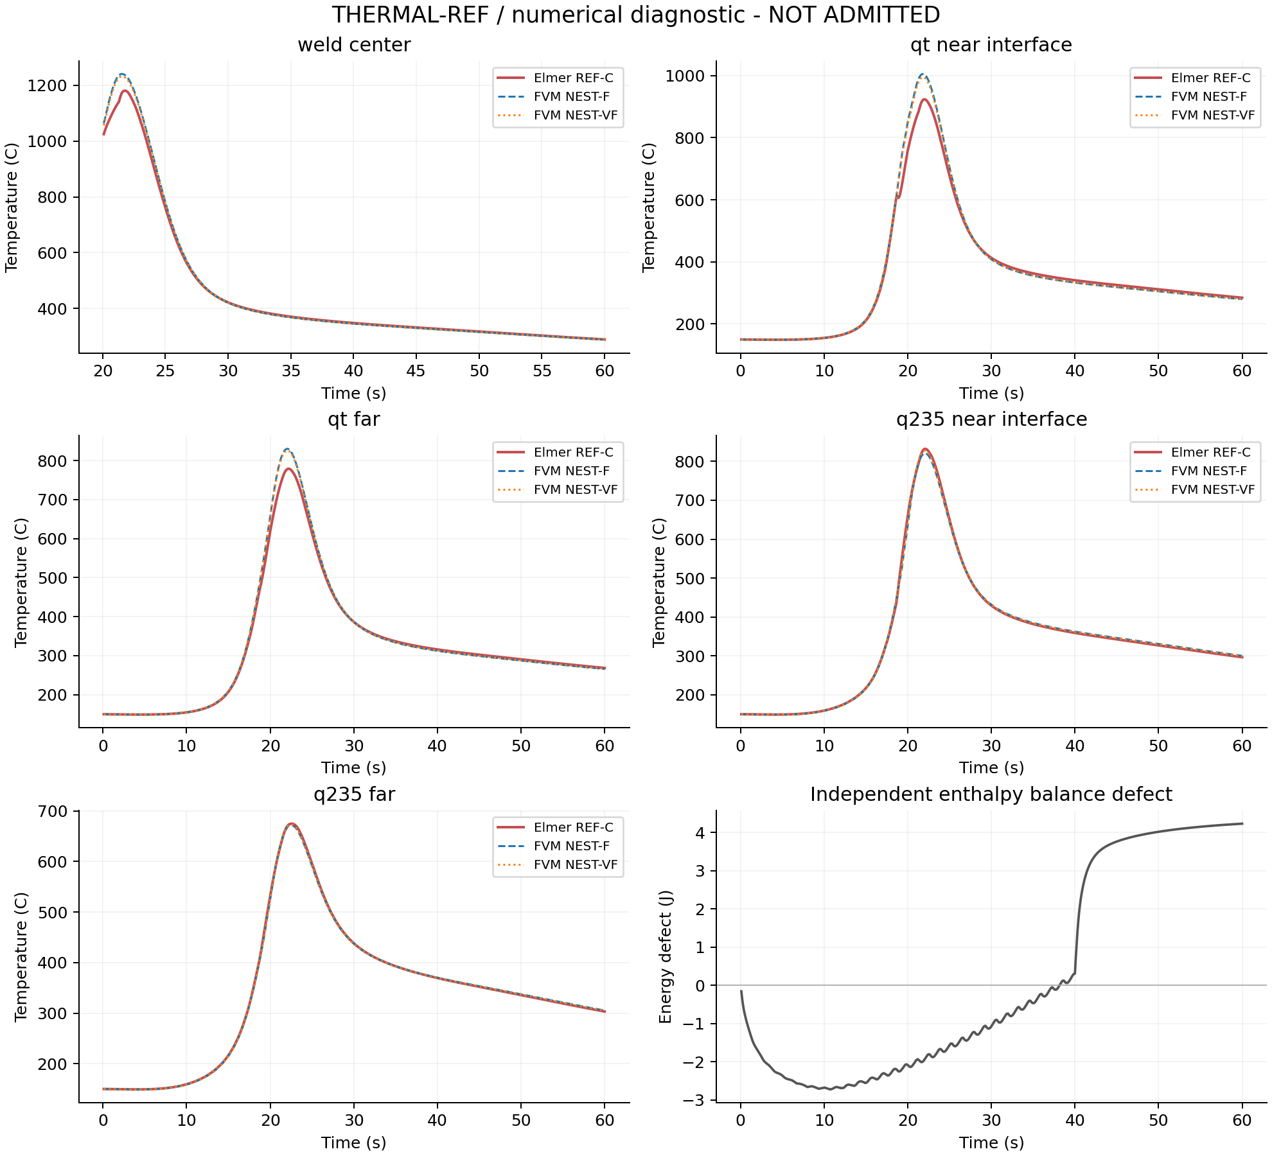
simulation/thermal-ref/results/REF-C/comparison.png
