xianzai588/Hanjie/simulation/thermal-v5/results/g-thermal-audit/efficiency-high/thermal0-peak-profile.png

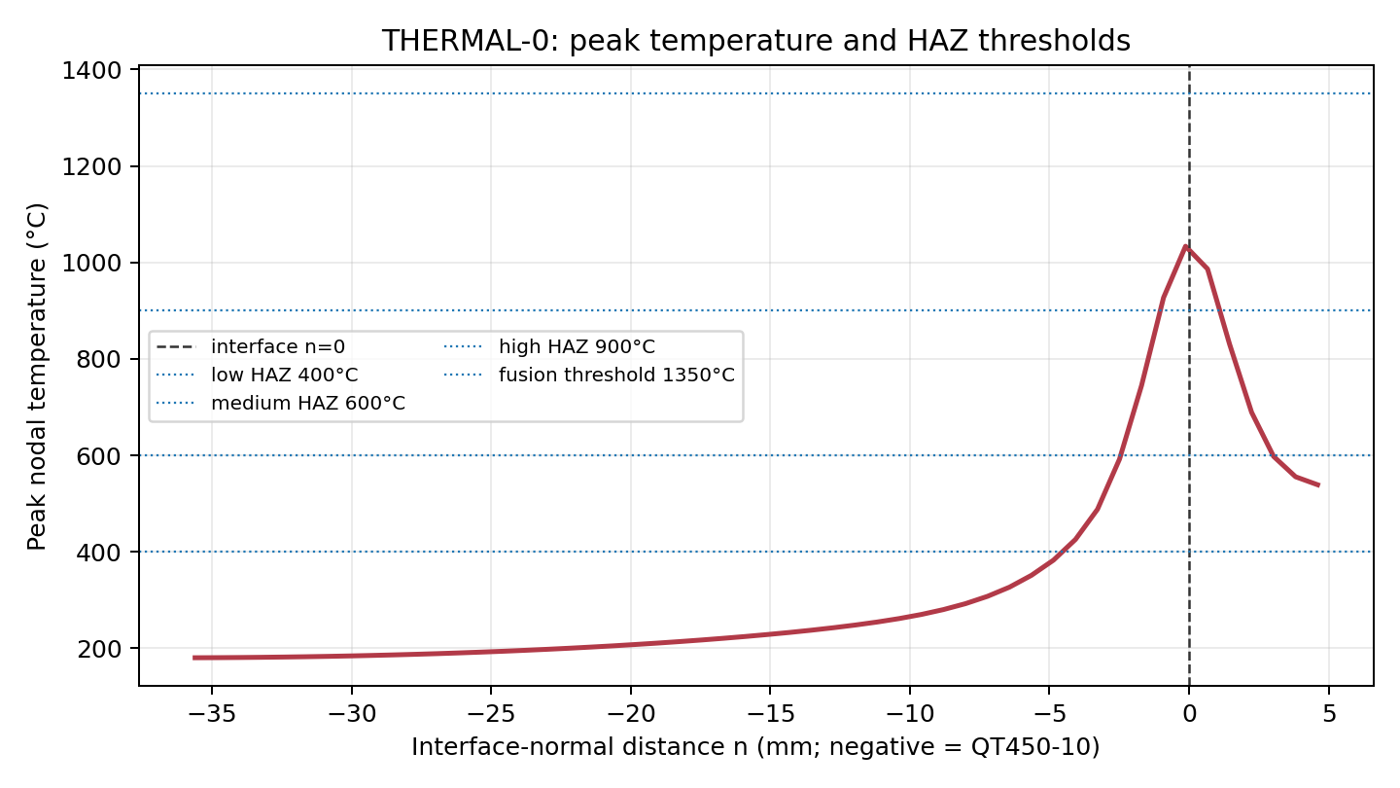
simulation/thermal-v5/results/g-thermal-audit/efficiency-high/thermal0-peak-profile.png
