xianzai588/Hanjie/simulation/thermal-v5/results/xsec-refinement-study/xsec-refinement-diagnostics.png

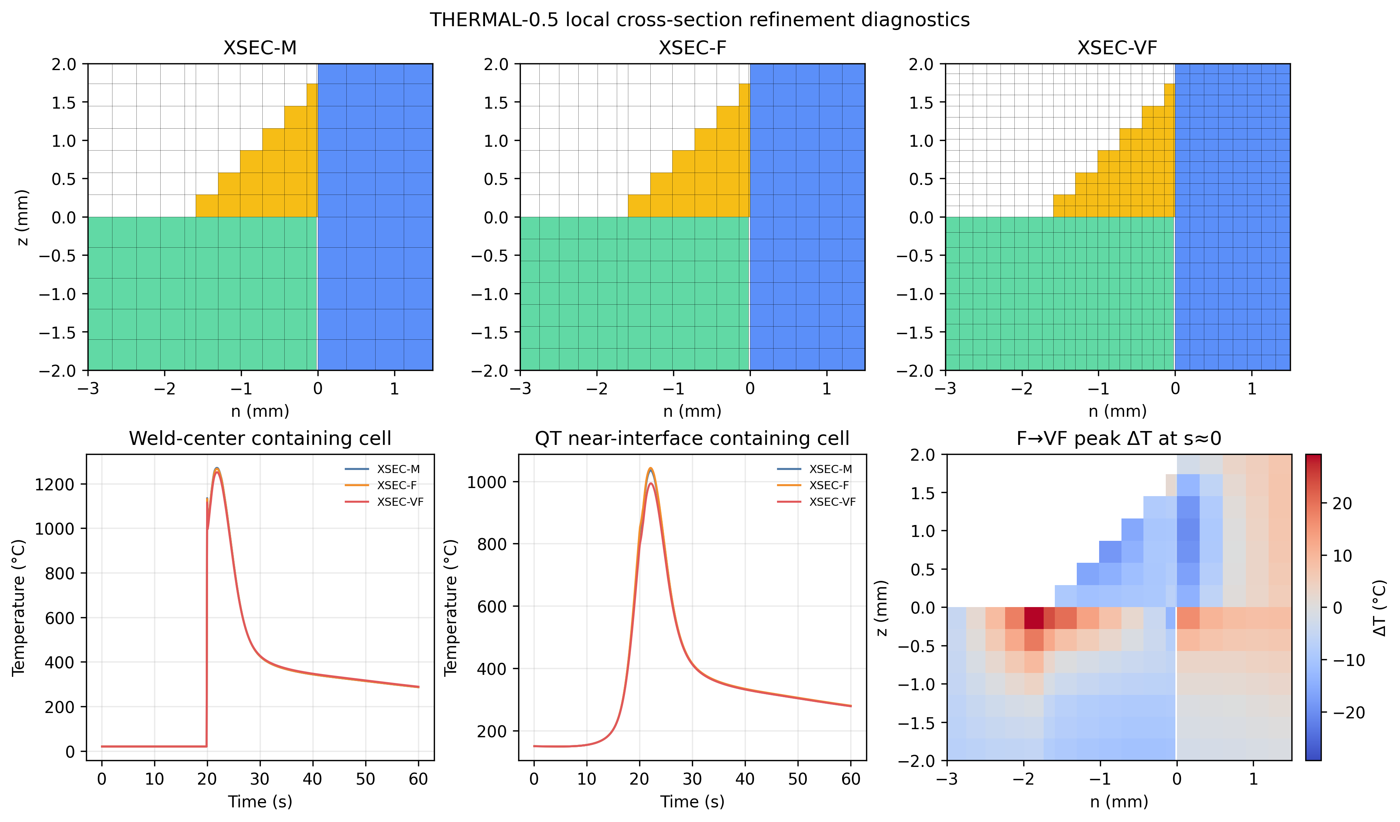
simulation/thermal-v5/results/xsec-refinement-study/xsec-refinement-diagnostics.png
