xianzai588/Hanjie/cad/generated/engineering-drawings/pdf/fixture-part.pdf

## 夹具锥形心轴与底板零件图

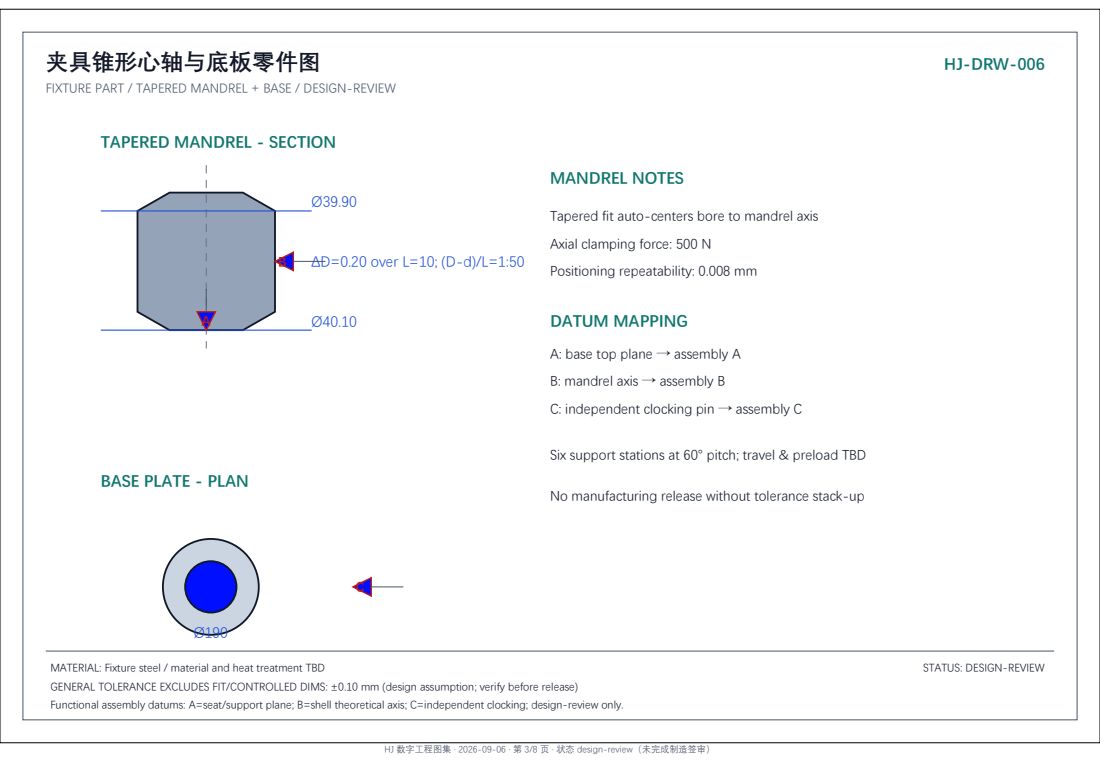
[picture p54: page 1]
HJ-DRW-006; ΔD=0.20 over L=10; (D-d)/L=1:50; MANDREL NOTES; DATUM MAPPING; MATERIAL: Fixture steel / material and heat treatment TBD; STATUS: DESIGN-REVIEW

FIXTURE PART / TAPERED MANDREL + BASE / DESIGN-REVIEW

TAPERED MANDREL - SECTION

Tapered fit auto-centers bore to mandrel axis

Axial clamping force: 500 N

Positioning repeatability: 0.008 mm

A: base top plane → assembly A

B: mandrel axis → assembly B

C: independent clocking pin → assembly C

Six support stations at 60° pitch; travel & preload TBD

BASE PLATE - PLAN

No manufacturing release without tolerance stack-up

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

HJ 数字工程图集 · 2026-09-06 · 第 3/8 页 · 状态 design-review（未完成制造签审）
