xianzai588/Hanjie/cad/generated/engineering-drawings/pdf/shell.pdf

# 薄壁壳体零件图

## HJ-DRW-002

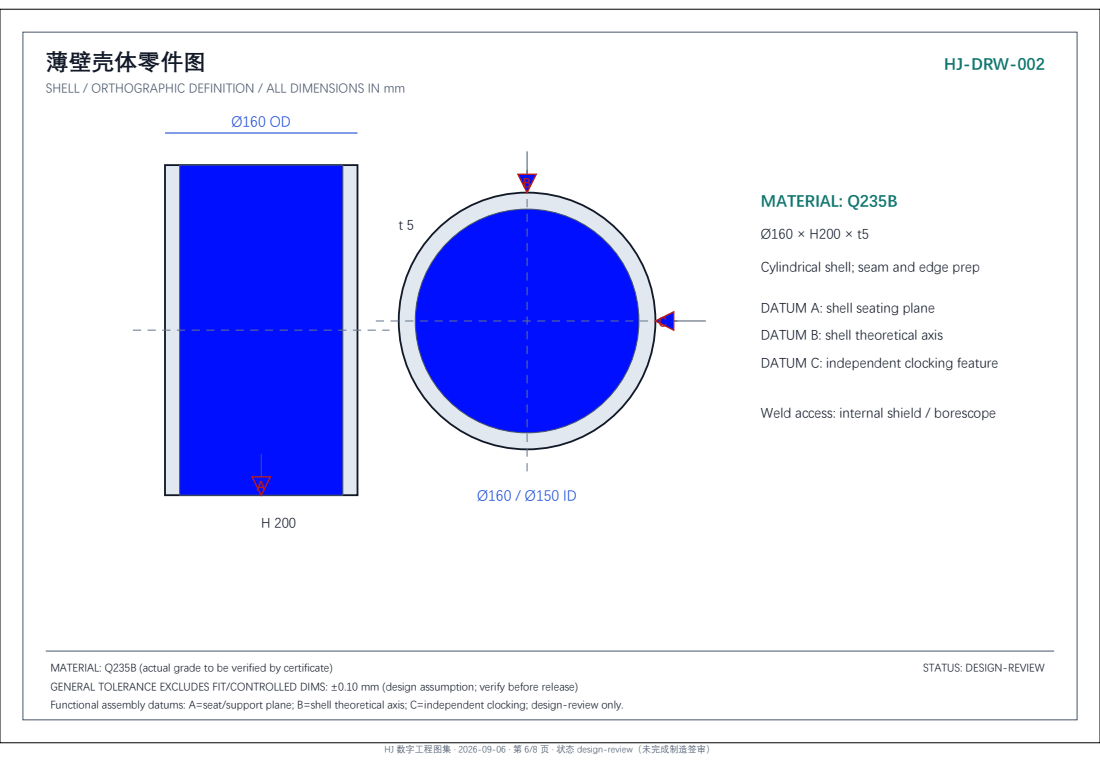
[picture p55: page 1]
MATERIAL: Q235B; MATERIAL: Q235B (actual grade to be verified by certificate); STATUS: DESIGN-REVIEW

SHELL / ORTHOGRAPHIC DEFINITION / ALL DIMENSIONS IN mm

Cylindrical shell; seam and edge prep

DATUM A: shell seating plane

DATUM B: shell theoretical axis

DATUM C: independent clocking feature

Weld access: internal shield / borescope

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

HJ 数字工程图集 · 2026-09-06 · 第 6/8 页 · 状态 design-review（未完成制造签审）
