xianzai588/Hanjie/cad/generated/engineering-drawings/pdf/weld-layout.pdf

# 焊缝布置与顺序图

## HJ-DRW-004

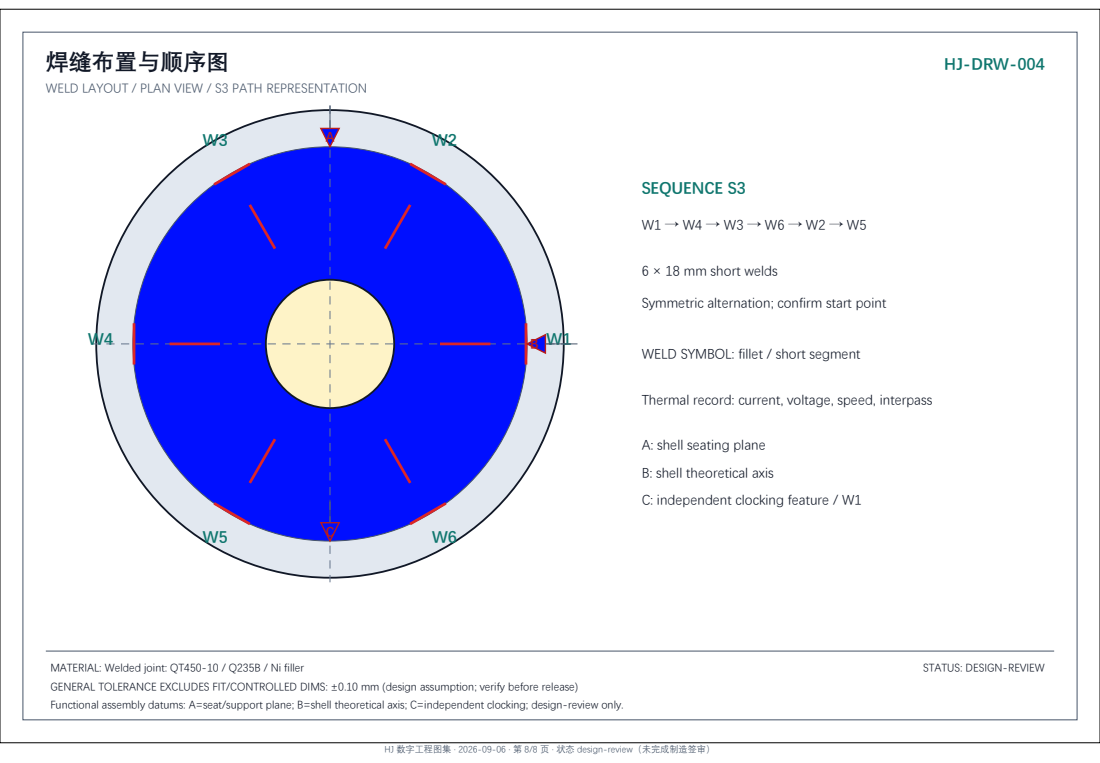
[picture p56: page 1]
SEQUENCE S3; MATERIAL: Welded joint: QT450-10 / Q235B / Ni filler; STATUS: DESIGN-REVIEW

WELD LAYOUT / PLAN VIEW / S3 PATH REPRESENTATION

6 × 18 mm short welds

Symmetric alternation; confirm start point

WELD SYMBOL: fillet / short segment

Thermal record: current, voltage, speed, interpass

A: shell seating plane

B: shell theoretical axis

C: independent clocking feature / W1

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

HJ 数字工程图集 · 2026-09-06 · 第 8/8 页 · 状态 design-review（未完成制造签审）
