xianzai588/Hanjie/project/tolerance.yaml

version: "TOLERANCE-1.0"
authority: "产品几何、自动化路径和测量不确定度三条链的唯一权威配置"
# 三链分离；数值为设计分配，未完成实测预算闭合。
target:
  tolerance_callout: Ø0.05 | A | B
  cylindrical_tolerance_zone_diameter_mm: 0.05
  radial_deviation_limit_mm: 0.025
quality_gates:
  vision:
    rejection_reasons:
    - extreme_illumination
    - excessive_blur
    - low_contrast
    - severe_distortion
    - heavy_occlusion
    action_on_failure: REFUSE_AND_ALARM
  temperature:
    max_peak_temperature_c: 1650.0
    interpass_gate_temperature_c: 200.0
    max_circumferential_delta_t_c: 40.0
  position_tolerance_cmm:
    acceptance_threshold_mm: 0.05
    guard_band_safety_margin_mm: 0.005
    guard_band_status: design_assumption_pending_uncertainty
evidence_level: design_assumption
budget_status: not_closed
legacy_v41_mixed_sum_mm: 0.028
legacy_v41_note: 旧表 0.028 而非 0.025 mm；混合路径/几何误差且含 P95，不能作为最坏情况上界
product_geometry_chain:
  unit: radial_mm
  interpretation: 各项为等效径向设计分配，并非原始平面度直接相加；灵敏度待验证
  contributions_mm:
    datum_a_equivalent: 0.005
    datum_b_equivalent: 0.003
    fixture_repeatability: 0.008
    initial_assembly: 0.005
    thermal_deformation: 0.012
    unclamping: 0.002
  worst_case_design_sum_mm: 0.035
  rss_mm: null
  p95_mm: null
  distribution_status: unknown
automation_path_chain:
  unit: mm
  evidence_level: design_assumption
  vision_radial_p95: 0.01
  camera_extrinsic: 0.004
  tcp_calibration: 0.003
  robot_repeatability: null
  product_sensitivities: null
  note: 机器人指标尚未核实；原 0.003 与设备表 0.03 不一致，待核实后经灵敏度映射，禁止直接相加
measurement_chain:
  expanded_uncertainty_mm: null
  coverage_factor: null
  components:
  - CMM
  - probe
  - datum_reconstruction
  - sampling
  - repeatability
  - environment
  note: MPE 不等于测量不确定度；未取得校准证书及重复测量数据
