xianzai588/Hanjie/simulation/cases/FE-001/config.yaml

case:
  case_id: FE-001
  structure: baseline
  fixture: rigid
  sequence: S1
mesh_points_per_axis: 61
model:
  name: reduced-order-thermal-structural-v1
  nominal_temperature_c: 20.0
  effective_heated_area_mm2: 200.0
  residual_fraction: 0.12
  cooling_memory: 0.35
  bore_effective_height_mm: 12.0
  initial_eccentricity_mm: 0.0
  position_tolerance_limit_mm: 0.05
geometry:
  shell_outer_diameter_mm: 160.0
  shell_thickness_mm: 5.0
  bearing_bore_diameter_mm: 40.0
  seat_core_outer_diameter_mm: 82.0
  seat_thickness_mm: 12.0
  wing_width: 18.0
  wing_outer_radius_mm: 74.98
  weld_segment_length_mm: 18.0
process:
  current_a: 75.0
  voltage_v: 12.0
  travel_speed_mm_s: 1.5
  efficiency: 0.55
  preheat_c: 150.0
  interpass_limit_c: 200.0
materials:
  q235b:
    density_kg_m3: 7850.0
    specific_heat_j_kgk: 470.0
    thermal_conductivity_w_mk: 45.0
    elastic_modulus_gpa: 210.0
    alpha_per_k: 1.2e-05
  qt450_10:
    density_kg_m3: 7200.0
    specific_heat_j_kgk: 460.0
    thermal_conductivity_w_mk: 35.0
    elastic_modulus_gpa: 170.0
    alpha_per_k: 1.05e-05
  fixture:
    equivalent_stiffness_n_mm: 1200.0
